frohro/Pico_Debug_Stack/Pico_Debug_Stack.txt

(export (version "E")
  (design
    (source "/home/frohro/Classes/Electronics/Pico_Development_Stack/Pico_Development_Stack.kicad_sch")
    (date "2025-12-18T11:42:48-0800")
    (tool "Eeschema 9.0.7-rc1-202512160022~49ee909d68~ubuntu25.04.1")
    (sheet (number "1") (name "/") (tstamps "/")
      (title_block
        (title "Raspberry Pi Pico Debug Stack")
        (company "Walla Walla University")
        (rev "0.1")
        (date "2025-12-10")
        (source "Pico_Development_Stack.kicad_sch")
        (comment (number "1") (value "Engineering"))
        (comment (number "2") (value "Rob Frohne"))
        (comment (number "3") (value ""))
        (comment (number "4") (value ""))
        (comment (number "5") (value ""))
        (comment (number "6") (value ""))
        (comment (number "7") (value ""))
        (comment (number "8") (value ""))
        (comment (number "9") (value "")))))
  (components
    (comp (ref "1V1_U1")
      (value "1V1")
      (footprint "TestPoint:TestPoint_Loop_D2.50mm_Drill1.0mm_LowProfile")
      (datasheet "~")
      (description "test point")
      (fields
        (field (name "Peak Wavelength"))
        (field (name "Footprint") "TestPoint:TestPoint_Loop_D2.50mm_Drill1.0mm_LowProfile")
        (field (name "Datasheet") "~")
        (field (name "Description") "test point"))
      (libsource (lib "Connector") (part "TestPoint") (description "test point"))
      (property (name "Peak Wavelength") (value ""))
      (property (name "Sheetname") (value "Root"))
      (property (name "Sheetfile") (value "Pico_Development_Stack.kicad_sch"))
      (property (name "ki_keywords") (value "test point tp"))
      (property (name "ki_fp_filters") (value "Pin* Test*"))
      (sheetpath (names "/") (tstamps "/"))
      (tstamps "04d520b3-1497-4948-9d44-730200b11b7a"))
    (comp (ref "A1")
      (value "RaspberryPi_Pico")
      (footprint "Module:RaspberryPi_Pico_SMD_HandSolder")
      (datasheet "https://datasheets.raspberrypi.com/pico/pico-datasheet.pdf")
      (description "Versatile and inexpensive microcontroller module (with debug pins) powered by RP2040 dual-core Arm Cortex-M0+ processor up to 133 MHz, 264kB SRAM, 2MB QSPI flash; also supports Raspberry Pi Pico 2")
      (fields
        (field (name "Peak Wavelength"))
        (field (name "Footprint") "Module:RaspberryPi_Pico_SMD_HandSolder")
        (field (name "Datasheet") "https://datasheets.raspberrypi.com/pico/pico-datasheet.pdf")
        (field (name "Description") "Versatile and inexpensive microcontroller module (with debug pins) powered by RP2040 dual-core Arm Cortex-M0+ processor up to 133 MHz, 264kB SRAM, 2MB QSPI flash; also supports Raspberry Pi Pico 2"))
      (libsource (lib "MCU_Module") (part "RaspberryPi_Pico_Debug") (description "Versatile and inexpensive microcontroller module (with debug pins) powered by RP2040 dual-core Arm Cortex-M0+ processor up to 133 MHz, 264kB SRAM, 2MB QSPI flash; also supports Raspberry Pi Pico 2"))
      (property (name "Peak Wavelength") (value ""))
      (property (name "Sheetname") (value "Root"))
      (property (name "Sheetfile") (value "Pico_Development_Stack.kicad_sch"))
      (property (name "ki_keywords") (value "RP2350A M33 RISC-V Hazard3 usb swd"))
      (property (name "ki_fp_filters") (value "RaspberryPi?Pico?SMD*"))
      (sheetpath (names "/") (tstamps "/"))
      (tstamps "4f39aecf-2b63-418a-a298-e7947e174bf0"))
    (comp (ref "C1")
      (value "10uF")
      (footprint "PCM_JLCPCB:C_0603")
      (datasheet "https://www.lcsc.com/datasheet/lcsc_datasheet_2304140030_Samsung-Electro-Mechanics-CL10A106MA8NRNC_C96446.pdf")
      (description "25V 10uF X5R ±20% 0603 Multilayer Ceramic Capacitors MLCC - SMD/SMT ROHS")
      (fields
        (field (name "LCSC") "C96446")
        (field (name "Stock") "3388297")
        (field (name "Price") "0.021USD")
        (field (name "Process") "SMT")
        (field (name "Minimum Qty") "20")
        (field (name "Attrition Qty") "8")
        (field (name "Class") "Basic Component")
        (field (name "Category") "Capacitors,Multilayer Ceramic Capacitors MLCC - SMD/SMT")
        (field (name "Manufacturer") "Samsung Electro-Mechanics")
        (field (name "Part") "CL10A106MA8NRNC")
        (field (name "Voltage Rated") "25V")
        (field (name "Tolerance") "±20%")
        (field (name "Capacitance") "10uF")
        (field (name "Temperature Coefficient") "X5R")
        (field (name "Footprint") "PCM_JLCPCB:C_0603")
        (field (name "Datasheet") "https://www.lcsc.com/datasheet/lcsc_datasheet_2304140030_Samsung-Electro-Mechanics-CL10A106MA8NRNC_C96446.pdf")
        (field (name "Description") "25V 10uF X5R ±20% 0603 Multilayer Ceramic Capacitors MLCC - SMD/SMT ROHS"))
      (libsource (lib "PCM_JLCPCB-Capacitors") (part "0603,10uF,(2)") (description "25V 10uF X5R ±20% 0603 Multilayer Ceramic Capacitors MLCC - SMD/SMT ROHS"))
      (property (name "LCSC") (value "C96446"))
      (property (name "Stock") (value "3388297"))
      (property (name "Price") (value "0.021USD"))
      (property (name "Process") (value "SMT"))
      (property (name "Minimum Qty") (value "20"))
      (property (name "Attrition Qty") (value "8"))
      (property (name "Class") (value "Basic Component"))
      (property (name "Category") (value "Capacitors,Multilayer Ceramic Capacitors MLCC - SMD/SMT"))
      (property (name "Manufacturer") (value "Samsung Electro-Mechanics"))
      (property (name "Part") (value "CL10A106MA8NRNC"))
      (property (name "Voltage Rated") (value "25V"))
      (property (name "Tolerance") (value "±20%"))
      (property (name "Capacitance") (value "10uF"))
      (property (name "Temperature Coefficient") (value "X5R"))
      (property (name "Sheetname") (value "Root"))
      (property (name "Sheetfile") (value "Pico_Development_Stack.kicad_sch"))
      (property (name "ki_fp_filters") (value "C_*"))
      (sheetpath (names "/") (tstamps "/"))
      (tstamps "58dccd1a-244c-415b-846c-d42b6af4e663"))
    (comp (ref "C2")
      (value "100nF")
      (footprint "PCM_JLCPCB:C_0603")
      (datasheet "https://www.lcsc.com/datasheet/lcsc_datasheet_2211101700_YAGEO-CC0603KRX7R9BB104_C14663.pdf")
      (description "50V 100nF X7R ±10% 0603 Multilayer Ceramic Capacitors MLCC - SMD/SMT ROHS")
      (fields
        (field (name "LCSC") "C14663")
        (field (name "Stock") "70324515")
        (field (name "Price") "0.006USD")
        (field (name "Process") "SMT")
        (field (name "Minimum Qty") "20")
        (field (name "Attrition Qty") "10")
        (field (name "Class") "Basic Component")
        (field (name "Category") "Capacitors,Multilayer Ceramic Capacitors MLCC - SMD/SMT")
        (field (name "Manufacturer") "YAGEO")
        (field (name "Part") "CC0603KRX7R9BB104")
        (field (name "Voltage Rated") "50V")
        (field (name "Tolerance") "±10%")
        (field (name "Capacitance") "100nF")
        (field (name "Temperature Coefficient") "X7R")
        (field (name "Peak Wavelength"))
        (field (name "Footprint") "PCM_JLCPCB:C_0603")
        (field (name "Datasheet") "https://www.lcsc.com/datasheet/lcsc_datasheet_2211101700_YAGEO-CC0603KRX7R9BB104_C14663.pdf")
        (field (name "Description") "50V 100nF X7R ±10% 0603 Multilayer Ceramic Capacitors MLCC - SMD/SMT ROHS"))
      (libsource (lib "PCM_JLCPCB-Capacitors") (part "0603,100nF") (description "50V 100nF X7R ±10% 0603 Multilayer Ceramic Capacitors MLCC - SMD/SMT ROHS"))
      (property (name "LCSC") (value "C14663"))
      (property (name "Stock") (value "70324515"))
      (property (name "Price") (value "0.006USD"))
      (property (name "Process") (value "SMT"))
      (property (name "Minimum Qty") (value "20"))
      (property (name "Attrition Qty") (value "10"))
      (property (name "Class") (value "Basic Component"))
      (property (name "Category") (value "Capacitors,Multilayer Ceramic Capacitors MLCC - SMD/SMT"))
      (property (name "Manufacturer") (value "YAGEO"))
      (property (name "Part") (value "CC0603KRX7R9BB104"))
      (property (name "Voltage Rated") (value "50V"))
      (property (name "Tolerance") (value "±10%"))
      (property (name "Capacitance") (value "100nF"))
      (property (name "Temperature Coefficient") (value "X7R"))
      (property (name "Peak Wavelength") (value ""))
      (property (name "Sheetname") (value "Root"))
      (property (name "Sheetfile") (value "Pico_Development_Stack.kicad_sch"))
      (property (name "ki_fp_filters") (value "C_*"))
      (sheetpath (names "/") (tstamps "/"))
      (tstamps "41aaf059-0a23-4617-9123-ac9339070171"))
    (comp (ref "C3")
      (value "100nF")
      (footprint "PCM_JLCPCB:C_0603")
      (datasheet "https://www.lcsc.com/datasheet/lcsc_datasheet_2211101700_YAGEO-CC0603KRX7R9BB104_C14663.pdf")
      (description "50V 100nF X7R ±10% 0603 Multilayer Ceramic Capacitors MLCC - SMD/SMT ROHS")
      (fields
        (field (name "LCSC") "C14663")
        (field (name "Stock") "70324515")
        (field (name "Price") "0.006USD")
        (field (name "Process") "SMT")
        (field (name "Minimum Qty") "20")
        (field (name "Attrition Qty") "10")
        (field (name "Class") "Basic Component")
        (field (name "Category") "Capacitors,Multilayer Ceramic Capacitors MLCC - SMD/SMT")
        (field (name "Manufacturer") "YAGEO")
        (field (name "Part") "CC0603KRX7R9BB104")
        (field (name "Voltage Rated") "50V")
        (field (name "Tolerance") "±10%")
        (field (name "Capacitance") "100nF")
        (field (name "Temperature Coefficient") "X7R")
        (field (name "Peak Wavelength"))
        (field (name "Footprint") "PCM_JLCPCB:C_0603")
        (field (name "Datasheet") "https://www.lcsc.com/datasheet/lcsc_datasheet_2211101700_YAGEO-CC0603KRX7R9BB104_C14663.pdf")
        (field (name "Description") "50V 100nF X7R ±10% 0603 Multilayer Ceramic Capacitors MLCC - SMD/SMT ROHS"))
      (libsource (lib "PCM_JLCPCB-Capacitors") (part "0603,100nF") (description "50V 100nF X7R ±10% 0603 Multilayer Ceramic Capacitors MLCC - SMD/SMT ROHS"))
      (property (name "LCSC") (value "C14663"))
      (property (name "Stock") (value "70324515"))
      (property (name "Price") (value "0.006USD"))
      (property (name "Process") (value "SMT"))
      (property (name "Minimum Qty") (value "20"))
      (property (name "Attrition Qty") (value "10"))
      (property (name "Class") (value "Basic Component"))
      (property (name "Category") (value "Capacitors,Multilayer Ceramic Capacitors MLCC - SMD/SMT"))
      (property (name "Manufacturer") (value "YAGEO"))
      (property (name "Part") (value "CC0603KRX7R9BB104"))
      (property (name "Voltage Rated") (value "50V"))
      (property (name "Tolerance") (value "±10%"))
      (property (name "Capacitance") (value "100nF"))
      (property (name "Temperature Coefficient") (value "X7R"))
      (property (name "Peak Wavelength") (value ""))
      (property (name "Sheetname") (value "Root"))
      (property (name "Sheetfile") (value "Pico_Development_Stack.kicad_sch"))
      (property (name "ki_fp_filters") (value "C_*"))
      (sheetpath (names "/") (tstamps "/"))
      (tstamps "a7b95df1-5875-4482-b6cb-c3aa639ff80f"))
    (comp (ref "C4")
      (value "100nF")
      (footprint "PCM_JLCPCB:C_0603")
      (datasheet "https://www.lcsc.com/datasheet/lcsc_datasheet_2211101700_YAGEO-CC0603KRX7R9BB104_C14663.pdf")
      (description "50V 100nF X7R ±10% 0603 Multilayer Ceramic Capacitors MLCC - SMD/SMT ROHS")
      (fields
        (field (name "LCSC") "C14663")
        (field (name "Stock") "70324515")
        (field (name "Price") "0.006USD")
        (field (name "Process") "SMT")
        (field (name "Minimum Qty") "20")
        (field (name "Attrition Qty") "10")
        (field (name "Class") "Basic Component")
        (field (name "Category") "Capacitors,Multilayer Ceramic Capacitors MLCC - SMD/SMT")
        (field (name "Manufacturer") "YAGEO")
        (field (name "Part") "CC0603KRX7R9BB104")
        (field (name "Voltage Rated") "50V")
        (field (name "Tolerance") "±10%")
        (field (name "Capacitance") "100nF")
        (field (name "Temperature Coefficient") "X7R")
        (field (name "Peak Wavelength"))
        (field (name "Footprint") "PCM_JLCPCB:C_0603")
        (field (name "Datasheet") "https://www.lcsc.com/datasheet/lcsc_datasheet_2211101700_YAGEO-CC0603KRX7R9BB104_C14663.pdf")
        (field (name "Description") "50V 100nF X7R ±10% 0603 Multilayer Ceramic Capacitors MLCC - SMD/SMT ROHS"))
      (libsource (lib "PCM_JLCPCB-Capacitors") (part "0603,100nF") (description "50V 100nF X7R ±10% 0603 Multilayer Ceramic Capacitors MLCC - SMD/SMT ROHS"))
      (property (name "LCSC") (value "C14663"))
      (property (name "Stock") (value "70324515"))
      (property (name "Price") (value "0.006USD"))
      (property (name "Process") (value "SMT"))
      (property (name "Minimum Qty") (value "20"))
      (property (name "Attrition Qty") (value "10"))
      (property (name "Class") (value "Basic Component"))
      (property (name "Category") (value "Capacitors,Multilayer Ceramic Capacitors MLCC - SMD/SMT"))
      (property (name "Manufacturer") (value "YAGEO"))
      (property (name "Part") (value "CC0603KRX7R9BB104"))
      (property (name "Voltage Rated") (value "50V"))
      (property (name "Tolerance") (value "±10%"))
      (property (name "Capacitance") (value "100nF"))
      (property (name "Temperature Coefficient") (value "X7R"))
      (property (name "Peak Wavelength") (value ""))
      (property (name "Sheetname") (value "Root"))
      (property (name "Sheetfile") (value "Pico_Development_Stack.kicad_sch"))
      (property (name "ki_fp_filters") (value "C_*"))
      (sheetpath (names "/") (tstamps "/"))
      (tstamps "84eebfa3-599e-4102-a1fc-1094d56afc2d"))
    (comp (ref "C5")
      (value "100nF")
      (footprint "PCM_JLCPCB:C_0603")
      (datasheet "https://www.lcsc.com/datasheet/lcsc_datasheet_2211101700_YAGEO-CC0603KRX7R9BB104_C14663.pdf")
      (description "50V 100nF X7R ±10% 0603 Multilayer Ceramic Capacitors MLCC - SMD/SMT ROHS")
      (fields
        (field (name "LCSC") "C14663")
        (field (name "Stock") "70324515")
        (field (name "Price") "0.006USD")
        (field (name "Process") "SMT")
        (field (name "Minimum Qty") "20")
        (field (name "Attrition Qty") "10")
        (field (name "Class") "Basic Component")
        (field (name "Category") "Capacitors,Multilayer Ceramic Capacitors MLCC - SMD/SMT")
        (field (name "Manufacturer") "YAGEO")
        (field (name "Part") "CC0603KRX7R9BB104")
        (field (name "Voltage Rated") "50V")
        (field (name "Tolerance") "±10%")
        (field (name "Capacitance") "100nF")
        (field (name "Temperature Coefficient") "X7R")
        (field (name "Peak Wavelength"))
        (field (name "Footprint") "PCM_JLCPCB:C_0603")
        (field (name "Datasheet") "https://www.lcsc.com/datasheet/lcsc_datasheet_2211101700_YAGEO-CC0603KRX7R9BB104_C14663.pdf")
        (field (name "Description") "50V 100nF X7R ±10% 0603 Multilayer Ceramic Capacitors MLCC - SMD/SMT ROHS"))
      (libsource (lib "PCM_JLCPCB-Capacitors") (part "0603,100nF") (description "50V 100nF X7R ±10% 0603 Multilayer Ceramic Capacitors MLCC - SMD/SMT ROHS"))
      (property (name "LCSC") (value "C14663"))
      (property (name "Stock") (value "70324515"))
      (property (name "Price") (value "0.006USD"))
      (property (name "Process") (value "SMT"))
      (property (name "Minimum Qty") (value "20"))
      (property (name "Attrition Qty") (value "10"))
      (property (name "Class") (value "Basic Component"))
      (property (name "Category") (value "Capacitors,Multilayer Ceramic Capacitors MLCC - SMD/SMT"))
      (property (name "Manufacturer") (value "YAGEO"))
      (property (name "Part") (value "CC0603KRX7R9BB104"))
      (property (name "Voltage Rated") (value "50V"))
      (property (name "Tolerance") (value "±10%"))
      (property (name "Capacitance") (value "100nF"))
      (property (name "Temperature Coefficient") (value "X7R"))
      (property (name "Peak Wavelength") (value ""))
      (property (name "Sheetname") (value "Root"))
      (property (name "Sheetfile") (value "Pico_Development_Stack.kicad_sch"))
      (property (name "ki_fp_filters") (value "C_*"))
      (sheetpath (names "/") (tstamps "/"))
      (tstamps "6679e69f-ec74-435c-90bb-8d16bdcccdf5"))
    (comp (ref "C6")
      (value "10uF")
      (footprint "PCM_JLCPCB:C_0603")
      (datasheet "https://www.lcsc.com/datasheet/lcsc_datasheet_2304140030_Samsung-Electro-Mechanics-CL10A106MA8NRNC_C96446.pdf")
      (description "25V 10uF X5R ±20% 0603 Multilayer Ceramic Capacitors MLCC - SMD/SMT ROHS")
      (fields
        (field (name "LCSC") "C96446")
        (field (name "Stock") "3388297")
        (field (name "Price") "0.021USD")
        (field (name "Process") "SMT")
        (field (name "Minimum Qty") "20")
        (field (name "Attrition Qty") "8")
        (field (name "Class") "Basic Component")
        (field (name "Category") "Capacitors,Multilayer Ceramic Capacitors MLCC - SMD/SMT")
        (field (name "Manufacturer") "Samsung Electro-Mechanics")
        (field (name "Part") "CL10A106MA8NRNC")
        (field (name "Voltage Rated") "25V")
        (field (name "Tolerance") "±20%")
        (field (name "Capacitance") "10uF")
        (field (name "Temperature Coefficient") "X5R")
        (field (name "Footprint") "PCM_JLCPCB:C_0603")
        (field (name "Datasheet") "https://www.lcsc.com/datasheet/lcsc_datasheet_2304140030_Samsung-Electro-Mechanics-CL10A106MA8NRNC_C96446.pdf")
        (field (name "Description") "25V 10uF X5R ±20% 0603 Multilayer Ceramic Capacitors MLCC - SMD/SMT ROHS"))
      (libsource (lib "PCM_JLCPCB-Capacitors") (part "0603,10uF,(2)") (description "25V 10uF X5R ±20% 0603 Multilayer Ceramic Capacitors MLCC - SMD/SMT ROHS"))
      (property (name "LCSC") (value "C96446"))
      (property (name "Stock") (value "3388297"))
      (property (name "Price") (value "0.021USD"))
      (property (name "Process") (value "SMT"))
      (property (name "Minimum Qty") (value "20"))
      (property (name "Attrition Qty") (value "8"))
      (property (name "Class") (value "Basic Component"))
      (property (name "Category") (value "Capacitors,Multilayer Ceramic Capacitors MLCC - SMD/SMT"))
      (property (name "Manufacturer") (value "Samsung Electro-Mechanics"))
      (property (name "Part") (value "CL10A106MA8NRNC"))
      (property (name "Voltage Rated") (value "25V"))
      (property (name "Tolerance") (value "±20%"))
      (property (name "Capacitance") (value "10uF"))
      (property (name "Temperature Coefficient") (value "X5R"))
      (property (name "Sheetname") (value "Root"))
      (property (name "Sheetfile") (value "Pico_Development_Stack.kicad_sch"))
      (property (name "ki_fp_filters") (value "C_*"))
      (sheetpath (names "/") (tstamps "/"))
      (tstamps "024aaf4a-5d37-4c77-9761-49cda8301e7f"))
    (comp (ref "C7")
      (value "22nF")
      (footprint "PCM_JLCPCB:C_0603")
      (datasheet "https://www.lcsc.com/datasheet/lcsc_datasheet_2304140030_Samsung-Electro-Mechanics-CL10B223KB8NNNC_C21122.pdf")
      (description "50V 22nF X7R ±10% 0603 Multilayer Ceramic Capacitors MLCC - SMD/SMT ROHS")
      (fields
        (field (name "LCSC") "C21122")
        (field (name "Stock") "746157")
        (field (name "Price") "0.007USD")
        (field (name "Process") "SMT")
        (field (name "Minimum Qty") "20")
        (field (name "Attrition Qty") "10")
        (field (name "Class") "Basic Component")
        (field (name "Category") "Capacitors,Multilayer Ceramic Capacitors MLCC - SMD/SMT")
        (field (name "Manufacturer") "Samsung Electro-Mechanics")
        (field (name "Part") "CL10B223KB8NNNC")
        (field (name "Voltage Rated") "50V")
        (field (name "Tolerance") "±10%")
        (field (name "Capacitance") "22nF")
        (field (name "Temperature Coefficient") "X7R")
        (field (name "Footprint") "PCM_JLCPCB:C_0603")
        (field (name "Datasheet") "https://www.lcsc.com/datasheet/lcsc_datasheet_2304140030_Samsung-Electro-Mechanics-CL10B223KB8NNNC_C21122.pdf")
        (field (name "Description") "50V 22nF X7R ±10% 0603 Multilayer Ceramic Capacitors MLCC - SMD/SMT ROHS"))
      (libsource (lib "PCM_JLCPCB-Capacitors") (part "0603,22nF") (description "50V 22nF X7R ±10% 0603 Multilayer Ceramic Capacitors MLCC - SMD/SMT ROHS"))
      (property (name "LCSC") (value "C21122"))
      (property (name "Stock") (value "746157"))
      (property (name "Price") (value "0.007USD"))
      (property (name "Process") (value "SMT"))
      (property (name "Minimum Qty") (value "20"))
      (property (name "Attrition Qty") (value "10"))
      (property (name "Class") (value "Basic Component"))
      (property (name "Category") (value "Capacitors,Multilayer Ceramic Capacitors MLCC - SMD/SMT"))
      (property (name "Manufacturer") (value "Samsung Electro-Mechanics"))
      (property (name "Part") (value "CL10B223KB8NNNC"))
      (property (name "Voltage Rated") (value "50V"))
      (property (name "Tolerance") (value "±10%"))
      (property (name "Capacitance") (value "22nF"))
      (property (name "Temperature Coefficient") (value "X7R"))
      (property (name "Sheetname") (value "Root"))
      (property (name "Sheetfile") (value "Pico_Development_Stack.kicad_sch"))
      (property (name "ki_fp_filters") (value "C_*"))
      (sheetpath (names "/") (tstamps "/"))
      (tstamps "5f9451e0-e461-40d3-bff0-ac59c7c7d7ab"))
    (comp (ref "C8")
      (value "22uF")
      (footprint "PCM_JLCPCB:C_0805")
      (datasheet "https://www.lcsc.com/datasheet/lcsc_datasheet_2304140030_Samsung-Electro-Mechanics-CL21A226MAQNNNE_C45783.pdf")
      (description "25V 22uF X5R ±20% 0805 Multilayer Ceramic Capacitors MLCC - SMD/SMT ROHS")
      (fields
        (field (name "LCSC") "C45783")
        (field (name "Stock") "6479946")
        (field (name "Price") "0.027USD")
        (field (name "Process") "SMT")
        (field (name "Minimum Qty") "20")
        (field (name "Attrition Qty") "8")
        (field (name "Class") "Basic Component")
        (field (name "Category") "Capacitors,Multilayer Ceramic Capacitors MLCC - SMD/SMT")
        (field (name "Manufacturer") "Samsung Electro-Mechanics")
        (field (name "Part") "CL21A226MAQNNNE")
        (field (name "Voltage Rated") "25V")
        (field (name "Tolerance") "±20%")
        (field (name "Capacitance") "22uF")
        (field (name "Temperature Coefficient") "X5R")
        (field (name "Footprint") "PCM_JLCPCB:C_0805")
        (field (name "Datasheet") "https://www.lcsc.com/datasheet/lcsc_datasheet_2304140030_Samsung-Electro-Mechanics-CL21A226MAQNNNE_C45783.pdf")
        (field (name "Description") "25V 22uF X5R ±20% 0805 Multilayer Ceramic Capacitors MLCC - SMD/SMT ROHS"))
      (libsource (lib "PCM_JLCPCB-Capacitors") (part "0805,22uF") (description "25V 22uF X5R ±20% 0805 Multilayer Ceramic Capacitors MLCC - SMD/SMT ROHS"))
      (property (name "LCSC") (value "C45783"))
      (property (name "Stock") (value "6479946"))
      (property (name "Price") (value "0.027USD"))
      (property (name "Process") (value "SMT"))
      (property (name "Minimum Qty") (value "20"))
      (property (name "Attrition Qty") (value "8"))
      (property (name "Class") (value "Basic Component"))
      (property (name "Category") (value "Capacitors,Multilayer Ceramic Capacitors MLCC - SMD/SMT"))
      (property (name "Manufacturer") (value "Samsung Electro-Mechanics"))
      (property (name "Part") (value "CL21A226MAQNNNE"))
      (property (name "Voltage Rated") (value "25V"))
      (property (name "Tolerance") (value "±20%"))
      (property (name "Capacitance") (value "22uF"))
      (property (name "Temperature Coefficient") (value "X5R"))
      (property (name "Sheetname") (value "Root"))
      (property (name "Sheetfile") (value "Pico_Development_Stack.kicad_sch"))
      (property (name "ki_fp_filters") (value "C_*"))
      (sheetpath (names "/") (tstamps "/"))
      (tstamps "dde8e6b0-4d19-45e5-ba62-ad8baa8489e9"))
    (comp (ref "C9")
      (value "22uF")
      (footprint "PCM_JLCPCB:C_0805")
      (datasheet "https://www.lcsc.com/datasheet/lcsc_datasheet_2304140030_Samsung-Electro-Mechanics-CL21A226MAQNNNE_C45783.pdf")
      (description "25V 22uF X5R ±20% 0805 Multilayer Ceramic Capacitors MLCC - SMD/SMT ROHS")
      (fields
        (field (name "LCSC") "C45783")
        (field (name "Stock") "6479946")
        (field (name "Price") "0.027USD")
        (field (name "Process") "SMT")
        (field (name "Minimum Qty") "20")
        (field (name "Attrition Qty") "8")
        (field (name "Class") "Basic Component")
        (field (name "Category") "Capacitors,Multilayer Ceramic Capacitors MLCC - SMD/SMT")
        (field (name "Manufacturer") "Samsung Electro-Mechanics")
        (field (name "Part") "CL21A226MAQNNNE")
        (field (name "Voltage Rated") "25V")
        (field (name "Tolerance") "±20%")
        (field (name "Capacitance") "22uF")
        (field (name "Temperature Coefficient") "X5R")
        (field (name "Footprint") "PCM_JLCPCB:C_0805")
        (field (name "Datasheet") "https://www.lcsc.com/datasheet/lcsc_datasheet_2304140030_Samsung-Electro-Mechanics-CL21A226MAQNNNE_C45783.pdf")
        (field (name "Description") "25V 22uF X5R ±20% 0805 Multilayer Ceramic Capacitors MLCC - SMD/SMT ROHS"))
      (libsource (lib "PCM_JLCPCB-Capacitors") (part "0805,22uF") (description "25V 22uF X5R ±20% 0805 Multilayer Ceramic Capacitors MLCC - SMD/SMT ROHS"))
      (property (name "LCSC") (value "C45783"))
      (property (name "Stock") (value "6479946"))
      (property (name "Price") (value "0.027USD"))
      (property (name "Process") (value "SMT"))
      (property (name "Minimum Qty") (value "20"))
      (property (name "Attrition Qty") (value "8"))
      (property (name "Class") (value "Basic Component"))
      (property (name "Category") (value "Capacitors,Multilayer Ceramic Capacitors MLCC - SMD/SMT"))
      (property (name "Manufacturer") (value "Samsung Electro-Mechanics"))
      (property (name "Part") (value "CL21A226MAQNNNE"))
      (property (name "Voltage Rated") (value "25V"))
      (property (name "Tolerance") (value "±20%"))
      (property (name "Capacitance") (value "22uF"))
      (property (name "Temperature Coefficient") (value "X5R"))
      (property (name "Sheetname") (value "Root"))
      (property (name "Sheetfile") (value "Pico_Development_Stack.kicad_sch"))
      (property (name "ki_fp_filters") (value "C_*"))
      (sheetpath (names "/") (tstamps "/"))
      (tstamps "4b71ddb2-d961-49d4-8c0b-ad9b4ba3da24"))
    (comp (ref "C10")
      (value "10uF")
      (footprint "PCM_JLCPCB:C_0603")
      (datasheet "https://www.lcsc.com/datasheet/lcsc_datasheet_2304140030_Samsung-Electro-Mechanics-CL10A106MA8NRNC_C96446.pdf")
      (description "25V 10uF X5R ±20% 0603 Multilayer Ceramic Capacitors MLCC - SMD/SMT ROHS")
      (fields
        (field (name "LCSC") "C96446")
        (field (name "Stock") "3388297")
        (field (name "Price") "0.021USD")
        (field (name "Process") "SMT")
        (field (name "Minimum Qty") "20")
        (field (name "Attrition Qty") "8")
        (field (name "Class") "Basic Component")
        (field (name "Category") "Capacitors,Multilayer Ceramic Capacitors MLCC - SMD/SMT")
        (field (name "Manufacturer") "Samsung Electro-Mechanics")
        (field (name "Part") "CL10A106MA8NRNC")
        (field (name "Voltage Rated") "25V")
        (field (name "Tolerance") "±20%")
        (field (name "Capacitance") "10uF")
        (field (name "Temperature Coefficient") "X5R")
        (field (name "Footprint") "PCM_JLCPCB:C_0603")
        (field (name "Datasheet") "https://www.lcsc.com/datasheet/lcsc_datasheet_2304140030_Samsung-Electro-Mechanics-CL10A106MA8NRNC_C96446.pdf")
        (field (name "Description") "25V 10uF X5R ±20% 0603 Multilayer Ceramic Capacitors MLCC - SMD/SMT ROHS"))
      (libsource (lib "PCM_JLCPCB-Capacitors") (part "0603,10uF,(2)") (description "25V 10uF X5R ±20% 0603 Multilayer Ceramic Capacitors MLCC - SMD/SMT ROHS"))
      (property (name "LCSC") (value "C96446"))
      (property (name "Stock") (value "3388297"))
      (property (name "Price") (value "0.021USD"))
      (property (name "Process") (value "SMT"))
      (property (name "Minimum Qty") (value "20"))
      (property (name "Attrition Qty") (value "8"))
      (property (name "Class") (value "Basic Component"))
      (property (name "Category") (value "Capacitors,Multilayer Ceramic Capacitors MLCC - SMD/SMT"))
      (property (name "Manufacturer") (value "Samsung Electro-Mechanics"))
      (property (name "Part") (value "CL10A106MA8NRNC"))
      (property (name "Voltage Rated") (value "25V"))
      (property (name "Tolerance") (value "±20%"))
      (property (name "Capacitance") (value "10uF"))
      (property (name "Temperature Coefficient") (value "X5R"))
      (property (name "Sheetname") (value "Root"))
      (property (name "Sheetfile") (value "Pico_Development_Stack.kicad_sch"))
      (property (name "ki_fp_filters") (value "C_*"))
      (sheetpath (names "/") (tstamps "/"))
      (tstamps "8ab68a28-5f2a-4086-b9f4-7d58be0168da"))
    (comp (ref "C11")
      (value "15pF")
      (footprint "PCM_JLCPCB:C_0603")
      (datasheet "https://www.lcsc.com/datasheet/lcsc_datasheet_2304140030_Samsung-Electro-Mechanics-CL10C150JB8NNNC_C1644.pdf")
      (description "50V 15pF C0G ±5% 0603 Multilayer Ceramic Capacitors MLCC - SMD/SMT ROHS")
      (fields
        (field (name "LCSC") "C1644")
        (field (name "Stock") "530628")
        (field (name "Price") "0.008USD")
        (field (name "Process") "SMT")
        (field (name "Minimum Qty") "20")
        (field (name "Attrition Qty") "10")
        (field (name "Class") "Basic Component")
        (field (name "Category") "Capacitors,Multilayer Ceramic Capacitors MLCC - SMD/SMT")
        (field (name "Manufacturer") "Samsung Electro-Mechanics")
        (field (name "Part") "CL10C150JB8NNNC")
        (field (name "Voltage Rated") "50V")
        (field (name "Tolerance") "±5%")
        (field (name "Capacitance") "15pF")
        (field (name "Temperature Coefficient") "C0G")
        (field (name "Footprint") "PCM_JLCPCB:C_0603")
        (field (name "Datasheet") "https://www.lcsc.com/datasheet/lcsc_datasheet_2304140030_Samsung-Electro-Mechanics-CL10C150JB8NNNC_C1644.pdf")
        (field (name "Description") "50V 15pF C0G ±5% 0603 Multilayer Ceramic Capacitors MLCC - SMD/SMT ROHS"))
      (libsource (lib "PCM_JLCPCB-Capacitors") (part "0603,15pF") (description "50V 15pF C0G ±5% 0603 Multilayer Ceramic Capacitors MLCC - SMD/SMT ROHS"))
      (property (name "LCSC") (value "C1644"))
      (property (name "Stock") (value "530628"))
      (property (name "Price") (value "0.008USD"))
      (property (name "Process") (value "SMT"))
      (property (name "Minimum Qty") (value "20"))
      (property (name "Attrition Qty") (value "10"))
      (property (name "Class") (value "Basic Component"))
      (property (name "Category") (value "Capacitors,Multilayer Ceramic Capacitors MLCC - SMD/SMT"))
      (property (name "Manufacturer") (value "Samsung Electro-Mechanics"))
      (property (name "Part") (value "CL10C150JB8NNNC"))
      (property (name "Voltage Rated") (value "50V"))
      (property (name "Tolerance") (value "±5%"))
      (property (name "Capacitance") (value "15pF"))
      (property (name "Temperature Coefficient") (value "C0G"))
      (property (name "Sheetname") (value "Root"))
      (property (name "Sheetfile") (value "Pico_Development_Stack.kicad_sch"))
      (property (name "ki_fp_filters") (value "C_*"))
      (sheetpath (names "/") (tstamps "/"))
      (tstamps "e517992e-69df-4bea-be89-e246776bf343"))
    (comp (ref "C12")
      (value "15pF")
      (footprint "PCM_JLCPCB:C_0603")
      (datasheet "https://www.lcsc.com/datasheet/lcsc_datasheet_2304140030_Samsung-Electro-Mechanics-CL10C150JB8NNNC_C1644.pdf")
      (description "50V 15pF C0G ±5% 0603 Multilayer Ceramic Capacitors MLCC - SMD/SMT ROHS")
      (fields
        (field (name "LCSC") "C1644")
        (field (name "Stock") "530628")
        (field (name "Price") "0.008USD")
        (field (name "Process") "SMT")
        (field (name "Minimum Qty") "20")
        (field (name "Attrition Qty") "10")
        (field (name "Class") "Basic Component")
        (field (name "Category") "Capacitors,Multilayer Ceramic Capacitors MLCC - SMD/SMT")
        (field (name "Manufacturer") "Samsung Electro-Mechanics")
        (field (name "Part") "CL10C150JB8NNNC")
        (field (name "Voltage Rated") "50V")
        (field (name "Tolerance") "±5%")
        (field (name "Capacitance") "15pF")
        (field (name "Temperature Coefficient") "C0G")
        (field (name "Footprint") "PCM_JLCPCB:C_0603")
        (field (name "Datasheet") "https://www.lcsc.com/datasheet/lcsc_datasheet_2304140030_Samsung-Electro-Mechanics-CL10C150JB8NNNC_C1644.pdf")
        (field (name "Description") "50V 15pF C0G ±5% 0603 Multilayer Ceramic Capacitors MLCC - SMD/SMT ROHS"))
      (libsource (lib "PCM_JLCPCB-Capacitors") (part "0603,15pF") (description "50V 15pF C0G ±5% 0603 Multilayer Ceramic Capacitors MLCC - SMD/SMT ROHS"))
      (property (name "LCSC") (value "C1644"))
      (property (name "Stock") (value "530628"))
      (property (name "Price") (value "0.008USD"))
      (property (name "Process") (value "SMT"))
      (property (name "Minimum Qty") (value "20"))
      (property (name "Attrition Qty") (value "10"))
      (property (name "Class") (value "Basic Component"))
      (property (name "Category") (value "Capacitors,Multilayer Ceramic Capacitors MLCC - SMD/SMT"))
      (property (name "Manufacturer") (value "Samsung Electro-Mechanics"))
      (property (name "Part") (value "CL10C150JB8NNNC"))
      (property (name "Voltage Rated") (value "50V"))
      (property (name "Tolerance") (value "±5%"))
      (property (name "Capacitance") (value "15pF"))
      (property (name "Temperature Coefficient") (value "C0G"))
      (property (name "Sheetname") (value "Root"))
      (property (name "Sheetfile") (value "Pico_Development_Stack.kicad_sch"))
      (property (name "ki_fp_filters") (value "C_*"))
      (sheetpath (names "/") (tstamps "/"))
      (tstamps "0e0d56db-b4ac-47ab-a85e-e6936359b822"))
    (comp (ref "C13")
      (value "100n")
      (footprint "PCM_JLCPCB:C_0603")
      (datasheet "https://www.lcsc.com/datasheet/lcsc_datasheet_2211101700_YAGEO-CC0603KRX7R9BB104_C14663.pdf")
      (description "50V 100nF X7R ±10% 0603 Multilayer Ceramic Capacitors MLCC - SMD/SMT ROHS")
      (fields
        (field (name "Peak Wavelength"))
        (field (name "LCSC") "C14663")
        (field (name "Stock") "70324515")
        (field (name "Price") "0.006USD")
        (field (name "Process") "SMT")
        (field (name "Minimum Qty") "20")
        (field (name "Attrition Qty") "10")
        (field (name "Class") "Basic Component")
        (field (name "Category") "Capacitors,Multilayer Ceramic Capacitors MLCC - SMD/SMT")
        (field (name "Manufacturer") "YAGEO")
        (field (name "Part") "CC0603KRX7R9BB104")
        (field (name "Voltage Rated") "50V")
        (field (name "Tolerance") "±10%")
        (field (name "Capacitance") "100nF")
        (field (name "Temperature Coefficient") "X7R")
        (field (name "Footprint") "PCM_JLCPCB:C_0603")
        (field (name "Datasheet") "https://www.lcsc.com/datasheet/lcsc_datasheet_2211101700_YAGEO-CC0603KRX7R9BB104_C14663.pdf")
        (field (name "Description") "50V 100nF X7R ±10% 0603 Multilayer Ceramic Capacitors MLCC - SMD/SMT ROHS"))
      (libsource (lib "PCM_JLCPCB-Capacitors") (part "0603,100nF") (description "50V 100nF X7R ±10% 0603 Multilayer Ceramic Capacitors MLCC - SMD/SMT ROHS"))
      (property (name "Peak Wavelength") (value ""))
      (property (name "LCSC") (value "C14663"))
      (property (name "Stock") (value "70324515"))
      (property (name "Price") (value "0.006USD"))
      (property (name "Process") (value "SMT"))
      (property (name "Minimum Qty") (value "20"))
      (property (name "Attrition Qty") (value "10"))
      (property (name "Class") (value "Basic Component"))
      (property (name "Category") (value "Capacitors,Multilayer Ceramic Capacitors MLCC - SMD/SMT"))
      (property (name "Manufacturer") (value "YAGEO"))
      (property (name "Part") (value "CC0603KRX7R9BB104"))
      (property (name "Voltage Rated") (value "50V"))
      (property (name "Tolerance") (value "±10%"))
      (property (name "Capacitance") (value "100nF"))
      (property (name "Temperature Coefficient") (value "X7R"))
      (property (name "Sheetname") (value "Root"))
      (property (name "Sheetfile") (value "Pico_Development_Stack.kicad_sch"))
      (property (name "ki_fp_filters") (value "C_*"))
      (sheetpath (names "/") (tstamps "/"))
      (tstamps "ad941bc2-e619-4ffe-8f91-d7e3073161dc"))
    (comp (ref "C14")
      (value "100n")
      (footprint "PCM_JLCPCB:C_0603")
      (datasheet "https://www.lcsc.com/datasheet/lcsc_datasheet_2211101700_YAGEO-CC0603KRX7R9BB104_C14663.pdf")
      (description "50V 100nF X7R ±10% 0603 Multilayer Ceramic Capacitors MLCC - SMD/SMT ROHS")
      (fields
        (field (name "Peak Wavelength"))
        (field (name "LCSC") "C14663")
        (field (name "Stock") "70324515")
        (field (name "Price") "0.006USD")
        (field (name "Process") "SMT")
        (field (name "Minimum Qty") "20")
        (field (name "Attrition Qty") "10")
        (field (name "Class") "Basic Component")
        (field (name "Category") "Capacitors,Multilayer Ceramic Capacitors MLCC - SMD/SMT")
        (field (name "Manufacturer") "YAGEO")
        (field (name "Part") "CC0603KRX7R9BB104")
        (field (name "Voltage Rated") "50V")
        (field (name "Tolerance") "±10%")
        (field (name "Capacitance") "100nF")
        (field (name "Temperature Coefficient") "X7R")
        (field (name "Footprint") "PCM_JLCPCB:C_0603")
        (field (name "Datasheet") "https://www.lcsc.com/datasheet/lcsc_datasheet_2211101700_YAGEO-CC0603KRX7R9BB104_C14663.pdf")
        (field (name "Description") "50V 100nF X7R ±10% 0603 Multilayer Ceramic Capacitors MLCC - SMD/SMT ROHS"))
      (libsource (lib "PCM_JLCPCB-Capacitors") (part "0603,100nF") (description "50V 100nF X7R ±10% 0603 Multilayer Ceramic Capacitors MLCC - SMD/SMT ROHS"))
      (property (name "Peak Wavelength") (value ""))
      (property (name "LCSC") (value "C14663"))
      (property (name "Stock") (value "70324515"))
      (property (name "Price") (value "0.006USD"))
      (property (name "Process") (value "SMT"))
      (property (name "Minimum Qty") (value "20"))
      (property (name "Attrition Qty") (value "10"))
      (property (name "Class") (value "Basic Component"))
      (property (name "Category") (value "Capacitors,Multilayer Ceramic Capacitors MLCC - SMD/SMT"))
      (property (name "Manufacturer") (value "YAGEO"))
      (property (name "Part") (value "CC0603KRX7R9BB104"))
      (property (name "Voltage Rated") (value "50V"))
      (property (name "Tolerance") (value "±10%"))
      (property (name "Capacitance") (value "100nF"))
      (property (name "Temperature Coefficient") (value "X7R"))
      (property (name "Sheetname") (value "Root"))
      (property (name "Sheetfile") (value "Pico_Development_Stack.kicad_sch"))
      (property (name "ki_fp_filters") (value "C_*"))
      (sheetpath (names "/") (tstamps "/"))
      (tstamps "87dbd1db-fe44-44e0-b614-1588969497be"))
    (comp (ref "C15")
      (value "15pF")
      (footprint "PCM_JLCPCB:C_0603")
      (datasheet "https://www.lcsc.com/datasheet/lcsc_datasheet_2304140030_Samsung-Electro-Mechanics-CL10C150JB8NNNC_C1644.pdf")
      (description "50V 15pF C0G ±5% 0603 Multilayer Ceramic Capacitors MLCC - SMD/SMT ROHS")
      (fields
        (field (name "LCSC") "C1644")
        (field (name "Stock") "530628")
        (field (name "Price") "0.008USD")
        (field (name "Process") "SMT")
        (field (name "Minimum Qty") "20")
        (field (name "Attrition Qty") "10")
        (field (name "Class") "Basic Component")
        (field (name "Category") "Capacitors,Multilayer Ceramic Capacitors MLCC - SMD/SMT")
        (field (name "Manufacturer") "Samsung Electro-Mechanics")
        (field (name "Part") "CL10C150JB8NNNC")
        (field (name "Voltage Rated") "50V")
        (field (name "Tolerance") "±5%")
        (field (name "Capacitance") "15pF")
        (field (name "Temperature Coefficient") "C0G")
        (field (name "Footprint") "PCM_JLCPCB:C_0603")
        (field (name "Datasheet") "https://www.lcsc.com/datasheet/lcsc_datasheet_2304140030_Samsung-Electro-Mechanics-CL10C150JB8NNNC_C1644.pdf")
        (field (name "Description") "50V 15pF C0G ±5% 0603 Multilayer Ceramic Capacitors MLCC - SMD/SMT ROHS"))
      (libsource (lib "PCM_JLCPCB-Capacitors") (part "0603,15pF") (description "50V 15pF C0G ±5% 0603 Multilayer Ceramic Capacitors MLCC - SMD/SMT ROHS"))
      (property (name "LCSC") (value "C1644"))
      (property (name "Stock") (value "530628"))
      (property (name "Price") (value "0.008USD"))
      (property (name "Process") (value "SMT"))
      (property (name "Minimum Qty") (value "20"))
      (property (name "Attrition Qty") (value "10"))
      (property (name "Class") (value "Basic Component"))
      (property (name "Category") (value "Capacitors,Multilayer Ceramic Capacitors MLCC - SMD/SMT"))
      (property (name "Manufacturer") (value "Samsung Electro-Mechanics"))
      (property (name "Part") (value "CL10C150JB8NNNC"))
      (property (name "Voltage Rated") (value "50V"))
      (property (name "Tolerance") (value "±5%"))
      (property (name "Capacitance") (value "15pF"))
      (property (name "Temperature Coefficient") (value "C0G"))
      (property (name "Sheetname") (value "Root"))
      (property (name "Sheetfile") (value "Pico_Development_Stack.kicad_sch"))
      (property (name "ki_fp_filters") (value "C_*"))
      (sheetpath (names "/") (tstamps "/"))
      (tstamps "90bb02f8-aedb-4994-ab52-2c149d783b24"))
    (comp (ref "C16")
      (value "15pF")
      (footprint "PCM_JLCPCB:C_0603")
      (datasheet "https://www.lcsc.com/datasheet/lcsc_datasheet_2304140030_Samsung-Electro-Mechanics-CL10C150JB8NNNC_C1644.pdf")
      (description "50V 15pF C0G ±5% 0603 Multilayer Ceramic Capacitors MLCC - SMD/SMT ROHS")
      (fields
        (field (name "LCSC") "C1644")
        (field (name "Stock") "530628")
        (field (name "Price") "0.008USD")
        (field (name "Process") "SMT")
        (field (name "Minimum Qty") "20")
        (field (name "Attrition Qty") "10")
        (field (name "Class") "Basic Component")
        (field (name "Category") "Capacitors,Multilayer Ceramic Capacitors MLCC - SMD/SMT")
        (field (name "Manufacturer") "Samsung Electro-Mechanics")
        (field (name "Part") "CL10C150JB8NNNC")
        (field (name "Voltage Rated") "50V")
        (field (name "Tolerance") "±5%")
        (field (name "Capacitance") "15pF")
        (field (name "Temperature Coefficient") "C0G")
        (field (name "Footprint") "PCM_JLCPCB:C_0603")
        (field (name "Datasheet") "https://www.lcsc.com/datasheet/lcsc_datasheet_2304140030_Samsung-Electro-Mechanics-CL10C150JB8NNNC_C1644.pdf")
        (field (name "Description") "50V 15pF C0G ±5% 0603 Multilayer Ceramic Capacitors MLCC - SMD/SMT ROHS"))
      (libsource (lib "PCM_JLCPCB-Capacitors") (part "0603,15pF") (description "50V 15pF C0G ±5% 0603 Multilayer Ceramic Capacitors MLCC - SMD/SMT ROHS"))
      (property (name "LCSC") (value "C1644"))
      (property (name "Stock") (value "530628"))
      (property (name "Price") (value "0.008USD"))
      (property (name "Process") (value "SMT"))
      (property (name "Minimum Qty") (value "20"))
      (property (name "Attrition Qty") (value "10"))
      (property (name "Class") (value "Basic Component"))
      (property (name "Category") (value "Capacitors,Multilayer Ceramic Capacitors MLCC - SMD/SMT"))
      (property (name "Manufacturer") (value "Samsung Electro-Mechanics"))
      (property (name "Part") (value "CL10C150JB8NNNC"))
      (property (name "Voltage Rated") (value "50V"))
      (property (name "Tolerance") (value "±5%"))
      (property (name "Capacitance") (value "15pF"))
      (property (name "Temperature Coefficient") (value "C0G"))
      (property (name "Sheetname") (value "Root"))
      (property (name "Sheetfile") (value "Pico_Development_Stack.kicad_sch"))
      (property (name "ki_fp_filters") (value "C_*"))
      (sheetpath (names "/") (tstamps "/"))
      (tstamps "218f0572-07b2-4993-b840-5253615be193"))
    (comp (ref "C17")
      (value "15pF")
      (footprint "PCM_JLCPCB:C_0603")
      (datasheet "https://www.lcsc.com/datasheet/lcsc_datasheet_2304140030_Samsung-Electro-Mechanics-CL10C150JB8NNNC_C1644.pdf")
      (description "50V 15pF C0G ±5% 0603 Multilayer Ceramic Capacitors MLCC - SMD/SMT ROHS")
      (fields
        (field (name "LCSC") "C1644")
        (field (name "Stock") "530628")
        (field (name "Price") "0.008USD")
        (field (name "Process") "SMT")
        (field (name "Minimum Qty") "20")
        (field (name "Attrition Qty") "10")
        (field (name "Class") "Basic Component")
        (field (name "Category") "Capacitors,Multilayer Ceramic Capacitors MLCC - SMD/SMT")
        (field (name "Manufacturer") "Samsung Electro-Mechanics")
        (field (name "Part") "CL10C150JB8NNNC")
        (field (name "Voltage Rated") "50V")
        (field (name "Tolerance") "±5%")
        (field (name "Capacitance") "15pF")
        (field (name "Temperature Coefficient") "C0G")
        (field (name "Footprint") "PCM_JLCPCB:C_0603")
        (field (name "Datasheet") "https://www.lcsc.com/datasheet/lcsc_datasheet_2304140030_Samsung-Electro-Mechanics-CL10C150JB8NNNC_C1644.pdf")
        (field (name "Description") "50V 15pF C0G ±5% 0603 Multilayer Ceramic Capacitors MLCC - SMD/SMT ROHS"))
      (libsource (lib "PCM_JLCPCB-Capacitors") (part "0603,15pF") (description "50V 15pF C0G ±5% 0603 Multilayer Ceramic Capacitors MLCC - SMD/SMT ROHS"))
      (property (name "LCSC") (value "C1644"))
      (property (name "Stock") (value "530628"))
      (property (name "Price") (value "0.008USD"))
      (property (name "Process") (value "SMT"))
      (property (name "Minimum Qty") (value "20"))
      (property (name "Attrition Qty") (value "10"))
      (property (name "Class") (value "Basic Component"))
      (property (name "Category") (value "Capacitors,Multilayer Ceramic Capacitors MLCC - SMD/SMT"))
      (property (name "Manufacturer") (value "Samsung Electro-Mechanics"))
      (property (name "Part") (value "CL10C150JB8NNNC"))
      (property (name "Voltage Rated") (value "50V"))
      (property (name "Tolerance") (value "±5%"))
      (property (name "Capacitance") (value "15pF"))
      (property (name "Temperature Coefficient") (value "C0G"))
      (property (name "Sheetname") (value "Root"))
      (property (name "Sheetfile") (value "Pico_Development_Stack.kicad_sch"))
      (property (name "ki_fp_filters") (value "C_*"))
      (sheetpath (names "/") (tstamps "/"))
      (tstamps "15d67958-7054-43be-b22d-373adae222cf"))
    (comp (ref "C18")
      (value "15pF")
      (footprint "PCM_JLCPCB:C_0603")
      (datasheet "https://www.lcsc.com/datasheet/lcsc_datasheet_2304140030_Samsung-Electro-Mechanics-CL10C150JB8NNNC_C1644.pdf")
      (description "50V 15pF C0G ±5% 0603 Multilayer Ceramic Capacitors MLCC - SMD/SMT ROHS")
      (fields
        (field (name "LCSC") "C1644")
        (field (name "Stock") "530628")
        (field (name "Price") "0.008USD")
        (field (name "Process") "SMT")
        (field (name "Minimum Qty") "20")
        (field (name "Attrition Qty") "10")
        (field (name "Class") "Basic Component")
        (field (name "Category") "Capacitors,Multilayer Ceramic Capacitors MLCC - SMD/SMT")
        (field (name "Manufacturer") "Samsung Electro-Mechanics")
        (field (name "Part") "CL10C150JB8NNNC")
        (field (name "Voltage Rated") "50V")
        (field (name "Tolerance") "±5%")
        (field (name "Capacitance") "15pF")
        (field (name "Temperature Coefficient") "C0G")
        (field (name "Footprint") "PCM_JLCPCB:C_0603")
        (field (name "Datasheet") "https://www.lcsc.com/datasheet/lcsc_datasheet_2304140030_Samsung-Electro-Mechanics-CL10C150JB8NNNC_C1644.pdf")
        (field (name "Description") "50V 15pF C0G ±5% 0603 Multilayer Ceramic Capacitors MLCC - SMD/SMT ROHS"))
      (libsource (lib "PCM_JLCPCB-Capacitors") (part "0603,15pF") (description "50V 15pF C0G ±5% 0603 Multilayer Ceramic Capacitors MLCC - SMD/SMT ROHS"))
      (property (name "LCSC") (value "C1644"))
      (property (name "Stock") (value "530628"))
      (property (name "Price") (value "0.008USD"))
      (property (name "Process") (value "SMT"))
      (property (name "Minimum Qty") (value "20"))
      (property (name "Attrition Qty") (value "10"))
      (property (name "Class") (value "Basic Component"))
      (property (name "Category") (value "Capacitors,Multilayer Ceramic Capacitors MLCC - SMD/SMT"))
      (property (name "Manufacturer") (value "Samsung Electro-Mechanics"))
      (property (name "Part") (value "CL10C150JB8NNNC"))
      (property (name "Voltage Rated") (value "50V"))
      (property (name "Tolerance") (value "±5%"))
      (property (name "Capacitance") (value "15pF"))
      (property (name "Temperature Coefficient") (value "C0G"))
      (property (name "Sheetname") (value "Root"))
      (property (name "Sheetfile") (value "Pico_Development_Stack.kicad_sch"))
      (property (name "ki_fp_filters") (value "C_*"))
      (sheetpath (names "/") (tstamps "/"))
      (tstamps "5f4d418f-146b-49ea-a87b-baa7f0aae07f"))
    (comp (ref "C19")
      (value "4.7uF")
      (footprint "PCM_JLCPCB:C_0603")
      (datasheet "https://www.lcsc.com/datasheet/lcsc_datasheet_2304140030_Samsung-Electro-Mechanics-CL10A475KO8NNNC_C19666.pdf")
      (description "16V 4.7uF X5R ±10% 0603 Multilayer Ceramic Capacitors MLCC - SMD/SMT ROHS")
      (fields
        (field (name "LCSC") "C19666")
        (field (name "Stock") "4246728")
        (field (name "Price") "0.013USD")
        (field (name "Process") "SMT")
        (field (name "Minimum Qty") "20")
        (field (name "Attrition Qty") "10")
        (field (name "Class") "Basic Component")
        (field (name "Category") "Capacitors,Multilayer Ceramic Capacitors MLCC - SMD/SMT")
        (field (name "Manufacturer") "Samsung Electro-Mechanics")
        (field (name "Part") "CL10A475KO8NNNC")
        (field (name "Voltage Rated") "16V")
        (field (name "Tolerance") "±10%")
        (field (name "Capacitance") "4.7uF")
        (field (name "Temperature Coefficient") "X5R")
        (field (name "Peak Wavelength"))
        (field (name "Footprint") "PCM_JLCPCB:C_0603")
        (field (name "Datasheet") "https://www.lcsc.com/datasheet/lcsc_datasheet_2304140030_Samsung-Electro-Mechanics-CL10A475KO8NNNC_C19666.pdf")
        (field (name "Description") "16V 4.7uF X5R ±10% 0603 Multilayer Ceramic Capacitors MLCC - SMD/SMT ROHS"))
      (libsource (lib "PCM_JLCPCB-Capacitors") (part "0603,4.7uF") (description "16V 4.7uF X5R ±10% 0603 Multilayer Ceramic Capacitors MLCC - SMD/SMT ROHS"))
      (property (name "LCSC") (value "C19666"))
      (property (name "Stock") (value "4246728"))
      (property (name "Price") (value "0.013USD"))
      (property (name "Process") (value "SMT"))
      (property (name "Minimum Qty") (value "20"))
      (property (name "Attrition Qty") (value "10"))
      (property (name "Class") (value "Basic Component"))
      (property (name "Category") (value "Capacitors,Multilayer Ceramic Capacitors MLCC - SMD/SMT"))
      (property (name "Manufacturer") (value "Samsung Electro-Mechanics"))
      (property (name "Part") (value "CL10A475KO8NNNC"))
      (property (name "Voltage Rated") (value "16V"))
      (property (name "Tolerance") (value "±10%"))
      (property (name "Capacitance") (value "4.7uF"))
      (property (name "Temperature Coefficient") (value "X5R"))
      (property (name "Peak Wavelength") (value ""))
      (property (name "Sheetname") (value "Root"))
      (property (name "Sheetfile") (value "Pico_Development_Stack.kicad_sch"))
      (property (name "ki_fp_filters") (value "C_*"))
      (sheetpath (names "/") (tstamps "/"))
      (tstamps "865ae598-d712-4617-9186-ccdd9e9680ec"))
    (comp (ref "C20")
      (value "100nF")
      (footprint "PCM_JLCPCB:C_0603")
      (datasheet "https://www.lcsc.com/datasheet/lcsc_datasheet_2211101700_YAGEO-CC0603KRX7R9BB104_C14663.pdf")
      (description "50V 100nF X7R ±10% 0603 Multilayer Ceramic Capacitors MLCC - SMD/SMT ROHS")
      (fields
        (field (name "LCSC") "C14663")
        (field (name "Stock") "70324515")
        (field (name "Price") "0.006USD")
        (field (name "Process") "SMT")
        (field (name "Minimum Qty") "20")
        (field (name "Attrition Qty") "10")
        (field (name "Class") "Basic Component")
        (field (name "Category") "Capacitors,Multilayer Ceramic Capacitors MLCC - SMD/SMT")
        (field (name "Manufacturer") "YAGEO")
        (field (name "Part") "CC0603KRX7R9BB104")
        (field (name "Voltage Rated") "50V")
        (field (name "Tolerance") "±10%")
        (field (name "Capacitance") "100nF")
        (field (name "Temperature Coefficient") "X7R")
        (field (name "Peak Wavelength"))
        (field (name "Footprint") "PCM_JLCPCB:C_0603")
        (field (name "Datasheet") "https://www.lcsc.com/datasheet/lcsc_datasheet_2211101700_YAGEO-CC0603KRX7R9BB104_C14663.pdf")
        (field (name "Description") "50V 100nF X7R ±10% 0603 Multilayer Ceramic Capacitors MLCC - SMD/SMT ROHS"))
      (libsource (lib "PCM_JLCPCB-Capacitors") (part "0603,100nF") (description "50V 100nF X7R ±10% 0603 Multilayer Ceramic Capacitors MLCC - SMD/SMT ROHS"))
      (property (name "LCSC") (value "C14663"))
      (property (name "Stock") (value "70324515"))
      (property (name "Price") (value "0.006USD"))
      (property (name "Process") (value "SMT"))
      (property (name "Minimum Qty") (value "20"))
      (property (name "Attrition Qty") (value "10"))
      (property (name "Class") (value "Basic Component"))
      (property (name "Category") (value "Capacitors,Multilayer Ceramic Capacitors MLCC - SMD/SMT"))
      (property (name "Manufacturer") (value "YAGEO"))
      (property (name "Part") (value "CC0603KRX7R9BB104"))
      (property (name "Voltage Rated") (value "50V"))
      (property (name "Tolerance") (value "±10%"))
      (property (name "Capacitance") (value "100nF"))
      (property (name "Temperature Coefficient") (value "X7R"))
      (property (name "Peak Wavelength") (value ""))
      (property (name "Sheetname") (value "Root"))
      (property (name "Sheetfile") (value "Pico_Development_Stack.kicad_sch"))
      (property (name "ki_fp_filters") (value "C_*"))
      (sheetpath (names "/") (tstamps "/"))
      (tstamps "ca55c5c2-c50b-49c5-8519-57ad99130cf6"))
    (comp (ref "C21")
      (value "100nF")
      (footprint "PCM_JLCPCB:C_0603")
      (datasheet "https://www.lcsc.com/datasheet/lcsc_datasheet_2211101700_YAGEO-CC0603KRX7R9BB104_C14663.pdf")
      (description "50V 100nF X7R ±10% 0603 Multilayer Ceramic Capacitors MLCC - SMD/SMT ROHS")
      (fields
        (field (name "LCSC") "C14663")
        (field (name "Stock") "70324515")
        (field (name "Price") "0.006USD")
        (field (name "Process") "SMT")
        (field (name "Minimum Qty") "20")
        (field (name "Attrition Qty") "10")
        (field (name "Class") "Basic Component")
        (field (name "Category") "Capacitors,Multilayer Ceramic Capacitors MLCC - SMD/SMT")
        (field (name "Manufacturer") "YAGEO")
        (field (name "Part") "CC0603KRX7R9BB104")
        (field (name "Voltage Rated") "50V")
        (field (name "Tolerance") "±10%")
        (field (name "Capacitance") "100nF")
        (field (name "Temperature Coefficient") "X7R")
        (field (name "Peak Wavelength"))
        (field (name "Footprint") "PCM_JLCPCB:C_0603")
        (field (name "Datasheet") "https://www.lcsc.com/datasheet/lcsc_datasheet_2211101700_YAGEO-CC0603KRX7R9BB104_C14663.pdf")
        (field (name "Description") "50V 100nF X7R ±10% 0603 Multilayer Ceramic Capacitors MLCC - SMD/SMT ROHS"))
      (libsource (lib "PCM_JLCPCB-Capacitors") (part "0603,100nF") (description "50V 100nF X7R ±10% 0603 Multilayer Ceramic Capacitors MLCC - SMD/SMT ROHS"))
      (property (name "LCSC") (value "C14663"))
      (property (name "Stock") (value "70324515"))
      (property (name "Price") (value "0.006USD"))
      (property (name "Process") (value "SMT"))
      (property (name "Minimum Qty") (value "20"))
      (property (name "Attrition Qty") (value "10"))
      (property (name "Class") (value "Basic Component"))
      (property (name "Category") (value "Capacitors,Multilayer Ceramic Capacitors MLCC - SMD/SMT"))
      (property (name "Manufacturer") (value "YAGEO"))
      (property (name "Part") (value "CC0603KRX7R9BB104"))
      (property (name "Voltage Rated") (value "50V"))
      (property (name "Tolerance") (value "±10%"))
      (property (name "Capacitance") (value "100nF"))
      (property (name "Temperature Coefficient") (value "X7R"))
      (property (name "Peak Wavelength") (value ""))
      (property (name "Sheetname") (value "Root"))
      (property (name "Sheetfile") (value "Pico_Development_Stack.kicad_sch"))
      (property (name "ki_fp_filters") (value "C_*"))
      (sheetpath (names "/") (tstamps "/"))
      (tstamps "75f6bb37-4ca2-4fcf-a8a9-06a22f594ee0"))
    (comp (ref "C22")
      (value "100nF")
      (footprint "PCM_JLCPCB:C_0603")
      (datasheet "https://www.lcsc.com/datasheet/lcsc_datasheet_2211101700_YAGEO-CC0603KRX7R9BB104_C14663.pdf")
      (description "50V 100nF X7R ±10% 0603 Multilayer Ceramic Capacitors MLCC - SMD/SMT ROHS")
      (fields
        (field (name "LCSC") "C14663")
        (field (name "Stock") "70324515")
        (field (name "Price") "0.006USD")
        (field (name "Process") "SMT")
        (field (name "Minimum Qty") "20")
        (field (name "Attrition Qty") "10")
        (field (name "Class") "Basic Component")
        (field (name "Category") "Capacitors,Multilayer Ceramic Capacitors MLCC - SMD/SMT")
        (field (name "Manufacturer") "YAGEO")
        (field (name "Part") "CC0603KRX7R9BB104")
        (field (name "Voltage Rated") "50V")
        (field (name "Tolerance") "±10%")
        (field (name "Capacitance") "100nF")
        (field (name "Temperature Coefficient") "X7R")
        (field (name "Peak Wavelength"))
        (field (name "Footprint") "PCM_JLCPCB:C_0603")
        (field (name "Datasheet") "https://www.lcsc.com/datasheet/lcsc_datasheet_2211101700_YAGEO-CC0603KRX7R9BB104_C14663.pdf")
        (field (name "Description") "50V 100nF X7R ±10% 0603 Multilayer Ceramic Capacitors MLCC - SMD/SMT ROHS"))
      (libsource (lib "PCM_JLCPCB-Capacitors") (part "0603,100nF") (description "50V 100nF X7R ±10% 0603 Multilayer Ceramic Capacitors MLCC - SMD/SMT ROHS"))
      (property (name "LCSC") (value "C14663"))
      (property (name "Stock") (value "70324515"))
      (property (name "Price") (value "0.006USD"))
      (property (name "Process") (value "SMT"))
      (property (name "Minimum Qty") (value "20"))
      (property (name "Attrition Qty") (value "10"))
      (property (name "Class") (value "Basic Component"))
      (property (name "Category") (value "Capacitors,Multilayer Ceramic Capacitors MLCC - SMD/SMT"))
      (property (name "Manufacturer") (value "YAGEO"))
      (property (name "Part") (value "CC0603KRX7R9BB104"))
      (property (name "Voltage Rated") (value "50V"))
      (property (name "Tolerance") (value "±10%"))
      (property (name "Capacitance") (value "100nF"))
      (property (name "Temperature Coefficient") (value "X7R"))
      (property (name "Peak Wavelength") (value ""))
      (property (name "Sheetname") (value "Root"))
      (property (name "Sheetfile") (value "Pico_Development_Stack.kicad_sch"))
      (property (name "ki_fp_filters") (value "C_*"))
      (sheetpath (names "/") (tstamps "/"))
      (tstamps "b9b01385-918e-4d0b-9988-2dadcb5075c7"))
    (comp (ref "C23")
      (value "100nF")
      (footprint "PCM_JLCPCB:C_0603")
      (datasheet "https://www.lcsc.com/datasheet/lcsc_datasheet_2211101700_YAGEO-CC0603KRX7R9BB104_C14663.pdf")
      (description "50V 100nF X7R ±10% 0603 Multilayer Ceramic Capacitors MLCC - SMD/SMT ROHS")
      (fields
        (field (name "LCSC") "C14663")
        (field (name "Stock") "70324515")
        (field (name "Price") "0.006USD")
        (field (name "Process") "SMT")
        (field (name "Minimum Qty") "20")
        (field (name "Attrition Qty") "10")
        (field (name "Class") "Basic Component")
        (field (name "Category") "Capacitors,Multilayer Ceramic Capacitors MLCC - SMD/SMT")
        (field (name "Manufacturer") "YAGEO")
        (field (name "Part") "CC0603KRX7R9BB104")
        (field (name "Voltage Rated") "50V")
        (field (name "Tolerance") "±10%")
        (field (name "Capacitance") "100nF")
        (field (name "Temperature Coefficient") "X7R")
        (field (name "Peak Wavelength"))
        (field (name "Footprint") "PCM_JLCPCB:C_0603")
        (field (name "Datasheet") "https://www.lcsc.com/datasheet/lcsc_datasheet_2211101700_YAGEO-CC0603KRX7R9BB104_C14663.pdf")
        (field (name "Description") "50V 100nF X7R ±10% 0603 Multilayer Ceramic Capacitors MLCC - SMD/SMT ROHS"))
      (libsource (lib "PCM_JLCPCB-Capacitors") (part "0603,100nF") (description "50V 100nF X7R ±10% 0603 Multilayer Ceramic Capacitors MLCC - SMD/SMT ROHS"))
      (property (name "LCSC") (value "C14663"))
      (property (name "Stock") (value "70324515"))
      (property (name "Price") (value "0.006USD"))
      (property (name "Process") (value "SMT"))
      (property (name "Minimum Qty") (value "20"))
      (property (name "Attrition Qty") (value "10"))
      (property (name "Class") (value "Basic Component"))
      (property (name "Category") (value "Capacitors,Multilayer Ceramic Capacitors MLCC - SMD/SMT"))
      (property (name "Manufacturer") (value "YAGEO"))
      (property (name "Part") (value "CC0603KRX7R9BB104"))
      (property (name "Voltage Rated") (value "50V"))
      (property (name "Tolerance") (value "±10%"))
      (property (name "Capacitance") (value "100nF"))
      (property (name "Temperature Coefficient") (value "X7R"))
      (property (name "Peak Wavelength") (value ""))
      (property (name "Sheetname") (value "Root"))
      (property (name "Sheetfile") (value "Pico_Development_Stack.kicad_sch"))
      (property (name "ki_fp_filters") (value "C_*"))
      (sheetpath (names "/") (tstamps "/"))
      (tstamps "6bfb8f57-e32c-4281-be6e-b84114ede55a"))
    (comp (ref "C24")
      (value "100nF")
      (footprint "PCM_JLCPCB:C_0603")
      (datasheet "https://www.lcsc.com/datasheet/lcsc_datasheet_2211101700_YAGEO-CC0603KRX7R9BB104_C14663.pdf")
      (description "50V 100nF X7R ±10% 0603 Multilayer Ceramic Capacitors MLCC - SMD/SMT ROHS")
      (fields
        (field (name "LCSC") "C14663")
        (field (name "Stock") "70324515")
        (field (name "Price") "0.006USD")
        (field (name "Process") "SMT")
        (field (name "Minimum Qty") "20")
        (field (name "Attrition Qty") "10")
        (field (name "Class") "Basic Component")
        (field (name "Category") "Capacitors,Multilayer Ceramic Capacitors MLCC - SMD/SMT")
        (field (name "Manufacturer") "YAGEO")
        (field (name "Part") "CC0603KRX7R9BB104")
        (field (name "Voltage Rated") "50V")
        (field (name "Tolerance") "±10%")
        (field (name "Capacitance") "100nF")
        (field (name "Temperature Coefficient") "X7R")
        (field (name "Peak Wavelength"))
        (field (name "Footprint") "PCM_JLCPCB:C_0603")
        (field (name "Datasheet") "https://www.lcsc.com/datasheet/lcsc_datasheet_2211101700_YAGEO-CC0603KRX7R9BB104_C14663.pdf")
        (field (name "Description") "50V 100nF X7R ±10% 0603 Multilayer Ceramic Capacitors MLCC - SMD/SMT ROHS"))
      (libsource (lib "PCM_JLCPCB-Capacitors") (part "0603,100nF") (description "50V 100nF X7R ±10% 0603 Multilayer Ceramic Capacitors MLCC - SMD/SMT ROHS"))
      (property (name "LCSC") (value "C14663"))
      (property (name "Stock") (value "70324515"))
      (property (name "Price") (value "0.006USD"))
      (property (name "Process") (value "SMT"))
      (property (name "Minimum Qty") (value "20"))
      (property (name "Attrition Qty") (value "10"))
      (property (name "Class") (value "Basic Component"))
      (property (name "Category") (value "Capacitors,Multilayer Ceramic Capacitors MLCC - SMD/SMT"))
      (property (name "Manufacturer") (value "YAGEO"))
      (property (name "Part") (value "CC0603KRX7R9BB104"))
      (property (name "Voltage Rated") (value "50V"))
      (property (name "Tolerance") (value "±10%"))
      (property (name "Capacitance") (value "100nF"))
      (property (name "Temperature Coefficient") (value "X7R"))
      (property (name "Peak Wavelength") (value ""))
      (property (name "Sheetname") (value "Root"))
      (property (name "Sheetfile") (value "Pico_Development_Stack.kicad_sch"))
      (property (name "ki_fp_filters") (value "C_*"))
      (sheetpath (names "/") (tstamps "/"))
      (tstamps "84b8df8d-e083-4673-9dab-93b357eb2180"))
    (comp (ref "C25")
      (value "100nF")
      (footprint "PCM_JLCPCB:C_0603")
      (datasheet "https://www.lcsc.com/datasheet/lcsc_datasheet_2211101700_YAGEO-CC0603KRX7R9BB104_C14663.pdf")
      (description "50V 100nF X7R ±10% 0603 Multilayer Ceramic Capacitors MLCC - SMD/SMT ROHS")
      (fields
        (field (name "LCSC") "C14663")
        (field (name "Stock") "70324515")
        (field (name "Price") "0.006USD")
        (field (name "Process") "SMT")
        (field (name "Minimum Qty") "20")
        (field (name "Attrition Qty") "10")
        (field (name "Class") "Basic Component")
        (field (name "Category") "Capacitors,Multilayer Ceramic Capacitors MLCC - SMD/SMT")
        (field (name "Manufacturer") "YAGEO")
        (field (name "Part") "CC0603KRX7R9BB104")
        (field (name "Voltage Rated") "50V")
        (field (name "Tolerance") "±10%")
        (field (name "Capacitance") "100nF")
        (field (name "Temperature Coefficient") "X7R")
        (field (name "Peak Wavelength"))
        (field (name "Footprint") "PCM_JLCPCB:C_0603")
        (field (name "Datasheet") "https://www.lcsc.com/datasheet/lcsc_datasheet_2211101700_YAGEO-CC0603KRX7R9BB104_C14663.pdf")
        (field (name "Description") "50V 100nF X7R ±10% 0603 Multilayer Ceramic Capacitors MLCC - SMD/SMT ROHS"))
      (libsource (lib "PCM_JLCPCB-Capacitors") (part "0603,100nF") (description "50V 100nF X7R ±10% 0603 Multilayer Ceramic Capacitors MLCC - SMD/SMT ROHS"))
      (property (name "LCSC") (value "C14663"))
      (property (name "Stock") (value "70324515"))
      (property (name "Price") (value "0.006USD"))
      (property (name "Process") (value "SMT"))
      (property (name "Minimum Qty") (value "20"))
      (property (name "Attrition Qty") (value "10"))
      (property (name "Class") (value "Basic Component"))
      (property (name "Category") (value "Capacitors,Multilayer Ceramic Capacitors MLCC - SMD/SMT"))
      (property (name "Manufacturer") (value "YAGEO"))
      (property (name "Part") (value "CC0603KRX7R9BB104"))
      (property (name "Voltage Rated") (value "50V"))
      (property (name "Tolerance") (value "±10%"))
      (property (name "Capacitance") (value "100nF"))
      (property (name "Temperature Coefficient") (value "X7R"))
      (property (name "Peak Wavelength") (value ""))
      (property (name "Sheetname") (value "Root"))
      (property (name "Sheetfile") (value "Pico_Development_Stack.kicad_sch"))
      (property (name "ki_fp_filters") (value "C_*"))
      (sheetpath (names "/") (tstamps "/"))
      (tstamps "aaebd554-cbd2-4509-abd4-4694b2d01228"))
    (comp (ref "C26")
      (value "4.7uF")
      (footprint "PCM_JLCPCB:C_0603")
      (datasheet "https://www.lcsc.com/datasheet/lcsc_datasheet_2304140030_Samsung-Electro-Mechanics-CL10A475KO8NNNC_C19666.pdf")
      (description "16V 4.7uF X5R ±10% 0603 Multilayer Ceramic Capacitors MLCC - SMD/SMT ROHS")
      (fields
        (field (name "LCSC") "C19666")
        (field (name "Stock") "4246728")
        (field (name "Price") "0.013USD")
        (field (name "Process") "SMT")
        (field (name "Minimum Qty") "20")
        (field (name "Attrition Qty") "10")
        (field (name "Class") "Basic Component")
        (field (name "Category") "Capacitors,Multilayer Ceramic Capacitors MLCC - SMD/SMT")
        (field (name "Manufacturer") "Samsung Electro-Mechanics")
        (field (name "Part") "CL10A475KO8NNNC")
        (field (name "Voltage Rated") "16V")
        (field (name "Tolerance") "±10%")
        (field (name "Capacitance") "4.7uF")
        (field (name "Temperature Coefficient") "X5R")
        (field (name "Peak Wavelength"))
        (field (name "Footprint") "PCM_JLCPCB:C_0603")
        (field (name "Datasheet") "https://www.lcsc.com/datasheet/lcsc_datasheet_2304140030_Samsung-Electro-Mechanics-CL10A475KO8NNNC_C19666.pdf")
        (field (name "Description") "16V 4.7uF X5R ±10% 0603 Multilayer Ceramic Capacitors MLCC - SMD/SMT ROHS"))
      (libsource (lib "PCM_JLCPCB-Capacitors") (part "0603,4.7uF") (description "16V 4.7uF X5R ±10% 0603 Multilayer Ceramic Capacitors MLCC - SMD/SMT ROHS"))
      (property (name "LCSC") (value "C19666"))
      (property (name "Stock") (value "4246728"))
      (property (name "Price") (value "0.013USD"))
      (property (name "Process") (value "SMT"))
      (property (name "Minimum Qty") (value "20"))
      (property (name "Attrition Qty") (value "10"))
      (property (name "Class") (value "Basic Component"))
      (property (name "Category") (value "Capacitors,Multilayer Ceramic Capacitors MLCC - SMD/SMT"))
      (property (name "Manufacturer") (value "Samsung Electro-Mechanics"))
      (property (name "Part") (value "CL10A475KO8NNNC"))
      (property (name "Voltage Rated") (value "16V"))
      (property (name "Tolerance") (value "±10%"))
      (property (name "Capacitance") (value "4.7uF"))
      (property (name "Temperature Coefficient") (value "X5R"))
      (property (name "Peak Wavelength") (value ""))
      (property (name "Sheetname") (value "Root"))
      (property (name "Sheetfile") (value "Pico_Development_Stack.kicad_sch"))
      (property (name "ki_fp_filters") (value "C_*"))
      (sheetpath (names "/") (tstamps "/"))
      (tstamps "f74d9d0c-deed-4326-8e12-ee981638bfbf"))
    (comp (ref "C27")
      (value "100nF")
      (footprint "PCM_JLCPCB:C_0603")
      (datasheet "https://www.lcsc.com/datasheet/lcsc_datasheet_2211101700_YAGEO-CC0603KRX7R9BB104_C14663.pdf")
      (description "50V 100nF X7R ±10% 0603 Multilayer Ceramic Capacitors MLCC - SMD/SMT ROHS")
      (fields
        (field (name "LCSC") "C14663")
        (field (name "Stock") "70324515")
        (field (name "Price") "0.006USD")
        (field (name "Process") "SMT")
        (field (name "Minimum Qty") "20")
        (field (name "Attrition Qty") "10")
        (field (name "Class") "Basic Component")
        (field (name "Category") "Capacitors,Multilayer Ceramic Capacitors MLCC - SMD/SMT")
        (field (name "Manufacturer") "YAGEO")
        (field (name "Part") "CC0603KRX7R9BB104")
        (field (name "Voltage Rated") "50V")
        (field (name "Tolerance") "±10%")
        (field (name "Capacitance") "100nF")
        (field (name "Temperature Coefficient") "X7R")
        (field (name "Peak Wavelength"))
        (field (name "Footprint") "PCM_JLCPCB:C_0603")
        (field (name "Datasheet") "https://www.lcsc.com/datasheet/lcsc_datasheet_2211101700_YAGEO-CC0603KRX7R9BB104_C14663.pdf")
        (field (name "Description") "50V 100nF X7R ±10% 0603 Multilayer Ceramic Capacitors MLCC - SMD/SMT ROHS"))
      (libsource (lib "PCM_JLCPCB-Capacitors") (part "0603,100nF") (description "50V 100nF X7R ±10% 0603 Multilayer Ceramic Capacitors MLCC - SMD/SMT ROHS"))
      (property (name "LCSC") (value "C14663"))
      (property (name "Stock") (value "70324515"))
      (property (name "Price") (value "0.006USD"))
      (property (name "Process") (value "SMT"))
      (property (name "Minimum Qty") (value "20"))
      (property (name "Attrition Qty") (value "10"))
      (property (name "Class") (value "Basic Component"))
      (property (name "Category") (value "Capacitors,Multilayer Ceramic Capacitors MLCC - SMD/SMT"))
      (property (name "Manufacturer") (value "YAGEO"))
      (property (name "Part") (value "CC0603KRX7R9BB104"))
      (property (name "Voltage Rated") (value "50V"))
      (property (name "Tolerance") (value "±10%"))
      (property (name "Capacitance") (value "100nF"))
      (property (name "Temperature Coefficient") (value "X7R"))
      (property (name "Peak Wavelength") (value ""))
      (property (name "Sheetname") (value "Root"))
      (property (name "Sheetfile") (value "Pico_Development_Stack.kicad_sch"))
      (property (name "ki_fp_filters") (value "C_*"))
      (sheetpath (names "/") (tstamps "/"))
      (tstamps "e8b9cc6f-45d6-46e1-a3eb-df0af3f1b29d"))
    (comp (ref "C28")
      (value "100nF")
      (footprint "PCM_JLCPCB:C_0603")
      (datasheet "https://www.lcsc.com/datasheet/lcsc_datasheet_2211101700_YAGEO-CC0603KRX7R9BB104_C14663.pdf")
      (description "50V 100nF X7R ±10% 0603 Multilayer Ceramic Capacitors MLCC - SMD/SMT ROHS")
      (fields
        (field (name "LCSC") "C14663")
        (field (name "Stock") "70324515")
        (field (name "Price") "0.006USD")
        (field (name "Process") "SMT")
        (field (name "Minimum Qty") "20")
        (field (name "Attrition Qty") "10")
        (field (name "Class") "Basic Component")
        (field (name "Category") "Capacitors,Multilayer Ceramic Capacitors MLCC - SMD/SMT")
        (field (name "Manufacturer") "YAGEO")
        (field (name "Part") "CC0603KRX7R9BB104")
        (field (name "Voltage Rated") "50V")
        (field (name "Tolerance") "±10%")
        (field (name "Capacitance") "100nF")
        (field (name "Temperature Coefficient") "X7R")
        (field (name "Peak Wavelength"))
        (field (name "Footprint") "PCM_JLCPCB:C_0603")
        (field (name "Datasheet") "https://www.lcsc.com/datasheet/lcsc_datasheet_2211101700_YAGEO-CC0603KRX7R9BB104_C14663.pdf")
        (field (name "Description") "50V 100nF X7R ±10% 0603 Multilayer Ceramic Capacitors MLCC - SMD/SMT ROHS"))
      (libsource (lib "PCM_JLCPCB-Capacitors") (part "0603,100nF") (description "50V 100nF X7R ±10% 0603 Multilayer Ceramic Capacitors MLCC - SMD/SMT ROHS"))
      (property (name "LCSC") (value "C14663"))
      (property (name "Stock") (value "70324515"))
      (property (name "Price") (value "0.006USD"))
      (property (name "Process") (value "SMT"))
      (property (name "Minimum Qty") (value "20"))
      (property (name "Attrition Qty") (value "10"))
      (property (name "Class") (value "Basic Component"))
      (property (name "Category") (value "Capacitors,Multilayer Ceramic Capacitors MLCC - SMD/SMT"))
      (property (name "Manufacturer") (value "YAGEO"))
      (property (name "Part") (value "CC0603KRX7R9BB104"))
      (property (name "Voltage Rated") (value "50V"))
      (property (name "Tolerance") (value "±10%"))
      (property (name "Capacitance") (value "100nF"))
      (property (name "Temperature Coefficient") (value "X7R"))
      (property (name "Peak Wavelength") (value ""))
      (property (name "Sheetname") (value "Root"))
      (property (name "Sheetfile") (value "Pico_Development_Stack.kicad_sch"))
      (property (name "ki_fp_filters") (value "C_*"))
      (sheetpath (names "/") (tstamps "/"))
      (tstamps "e0b12413-ece6-447b-95f8-5f0cf46dce46"))
    (comp (ref "C29")
      (value "100nF")
      (footprint "PCM_JLCPCB:C_0603")
      (datasheet "https://www.lcsc.com/datasheet/lcsc_datasheet_2211101700_YAGEO-CC0603KRX7R9BB104_C14663.pdf")
      (description "50V 100nF X7R ±10% 0603 Multilayer Ceramic Capacitors MLCC - SMD/SMT ROHS")
      (fields
        (field (name "LCSC") "C14663")
        (field (name "Stock") "70324515")
        (field (name "Price") "0.006USD")
        (field (name "Process") "SMT")
        (field (name "Minimum Qty") "20")
        (field (name "Attrition Qty") "10")
        (field (name "Class") "Basic Component")
        (field (name "Category") "Capacitors,Multilayer Ceramic Capacitors MLCC - SMD/SMT")
        (field (name "Manufacturer") "YAGEO")
        (field (name "Part") "CC0603KRX7R9BB104")
        (field (name "Voltage Rated") "50V")
        (field (name "Tolerance") "±10%")
        (field (name "Capacitance") "100nF")
        (field (name "Temperature Coefficient") "X7R")
        (field (name "Peak Wavelength"))
        (field (name "Footprint") "PCM_JLCPCB:C_0603")
        (field (name "Datasheet") "https://www.lcsc.com/datasheet/lcsc_datasheet_2211101700_YAGEO-CC0603KRX7R9BB104_C14663.pdf")
        (field (name "Description") "50V 100nF X7R ±10% 0603 Multilayer Ceramic Capacitors MLCC - SMD/SMT ROHS"))
      (libsource (lib "PCM_JLCPCB-Capacitors") (part "0603,100nF") (description "50V 100nF X7R ±10% 0603 Multilayer Ceramic Capacitors MLCC - SMD/SMT ROHS"))
      (property (name "LCSC") (value "C14663"))
      (property (name "Stock") (value "70324515"))
      (property (name "Price") (value "0.006USD"))
      (property (name "Process") (value "SMT"))
      (property (name "Minimum Qty") (value "20"))
      (property (name "Attrition Qty") (value "10"))
      (property (name "Class") (value "Basic Component"))
      (property (name "Category") (value "Capacitors,Multilayer Ceramic Capacitors MLCC - SMD/SMT"))
      (property (name "Manufacturer") (value "YAGEO"))
      (property (name "Part") (value "CC0603KRX7R9BB104"))
      (property (name "Voltage Rated") (value "50V"))
      (property (name "Tolerance") (value "±10%"))
      (property (name "Capacitance") (value "100nF"))
      (property (name "Temperature Coefficient") (value "X7R"))
      (property (name "Peak Wavelength") (value ""))
      (property (name "Sheetname") (value "Root"))
      (property (name "Sheetfile") (value "Pico_Development_Stack.kicad_sch"))
      (property (name "ki_fp_filters") (value "C_*"))
      (sheetpath (names "/") (tstamps "/"))
      (tstamps "873663b2-8935-4546-b954-d496e2f44f45"))
    (comp (ref "C30")
      (value "4.7uF")
      (footprint "PCM_JLCPCB:C_0603")
      (datasheet "https://www.lcsc.com/datasheet/lcsc_datasheet_2304140030_Samsung-Electro-Mechanics-CL10A475KO8NNNC_C19666.pdf")
      (description "16V 4.7uF X5R ±10% 0603 Multilayer Ceramic Capacitors MLCC - SMD/SMT ROHS")
      (fields
        (field (name "LCSC") "C19666")
        (field (name "Stock") "4246728")
        (field (name "Price") "0.013USD")
        (field (name "Process") "SMT")
        (field (name "Minimum Qty") "20")
        (field (name "Attrition Qty") "10")
        (field (name "Class") "Basic Component")
        (field (name "Category") "Capacitors,Multilayer Ceramic Capacitors MLCC - SMD/SMT")
        (field (name "Manufacturer") "Samsung Electro-Mechanics")
        (field (name "Part") "CL10A475KO8NNNC")
        (field (name "Voltage Rated") "16V")
        (field (name "Tolerance") "±10%")
        (field (name "Capacitance") "4.7uF")
        (field (name "Temperature Coefficient") "X5R")
        (field (name "Peak Wavelength"))
        (field (name "Footprint") "PCM_JLCPCB:C_0603")
        (field (name "Datasheet") "https://www.lcsc.com/datasheet/lcsc_datasheet_2304140030_Samsung-Electro-Mechanics-CL10A475KO8NNNC_C19666.pdf")
        (field (name "Description") "16V 4.7uF X5R ±10% 0603 Multilayer Ceramic Capacitors MLCC - SMD/SMT ROHS"))
      (libsource (lib "PCM_JLCPCB-Capacitors") (part "0603,4.7uF") (description "16V 4.7uF X5R ±10% 0603 Multilayer Ceramic Capacitors MLCC - SMD/SMT ROHS"))
      (property (name "LCSC") (value "C19666"))
      (property (name "Stock") (value "4246728"))
      (property (name "Price") (value "0.013USD"))
      (property (name "Process") (value "SMT"))
      (property (name "Minimum Qty") (value "20"))
      (property (name "Attrition Qty") (value "10"))
      (property (name "Class") (value "Basic Component"))
      (property (name "Category") (value "Capacitors,Multilayer Ceramic Capacitors MLCC - SMD/SMT"))
      (property (name "Manufacturer") (value "Samsung Electro-Mechanics"))
      (property (name "Part") (value "CL10A475KO8NNNC"))
      (property (name "Voltage Rated") (value "16V"))
      (property (name "Tolerance") (value "±10%"))
      (property (name "Capacitance") (value "4.7uF"))
      (property (name "Temperature Coefficient") (value "X5R"))
      (property (name "Peak Wavelength") (value ""))
      (property (name "Sheetname") (value "Root"))
      (property (name "Sheetfile") (value "Pico_Development_Stack.kicad_sch"))
      (property (name "ki_fp_filters") (value "C_*"))
      (sheetpath (names "/") (tstamps "/"))
      (tstamps "7c456a5d-525f-41ba-9538-c5f92bb68a56"))
    (comp (ref "C31")
      (value "100nF")
      (footprint "PCM_JLCPCB:C_0603")
      (datasheet "https://www.lcsc.com/datasheet/lcsc_datasheet_2211101700_YAGEO-CC0603KRX7R9BB104_C14663.pdf")
      (description "50V 100nF X7R ±10% 0603 Multilayer Ceramic Capacitors MLCC - SMD/SMT ROHS")
      (fields
        (field (name "LCSC") "C14663")
        (field (name "Stock") "70324515")
        (field (name "Price") "0.006USD")
        (field (name "Process") "SMT")
        (field (name "Minimum Qty") "20")
        (field (name "Attrition Qty") "10")
        (field (name "Class") "Basic Component")
        (field (name "Category") "Capacitors,Multilayer Ceramic Capacitors MLCC - SMD/SMT")
        (field (name "Manufacturer") "YAGEO")
        (field (name "Part") "CC0603KRX7R9BB104")
        (field (name "Voltage Rated") "50V")
        (field (name "Tolerance") "±10%")
        (field (name "Capacitance") "100nF")
        (field (name "Temperature Coefficient") "X7R")
        (field (name "Peak Wavelength"))
        (field (name "Footprint") "PCM_JLCPCB:C_0603")
        (field (name "Datasheet") "https://www.lcsc.com/datasheet/lcsc_datasheet_2211101700_YAGEO-CC0603KRX7R9BB104_C14663.pdf")
        (field (name "Description") "50V 100nF X7R ±10% 0603 Multilayer Ceramic Capacitors MLCC - SMD/SMT ROHS"))
      (libsource (lib "PCM_JLCPCB-Capacitors") (part "0603,100nF") (description "50V 100nF X7R ±10% 0603 Multilayer Ceramic Capacitors MLCC - SMD/SMT ROHS"))
      (property (name "LCSC") (value "C14663"))
      (property (name "Stock") (value "70324515"))
      (property (name "Price") (value "0.006USD"))
      (property (name "Process") (value "SMT"))
      (property (name "Minimum Qty") (value "20"))
      (property (name "Attrition Qty") (value "10"))
      (property (name "Class") (value "Basic Component"))
      (property (name "Category") (value "Capacitors,Multilayer Ceramic Capacitors MLCC - SMD/SMT"))
      (property (name "Manufacturer") (value "YAGEO"))
      (property (name "Part") (value "CC0603KRX7R9BB104"))
      (property (name "Voltage Rated") (value "50V"))
      (property (name "Tolerance") (value "±10%"))
      (property (name "Capacitance") (value "100nF"))
      (property (name "Temperature Coefficient") (value "X7R"))
      (property (name "Peak Wavelength") (value ""))
      (property (name "Sheetname") (value "Root"))
      (property (name "Sheetfile") (value "Pico_Development_Stack.kicad_sch"))
      (property (name "ki_fp_filters") (value "C_*"))
      (sheetpath (names "/") (tstamps "/"))
      (tstamps "79128338-b6f2-48ef-9651-77ad70c91b5a"))
    (comp (ref "C32")
      (value "100n")
      (footprint "PCM_JLCPCB:C_0603")
      (datasheet "https://www.lcsc.com/datasheet/lcsc_datasheet_2211101700_YAGEO-CC0603KRX7R9BB104_C14663.pdf")
      (description "50V 100nF X7R ±10% 0603 Multilayer Ceramic Capacitors MLCC - SMD/SMT ROHS")
      (fields
        (field (name "Peak Wavelength"))
        (field (name "LCSC") "C14663")
        (field (name "Stock") "70324515")
        (field (name "Price") "0.006USD")
        (field (name "Process") "SMT")
        (field (name "Minimum Qty") "20")
        (field (name "Attrition Qty") "10")
        (field (name "Class") "Basic Component")
        (field (name "Category") "Capacitors,Multilayer Ceramic Capacitors MLCC - SMD/SMT")
        (field (name "Manufacturer") "YAGEO")
        (field (name "Part") "CC0603KRX7R9BB104")
        (field (name "Voltage Rated") "50V")
        (field (name "Tolerance") "±10%")
        (field (name "Capacitance") "100nF")
        (field (name "Temperature Coefficient") "X7R")
        (field (name "Footprint") "PCM_JLCPCB:C_0603")
        (field (name "Datasheet") "https://www.lcsc.com/datasheet/lcsc_datasheet_2211101700_YAGEO-CC0603KRX7R9BB104_C14663.pdf")
        (field (name "Description") "50V 100nF X7R ±10% 0603 Multilayer Ceramic Capacitors MLCC - SMD/SMT ROHS"))
      (libsource (lib "PCM_JLCPCB-Capacitors") (part "0603,100nF") (description "50V 100nF X7R ±10% 0603 Multilayer Ceramic Capacitors MLCC - SMD/SMT ROHS"))
      (property (name "Peak Wavelength") (value ""))
      (property (name "LCSC") (value "C14663"))
      (property (name "Stock") (value "70324515"))
      (property (name "Price") (value "0.006USD"))
      (property (name "Process") (value "SMT"))
      (property (name "Minimum Qty") (value "20"))
      (property (name "Attrition Qty") (value "10"))
      (property (name "Class") (value "Basic Component"))
      (property (name "Category") (value "Capacitors,Multilayer Ceramic Capacitors MLCC - SMD/SMT"))
      (property (name "Manufacturer") (value "YAGEO"))
      (property (name "Part") (value "CC0603KRX7R9BB104"))
      (property (name "Voltage Rated") (value "50V"))
      (property (name "Tolerance") (value "±10%"))
      (property (name "Capacitance") (value "100nF"))
      (property (name "Temperature Coefficient") (value "X7R"))
      (property (name "Sheetname") (value "Root"))
      (property (name "Sheetfile") (value "Pico_Development_Stack.kicad_sch"))
      (property (name "ki_fp_filters") (value "C_*"))
      (sheetpath (names "/") (tstamps "/"))
      (tstamps "da8af28b-ccc7-456c-bf95-34231815c364"))
    (comp (ref "C33")
      (value "100nF")
      (footprint "PCM_JLCPCB:C_0603")
      (datasheet "https://www.lcsc.com/datasheet/lcsc_datasheet_2211101700_YAGEO-CC0603KRX7R9BB104_C14663.pdf")
      (description "50V 100nF X7R ±10% 0603 Multilayer Ceramic Capacitors MLCC - SMD/SMT ROHS")
      (fields
        (field (name "LCSC") "C14663")
        (field (name "Stock") "70324515")
        (field (name "Price") "0.006USD")
        (field (name "Process") "SMT")
        (field (name "Minimum Qty") "20")
        (field (name "Attrition Qty") "10")
        (field (name "Class") "Basic Component")
        (field (name "Category") "Capacitors,Multilayer Ceramic Capacitors MLCC - SMD/SMT")
        (field (name "Manufacturer") "YAGEO")
        (field (name "Part") "CC0603KRX7R9BB104")
        (field (name "Voltage Rated") "50V")
        (field (name "Tolerance") "±10%")
        (field (name "Capacitance") "100nF")
        (field (name "Temperature Coefficient") "X7R")
        (field (name "Peak Wavelength"))
        (field (name "Footprint") "PCM_JLCPCB:C_0603")
        (field (name "Datasheet") "https://www.lcsc.com/datasheet/lcsc_datasheet_2211101700_YAGEO-CC0603KRX7R9BB104_C14663.pdf")
        (field (name "Description") "50V 100nF X7R ±10% 0603 Multilayer Ceramic Capacitors MLCC - SMD/SMT ROHS"))
      (libsource (lib "PCM_JLCPCB-Capacitors") (part "0603,100nF") (description "50V 100nF X7R ±10% 0603 Multilayer Ceramic Capacitors MLCC - SMD/SMT ROHS"))
      (property (name "LCSC") (value "C14663"))
      (property (name "Stock") (value "70324515"))
      (property (name "Price") (value "0.006USD"))
      (property (name "Process") (value "SMT"))
      (property (name "Minimum Qty") (value "20"))
      (property (name "Attrition Qty") (value "10"))
      (property (name "Class") (value "Basic Component"))
      (property (name "Category") (value "Capacitors,Multilayer Ceramic Capacitors MLCC - SMD/SMT"))
      (property (name "Manufacturer") (value "YAGEO"))
      (property (name "Part") (value "CC0603KRX7R9BB104"))
      (property (name "Voltage Rated") (value "50V"))
      (property (name "Tolerance") (value "±10%"))
      (property (name "Capacitance") (value "100nF"))
      (property (name "Temperature Coefficient") (value "X7R"))
      (property (name "Peak Wavelength") (value ""))
      (property (name "Sheetname") (value "Root"))
      (property (name "Sheetfile") (value "Pico_Development_Stack.kicad_sch"))
      (property (name "ki_fp_filters") (value "C_*"))
      (sheetpath (names "/") (tstamps "/"))
      (tstamps "2f4d4903-1c43-4e39-ac3f-e6f6d8c4c7b7"))
    (comp (ref "C34")
      (value "100nF")
      (footprint "PCM_JLCPCB:C_0603")
      (datasheet "https://www.lcsc.com/datasheet/lcsc_datasheet_2211101700_YAGEO-CC0603KRX7R9BB104_C14663.pdf")
      (description "50V 100nF X7R ±10% 0603 Multilayer Ceramic Capacitors MLCC - SMD/SMT ROHS")
      (fields
        (field (name "LCSC") "C14663")
        (field (name "Stock") "70324515")
        (field (name "Price") "0.006USD")
        (field (name "Process") "SMT")
        (field (name "Minimum Qty") "20")
        (field (name "Attrition Qty") "10")
        (field (name "Class") "Basic Component")
        (field (name "Category") "Capacitors,Multilayer Ceramic Capacitors MLCC - SMD/SMT")
        (field (name "Manufacturer") "YAGEO")
        (field (name "Part") "CC0603KRX7R9BB104")
        (field (name "Voltage Rated") "50V")
        (field (name "Tolerance") "±10%")
        (field (name "Capacitance") "100nF")
        (field (name "Temperature Coefficient") "X7R")
        (field (name "Peak Wavelength"))
        (field (name "Footprint") "PCM_JLCPCB:C_0603")
        (field (name "Datasheet") "https://www.lcsc.com/datasheet/lcsc_datasheet_2211101700_YAGEO-CC0603KRX7R9BB104_C14663.pdf")
        (field (name "Description") "50V 100nF X7R ±10% 0603 Multilayer Ceramic Capacitors MLCC - SMD/SMT ROHS"))
      (libsource (lib "PCM_JLCPCB-Capacitors") (part "0603,100nF") (description "50V 100nF X7R ±10% 0603 Multilayer Ceramic Capacitors MLCC - SMD/SMT ROHS"))
      (property (name "LCSC") (value "C14663"))
      (property (name "Stock") (value "70324515"))
      (property (name "Price") (value "0.006USD"))
      (property (name "Process") (value "SMT"))
      (property (name "Minimum Qty") (value "20"))
      (property (name "Attrition Qty") (value "10"))
      (property (name "Class") (value "Basic Component"))
      (property (name "Category") (value "Capacitors,Multilayer Ceramic Capacitors MLCC - SMD/SMT"))
      (property (name "Manufacturer") (value "YAGEO"))
      (property (name "Part") (value "CC0603KRX7R9BB104"))
      (property (name "Voltage Rated") (value "50V"))
      (property (name "Tolerance") (value "±10%"))
      (property (name "Capacitance") (value "100nF"))
      (property (name "Temperature Coefficient") (value "X7R"))
      (property (name "Peak Wavelength") (value ""))
      (property (name "Sheetname") (value "Root"))
      (property (name "Sheetfile") (value "Pico_Development_Stack.kicad_sch"))
      (property (name "ki_fp_filters") (value "C_*"))
      (sheetpath (names "/") (tstamps "/"))
      (tstamps "e2f00ef4-2e52-44ad-8080-6618dc923abf"))
    (comp (ref "C35")
      (value "100nF")
      (footprint "PCM_JLCPCB:C_0603")
      (datasheet "https://www.lcsc.com/datasheet/lcsc_datasheet_2211101700_YAGEO-CC0603KRX7R9BB104_C14663.pdf")
      (description "50V 100nF X7R ±10% 0603 Multilayer Ceramic Capacitors MLCC - SMD/SMT ROHS")
      (fields
        (field (name "LCSC") "C14663")
        (field (name "Stock") "70324515")
        (field (name "Price") "0.006USD")
        (field (name "Process") "SMT")
        (field (name "Minimum Qty") "20")
        (field (name "Attrition Qty") "10")
        (field (name "Class") "Basic Component")
        (field (name "Category") "Capacitors,Multilayer Ceramic Capacitors MLCC - SMD/SMT")
        (field (name "Manufacturer") "YAGEO")
        (field (name "Part") "CC0603KRX7R9BB104")
        (field (name "Voltage Rated") "50V")
        (field (name "Tolerance") "±10%")
        (field (name "Capacitance") "100nF")
        (field (name "Temperature Coefficient") "X7R")
        (field (name "Peak Wavelength"))
        (field (name "Footprint") "PCM_JLCPCB:C_0603")
        (field (name "Datasheet") "https://www.lcsc.com/datasheet/lcsc_datasheet_2211101700_YAGEO-CC0603KRX7R9BB104_C14663.pdf")
        (field (name "Description") "50V 100nF X7R ±10% 0603 Multilayer Ceramic Capacitors MLCC - SMD/SMT ROHS"))
      (libsource (lib "PCM_JLCPCB-Capacitors") (part "0603,100nF") (description "50V 100nF X7R ±10% 0603 Multilayer Ceramic Capacitors MLCC - SMD/SMT ROHS"))
      (property (name "LCSC") (value "C14663"))
      (property (name "Stock") (value "70324515"))
      (property (name "Price") (value "0.006USD"))
      (property (name "Process") (value "SMT"))
      (property (name "Minimum Qty") (value "20"))
      (property (name "Attrition Qty") (value "10"))
      (property (name "Class") (value "Basic Component"))
      (property (name "Category") (value "Capacitors,Multilayer Ceramic Capacitors MLCC - SMD/SMT"))
      (property (name "Manufacturer") (value "YAGEO"))
      (property (name "Part") (value "CC0603KRX7R9BB104"))
      (property (name "Voltage Rated") (value "50V"))
      (property (name "Tolerance") (value "±10%"))
      (property (name "Capacitance") (value "100nF"))
      (property (name "Temperature Coefficient") (value "X7R"))
      (property (name "Peak Wavelength") (value ""))
      (property (name "Sheetname") (value "Root"))
      (property (name "Sheetfile") (value "Pico_Development_Stack.kicad_sch"))
      (property (name "ki_fp_filters") (value "C_*"))
      (sheetpath (names "/") (tstamps "/"))
      (tstamps "4370ad8e-e7aa-4ca7-9f03-ec5d0a1f4b6d"))
    (comp (ref "C36")
      (value "100nF")
      (footprint "PCM_JLCPCB:C_0603")
      (datasheet "https://www.lcsc.com/datasheet/lcsc_datasheet_2211101700_YAGEO-CC0603KRX7R9BB104_C14663.pdf")
      (description "50V 100nF X7R ±10% 0603 Multilayer Ceramic Capacitors MLCC - SMD/SMT ROHS")
      (fields
        (field (name "LCSC") "C14663")
        (field (name "Stock") "70324515")
        (field (name "Price") "0.006USD")
        (field (name "Process") "SMT")
        (field (name "Minimum Qty") "20")
        (field (name "Attrition Qty") "10")
        (field (name "Class") "Basic Component")
        (field (name "Category") "Capacitors,Multilayer Ceramic Capacitors MLCC - SMD/SMT")
        (field (name "Manufacturer") "YAGEO")
        (field (name "Part") "CC0603KRX7R9BB104")
        (field (name "Voltage Rated") "50V")
        (field (name "Tolerance") "±10%")
        (field (name "Capacitance") "100nF")
        (field (name "Temperature Coefficient") "X7R")
        (field (name "Peak Wavelength"))
        (field (name "Footprint") "PCM_JLCPCB:C_0603")
        (field (name "Datasheet") "https://www.lcsc.com/datasheet/lcsc_datasheet_2211101700_YAGEO-CC0603KRX7R9BB104_C14663.pdf")
        (field (name "Description") "50V 100nF X7R ±10% 0603 Multilayer Ceramic Capacitors MLCC - SMD/SMT ROHS"))
      (libsource (lib "PCM_JLCPCB-Capacitors") (part "0603,100nF") (description "50V 100nF X7R ±10% 0603 Multilayer Ceramic Capacitors MLCC - SMD/SMT ROHS"))
      (property (name "LCSC") (value "C14663"))
      (property (name "Stock") (value "70324515"))
      (property (name "Price") (value "0.006USD"))
      (property (name "Process") (value "SMT"))
      (property (name "Minimum Qty") (value "20"))
      (property (name "Attrition Qty") (value "10"))
      (property (name "Class") (value "Basic Component"))
      (property (name "Category") (value "Capacitors,Multilayer Ceramic Capacitors MLCC - SMD/SMT"))
      (property (name "Manufacturer") (value "YAGEO"))
      (property (name "Part") (value "CC0603KRX7R9BB104"))
      (property (name "Voltage Rated") (value "50V"))
      (property (name "Tolerance") (value "±10%"))
      (property (name "Capacitance") (value "100nF"))
      (property (name "Temperature Coefficient") (value "X7R"))
      (property (name "Peak Wavelength") (value ""))
      (property (name "Sheetname") (value "Root"))
      (property (name "Sheetfile") (value "Pico_Development_Stack.kicad_sch"))
      (property (name "ki_fp_filters") (value "C_*"))
      (sheetpath (names "/") (tstamps "/"))
      (tstamps "6656456e-064b-45f4-95b9-a9eaaae7918c"))
    (comp (ref "C37")
      (value "100nF")
      (footprint "PCM_JLCPCB:C_0603")
      (datasheet "https://www.lcsc.com/datasheet/lcsc_datasheet_2211101700_YAGEO-CC0603KRX7R9BB104_C14663.pdf")
      (description "50V 100nF X7R ±10% 0603 Multilayer Ceramic Capacitors MLCC - SMD/SMT ROHS")
      (fields
        (field (name "LCSC") "C14663")
        (field (name "Stock") "70324515")
        (field (name "Price") "0.006USD")
        (field (name "Process") "SMT")
        (field (name "Minimum Qty") "20")
        (field (name "Attrition Qty") "10")
        (field (name "Class") "Basic Component")
        (field (name "Category") "Capacitors,Multilayer Ceramic Capacitors MLCC - SMD/SMT")
        (field (name "Manufacturer") "YAGEO")
        (field (name "Part") "CC0603KRX7R9BB104")
        (field (name "Voltage Rated") "50V")
        (field (name "Tolerance") "±10%")
        (field (name "Capacitance") "100nF")
        (field (name "Temperature Coefficient") "X7R")
        (field (name "Peak Wavelength"))
        (field (name "Footprint") "PCM_JLCPCB:C_0603")
        (field (name "Datasheet") "https://www.lcsc.com/datasheet/lcsc_datasheet_2211101700_YAGEO-CC0603KRX7R9BB104_C14663.pdf")
        (field (name "Description") "50V 100nF X7R ±10% 0603 Multilayer Ceramic Capacitors MLCC - SMD/SMT ROHS"))
      (libsource (lib "PCM_JLCPCB-Capacitors") (part "0603,100nF") (description "50V 100nF X7R ±10% 0603 Multilayer Ceramic Capacitors MLCC - SMD/SMT ROHS"))
      (property (name "LCSC") (value "C14663"))
      (property (name "Stock") (value "70324515"))
      (property (name "Price") (value "0.006USD"))
      (property (name "Process") (value "SMT"))
      (property (name "Minimum Qty") (value "20"))
      (property (name "Attrition Qty") (value "10"))
      (property (name "Class") (value "Basic Component"))
      (property (name "Category") (value "Capacitors,Multilayer Ceramic Capacitors MLCC - SMD/SMT"))
      (property (name "Manufacturer") (value "YAGEO"))
      (property (name "Part") (value "CC0603KRX7R9BB104"))
      (property (name "Voltage Rated") (value "50V"))
      (property (name "Tolerance") (value "±10%"))
      (property (name "Capacitance") (value "100nF"))
      (property (name "Temperature Coefficient") (value "X7R"))
      (property (name "Peak Wavelength") (value ""))
      (property (name "Sheetname") (value "Root"))
      (property (name "Sheetfile") (value "Pico_Development_Stack.kicad_sch"))
      (property (name "ki_fp_filters") (value "C_*"))
      (sheetpath (names "/") (tstamps "/"))
      (tstamps "7d0f20d1-c7f8-4761-8048-be2d64ce4be7"))
    (comp (ref "C38")
      (value "100nF")
      (footprint "PCM_JLCPCB:C_0603")
      (datasheet "https://www.lcsc.com/datasheet/lcsc_datasheet_2211101700_YAGEO-CC0603KRX7R9BB104_C14663.pdf")
      (description "50V 100nF X7R ±10% 0603 Multilayer Ceramic Capacitors MLCC - SMD/SMT ROHS")
      (fields
        (field (name "LCSC") "C14663")
        (field (name "Stock") "70324515")
        (field (name "Price") "0.006USD")
        (field (name "Process") "SMT")
        (field (name "Minimum Qty") "20")
        (field (name "Attrition Qty") "10")
        (field (name "Class") "Basic Component")
        (field (name "Category") "Capacitors,Multilayer Ceramic Capacitors MLCC - SMD/SMT")
        (field (name "Manufacturer") "YAGEO")
        (field (name "Part") "CC0603KRX7R9BB104")
        (field (name "Voltage Rated") "50V")
        (field (name "Tolerance") "±10%")
        (field (name "Capacitance") "100nF")
        (field (name "Temperature Coefficient") "X7R")
        (field (name "Peak Wavelength"))
        (field (name "Footprint") "PCM_JLCPCB:C_0603")
        (field (name "Datasheet") "https://www.lcsc.com/datasheet/lcsc_datasheet_2211101700_YAGEO-CC0603KRX7R9BB104_C14663.pdf")
        (field (name "Description") "50V 100nF X7R ±10% 0603 Multilayer Ceramic Capacitors MLCC - SMD/SMT ROHS"))
      (libsource (lib "PCM_JLCPCB-Capacitors") (part "0603,100nF") (description "50V 100nF X7R ±10% 0603 Multilayer Ceramic Capacitors MLCC - SMD/SMT ROHS"))
      (property (name "LCSC") (value "C14663"))
      (property (name "Stock") (value "70324515"))
      (property (name "Price") (value "0.006USD"))
      (property (name "Process") (value "SMT"))
      (property (name "Minimum Qty") (value "20"))
      (property (name "Attrition Qty") (value "10"))
      (property (name "Class") (value "Basic Component"))
      (property (name "Category") (value "Capacitors,Multilayer Ceramic Capacitors MLCC - SMD/SMT"))
      (property (name "Manufacturer") (value "YAGEO"))
      (property (name "Part") (value "CC0603KRX7R9BB104"))
      (property (name "Voltage Rated") (value "50V"))
      (property (name "Tolerance") (value "±10%"))
      (property (name "Capacitance") (value "100nF"))
      (property (name "Temperature Coefficient") (value "X7R"))
      (property (name "Peak Wavelength") (value ""))
      (property (name "Sheetname") (value "Root"))
      (property (name "Sheetfile") (value "Pico_Development_Stack.kicad_sch"))
      (property (name "ki_fp_filters") (value "C_*"))
      (sheetpath (names "/") (tstamps "/"))
      (tstamps "36dfb3c3-4554-4fc9-b1e4-bfa76814b88c"))
    (comp (ref "C39")
      (value "100nF")
      (footprint "PCM_JLCPCB:C_0603")
      (datasheet "https://www.lcsc.com/datasheet/lcsc_datasheet_2211101700_YAGEO-CC0603KRX7R9BB104_C14663.pdf")
      (description "50V 100nF X7R ±10% 0603 Multilayer Ceramic Capacitors MLCC - SMD/SMT ROHS")
      (fields
        (field (name "LCSC") "C14663")
        (field (name "Stock") "70324515")
        (field (name "Price") "0.006USD")
        (field (name "Process") "SMT")
        (field (name "Minimum Qty") "20")
        (field (name "Attrition Qty") "10")
        (field (name "Class") "Basic Component")
        (field (name "Category") "Capacitors,Multilayer Ceramic Capacitors MLCC - SMD/SMT")
        (field (name "Manufacturer") "YAGEO")
        (field (name "Part") "CC0603KRX7R9BB104")
        (field (name "Voltage Rated") "50V")
        (field (name "Tolerance") "±10%")
        (field (name "Capacitance") "100nF")
        (field (name "Temperature Coefficient") "X7R")
        (field (name "Peak Wavelength"))
        (field (name "Footprint") "PCM_JLCPCB:C_0603")
        (field (name "Datasheet") "https://www.lcsc.com/datasheet/lcsc_datasheet_2211101700_YAGEO-CC0603KRX7R9BB104_C14663.pdf")
        (field (name "Description") "50V 100nF X7R ±10% 0603 Multilayer Ceramic Capacitors MLCC - SMD/SMT ROHS"))
      (libsource (lib "PCM_JLCPCB-Capacitors") (part "0603,100nF") (description "50V 100nF X7R ±10% 0603 Multilayer Ceramic Capacitors MLCC - SMD/SMT ROHS"))
      (property (name "LCSC") (value "C14663"))
      (property (name "Stock") (value "70324515"))
      (property (name "Price") (value "0.006USD"))
      (property (name "Process") (value "SMT"))
      (property (name "Minimum Qty") (value "20"))
      (property (name "Attrition Qty") (value "10"))
      (property (name "Class") (value "Basic Component"))
      (property (name "Category") (value "Capacitors,Multilayer Ceramic Capacitors MLCC - SMD/SMT"))
      (property (name "Manufacturer") (value "YAGEO"))
      (property (name "Part") (value "CC0603KRX7R9BB104"))
      (property (name "Voltage Rated") (value "50V"))
      (property (name "Tolerance") (value "±10%"))
      (property (name "Capacitance") (value "100nF"))
      (property (name "Temperature Coefficient") (value "X7R"))
      (property (name "Peak Wavelength") (value ""))
      (property (name "Sheetname") (value "Root"))
      (property (name "Sheetfile") (value "Pico_Development_Stack.kicad_sch"))
      (property (name "ki_fp_filters") (value "C_*"))
      (sheetpath (names "/") (tstamps "/"))
      (tstamps "16761f3f-bbdb-4f41-bd6c-0ec570a62cc6"))
    (comp (ref "C40")
      (value "100nF")
      (footprint "PCM_JLCPCB:C_0603")
      (datasheet "https://www.lcsc.com/datasheet/lcsc_datasheet_2211101700_YAGEO-CC0603KRX7R9BB104_C14663.pdf")
      (description "50V 100nF X7R ±10% 0603 Multilayer Ceramic Capacitors MLCC - SMD/SMT ROHS")
      (fields
        (field (name "LCSC") "C14663")
        (field (name "Stock") "70324515")
        (field (name "Price") "0.006USD")
        (field (name "Process") "SMT")
        (field (name "Minimum Qty") "20")
        (field (name "Attrition Qty") "10")
        (field (name "Class") "Basic Component")
        (field (name "Category") "Capacitors,Multilayer Ceramic Capacitors MLCC - SMD/SMT")
        (field (name "Manufacturer") "YAGEO")
        (field (name "Part") "CC0603KRX7R9BB104")
        (field (name "Voltage Rated") "50V")
        (field (name "Tolerance") "±10%")
        (field (name "Capacitance") "100nF")
        (field (name "Temperature Coefficient") "X7R")
        (field (name "Peak Wavelength"))
        (field (name "Footprint") "PCM_JLCPCB:C_0603")
        (field (name "Datasheet") "https://www.lcsc.com/datasheet/lcsc_datasheet_2211101700_YAGEO-CC0603KRX7R9BB104_C14663.pdf")
        (field (name "Description") "50V 100nF X7R ±10% 0603 Multilayer Ceramic Capacitors MLCC - SMD/SMT ROHS"))
      (libsource (lib "PCM_JLCPCB-Capacitors") (part "0603,100nF") (description "50V 100nF X7R ±10% 0603 Multilayer Ceramic Capacitors MLCC - SMD/SMT ROHS"))
      (property (name "LCSC") (value "C14663"))
      (property (name "Stock") (value "70324515"))
      (property (name "Price") (value "0.006USD"))
      (property (name "Process") (value "SMT"))
      (property (name "Minimum Qty") (value "20"))
      (property (name "Attrition Qty") (value "10"))
      (property (name "Class") (value "Basic Component"))
      (property (name "Category") (value "Capacitors,Multilayer Ceramic Capacitors MLCC - SMD/SMT"))
      (property (name "Manufacturer") (value "YAGEO"))
      (property (name "Part") (value "CC0603KRX7R9BB104"))
      (property (name "Voltage Rated") (value "50V"))
      (property (name "Tolerance") (value "±10%"))
      (property (name "Capacitance") (value "100nF"))
      (property (name "Temperature Coefficient") (value "X7R"))
      (property (name "Peak Wavelength") (value ""))
      (property (name "Sheetname") (value "Root"))
      (property (name "Sheetfile") (value "Pico_Development_Stack.kicad_sch"))
      (property (name "ki_fp_filters") (value "C_*"))
      (sheetpath (names "/") (tstamps "/"))
      (tstamps "1224a955-da0b-4c8c-a5c6-6e18616c0d9f"))
    (comp (ref "C41")
      (value "100nF")
      (footprint "PCM_JLCPCB:C_0603")
      (datasheet "https://www.lcsc.com/datasheet/lcsc_datasheet_2211101700_YAGEO-CC0603KRX7R9BB104_C14663.pdf")
      (description "50V 100nF X7R ±10% 0603 Multilayer Ceramic Capacitors MLCC - SMD/SMT ROHS")
      (fields
        (field (name "LCSC") "C14663")
        (field (name "Stock") "70324515")
        (field (name "Price") "0.006USD")
        (field (name "Process") "SMT")
        (field (name "Minimum Qty") "20")
        (field (name "Attrition Qty") "10")
        (field (name "Class") "Basic Component")
        (field (name "Category") "Capacitors,Multilayer Ceramic Capacitors MLCC - SMD/SMT")
        (field (name "Manufacturer") "YAGEO")
        (field (name "Part") "CC0603KRX7R9BB104")
        (field (name "Voltage Rated") "50V")
        (field (name "Tolerance") "±10%")
        (field (name "Capacitance") "100nF")
        (field (name "Temperature Coefficient") "X7R")
        (field (name "Peak Wavelength"))
        (field (name "Footprint") "PCM_JLCPCB:C_0603")
        (field (name "Datasheet") "https://www.lcsc.com/datasheet/lcsc_datasheet_2211101700_YAGEO-CC0603KRX7R9BB104_C14663.pdf")
        (field (name "Description") "50V 100nF X7R ±10% 0603 Multilayer Ceramic Capacitors MLCC - SMD/SMT ROHS"))
      (libsource (lib "PCM_JLCPCB-Capacitors") (part "0603,100nF") (description "50V 100nF X7R ±10% 0603 Multilayer Ceramic Capacitors MLCC - SMD/SMT ROHS"))
      (property (name "LCSC") (value "C14663"))
      (property (name "Stock") (value "70324515"))
      (property (name "Price") (value "0.006USD"))
      (property (name "Process") (value "SMT"))
      (property (name "Minimum Qty") (value "20"))
      (property (name "Attrition Qty") (value "10"))
      (property (name "Class") (value "Basic Component"))
      (property (name "Category") (value "Capacitors,Multilayer Ceramic Capacitors MLCC - SMD/SMT"))
      (property (name "Manufacturer") (value "YAGEO"))
      (property (name "Part") (value "CC0603KRX7R9BB104"))
      (property (name "Voltage Rated") (value "50V"))
      (property (name "Tolerance") (value "±10%"))
      (property (name "Capacitance") (value "100nF"))
      (property (name "Temperature Coefficient") (value "X7R"))
      (property (name "Peak Wavelength") (value ""))
      (property (name "Sheetname") (value "Root"))
      (property (name "Sheetfile") (value "Pico_Development_Stack.kicad_sch"))
      (property (name "ki_fp_filters") (value "C_*"))
      (sheetpath (names "/") (tstamps "/"))
      (tstamps "8881840b-f177-484f-a84d-7bad4b38f877"))
    (comp (ref "C42")
      (value "4.7uF")
      (footprint "PCM_JLCPCB:C_0603")
      (datasheet "https://www.lcsc.com/datasheet/lcsc_datasheet_2304140030_Samsung-Electro-Mechanics-CL10A475KO8NNNC_C19666.pdf")
      (description "16V 4.7uF X5R ±10% 0603 Multilayer Ceramic Capacitors MLCC - SMD/SMT ROHS")
      (fields
        (field (name "LCSC") "C19666")
        (field (name "Stock") "4246728")
        (field (name "Price") "0.013USD")
        (field (name "Process") "SMT")
        (field (name "Minimum Qty") "20")
        (field (name "Attrition Qty") "10")
        (field (name "Class") "Basic Component")
        (field (name "Category") "Capacitors,Multilayer Ceramic Capacitors MLCC - SMD/SMT")
        (field (name "Manufacturer") "Samsung Electro-Mechanics")
        (field (name "Part") "CL10A475KO8NNNC")
        (field (name "Voltage Rated") "16V")
        (field (name "Tolerance") "±10%")
        (field (name "Capacitance") "4.7uF")
        (field (name "Temperature Coefficient") "X5R")
        (field (name "Peak Wavelength"))
        (field (name "Footprint") "PCM_JLCPCB:C_0603")
        (field (name "Datasheet") "https://www.lcsc.com/datasheet/lcsc_datasheet_2304140030_Samsung-Electro-Mechanics-CL10A475KO8NNNC_C19666.pdf")
        (field (name "Description") "16V 4.7uF X5R ±10% 0603 Multilayer Ceramic Capacitors MLCC - SMD/SMT ROHS"))
      (libsource (lib "PCM_JLCPCB-Capacitors") (part "0603,4.7uF") (description "16V 4.7uF X5R ±10% 0603 Multilayer Ceramic Capacitors MLCC - SMD/SMT ROHS"))
      (property (name "LCSC") (value "C19666"))
      (property (name "Stock") (value "4246728"))
      (property (name "Price") (value "0.013USD"))
      (property (name "Process") (value "SMT"))
      (property (name "Minimum Qty") (value "20"))
      (property (name "Attrition Qty") (value "10"))
      (property (name "Class") (value "Basic Component"))
      (property (name "Category") (value "Capacitors,Multilayer Ceramic Capacitors MLCC - SMD/SMT"))
      (property (name "Manufacturer") (value "Samsung Electro-Mechanics"))
      (property (name "Part") (value "CL10A475KO8NNNC"))
      (property (name "Voltage Rated") (value "16V"))
      (property (name "Tolerance") (value "±10%"))
      (property (name "Capacitance") (value "4.7uF"))
      (property (name "Temperature Coefficient") (value "X5R"))
      (property (name "Peak Wavelength") (value ""))
      (property (name "Sheetname") (value "Root"))
      (property (name "Sheetfile") (value "Pico_Development_Stack.kicad_sch"))
      (property (name "ki_fp_filters") (value "C_*"))
      (sheetpath (names "/") (tstamps "/"))
      (tstamps "96b5afff-71ce-4195-a9d3-e01919553243"))
    (comp (ref "C43")
      (value "4.7uF")
      (footprint "PCM_JLCPCB:C_0603")
      (datasheet "https://www.lcsc.com/datasheet/lcsc_datasheet_2304140030_Samsung-Electro-Mechanics-CL10A475KO8NNNC_C19666.pdf")
      (description "16V 4.7uF X5R ±10% 0603 Multilayer Ceramic Capacitors MLCC - SMD/SMT ROHS")
      (fields
        (field (name "LCSC") "C19666")
        (field (name "Stock") "4246728")
        (field (name "Price") "0.013USD")
        (field (name "Process") "SMT")
        (field (name "Minimum Qty") "20")
        (field (name "Attrition Qty") "10")
        (field (name "Class") "Basic Component")
        (field (name "Category") "Capacitors,Multilayer Ceramic Capacitors MLCC - SMD/SMT")
        (field (name "Manufacturer") "Samsung Electro-Mechanics")
        (field (name "Part") "CL10A475KO8NNNC")
        (field (name "Voltage Rated") "16V")
        (field (name "Tolerance") "±10%")
        (field (name "Capacitance") "4.7uF")
        (field (name "Temperature Coefficient") "X5R")
        (field (name "Peak Wavelength"))
        (field (name "Footprint") "PCM_JLCPCB:C_0603")
        (field (name "Datasheet") "https://www.lcsc.com/datasheet/lcsc_datasheet_2304140030_Samsung-Electro-Mechanics-CL10A475KO8NNNC_C19666.pdf")
        (field (name "Description") "16V 4.7uF X5R ±10% 0603 Multilayer Ceramic Capacitors MLCC - SMD/SMT ROHS"))
      (libsource (lib "PCM_JLCPCB-Capacitors") (part "0603,4.7uF") (description "16V 4.7uF X5R ±10% 0603 Multilayer Ceramic Capacitors MLCC - SMD/SMT ROHS"))
      (property (name "LCSC") (value "C19666"))
      (property (name "Stock") (value "4246728"))
      (property (name "Price") (value "0.013USD"))
      (property (name "Process") (value "SMT"))
      (property (name "Minimum Qty") (value "20"))
      (property (name "Attrition Qty") (value "10"))
      (property (name "Class") (value "Basic Component"))
      (property (name "Category") (value "Capacitors,Multilayer Ceramic Capacitors MLCC - SMD/SMT"))
      (property (name "Manufacturer") (value "Samsung Electro-Mechanics"))
      (property (name "Part") (value "CL10A475KO8NNNC"))
      (property (name "Voltage Rated") (value "16V"))
      (property (name "Tolerance") (value "±10%"))
      (property (name "Capacitance") (value "4.7uF"))
      (property (name "Temperature Coefficient") (value "X5R"))
      (property (name "Peak Wavelength") (value ""))
      (property (name "Sheetname") (value "Root"))
      (property (name "Sheetfile") (value "Pico_Development_Stack.kicad_sch"))
      (property (name "ki_fp_filters") (value "C_*"))
      (sheetpath (names "/") (tstamps "/"))
      (tstamps "147271d9-db15-424f-a858-47c8d82a547e"))
    (comp (ref "C44")
      (value "4.7uF")
      (footprint "PCM_JLCPCB:C_0603")
      (datasheet "https://www.lcsc.com/datasheet/lcsc_datasheet_2304140030_Samsung-Electro-Mechanics-CL10A475KO8NNNC_C19666.pdf")
      (description "16V 4.7uF X5R ±10% 0603 Multilayer Ceramic Capacitors MLCC - SMD/SMT ROHS")
      (fields
        (field (name "LCSC") "C19666")
        (field (name "Stock") "4246728")
        (field (name "Price") "0.013USD")
        (field (name "Process") "SMT")
        (field (name "Minimum Qty") "20")
        (field (name "Attrition Qty") "10")
        (field (name "Class") "Basic Component")
        (field (name "Category") "Capacitors,Multilayer Ceramic Capacitors MLCC - SMD/SMT")
        (field (name "Manufacturer") "Samsung Electro-Mechanics")
        (field (name "Part") "CL10A475KO8NNNC")
        (field (name "Voltage Rated") "16V")
        (field (name "Tolerance") "±10%")
        (field (name "Capacitance") "4.7uF")
        (field (name "Temperature Coefficient") "X5R")
        (field (name "Peak Wavelength"))
        (field (name "Footprint") "PCM_JLCPCB:C_0603")
        (field (name "Datasheet") "https://www.lcsc.com/datasheet/lcsc_datasheet_2304140030_Samsung-Electro-Mechanics-CL10A475KO8NNNC_C19666.pdf")
        (field (name "Description") "16V 4.7uF X5R ±10% 0603 Multilayer Ceramic Capacitors MLCC - SMD/SMT ROHS"))
      (libsource (lib "PCM_JLCPCB-Capacitors") (part "0603,4.7uF") (description "16V 4.7uF X5R ±10% 0603 Multilayer Ceramic Capacitors MLCC - SMD/SMT ROHS"))
      (property (name "LCSC") (value "C19666"))
      (property (name "Stock") (value "4246728"))
      (property (name "Price") (value "0.013USD"))
      (property (name "Process") (value "SMT"))
      (property (name "Minimum Qty") (value "20"))
      (property (name "Attrition Qty") (value "10"))
      (property (name "Class") (value "Basic Component"))
      (property (name "Category") (value "Capacitors,Multilayer Ceramic Capacitors MLCC - SMD/SMT"))
      (property (name "Manufacturer") (value "Samsung Electro-Mechanics"))
      (property (name "Part") (value "CL10A475KO8NNNC"))
      (property (name "Voltage Rated") (value "16V"))
      (property (name "Tolerance") (value "±10%"))
      (property (name "Capacitance") (value "4.7uF"))
      (property (name "Temperature Coefficient") (value "X5R"))
      (property (name "Peak Wavelength") (value ""))
      (property (name "Sheetname") (value "Root"))
      (property (name "Sheetfile") (value "Pico_Development_Stack.kicad_sch"))
      (property (name "ki_fp_filters") (value "C_*"))
      (sheetpath (names "/") (tstamps "/"))
      (tstamps "16b729c1-7c3c-4056-a16e-496998ee01d5"))
    (comp (ref "C45")
      (value "4.7uF")
      (footprint "PCM_JLCPCB:C_0603")
      (datasheet "https://www.lcsc.com/datasheet/lcsc_datasheet_2304140030_Samsung-Electro-Mechanics-CL10A475KO8NNNC_C19666.pdf")
      (description "16V 4.7uF X5R ±10% 0603 Multilayer Ceramic Capacitors MLCC - SMD/SMT ROHS")
      (fields
        (field (name "LCSC") "C19666")
        (field (name "Stock") "4246728")
        (field (name "Price") "0.013USD")
        (field (name "Process") "SMT")
        (field (name "Minimum Qty") "20")
        (field (name "Attrition Qty") "10")
        (field (name "Class") "Basic Component")
        (field (name "Category") "Capacitors,Multilayer Ceramic Capacitors MLCC - SMD/SMT")
        (field (name "Manufacturer") "Samsung Electro-Mechanics")
        (field (name "Part") "CL10A475KO8NNNC")
        (field (name "Voltage Rated") "16V")
        (field (name "Tolerance") "±10%")
        (field (name "Capacitance") "4.7uF")
        (field (name "Temperature Coefficient") "X5R")
        (field (name "Peak Wavelength"))
        (field (name "Footprint") "PCM_JLCPCB:C_0603")
        (field (name "Datasheet") "https://www.lcsc.com/datasheet/lcsc_datasheet_2304140030_Samsung-Electro-Mechanics-CL10A475KO8NNNC_C19666.pdf")
        (field (name "Description") "16V 4.7uF X5R ±10% 0603 Multilayer Ceramic Capacitors MLCC - SMD/SMT ROHS"))
      (libsource (lib "PCM_JLCPCB-Capacitors") (part "0603,4.7uF") (description "16V 4.7uF X5R ±10% 0603 Multilayer Ceramic Capacitors MLCC - SMD/SMT ROHS"))
      (property (name "LCSC") (value "C19666"))
      (property (name "Stock") (value "4246728"))
      (property (name "Price") (value "0.013USD"))
      (property (name "Process") (value "SMT"))
      (property (name "Minimum Qty") (value "20"))
      (property (name "Attrition Qty") (value "10"))
      (property (name "Class") (value "Basic Component"))
      (property (name "Category") (value "Capacitors,Multilayer Ceramic Capacitors MLCC - SMD/SMT"))
      (property (name "Manufacturer") (value "Samsung Electro-Mechanics"))
      (property (name "Part") (value "CL10A475KO8NNNC"))
      (property (name "Voltage Rated") (value "16V"))
      (property (name "Tolerance") (value "±10%"))
      (property (name "Capacitance") (value "4.7uF"))
      (property (name "Temperature Coefficient") (value "X5R"))
      (property (name "Peak Wavelength") (value ""))
      (property (name "Sheetname") (value "Root"))
      (property (name "Sheetfile") (value "Pico_Development_Stack.kicad_sch"))
      (property (name "ki_fp_filters") (value "C_*"))
      (sheetpath (names "/") (tstamps "/"))
      (tstamps "3ad55d2a-3434-42a7-9e0e-dc7847096d6e"))
    (comp (ref "C46")
      (value "4.7uF")
      (footprint "PCM_JLCPCB:C_0603")
      (datasheet "https://www.lcsc.com/datasheet/lcsc_datasheet_2304140030_Samsung-Electro-Mechanics-CL10A475KO8NNNC_C19666.pdf")
      (description "16V 4.7uF X5R ±10% 0603 Multilayer Ceramic Capacitors MLCC - SMD/SMT ROHS")
      (fields
        (field (name "LCSC") "C19666")
        (field (name "Stock") "4246728")
        (field (name "Price") "0.013USD")
        (field (name "Process") "SMT")
        (field (name "Minimum Qty") "20")
        (field (name "Attrition Qty") "10")
        (field (name "Class") "Basic Component")
        (field (name "Category") "Capacitors,Multilayer Ceramic Capacitors MLCC - SMD/SMT")
        (field (name "Manufacturer") "Samsung Electro-Mechanics")
        (field (name "Part") "CL10A475KO8NNNC")
        (field (name "Voltage Rated") "16V")
        (field (name "Tolerance") "±10%")
        (field (name "Capacitance") "4.7uF")
        (field (name "Temperature Coefficient") "X5R")
        (field (name "Peak Wavelength"))
        (field (name "Footprint") "PCM_JLCPCB:C_0603")
        (field (name "Datasheet") "https://www.lcsc.com/datasheet/lcsc_datasheet_2304140030_Samsung-Electro-Mechanics-CL10A475KO8NNNC_C19666.pdf")
        (field (name "Description") "16V 4.7uF X5R ±10% 0603 Multilayer Ceramic Capacitors MLCC - SMD/SMT ROHS"))
      (libsource (lib "PCM_JLCPCB-Capacitors") (part "0603,4.7uF") (description "16V 4.7uF X5R ±10% 0603 Multilayer Ceramic Capacitors MLCC - SMD/SMT ROHS"))
      (property (name "LCSC") (value "C19666"))
      (property (name "Stock") (value "4246728"))
      (property (name "Price") (value "0.013USD"))
      (property (name "Process") (value "SMT"))
      (property (name "Minimum Qty") (value "20"))
      (property (name "Attrition Qty") (value "10"))
      (property (name "Class") (value "Basic Component"))
      (property (name "Category") (value "Capacitors,Multilayer Ceramic Capacitors MLCC - SMD/SMT"))
      (property (name "Manufacturer") (value "Samsung Electro-Mechanics"))
      (property (name "Part") (value "CL10A475KO8NNNC"))
      (property (name "Voltage Rated") (value "16V"))
      (property (name "Tolerance") (value "±10%"))
      (property (name "Capacitance") (value "4.7uF"))
      (property (name "Temperature Coefficient") (value "X5R"))
      (property (name "Peak Wavelength") (value ""))
      (property (name "Sheetname") (value "Root"))
      (property (name "Sheetfile") (value "Pico_Development_Stack.kicad_sch"))
      (property (name "ki_fp_filters") (value "C_*"))
      (sheetpath (names "/") (tstamps "/"))
      (tstamps "5d4a049a-fae1-4411-86f7-475b60c1a661"))
    (comp (ref "C47")
      (value "4.7uF")
      (footprint "PCM_JLCPCB:C_0603")
      (datasheet "https://www.lcsc.com/datasheet/lcsc_datasheet_2304140030_Samsung-Electro-Mechanics-CL10A475KO8NNNC_C19666.pdf")
      (description "16V 4.7uF X5R ±10% 0603 Multilayer Ceramic Capacitors MLCC - SMD/SMT ROHS")
      (fields
        (field (name "LCSC") "C19666")
        (field (name "Stock") "4246728")
        (field (name "Price") "0.013USD")
        (field (name "Process") "SMT")
        (field (name "Minimum Qty") "20")
        (field (name "Attrition Qty") "10")
        (field (name "Class") "Basic Component")
        (field (name "Category") "Capacitors,Multilayer Ceramic Capacitors MLCC - SMD/SMT")
        (field (name "Manufacturer") "Samsung Electro-Mechanics")
        (field (name "Part") "CL10A475KO8NNNC")
        (field (name "Voltage Rated") "16V")
        (field (name "Tolerance") "±10%")
        (field (name "Capacitance") "4.7uF")
        (field (name "Temperature Coefficient") "X5R")
        (field (name "Peak Wavelength"))
        (field (name "Footprint") "PCM_JLCPCB:C_0603")
        (field (name "Datasheet") "https://www.lcsc.com/datasheet/lcsc_datasheet_2304140030_Samsung-Electro-Mechanics-CL10A475KO8NNNC_C19666.pdf")
        (field (name "Description") "16V 4.7uF X5R ±10% 0603 Multilayer Ceramic Capacitors MLCC - SMD/SMT ROHS"))
      (libsource (lib "PCM_JLCPCB-Capacitors") (part "0603,4.7uF") (description "16V 4.7uF X5R ±10% 0603 Multilayer Ceramic Capacitors MLCC - SMD/SMT ROHS"))
      (property (name "LCSC") (value "C19666"))
      (property (name "Stock") (value "4246728"))
      (property (name "Price") (value "0.013USD"))
      (property (name "Process") (value "SMT"))
      (property (name "Minimum Qty") (value "20"))
      (property (name "Attrition Qty") (value "10"))
      (property (name "Class") (value "Basic Component"))
      (property (name "Category") (value "Capacitors,Multilayer Ceramic Capacitors MLCC - SMD/SMT"))
      (property (name "Manufacturer") (value "Samsung Electro-Mechanics"))
      (property (name "Part") (value "CL10A475KO8NNNC"))
      (property (name "Voltage Rated") (value "16V"))
      (property (name "Tolerance") (value "±10%"))
      (property (name "Capacitance") (value "4.7uF"))
      (property (name "Temperature Coefficient") (value "X5R"))
      (property (name "Peak Wavelength") (value ""))
      (property (name "Sheetname") (value "Root"))
      (property (name "Sheetfile") (value "Pico_Development_Stack.kicad_sch"))
      (property (name "ki_fp_filters") (value "C_*"))
      (sheetpath (names "/") (tstamps "/"))
      (tstamps "95ebddab-0b43-4e12-a00f-663cf9faca92"))
    (comp (ref "C48")
      (value "4.7uF")
      (footprint "PCM_JLCPCB:C_0603")
      (datasheet "https://www.lcsc.com/datasheet/lcsc_datasheet_2304140030_Samsung-Electro-Mechanics-CL10A475KO8NNNC_C19666.pdf")
      (description "16V 4.7uF X5R ±10% 0603 Multilayer Ceramic Capacitors MLCC - SMD/SMT ROHS")
      (fields
        (field (name "LCSC") "C19666")
        (field (name "Stock") "4246728")
        (field (name "Price") "0.013USD")
        (field (name "Process") "SMT")
        (field (name "Minimum Qty") "20")
        (field (name "Attrition Qty") "10")
        (field (name "Class") "Basic Component")
        (field (name "Category") "Capacitors,Multilayer Ceramic Capacitors MLCC - SMD/SMT")
        (field (name "Manufacturer") "Samsung Electro-Mechanics")
        (field (name "Part") "CL10A475KO8NNNC")
        (field (name "Voltage Rated") "16V")
        (field (name "Tolerance") "±10%")
        (field (name "Capacitance") "4.7uF")
        (field (name "Temperature Coefficient") "X5R")
        (field (name "Peak Wavelength"))
        (field (name "Footprint") "PCM_JLCPCB:C_0603")
        (field (name "Datasheet") "https://www.lcsc.com/datasheet/lcsc_datasheet_2304140030_Samsung-Electro-Mechanics-CL10A475KO8NNNC_C19666.pdf")
        (field (name "Description") "16V 4.7uF X5R ±10% 0603 Multilayer Ceramic Capacitors MLCC - SMD/SMT ROHS"))
      (libsource (lib "PCM_JLCPCB-Capacitors") (part "0603,4.7uF") (description "16V 4.7uF X5R ±10% 0603 Multilayer Ceramic Capacitors MLCC - SMD/SMT ROHS"))
      (property (name "LCSC") (value "C19666"))
      (property (name "Stock") (value "4246728"))
      (property (name "Price") (value "0.013USD"))
      (property (name "Process") (value "SMT"))
      (property (name "Minimum Qty") (value "20"))
      (property (name "Attrition Qty") (value "10"))
      (property (name "Class") (value "Basic Component"))
      (property (name "Category") (value "Capacitors,Multilayer Ceramic Capacitors MLCC - SMD/SMT"))
      (property (name "Manufacturer") (value "Samsung Electro-Mechanics"))
      (property (name "Part") (value "CL10A475KO8NNNC"))
      (property (name "Voltage Rated") (value "16V"))
      (property (name "Tolerance") (value "±10%"))
      (property (name "Capacitance") (value "4.7uF"))
      (property (name "Temperature Coefficient") (value "X5R"))
      (property (name "Peak Wavelength") (value ""))
      (property (name "Sheetname") (value "Root"))
      (property (name "Sheetfile") (value "Pico_Development_Stack.kicad_sch"))
      (property (name "ki_fp_filters") (value "C_*"))
      (sheetpath (names "/") (tstamps "/"))
      (tstamps "080712cc-73fa-40e3-a1b7-6d8b50e39555"))
    (comp (ref "C49")
      (value "4.7uF")
      (footprint "PCM_JLCPCB:C_0603")
      (datasheet "https://www.lcsc.com/datasheet/lcsc_datasheet_2304140030_Samsung-Electro-Mechanics-CL10A475KO8NNNC_C19666.pdf")
      (description "16V 4.7uF X5R ±10% 0603 Multilayer Ceramic Capacitors MLCC - SMD/SMT ROHS")
      (fields
        (field (name "LCSC") "C19666")
        (field (name "Stock") "4246728")
        (field (name "Price") "0.013USD")
        (field (name "Process") "SMT")
        (field (name "Minimum Qty") "20")
        (field (name "Attrition Qty") "10")
        (field (name "Class") "Basic Component")
        (field (name "Category") "Capacitors,Multilayer Ceramic Capacitors MLCC - SMD/SMT")
        (field (name "Manufacturer") "Samsung Electro-Mechanics")
        (field (name "Part") "CL10A475KO8NNNC")
        (field (name "Voltage Rated") "16V")
        (field (name "Tolerance") "±10%")
        (field (name "Capacitance") "4.7uF")
        (field (name "Temperature Coefficient") "X5R")
        (field (name "Peak Wavelength"))
        (field (name "Footprint") "PCM_JLCPCB:C_0603")
        (field (name "Datasheet") "https://www.lcsc.com/datasheet/lcsc_datasheet_2304140030_Samsung-Electro-Mechanics-CL10A475KO8NNNC_C19666.pdf")
        (field (name "Description") "16V 4.7uF X5R ±10% 0603 Multilayer Ceramic Capacitors MLCC - SMD/SMT ROHS"))
      (libsource (lib "PCM_JLCPCB-Capacitors") (part "0603,4.7uF") (description "16V 4.7uF X5R ±10% 0603 Multilayer Ceramic Capacitors MLCC - SMD/SMT ROHS"))
      (property (name "LCSC") (value "C19666"))
      (property (name "Stock") (value "4246728"))
      (property (name "Price") (value "0.013USD"))
      (property (name "Process") (value "SMT"))
      (property (name "Minimum Qty") (value "20"))
      (property (name "Attrition Qty") (value "10"))
      (property (name "Class") (value "Basic Component"))
      (property (name "Category") (value "Capacitors,Multilayer Ceramic Capacitors MLCC - SMD/SMT"))
      (property (name "Manufacturer") (value "Samsung Electro-Mechanics"))
      (property (name "Part") (value "CL10A475KO8NNNC"))
      (property (name "Voltage Rated") (value "16V"))
      (property (name "Tolerance") (value "±10%"))
      (property (name "Capacitance") (value "4.7uF"))
      (property (name "Temperature Coefficient") (value "X5R"))
      (property (name "Peak Wavelength") (value ""))
      (property (name "Sheetname") (value "Root"))
      (property (name "Sheetfile") (value "Pico_Development_Stack.kicad_sch"))
      (property (name "ki_fp_filters") (value "C_*"))
      (sheetpath (names "/") (tstamps "/"))
      (tstamps "a0f87000-1853-4cdf-aff3-57dda5206287"))
    (comp (ref "C50")
      (value "4.7uF")
      (footprint "PCM_JLCPCB:C_0603")
      (datasheet "https://www.lcsc.com/datasheet/lcsc_datasheet_2304140030_Samsung-Electro-Mechanics-CL10A475KO8NNNC_C19666.pdf")
      (description "16V 4.7uF X5R ±10% 0603 Multilayer Ceramic Capacitors MLCC - SMD/SMT ROHS")
      (fields
        (field (name "LCSC") "C19666")
        (field (name "Stock") "4246728")
        (field (name "Price") "0.013USD")
        (field (name "Process") "SMT")
        (field (name "Minimum Qty") "20")
        (field (name "Attrition Qty") "10")
        (field (name "Class") "Basic Component")
        (field (name "Category") "Capacitors,Multilayer Ceramic Capacitors MLCC - SMD/SMT")
        (field (name "Manufacturer") "Samsung Electro-Mechanics")
        (field (name "Part") "CL10A475KO8NNNC")
        (field (name "Voltage Rated") "16V")
        (field (name "Tolerance") "±10%")
        (field (name "Capacitance") "4.7uF")
        (field (name "Temperature Coefficient") "X5R")
        (field (name "Peak Wavelength"))
        (field (name "Footprint") "PCM_JLCPCB:C_0603")
        (field (name "Datasheet") "https://www.lcsc.com/datasheet/lcsc_datasheet_2304140030_Samsung-Electro-Mechanics-CL10A475KO8NNNC_C19666.pdf")
        (field (name "Description") "16V 4.7uF X5R ±10% 0603 Multilayer Ceramic Capacitors MLCC - SMD/SMT ROHS"))
      (libsource (lib "PCM_JLCPCB-Capacitors") (part "0603,4.7uF") (description "16V 4.7uF X5R ±10% 0603 Multilayer Ceramic Capacitors MLCC - SMD/SMT ROHS"))
      (property (name "LCSC") (value "C19666"))
      (property (name "Stock") (value "4246728"))
      (property (name "Price") (value "0.013USD"))
      (property (name "Process") (value "SMT"))
      (property (name "Minimum Qty") (value "20"))
      (property (name "Attrition Qty") (value "10"))
      (property (name "Class") (value "Basic Component"))
      (property (name "Category") (value "Capacitors,Multilayer Ceramic Capacitors MLCC - SMD/SMT"))
      (property (name "Manufacturer") (value "Samsung Electro-Mechanics"))
      (property (name "Part") (value "CL10A475KO8NNNC"))
      (property (name "Voltage Rated") (value "16V"))
      (property (name "Tolerance") (value "±10%"))
      (property (name "Capacitance") (value "4.7uF"))
      (property (name "Temperature Coefficient") (value "X5R"))
      (property (name "Peak Wavelength") (value ""))
      (property (name "Sheetname") (value "Root"))
      (property (name "Sheetfile") (value "Pico_Development_Stack.kicad_sch"))
      (property (name "ki_fp_filters") (value "C_*"))
      (sheetpath (names "/") (tstamps "/"))
      (tstamps "82aacd82-7b84-4ed9-b3f4-a3ce0ccb5372"))
    (comp (ref "C51")
      (value "100nF")
      (footprint "PCM_JLCPCB:C_0603")
      (datasheet "https://www.lcsc.com/datasheet/lcsc_datasheet_2211101700_YAGEO-CC0603KRX7R9BB104_C14663.pdf")
      (description "50V 100nF X7R ±10% 0603 Multilayer Ceramic Capacitors MLCC - SMD/SMT ROHS")
      (fields
        (field (name "LCSC") "C14663")
        (field (name "Stock") "70324515")
        (field (name "Price") "0.006USD")
        (field (name "Process") "SMT")
        (field (name "Minimum Qty") "20")
        (field (name "Attrition Qty") "10")
        (field (name "Class") "Basic Component")
        (field (name "Category") "Capacitors,Multilayer Ceramic Capacitors MLCC - SMD/SMT")
        (field (name "Manufacturer") "YAGEO")
        (field (name "Part") "CC0603KRX7R9BB104")
        (field (name "Voltage Rated") "50V")
        (field (name "Tolerance") "±10%")
        (field (name "Capacitance") "100nF")
        (field (name "Temperature Coefficient") "X7R")
        (field (name "Peak Wavelength"))
        (field (name "Footprint") "PCM_JLCPCB:C_0603")
        (field (name "Datasheet") "https://www.lcsc.com/datasheet/lcsc_datasheet_2211101700_YAGEO-CC0603KRX7R9BB104_C14663.pdf")
        (field (name "Description") "50V 100nF X7R ±10% 0603 Multilayer Ceramic Capacitors MLCC - SMD/SMT ROHS"))
      (libsource (lib "PCM_JLCPCB-Capacitors") (part "0603,100nF") (description "50V 100nF X7R ±10% 0603 Multilayer Ceramic Capacitors MLCC - SMD/SMT ROHS"))
      (property (name "LCSC") (value "C14663"))
      (property (name "Stock") (value "70324515"))
      (property (name "Price") (value "0.006USD"))
      (property (name "Process") (value "SMT"))
      (property (name "Minimum Qty") (value "20"))
      (property (name "Attrition Qty") (value "10"))
      (property (name "Class") (value "Basic Component"))
      (property (name "Category") (value "Capacitors,Multilayer Ceramic Capacitors MLCC - SMD/SMT"))
      (property (name "Manufacturer") (value "YAGEO"))
      (property (name "Part") (value "CC0603KRX7R9BB104"))
      (property (name "Voltage Rated") (value "50V"))
      (property (name "Tolerance") (value "±10%"))
      (property (name "Capacitance") (value "100nF"))
      (property (name "Temperature Coefficient") (value "X7R"))
      (property (name "Peak Wavelength") (value ""))
      (property (name "Sheetname") (value "Root"))
      (property (name "Sheetfile") (value "Pico_Development_Stack.kicad_sch"))
      (property (name "ki_fp_filters") (value "C_*"))
      (sheetpath (names "/") (tstamps "/"))
      (tstamps "45892542-954b-4660-8594-d2c9b5d252cb"))
    (comp (ref "C53")
      (value "100nF")
      (footprint "PCM_JLCPCB:C_0603")
      (datasheet "https://www.lcsc.com/datasheet/lcsc_datasheet_2211101700_YAGEO-CC0603KRX7R9BB104_C14663.pdf")
      (description "50V 100nF X7R ±10% 0603 Multilayer Ceramic Capacitors MLCC - SMD/SMT ROHS")
      (fields
        (field (name "LCSC") "C14663")
        (field (name "Stock") "70324515")
        (field (name "Price") "0.006USD")
        (field (name "Process") "SMT")
        (field (name "Minimum Qty") "20")
        (field (name "Attrition Qty") "10")
        (field (name "Class") "Basic Component")
        (field (name "Category") "Capacitors,Multilayer Ceramic Capacitors MLCC - SMD/SMT")
        (field (name "Manufacturer") "YAGEO")
        (field (name "Part") "CC0603KRX7R9BB104")
        (field (name "Voltage Rated") "50V")
        (field (name "Tolerance") "±10%")
        (field (name "Capacitance") "100nF")
        (field (name "Temperature Coefficient") "X7R")
        (field (name "Peak Wavelength"))
        (field (name "Footprint") "PCM_JLCPCB:C_0603")
        (field (name "Datasheet") "https://www.lcsc.com/datasheet/lcsc_datasheet_2211101700_YAGEO-CC0603KRX7R9BB104_C14663.pdf")
        (field (name "Description") "50V 100nF X7R ±10% 0603 Multilayer Ceramic Capacitors MLCC - SMD/SMT ROHS"))
      (libsource (lib "PCM_JLCPCB-Capacitors") (part "0603,100nF") (description "50V 100nF X7R ±10% 0603 Multilayer Ceramic Capacitors MLCC - SMD/SMT ROHS"))
      (property (name "LCSC") (value "C14663"))
      (property (name "Stock") (value "70324515"))
      (property (name "Price") (value "0.006USD"))
      (property (name "Process") (value "SMT"))
      (property (name "Minimum Qty") (value "20"))
      (property (name "Attrition Qty") (value "10"))
      (property (name "Class") (value "Basic Component"))
      (property (name "Category") (value "Capacitors,Multilayer Ceramic Capacitors MLCC - SMD/SMT"))
      (property (name "Manufacturer") (value "YAGEO"))
      (property (name "Part") (value "CC0603KRX7R9BB104"))
      (property (name "Voltage Rated") (value "50V"))
      (property (name "Tolerance") (value "±10%"))
      (property (name "Capacitance") (value "100nF"))
      (property (name "Temperature Coefficient") (value "X7R"))
      (property (name "Peak Wavelength") (value ""))
      (property (name "Sheetname") (value "Root"))
      (property (name "Sheetfile") (value "Pico_Development_Stack.kicad_sch"))
      (property (name "ki_fp_filters") (value "C_*"))
      (sheetpath (names "/") (tstamps "/"))
      (tstamps "f40a20b5-04e6-40b8-84e6-9f1aa595ebb6"))
    (comp (ref "C54")
      (value "22pF")
      (footprint "PCM_JLCPCB:C_0603")
      (datasheet "https://www.lcsc.com/datasheet/lcsc_datasheet_2304140030_Samsung-Electro-Mechanics-CL10C220JB8NNNC_C1653.pdf")
      (description "50V 22pF C0G ±5% 0603 Multilayer Ceramic Capacitors MLCC - SMD/SMT ROHS")
      (fields
        (field (name "LCSC") "C1653")
        (field (name "Stock") "1531147")
        (field (name "Price") "0.007USD")
        (field (name "Process") "SMT")
        (field (name "Minimum Qty") "20")
        (field (name "Attrition Qty") "10")
        (field (name "Class") "Basic Component")
        (field (name "Category") "Capacitors,Multilayer Ceramic Capacitors MLCC - SMD/SMT")
        (field (name "Manufacturer") "Samsung Electro-Mechanics")
        (field (name "Part") "CL10C220JB8NNNC")
        (field (name "Voltage Rated") "50V")
        (field (name "Tolerance") "±5%")
        (field (name "Capacitance") "22pF")
        (field (name "Temperature Coefficient") "C0G")
        (field (name "Footprint") "PCM_JLCPCB:C_0603")
        (field (name "Datasheet") "https://www.lcsc.com/datasheet/lcsc_datasheet_2304140030_Samsung-Electro-Mechanics-CL10C220JB8NNNC_C1653.pdf")
        (field (name "Description") "50V 22pF C0G ±5% 0603 Multilayer Ceramic Capacitors MLCC - SMD/SMT ROHS"))
      (libsource (lib "PCM_JLCPCB-Capacitors") (part "0603,22pF") (description "50V 22pF C0G ±5% 0603 Multilayer Ceramic Capacitors MLCC - SMD/SMT ROHS"))
      (property (name "LCSC") (value "C1653"))
      (property (name "Stock") (value "1531147"))
      (property (name "Price") (value "0.007USD"))
      (property (name "Process") (value "SMT"))
      (property (name "Minimum Qty") (value "20"))
      (property (name "Attrition Qty") (value "10"))
      (property (name "Class") (value "Basic Component"))
      (property (name "Category") (value "Capacitors,Multilayer Ceramic Capacitors MLCC - SMD/SMT"))
      (property (name "Manufacturer") (value "Samsung Electro-Mechanics"))
      (property (name "Part") (value "CL10C220JB8NNNC"))
      (property (name "Voltage Rated") (value "50V"))
      (property (name "Tolerance") (value "±5%"))
      (property (name "Capacitance") (value "22pF"))
      (property (name "Temperature Coefficient") (value "C0G"))
      (property (name "Sheetname") (value "Root"))
      (property (name "Sheetfile") (value "Pico_Development_Stack.kicad_sch"))
      (property (name "ki_fp_filters") (value "C_*"))
      (sheetpath (names "/") (tstamps "/"))
      (tstamps "2def1469-bda8-4223-b0f7-c8abf922d548"))
    (comp (ref "C55")
      (value "22uF")
      (footprint "PCM_JLCPCB:C_0805")
      (datasheet "https://www.lcsc.com/datasheet/lcsc_datasheet_2304140030_Samsung-Electro-Mechanics-CL21A226MAQNNNE_C45783.pdf")
      (description "25V 22uF X5R ±20% 0805 Multilayer Ceramic Capacitors MLCC - SMD/SMT ROHS")
      (fields
        (field (name "LCSC") "C45783")
        (field (name "Stock") "6479946")
        (field (name "Price") "0.027USD")
        (field (name "Process") "SMT")
        (field (name "Minimum Qty") "20")
        (field (name "Attrition Qty") "8")
        (field (name "Class") "Basic Component")
        (field (name "Category") "Capacitors,Multilayer Ceramic Capacitors MLCC - SMD/SMT")
        (field (name "Manufacturer") "Samsung Electro-Mechanics")
        (field (name "Part") "CL21A226MAQNNNE")
        (field (name "Voltage Rated") "25V")
        (field (name "Tolerance") "±20%")
        (field (name "Capacitance") "22uF")
        (field (name "Temperature Coefficient") "X5R")
        (field (name "Footprint") "PCM_JLCPCB:C_0805")
        (field (name "Datasheet") "https://www.lcsc.com/datasheet/lcsc_datasheet_2304140030_Samsung-Electro-Mechanics-CL21A226MAQNNNE_C45783.pdf")
        (field (name "Description") "25V 22uF X5R ±20% 0805 Multilayer Ceramic Capacitors MLCC - SMD/SMT ROHS"))
      (libsource (lib "PCM_JLCPCB-Capacitors") (part "0805,22uF") (description "25V 22uF X5R ±20% 0805 Multilayer Ceramic Capacitors MLCC - SMD/SMT ROHS"))
      (property (name "LCSC") (value "C45783"))
      (property (name "Stock") (value "6479946"))
      (property (name "Price") (value "0.027USD"))
      (property (name "Process") (value "SMT"))
      (property (name "Minimum Qty") (value "20"))
      (property (name "Attrition Qty") (value "8"))
      (property (name "Class") (value "Basic Component"))
      (property (name "Category") (value "Capacitors,Multilayer Ceramic Capacitors MLCC - SMD/SMT"))
      (property (name "Manufacturer") (value "Samsung Electro-Mechanics"))
      (property (name "Part") (value "CL21A226MAQNNNE"))
      (property (name "Voltage Rated") (value "25V"))
      (property (name "Tolerance") (value "±20%"))
      (property (name "Capacitance") (value "22uF"))
      (property (name "Temperature Coefficient") (value "X5R"))
      (property (name "Sheetname") (value "Root"))
      (property (name "Sheetfile") (value "Pico_Development_Stack.kicad_sch"))
      (property (name "ki_fp_filters") (value "C_*"))
      (sheetpath (names "/") (tstamps "/"))
      (tstamps "98d2fd50-b016-44f2-94d3-fa6d7b15861d"))
    (comp (ref "D1")
      (value "Yellow")
      (footprint "PCM_JLCPCB:D_0603")
      (datasheet "https://www.lcsc.com/datasheet/lcsc_datasheet_2008201033_Foshan-NationStar-Optoelectronics-NCD0603Y2_C89811.pdf")
      (description "25mA 100mcd~220mcd Colorless transparent lens 586nm~595nm -30°C~+85°C Yellow 130° 65mW 1.6V~2.6V 0603 LED Indication - Discrete ROHS")
      (fields
        (field (name "LCSC") "C89811")
        (field (name "Stock") "109176")
        (field (name "Price") "0.021USD")
        (field (name "Process") "SMT")
        (field (name "Minimum Qty") "20")
        (field (name "Attrition Qty") "6")
        (field (name "Class") "Preferred Component")
        (field (name "Category") "Optoelectronics,Light Emitting Diodes (LED)")
        (field (name "Manufacturer") "Foshan NationStar Optoelectronics")
        (field (name "Part") "NCD0603Y2")
        (field (name "Dominant Wavelength") "586nm~595nm")
        (field (name "Operating Temperature") "-30°C~+85°C")
        (field (name "Power Dissipation") "65mW")
        (field (name "Emitted Color") "Yellow")
        (field (name "Viewing Angle") "130°")
        (field (name "Forward Current") "25mA")
        (field (name "Forward Voltage (VF)") "1.6V~2.6V")
        (field (name "Lens Color") "Colorless Transparent Lens")
        (field (name "Luminous Intensity") "100mcd~220mcd")
        (field (name "Peak Wavelength"))
        (field (name "Footprint") "PCM_JLCPCB:D_0603")
        (field (name "Datasheet") "https://www.lcsc.com/datasheet/lcsc_datasheet_2008201033_Foshan-NationStar-Optoelectronics-NCD0603Y2_C89811.pdf")
        (field (name "Description") "25mA 100mcd~220mcd Colorless transparent lens 586nm~595nm -30°C~+85°C Yellow 130° 65mW 1.6V~2.6V 0603 LED Indication - Discrete ROHS"))
      (libsource (lib "PCM_JLCPCB-Diodes") (part "LED,0603,Yellow") (description "25mA 100mcd~220mcd Colorless transparent lens 586nm~595nm -30°C~+85°C Yellow 130° 65mW 1.6V~2.6V 0603 LED Indication - Discrete ROHS"))
      (property (name "LCSC") (value "C89811"))
      (property (name "Stock") (value "109176"))
      (property (name "Price") (value "0.021USD"))
      (property (name "Process") (value "SMT"))
      (property (name "Minimum Qty") (value "20"))
      (property (name "Attrition Qty") (value "6"))
      (property (name "Class") (value "Preferred Component"))
      (property (name "Category") (value "Optoelectronics,Light Emitting Diodes (LED)"))
      (property (name "Manufacturer") (value "Foshan NationStar Optoelectronics"))
      (property (name "Part") (value "NCD0603Y2"))
      (property (name "Dominant Wavelength") (value "586nm~595nm"))
      (property (name "Operating Temperature") (value "-30°C~+85°C"))
      (property (name "Power Dissipation") (value "65mW"))
      (property (name "Emitted Color") (value "Yellow"))
      (property (name "Viewing Angle") (value "130°"))
      (property (name "Forward Current") (value "25mA"))
      (property (name "Forward Voltage (VF)") (value "1.6V~2.6V"))
      (property (name "Lens Color") (value "Colorless Transparent Lens"))
      (property (name "Luminous Intensity") (value "100mcd~220mcd"))
      (property (name "Peak Wavelength") (value ""))
      (property (name "Sheetname") (value "Root"))
      (property (name "Sheetfile") (value "Pico_Development_Stack.kicad_sch"))
      (property (name "ki_fp_filters") (value "D_*"))
      (sheetpath (names "/") (tstamps "/"))
      (tstamps "62735aab-d9ce-48e6-ab62-4147f854bcb2"))
    (comp (ref "D2")
      (value "White")
      (footprint "PCM_JLCPCB:D_0603")
      (datasheet "https://www.lcsc.com/datasheet/lcsc_datasheet_2305091500_Hubei-KENTO-Elec-KT-0603W_C2290.pdf")
      (description "White 0603 LED Indication - Discrete ROHS")
      (fields
        (field (name "LCSC") "C2290")
        (field (name "Stock") "1189238")
        (field (name "Price") "0.013USD")
        (field (name "Process") "SMT")
        (field (name "Minimum Qty") "20")
        (field (name "Attrition Qty") "10")
        (field (name "Class") "Basic Component")
        (field (name "Category") "Optocouplers & LEDs & Infrared,Light Emitting Diodes (LED)")
        (field (name "Manufacturer") "Hubei KENTO Elec")
        (field (name "Part") "KT-0603W")
        (field (name "Peak Wavelength"))
        (field (name "Footprint") "PCM_JLCPCB:D_0603")
        (field (name "Datasheet") "https://www.lcsc.com/datasheet/lcsc_datasheet_2305091500_Hubei-KENTO-Elec-KT-0603W_C2290.pdf")
        (field (name "Description") "White 0603 LED Indication - Discrete ROHS"))
      (libsource (lib "PCM_JLCPCB-Diodes") (part "LED,0603,White") (description "White 0603 LED Indication - Discrete ROHS"))
      (property (name "LCSC") (value "C2290"))
      (property (name "Stock") (value "1189238"))
      (property (name "Price") (value "0.013USD"))
      (property (name "Process") (value "SMT"))
      (property (name "Minimum Qty") (value "20"))
      (property (name "Attrition Qty") (value "10"))
      (property (name "Class") (value "Basic Component"))
      (property (name "Category") (value "Optocouplers & LEDs & Infrared,Light Emitting Diodes (LED)"))
      (property (name "Manufacturer") (value "Hubei KENTO Elec"))
      (property (name "Part") (value "KT-0603W"))
      (property (name "Peak Wavelength") (value ""))
      (property (name "Sheetname") (value "Root"))
      (property (name "Sheetfile") (value "Pico_Development_Stack.kicad_sch"))
      (property (name "ki_fp_filters") (value "D_*"))
      (sheetpath (names "/") (tstamps "/"))
      (tstamps "ff92ca50-6125-4905-8825-2a82932b9def"))
    (comp (ref "D3")
      (value "Red")
      (footprint "PCM_JLCPCB:D_0603")
      (datasheet "https://www.lcsc.com/datasheet/lcsc_datasheet_1810231112_Hubei-KENTO-Elec-KT-0603R_C2286.pdf")
      (description "-40°C~+85°C Red 0603 LED Indication - Discrete ROHS")
      (fields
        (field (name "LCSC") "C2286")
        (field (name "Stock") "5373336")
        (field (name "Price") "0.009USD")
        (field (name "Process") "SMT")
        (field (name "Minimum Qty") "20")
        (field (name "Attrition Qty") "10")
        (field (name "Class") "Basic Component")
        (field (name "Category") "Optocouplers & LEDs & Infrared,Light Emitting Diodes (LED)")
        (field (name "Manufacturer") "Hubei KENTO Elec")
        (field (name "Part") "KT-0603R")
        (field (name "Peak Wavelength"))
        (field (name "Footprint") "PCM_JLCPCB:D_0603")
        (field (name "Datasheet") "https://www.lcsc.com/datasheet/lcsc_datasheet_1810231112_Hubei-KENTO-Elec-KT-0603R_C2286.pdf")
        (field (name "Description") "-40°C~+85°C Red 0603 LED Indication - Discrete ROHS"))
      (libsource (lib "") (part "LED,0603,Red_1") (description "-40°C~+85°C Red 0603 LED Indication - Discrete ROHS"))
      (property (name "LCSC") (value "C2286"))
      (property (name "Stock") (value "5373336"))
      (property (name "Price") (value "0.009USD"))
      (property (name "Process") (value "SMT"))
      (property (name "Minimum Qty") (value "20"))
      (property (name "Attrition Qty") (value "10"))
      (property (name "Class") (value "Basic Component"))
      (property (name "Category") (value "Optocouplers & LEDs & Infrared,Light Emitting Diodes (LED)"))
      (property (name "Manufacturer") (value "Hubei KENTO Elec"))
      (property (name "Part") (value "KT-0603R"))
      (property (name "Peak Wavelength") (value ""))
      (property (name "Sheetname") (value "Root"))
      (property (name "Sheetfile") (value "Pico_Development_Stack.kicad_sch"))
      (property (name "ki_fp_filters") (value "D_*"))
      (sheetpath (names "/") (tstamps "/"))
      (tstamps "6e773e9d-b389-4b18-94f9-b2ccc0c4eeda"))
    (comp (ref "D4")
      (value "Red")
      (footprint "PCM_JLCPCB:D_0603")
      (datasheet "https://www.lcsc.com/datasheet/lcsc_datasheet_1810231112_Hubei-KENTO-Elec-KT-0603R_C2286.pdf")
      (description "-40°C~+85°C Red 0603 LED Indication - Discrete ROHS")
      (fields
        (field (name "LCSC") "C2286")
        (field (name "Stock") "5373336")
        (field (name "Price") "0.009USD")
        (field (name "Process") "SMT")
        (field (name "Minimum Qty") "20")
        (field (name "Attrition Qty") "10")
        (field (name "Class") "Basic Component")
        (field (name "Category") "Optocouplers & LEDs & Infrared,Light Emitting Diodes (LED)")
        (field (name "Manufacturer") "Hubei KENTO Elec")
        (field (name "Part") "KT-0603R")
        (field (name "Peak Wavelength"))
        (field (name "Footprint") "PCM_JLCPCB:D_0603")
        (field (name "Datasheet") "https://www.lcsc.com/datasheet/lcsc_datasheet_1810231112_Hubei-KENTO-Elec-KT-0603R_C2286.pdf")
        (field (name "Description") "-40°C~+85°C Red 0603 LED Indication - Discrete ROHS"))
      (libsource (lib "PCM_JLCPCB-Diodes") (part "LED,0603,Red") (description "-40°C~+85°C Red 0603 LED Indication - Discrete ROHS"))
      (property (name "LCSC") (value "C2286"))
      (property (name "Stock") (value "5373336"))
      (property (name "Price") (value "0.009USD"))
      (property (name "Process") (value "SMT"))
      (property (name "Minimum Qty") (value "20"))
      (property (name "Attrition Qty") (value "10"))
      (property (name "Class") (value "Basic Component"))
      (property (name "Category") (value "Optocouplers & LEDs & Infrared,Light Emitting Diodes (LED)"))
      (property (name "Manufacturer") (value "Hubei KENTO Elec"))
      (property (name "Part") (value "KT-0603R"))
      (property (name "Peak Wavelength") (value ""))
      (property (name "Sheetname") (value "Root"))
      (property (name "Sheetfile") (value "Pico_Development_Stack.kicad_sch"))
      (property (name "ki_fp_filters") (value "D_*"))
      (sheetpath (names "/") (tstamps "/"))
      (tstamps "ae4c3171-1197-4654-aec0-e06fa974b799"))
    (comp (ref "D5")
      (value "Green")
      (footprint "PCM_JLCPCB:D_0805")
      (datasheet "https://www.lcsc.com/datasheet/lcsc_datasheet_1806151820_Hubei-KENTO-Elec-KT-0805G_C2297.pdf")
      (description "Emerald 0805 LED Indication - Discrete ROHS")
      (fields
        (field (name "LCSC") "C2297")
        (field (name "Stock") "2062782")
        (field (name "Price") "0.014USD")
        (field (name "Process") "SMT")
        (field (name "Minimum Qty") "20")
        (field (name "Attrition Qty") "10")
        (field (name "Class") "Basic Component")
        (field (name "Category") "Optoelectronics,Light Emitting Diodes (LED)")
        (field (name "Manufacturer") "Hubei KENTO Elec")
        (field (name "Part") "KT-0805G")
        (field (name "Emitted Color") "Emerald")
        (field (name "Peak Wavelength"))
        (field (name "Footprint") "PCM_JLCPCB:D_0805")
        (field (name "Datasheet") "https://www.lcsc.com/datasheet/lcsc_datasheet_1806151820_Hubei-KENTO-Elec-KT-0805G_C2297.pdf")
        (field (name "Description") "Emerald 0805 LED Indication - Discrete ROHS"))
      (libsource (lib "PCM_JLCPCB-Diodes") (part "LED,0805,Green") (description "Emerald 0805 LED Indication - Discrete ROHS"))
      (property (name "LCSC") (value "C2297"))
      (property (name "Stock") (value "2062782"))
      (property (name "Price") (value "0.014USD"))
      (property (name "Process") (value "SMT"))
      (property (name "Minimum Qty") (value "20"))
      (property (name "Attrition Qty") (value "10"))
      (property (name "Class") (value "Basic Component"))
      (property (name "Category") (value "Optoelectronics,Light Emitting Diodes (LED)"))
      (property (name "Manufacturer") (value "Hubei KENTO Elec"))
      (property (name "Part") (value "KT-0805G"))
      (property (name "Emitted Color") (value "Emerald"))
      (property (name "Peak Wavelength") (value ""))
      (property (name "Sheetname") (value "Root"))
      (property (name "Sheetfile") (value "Pico_Development_Stack.kicad_sch"))
      (property (name "ki_fp_filters") (value "D_*"))
      (sheetpath (names "/") (tstamps "/"))
      (tstamps "464cc7e6-92a1-4b4a-a962-cd1b3005c9b5"))
    (comp (ref "D6")
      (value "DSL34")
      (footprint "PCM_JLCPCB:D_SOD-123FL")
      (datasheet "https://wmsc.lcsc.com/wmsc/upload/file/pdf/v2/lcsc/2406171613_hongjiacheng-DSL34_C22466347.pdf")
      (description "40V Independent Type 450mV@3A 4A SOD-123FL Schottky Diodes ROHS")
      (fields
        (field (name "LCSC") "C22466347")
        (field (name "Stock") "2179")
        (field (name "Price") "0.075USD")
        (field (name "Process") "SMT")
        (field (name "Minimum Qty") "5")
        (field (name "Attrition Qty") "4")
        (field (name "Class") "Preferred Component")
        (field (name "Category") "Diodes,Schottky Diodes")
        (field (name "Manufacturer") "hongjiacheng")
        (field (name "Part") "DSL34")
        (field (name "Footprint") "PCM_JLCPCB:D_SOD-123FL")
        (field (name "Datasheet") "https://wmsc.lcsc.com/wmsc/upload/file/pdf/v2/lcsc/2406171613_hongjiacheng-DSL34_C22466347.pdf")
        (field (name "Description") "40V Independent Type 450mV@3A 4A SOD-123FL Schottky Diodes ROHS"))
      (libsource (lib "PCM_JLCPCB-Diodes") (part "Schottky,DSL34") (description "40V Independent Type 450mV@3A 4A SOD-123FL Schottky Diodes ROHS"))
      (property (name "LCSC") (value "C22466347"))
      (property (name "Stock") (value "2179"))
      (property (name "Price") (value "0.075USD"))
      (property (name "Process") (value "SMT"))
      (property (name "Minimum Qty") (value "5"))
      (property (name "Attrition Qty") (value "4"))
      (property (name "Class") (value "Preferred Component"))
      (property (name "Category") (value "Diodes,Schottky Diodes"))
      (property (name "Manufacturer") (value "hongjiacheng"))
      (property (name "Part") (value "DSL34"))
      (property (name "Sheetname") (value "Root"))
      (property (name "Sheetfile") (value "Pico_Development_Stack.kicad_sch"))
      (property (name "ki_fp_filters") (value "D_*"))
      (sheetpath (names "/") (tstamps "/"))
      (tstamps "4f23d096-c17b-4171-95a1-483f6a2bd861"))
    (comp (ref "D7")
      (value "BAT54")
      (footprint "PCM_JLCPCB:D_SOT-23")
      (datasheet "https://wmsc.lcsc.com/wmsc/upload/file/pdf/v2/lcsc/2406171624_hongjiacheng-BAT54_C22466368.pdf")
      (description "30V Independent Type 200mA 1V@100mA SOT-23 Schottky Diodes ROHS")
      (fields
        (field (name "LCSC") "C22466368")
        (field (name "Stock") "11561")
        (field (name "Price") "0.016USD")
        (field (name "Process") "SMT")
        (field (name "Minimum Qty") "10")
        (field (name "Attrition Qty") "4")
        (field (name "Class") "Preferred Component")
        (field (name "Category") "Diodes,Schottky Diodes")
        (field (name "Manufacturer") "hongjiacheng")
        (field (name "Part") "BAT54")
        (field (name "Peak Wavelength"))
        (field (name "Footprint") "PCM_JLCPCB:D_SOT-23")
        (field (name "Datasheet") "https://wmsc.lcsc.com/wmsc/upload/file/pdf/v2/lcsc/2406171624_hongjiacheng-BAT54_C22466368.pdf")
        (field (name "Description") "30V Independent Type 200mA 1V@100mA SOT-23 Schottky Diodes ROHS"))
      (libsource (lib "") (part "Schottky,BAT54_1") (description "30V Independent Type 200mA 1V@100mA SOT-23 Schottky Diodes ROHS"))
      (property (name "LCSC") (value "C22466368"))
      (property (name "Stock") (value "11561"))
      (property (name "Price") (value "0.016USD"))
      (property (name "Process") (value "SMT"))
      (property (name "Minimum Qty") (value "10"))
      (property (name "Attrition Qty") (value "4"))
      (property (name "Class") (value "Preferred Component"))
      (property (name "Category") (value "Diodes,Schottky Diodes"))
      (property (name "Manufacturer") (value "hongjiacheng"))
      (property (name "Part") (value "BAT54"))
      (property (name "Peak Wavelength") (value ""))
      (property (name "Sheetname") (value "Root"))
      (property (name "Sheetfile") (value "Pico_Development_Stack.kicad_sch"))
      (property (name "ki_fp_filters") (value "D_*"))
      (sheetpath (names "/") (tstamps "/"))
      (tstamps "d3fb643c-5e9f-4551-b4f2-c9d6ea8e1781"))
    (comp (ref "F1")
      (value "1.5A Hold")
      (footprint "Fuse:Fuse_1206_3216Metric")
      (datasheet "https://jlcpcb.com/api/file/downloadByFileSystemAccessId/8588912268200824832")
      (description "Resettable fuse, polymeric positive temperature coefficient")
      (fields
        (field (name "LCSC") "C495353")
        (field (name "Footprint") "Fuse:Fuse_1206_3216Metric")
        (field (name "Datasheet") "https://jlcpcb.com/api/file/downloadByFileSystemAccessId/8588912268200824832")
        (field (name "Description") "Resettable fuse, polymeric positive temperature coefficient"))
      (libsource (lib "Device") (part "Polyfuse") (description "Resettable fuse, polymeric positive temperature coefficient"))
      (property (name "LCSC") (value "C495353"))
      (property (name "Sheetname") (value "Root"))
      (property (name "Sheetfile") (value "Pico_Development_Stack.kicad_sch"))
      (property (name "ki_keywords") (value "resettable fuse PTC PPTC polyfuse polyswitch"))
      (property (name "ki_fp_filters") (value "*polyfuse* *PTC*"))
      (sheetpath (names "/") (tstamps "/"))
      (tstamps "28ae9bc4-b235-46db-a72f-761ccf691ff6"))
    (comp (ref "J1")
      (value "~")
      (footprint "Connector_PinHeader_2.54mm:PinHeader_1x20_P2.54mm_Vertical")
      (fields
        (field (name "LCSC") "C5156618")
        (field (name "Peak Wavelength"))
        (field (name "Footprint") "Connector_PinHeader_2.54mm:PinHeader_1x20_P2.54mm_Vertical")
        (field (name "Datasheet"))
        (field (name "Description")))
      (libsource (lib "pico_connector") (part "Conn_02x20_Split") (description ""))
      (property (name "LCSC") (value "C5156618"))
      (property (name "Peak Wavelength") (value ""))
      (property (name "Sheetname") (value "Root"))
      (property (name "Sheetfile") (value "Pico_Development_Stack.kicad_sch"))
      (sheetpath (names "/") (tstamps "/"))
      (tstamps "dca91faf-70bd-4cf9-b9a8-d3aa629bac33" "2bd1ea44-22ed-4d28-a79a-78d9ba1ff8de"))
    (comp (ref "J2")
      (value "~")
      (footprint "Connector_PinHeader_2.54mm:PinHeader_1x20_P2.54mm_Vertical")
      (fields
        (field (name "LCSC") "C5156618")
        (field (name "Peak Wavelength"))
        (field (name "Footprint") "Connector_PinHeader_2.54mm:PinHeader_1x20_P2.54mm_Vertical")
        (field (name "Datasheet"))
        (field (name "Description")))
      (libsource (lib "") (part "Conn_02x20_Split_1") (description ""))
      (property (name "LCSC") (value "C5156618"))
      (property (name "Peak Wavelength") (value ""))
      (property (name "Sheetname") (value "Root"))
      (property (name "Sheetfile") (value "Pico_Development_Stack.kicad_sch"))
      (sheetpath (names "/") (tstamps "/"))
      (tstamps "acac66ce-e59e-41d9-9e9a-52cee66e3979" "73eaa5f6-ff18-4a8e-9aa7-afc34390f896"))
    (comp (ref "J3")
      (value "Conn_01x03_Socket")
      (footprint "Connector_PinHeader_2.54mm:PinHeader_1x03_P2.54mm_Vertical")
      (datasheet "~")
      (description "Generic connector, single row, 01x03, script generated")
      (fields
        (field (name "LCSC") "C146243")
        (field (name "Peak Wavelength"))
        (field (name "Footprint") "Connector_PinHeader_2.54mm:PinHeader_1x03_P2.54mm_Vertical")
        (field (name "Datasheet") "~")
        (field (name "Description") "Generic connector, single row, 01x03, script generated"))
      (libsource (lib "Connector") (part "Conn_01x03_Socket") (description "Generic connector, single row, 01x03, script generated"))
      (property (name "LCSC") (value "C146243"))
      (property (name "Peak Wavelength") (value ""))
      (property (name "Sheetname") (value "Root"))
      (property (name "Sheetfile") (value "Pico_Development_Stack.kicad_sch"))
      (property (name "dnp"))
      (property (name "ki_keywords") (value "connector"))
      (property (name "ki_fp_filters") (value "Connector*:*_1x??_*"))
      (sheetpath (names "/") (tstamps "/"))
      (tstamps "0c39ba6d-f657-436c-8a25-a9315b20b34a"))
    (comp (ref "J4")
      (value "Conn_01x04_Pin")
      (footprint "Connector_PinHeader_2.54mm:PinHeader_1x04_P2.54mm_Vertical")
      (datasheet "~")
      (description "Generic connector, single row, 01x04, script generated")
      (fields
        (field (name "Peak Wavelength"))
        (field (name "Footprint") "Connector_PinHeader_2.54mm:PinHeader_1x04_P2.54mm_Vertical")
        (field (name "Datasheet") "~")
        (field (name "Description") "Generic connector, single row, 01x04, script generated"))
      (libsource (lib "Connector") (part "Conn_01x04_Pin") (description "Generic connector, single row, 01x04, script generated"))
      (property (name "Peak Wavelength") (value ""))
      (property (name "Sheetname") (value "Root"))
      (property (name "Sheetfile") (value "Pico_Development_Stack.kicad_sch"))
      (property (name "dnp"))
      (property (name "ki_keywords") (value "connector"))
      (property (name "ki_fp_filters") (value "Connector*:*_1x??_*"))
      (sheetpath (names "/") (tstamps "/"))
      (tstamps "27a7612e-1bfc-49e0-9d28-f88ef1f9bc46"))
    (comp (ref "J5")
      (value "Conn_01x03_Socket")
      (footprint "Connector_PinHeader_2.54mm:PinHeader_1x03_P2.54mm_Vertical")
      (datasheet "~")
      (description "Generic connector, single row, 01x03, script generated")
      (fields
        (field (name "LCSC") "C146243")
        (field (name "Peak Wavelength"))
        (field (name "Footprint") "Connector_PinHeader_2.54mm:PinHeader_1x03_P2.54mm_Vertical")
        (field (name "Datasheet") "~")
        (field (name "Description") "Generic connector, single row, 01x03, script generated"))
      (libsource (lib "Connector") (part "Conn_01x03_Socket") (description "Generic connector, single row, 01x03, script generated"))
      (property (name "LCSC") (value "C146243"))
      (property (name "Peak Wavelength") (value ""))
      (property (name "Sheetname") (value "Root"))
      (property (name "Sheetfile") (value "Pico_Development_Stack.kicad_sch"))
      (property (name "dnp"))
      (property (name "ki_keywords") (value "connector"))
      (property (name "ki_fp_filters") (value "Connector*:*_1x??_*"))
      (sheetpath (names "/") (tstamps "/"))
      (tstamps "16b57b28-94a9-4d8a-b17a-526beb976af7"))
    (comp (ref "J6")
      (value "Conn_01x03_Socket")
      (footprint "Connector_PinHeader_2.54mm:PinHeader_1x03_P2.54mm_Vertical")
      (datasheet "~")
      (description "Generic connector, single row, 01x03, script generated")
      (fields
        (field (name "LCSC") "C146243")
        (field (name "Peak Wavelength"))
        (field (name "Footprint") "Connector_PinHeader_2.54mm:PinHeader_1x03_P2.54mm_Vertical")
        (field (name "Datasheet") "~")
        (field (name "Description") "Generic connector, single row, 01x03, script generated"))
      (libsource (lib "Connector") (part "Conn_01x03_Socket") (description "Generic connector, single row, 01x03, script generated"))
      (property (name "LCSC") (value "C146243"))
      (property (name "Peak Wavelength") (value ""))
      (property (name "Sheetname") (value "Root"))
      (property (name "Sheetfile") (value "Pico_Development_Stack.kicad_sch"))
      (property (name "dnp"))
      (property (name "ki_keywords") (value "connector"))
      (property (name "ki_fp_filters") (value "Connector*:*_1x??_*"))
      (sheetpath (names "/") (tstamps "/"))
      (tstamps "270e0014-441d-4b42-8c60-c7f7f2f2c71c"))
    (comp (ref "J7")
      (value "Connector, USB-TYPE-C-16P")
      (footprint "PCM_JLCPCB:TYPE-C-SMD_HX-TYPE-C-16PIN")
      (datasheet "https://atta.szlcsc.com/upload/public/pdf/source/20220920/0EF8F885FCCEA71F60E9E85152155021.pdf")
      (description "3A 1 Horizontal attachment 16P Female -25℃~+85℃ Type-C SMD USB Connectors ROHS")
      (fields
        (field (name "LCSC") "C2927039")
        (field (name "Peak Wavelength"))
        (field (name "Footprint") "PCM_JLCPCB:TYPE-C-SMD_HX-TYPE-C-16PIN")
        (field (name "Datasheet") "https://atta.szlcsc.com/upload/public/pdf/source/20220920/0EF8F885FCCEA71F60E9E85152155021.pdf")
        (field (name "Description") "3A 1 Horizontal attachment 16P Female -25℃~+85℃ Type-C SMD USB Connectors ROHS"))
      (libsource (lib "PCM_JLCPCB-Extended") (part "Connector, USB-TYPE-C-16P") (description "3A 1 Horizontal attachment 16P Female -25℃~+85℃ Type-C SMD USB Connectors ROHS"))
      (property (name "LCSC") (value "C2927039"))
      (property (name "Peak Wavelength") (value ""))
      (property (name "Sheetname") (value "Root"))
      (property (name "Sheetfile") (value "Pico_Development_Stack.kicad_sch"))
      (property (name "ki_keywords") (value "C2927039"))
      (sheetpath (names "/") (tstamps "/"))
      (tstamps "281c5886-41fa-4984-95f0-c419b18c8f3a"))
    (comp (ref "J8")
      (value "~")
      (footprint "Connector_PinHeader_2.54mm:PinHeader_1x20_P2.54mm_Vertical")
      (fields
        (field (name "LCSC") "C5156618")
        (field (name "Peak Wavelength"))
        (field (name "Footprint") "Connector_PinHeader_2.54mm:PinHeader_1x20_P2.54mm_Vertical")
        (field (name "Datasheet"))
        (field (name "Description")))
      (libsource (lib "pico_connector") (part "Conn_02x20_Split") (description ""))
      (property (name "LCSC") (value "C5156618"))
      (property (name "Peak Wavelength") (value ""))
      (property (name "Sheetname") (value "Root"))
      (property (name "Sheetfile") (value "Pico_Development_Stack.kicad_sch"))
      (sheetpath (names "/") (tstamps "/"))
      (tstamps "cd9b2c14-3386-4b3e-b18d-ec6b7f2b1b2d" "2ccc84cd-9a5c-4726-80b7-77600156cfa5"))
    (comp (ref "J9")
      (value "Conn_01x03_Socket")
      (footprint "Connector_PinHeader_2.54mm:PinHeader_1x03_P2.54mm_Vertical")
      (datasheet "~")
      (description "Generic connector, single row, 01x03, script generated")
      (fields
        (field (name "LCSC") "C146243")
        (field (name "Peak Wavelength"))
        (field (name "Footprint") "Connector_PinHeader_2.54mm:PinHeader_1x03_P2.54mm_Vertical")
        (field (name "Datasheet") "~")
        (field (name "Description") "Generic connector, single row, 01x03, script generated"))
      (libsource (lib "Connector") (part "Conn_01x03_Socket") (description "Generic connector, single row, 01x03, script generated"))
      (property (name "LCSC") (value "C146243"))
      (property (name "Peak Wavelength") (value ""))
      (property (name "Sheetname") (value "Root"))
      (property (name "Sheetfile") (value "Pico_Development_Stack.kicad_sch"))
      (property (name "dnp"))
      (property (name "ki_keywords") (value "connector"))
      (property (name "ki_fp_filters") (value "Connector*:*_1x??_*"))
      (sheetpath (names "/") (tstamps "/"))
      (tstamps "838e640d-11af-49bd-b11b-da73854da911"))
    (comp (ref "J10")
      (value "USB_A_Stacked")
      (footprint "Connector_USB:USB_A_CUI_UJ2-ADH-TH_Horizontal_Stacked")
      (datasheet "https://jlcpcb.com/api/file/downloadByFileSystemAccessId/8588933952048807936")
      (description "USB Type A connector, stacked")
      (fields
        (field (name "LCSC") "C698206")
        (field (name "Peak Wavelength"))
        (field (name "Footprint") "Connector_USB:USB_A_CUI_UJ2-ADH-TH_Horizontal_Stacked")
        (field (name "Datasheet") "https://jlcpcb.com/api/file/downloadByFileSystemAccessId/8588933952048807936")
        (field (name "Description") "USB Type A connector, stacked"))
      (libsource (lib "Connector") (part "USB_A_Stacked") (description "USB Type A connector, stacked"))
      (property (name "LCSC") (value "C698206"))
      (property (name "Peak Wavelength") (value ""))
      (property (name "Sheetname") (value "Root"))
      (property (name "Sheetfile") (value "Pico_Development_Stack.kicad_sch"))
      (property (name "ki_keywords") (value "connector USB"))
      (property (name "ki_fp_filters") (value "USB*"))
      (sheetpath (names "/") (tstamps "/"))
      (tstamps "073b8051-b3c6-4429-a915-11d010d51a31"))
    (comp (ref "L1")
      (value "3.3u")
      (footprint "RP2350_60QFN_minimal:L_pol_2016")
      (datasheet "https://lcsc.com/datasheet/lcsc_datasheet_2412101620_ABRACON-AOTA-B201610S3R3-101-T_C42411119.pdf")
      (description "FIXED IND 3.3UH 1.2A 150MOHM SMD")
      (fields
        (field (name "MPN") "MLP2016H3R3MT0S1  (substituted AOTA-B201610S3R3-101-T)")
        (field (name "Manufacturer") "TDK Corporation")
        (field (name "LCSC") "C42411119")
        (field (name "Attrition Qty"))
        (field (name "Capacitance"))
        (field (name "Category"))
        (field (name "Class"))
        (field (name "Minimum Qty"))
        (field (name "Part"))
        (field (name "Price"))
        (field (name "Process"))
        (field (name "Stock"))
        (field (name "Temperature Coefficient"))
        (field (name "Tolerance"))
        (field (name "Voltage Rated"))
        (field (name "Peak Wavelength"))
        (field (name "Footprint") "RP2350_60QFN_minimal:L_pol_2016")
        (field (name "Datasheet") "https://lcsc.com/datasheet/lcsc_datasheet_2412101620_ABRACON-AOTA-B201610S3R3-101-T_C42411119.pdf")
        (field (name "Description") "FIXED IND 3.3UH 1.2A 150MOHM SMD"))
      (libsource (lib "") (part "L_1") (description "FIXED IND 3.3UH 1.2A 150MOHM SMD"))
      (property (name "MPN") (value "MLP2016H3R3MT0S1  (substituted AOTA-B201610S3R3-101-T)"))
      (property (name "Manufacturer") (value "TDK Corporation"))
      (property (name "LCSC") (value "C42411119"))
      (property (name "Attrition Qty") (value ""))
      (property (name "Capacitance") (value ""))
      (property (name "Category") (value ""))
      (property (name "Class") (value ""))
      (property (name "Minimum Qty") (value ""))
      (property (name "Part") (value ""))
      (property (name "Price") (value ""))
      (property (name "Process") (value ""))
      (property (name "Stock") (value ""))
      (property (name "Temperature Coefficient") (value ""))
      (property (name "Tolerance") (value ""))
      (property (name "Voltage Rated") (value ""))
      (property (name "Peak Wavelength") (value ""))
      (property (name "Sheetname") (value "Root"))
      (property (name "Sheetfile") (value "Pico_Development_Stack.kicad_sch"))
      (property (name "ki_keywords") (value "inductor choke coil reactor magnetic"))
      (property (name "ki_fp_filters") (value "Choke_* *Coil* Inductor_* L_*"))
      (sheetpath (names "/") (tstamps "/"))
      (tstamps "5e161da0-e50c-4f34-a66e-d46ecc302bc6"))
    (comp (ref "L2")
      (value "3.3u")
      (footprint "RP2350_60QFN_minimal:L_pol_2016")
      (datasheet "https://lcsc.com/datasheet/lcsc_datasheet_2412101620_ABRACON-AOTA-B201610S3R3-101-T_C42411119.pdf")
      (description "FIXED IND 3.3UH 1.2A 150MOHM SMD")
      (fields
        (field (name "MPN") "MLP2016H3R3MT0S1  (substituted AOTA-B201610S3R3-101-T)")
        (field (name "Manufacturer") "TDK Corporation")
        (field (name "LCSC") "C42411119")
        (field (name "Attrition Qty"))
        (field (name "Capacitance"))
        (field (name "Category"))
        (field (name "Class"))
        (field (name "Minimum Qty"))
        (field (name "Part"))
        (field (name "Price"))
        (field (name "Process"))
        (field (name "Stock"))
        (field (name "Temperature Coefficient"))
        (field (name "Tolerance"))
        (field (name "Voltage Rated"))
        (field (name "Peak Wavelength"))
        (field (name "Footprint") "RP2350_60QFN_minimal:L_pol_2016")
        (field (name "Datasheet") "https://lcsc.com/datasheet/lcsc_datasheet_2412101620_ABRACON-AOTA-B201610S3R3-101-T_C42411119.pdf")
        (field (name "Description") "FIXED IND 3.3UH 1.2A 150MOHM SMD"))
      (libsource (lib "") (part "L_1") (description "FIXED IND 3.3UH 1.2A 150MOHM SMD"))
      (property (name "MPN") (value "MLP2016H3R3MT0S1  (substituted AOTA-B201610S3R3-101-T)"))
      (property (name "Manufacturer") (value "TDK Corporation"))
      (property (name "LCSC") (value "C42411119"))
      (property (name "Attrition Qty") (value ""))
      (property (name "Capacitance") (value ""))
      (property (name "Category") (value ""))
      (property (name "Class") (value ""))
      (property (name "Minimum Qty") (value ""))
      (property (name "Part") (value ""))
      (property (name "Price") (value ""))
      (property (name "Process") (value ""))
      (property (name "Stock") (value ""))
      (property (name "Temperature Coefficient") (value ""))
      (property (name "Tolerance") (value ""))
      (property (name "Voltage Rated") (value ""))
      (property (name "Peak Wavelength") (value ""))
      (property (name "Sheetname") (value "Root"))
      (property (name "Sheetfile") (value "Pico_Development_Stack.kicad_sch"))
      (property (name "ki_keywords") (value "inductor choke coil reactor magnetic"))
      (property (name "ki_fp_filters") (value "Choke_* *Coil* Inductor_* L_*"))
      (sheetpath (names "/") (tstamps "/"))
      (tstamps "be5c274a-0f05-4272-9dc6-86db70678593"))
    (comp (ref "L3")
      (value "3.3u")
      (footprint "RP2350_60QFN_minimal:L_pol_2016")
      (datasheet "https://lcsc.com/datasheet/lcsc_datasheet_2412101620_ABRACON-AOTA-B201610S3R3-101-T_C42411119.pdf")
      (description "FIXED IND 3.3UH 1.2A 150MOHM SMD")
      (fields
        (field (name "MPN") "MLP2016H3R3MT0S1  (substituted AOTA-B201610S3R3-101-T)")
        (field (name "Manufacturer") "TDK Corporation")
        (field (name "LCSC") "C42411119")
        (field (name "Attrition Qty"))
        (field (name "Capacitance"))
        (field (name "Category"))
        (field (name "Class"))
        (field (name "Minimum Qty"))
        (field (name "Part"))
        (field (name "Price"))
        (field (name "Process"))
        (field (name "Stock"))
        (field (name "Temperature Coefficient"))
        (field (name "Tolerance"))
        (field (name "Voltage Rated"))
        (field (name "Peak Wavelength"))
        (field (name "Footprint") "RP2350_60QFN_minimal:L_pol_2016")
        (field (name "Datasheet") "https://lcsc.com/datasheet/lcsc_datasheet_2412101620_ABRACON-AOTA-B201610S3R3-101-T_C42411119.pdf")
        (field (name "Description") "FIXED IND 3.3UH 1.2A 150MOHM SMD"))
      (libsource (lib "") (part "L_1") (description "FIXED IND 3.3UH 1.2A 150MOHM SMD"))
      (property (name "MPN") (value "MLP2016H3R3MT0S1  (substituted AOTA-B201610S3R3-101-T)"))
      (property (name "Manufacturer") (value "TDK Corporation"))
      (property (name "LCSC") (value "C42411119"))
      (property (name "Attrition Qty") (value ""))
      (property (name "Capacitance") (value ""))
      (property (name "Category") (value ""))
      (property (name "Class") (value ""))
      (property (name "Minimum Qty") (value ""))
      (property (name "Part") (value ""))
      (property (name "Price") (value ""))
      (property (name "Process") (value ""))
      (property (name "Stock") (value ""))
      (property (name "Temperature Coefficient") (value ""))
      (property (name "Tolerance") (value ""))
      (property (name "Voltage Rated") (value ""))
      (property (name "Peak Wavelength") (value ""))
      (property (name "Sheetname") (value "Root"))
      (property (name "Sheetfile") (value "Pico_Development_Stack.kicad_sch"))
      (property (name "ki_keywords") (value "inductor choke coil reactor magnetic"))
      (property (name "ki_fp_filters") (value "Choke_* *Coil* Inductor_* L_*"))
      (sheetpath (names "/") (tstamps "/"))
      (tstamps "b89c7669-9454-4ffd-bd4a-16ec1bcdc85b"))
    (comp (ref "L4")
      (value "3.3u")
      (footprint "RP2350_60QFN_minimal:L_pol_2016")
      (datasheet "https://lcsc.com/datasheet/lcsc_datasheet_2412101620_ABRACON-AOTA-B201610S3R3-101-T_C42411119.pdf")
      (description "FIXED IND 3.3UH 1.2A 150MOHM SMD")
      (fields
        (field (name "MPN") "MLP2016H3R3MT0S1  (substituted AOTA-B201610S3R3-101-T)")
        (field (name "Manufacturer") "TDK Corporation")
        (field (name "LCSC") "C42411119")
        (field (name "Attrition Qty"))
        (field (name "Capacitance"))
        (field (name "Category"))
        (field (name "Class"))
        (field (name "Minimum Qty"))
        (field (name "Part"))
        (field (name "Price"))
        (field (name "Process"))
        (field (name "Stock"))
        (field (name "Temperature Coefficient"))
        (field (name "Tolerance"))
        (field (name "Voltage Rated"))
        (field (name "Peak Wavelength"))
        (field (name "Footprint") "RP2350_60QFN_minimal:L_pol_2016")
        (field (name "Datasheet") "https://lcsc.com/datasheet/lcsc_datasheet_2412101620_ABRACON-AOTA-B201610S3R3-101-T_C42411119.pdf")
        (field (name "Description") "FIXED IND 3.3UH 1.2A 150MOHM SMD"))
      (libsource (lib "") (part "L_1") (description "FIXED IND 3.3UH 1.2A 150MOHM SMD"))
      (property (name "MPN") (value "MLP2016H3R3MT0S1  (substituted AOTA-B201610S3R3-101-T)"))
      (property (name "Manufacturer") (value "TDK Corporation"))
      (property (name "LCSC") (value "C42411119"))
      (property (name "Attrition Qty") (value ""))
      (property (name "Capacitance") (value ""))
      (property (name "Category") (value ""))
      (property (name "Class") (value ""))
      (property (name "Minimum Qty") (value ""))
      (property (name "Part") (value ""))
      (property (name "Price") (value ""))
      (property (name "Process") (value ""))
      (property (name "Stock") (value ""))
      (property (name "Temperature Coefficient") (value ""))
      (property (name "Tolerance") (value ""))
      (property (name "Voltage Rated") (value ""))
      (property (name "Peak Wavelength") (value ""))
      (property (name "Sheetname") (value "Root"))
      (property (name "Sheetfile") (value "Pico_Development_Stack.kicad_sch"))
      (property (name "ki_keywords") (value "inductor choke coil reactor magnetic"))
      (property (name "ki_fp_filters") (value "Choke_* *Coil* Inductor_* L_*"))
      (sheetpath (names "/") (tstamps "/"))
      (tstamps "c067a2de-0410-451f-be36-9b976feb9291"))
    (comp (ref "R1")
      (value "330")
      (footprint "PCM_JLCPCB:R_0603")
      (datasheet "https://www.lcsc.com/datasheet/lcsc_datasheet_2206010116_UNI-ROYAL-Uniroyal-Elec-0603WAF3300T5E_C23138.pdf")
      (description "100mW Thick Film Resistors 75V ±100ppm/°C ±1% 330Ω 0603 Chip Resistor - Surface Mount ROHS")
      (fields
        (field (name "LCSC") "C23138")
        (field (name "Peak Wavelength"))
        (field (name "Stock") "2977706")
        (field (name "Price") "0.004USD")
        (field (name "Process") "SMT")
        (field (name "Minimum Qty") "20")
        (field (name "Attrition Qty") "10")
        (field (name "Class") "Basic Component")
        (field (name "Category") "Resistors,Chip Resistor - Surface Mount")
        (field (name "Manufacturer") "UNI-ROYAL(Uniroyal Elec)")
        (field (name "Part") "0603WAF3300T5E")
        (field (name "Resistance") "330Ω")
        (field (name "Power(Watts)") "100mW")
        (field (name "Type") "Thick Film Resistors")
        (field (name "Overload Voltage (Max)") "75V")
        (field (name "Operating Temperature Range") "-55°C~+155°C")
        (field (name "Tolerance") "±1%")
        (field (name "Temperature Coefficient") "±100ppm/°C")
        (field (name "Footprint") "PCM_JLCPCB:R_0603")
        (field (name "Datasheet") "https://www.lcsc.com/datasheet/lcsc_datasheet_2206010116_UNI-ROYAL-Uniroyal-Elec-0603WAF3300T5E_C23138.pdf")
        (field (name "Description") "100mW Thick Film Resistors 75V ±100ppm/°C ±1% 330Ω 0603 Chip Resistor - Surface Mount ROHS"))
      (libsource (lib "PCM_JLCPCB-Resistors") (part "0603,330Ω") (description "100mW Thick Film Resistors 75V ±100ppm/°C ±1% 330Ω 0603 Chip Resistor - Surface Mount ROHS"))
      (property (name "LCSC") (value "C23138"))
      (property (name "Peak Wavelength") (value ""))
      (property (name "Stock") (value "2977706"))
      (property (name "Price") (value "0.004USD"))
      (property (name "Process") (value "SMT"))
      (property (name "Minimum Qty") (value "20"))
      (property (name "Attrition Qty") (value "10"))
      (property (name "Class") (value "Basic Component"))
      (property (name "Category") (value "Resistors,Chip Resistor - Surface Mount"))
      (property (name "Manufacturer") (value "UNI-ROYAL(Uniroyal Elec)"))
      (property (name "Part") (value "0603WAF3300T5E"))
      (property (name "Resistance") (value "330Ω"))
      (property (name "Power(Watts)") (value "100mW"))
      (property (name "Type") (value "Thick Film Resistors"))
      (property (name "Overload Voltage (Max)") (value "75V"))
      (property (name "Operating Temperature Range") (value "-55°C~+155°C"))
      (property (name "Tolerance") (value "±1%"))
      (property (name "Temperature Coefficient") (value "±100ppm/°C"))
      (property (name "Sheetname") (value "Root"))
      (property (name "Sheetfile") (value "Pico_Development_Stack.kicad_sch"))
      (property (name "ki_fp_filters") (value "R_*"))
      (sheetpath (names "/") (tstamps "/"))
      (tstamps "da9b8adb-8030-4fa9-adce-ca6d056d3193"))
    (comp (ref "R2")
      (value "330")
      (footprint "PCM_JLCPCB:R_0603")
      (datasheet "https://www.lcsc.com/datasheet/lcsc_datasheet_2206010116_UNI-ROYAL-Uniroyal-Elec-0603WAF3300T5E_C23138.pdf")
      (description "100mW Thick Film Resistors 75V ±100ppm/°C ±1% 330Ω 0603 Chip Resistor - Surface Mount ROHS")
      (fields
        (field (name "LCSC") "C23138")
        (field (name "Peak Wavelength"))
        (field (name "Stock") "2977706")
        (field (name "Price") "0.004USD")
        (field (name "Process") "SMT")
        (field (name "Minimum Qty") "20")
        (field (name "Attrition Qty") "10")
        (field (name "Class") "Basic Component")
        (field (name "Category") "Resistors,Chip Resistor - Surface Mount")
        (field (name "Manufacturer") "UNI-ROYAL(Uniroyal Elec)")
        (field (name "Part") "0603WAF3300T5E")
        (field (name "Resistance") "330Ω")
        (field (name "Power(Watts)") "100mW")
        (field (name "Type") "Thick Film Resistors")
        (field (name "Overload Voltage (Max)") "75V")
        (field (name "Operating Temperature Range") "-55°C~+155°C")
        (field (name "Tolerance") "±1%")
        (field (name "Temperature Coefficient") "±100ppm/°C")
        (field (name "Footprint") "PCM_JLCPCB:R_0603")
        (field (name "Datasheet") "https://www.lcsc.com/datasheet/lcsc_datasheet_2206010116_UNI-ROYAL-Uniroyal-Elec-0603WAF3300T5E_C23138.pdf")
        (field (name "Description") "100mW Thick Film Resistors 75V ±100ppm/°C ±1% 330Ω 0603 Chip Resistor - Surface Mount ROHS"))
      (libsource (lib "PCM_JLCPCB-Resistors") (part "0603,330Ω") (description "100mW Thick Film Resistors 75V ±100ppm/°C ±1% 330Ω 0603 Chip Resistor - Surface Mount ROHS"))
      (property (name "LCSC") (value "C23138"))
      (property (name "Peak Wavelength") (value ""))
      (property (name "Stock") (value "2977706"))
      (property (name "Price") (value "0.004USD"))
      (property (name "Process") (value "SMT"))
      (property (name "Minimum Qty") (value "20"))
      (property (name "Attrition Qty") (value "10"))
      (property (name "Class") (value "Basic Component"))
      (property (name "Category") (value "Resistors,Chip Resistor - Surface Mount"))
      (property (name "Manufacturer") (value "UNI-ROYAL(Uniroyal Elec)"))
      (property (name "Part") (value "0603WAF3300T5E"))
      (property (name "Resistance") (value "330Ω"))
      (property (name "Power(Watts)") (value "100mW"))
      (property (name "Type") (value "Thick Film Resistors"))
      (property (name "Overload Voltage (Max)") (value "75V"))
      (property (name "Operating Temperature Range") (value "-55°C~+155°C"))
      (property (name "Tolerance") (value "±1%"))
      (property (name "Temperature Coefficient") (value "±100ppm/°C"))
      (property (name "Sheetname") (value "Root"))
      (property (name "Sheetfile") (value "Pico_Development_Stack.kicad_sch"))
      (property (name "ki_fp_filters") (value "R_*"))
      (sheetpath (names "/") (tstamps "/"))
      (tstamps "48f871f1-1a21-4012-8d5c-1cacccdf2214"))
    (comp (ref "R3")
      (value "330")
      (footprint "PCM_JLCPCB:R_0603")
      (datasheet "https://www.lcsc.com/datasheet/lcsc_datasheet_2206010116_UNI-ROYAL-Uniroyal-Elec-0603WAF3300T5E_C23138.pdf")
      (description "100mW Thick Film Resistors 75V ±100ppm/°C ±1% 330Ω 0603 Chip Resistor - Surface Mount ROHS")
      (fields
        (field (name "LCSC") "C23138")
        (field (name "Peak Wavelength"))
        (field (name "Stock") "2977706")
        (field (name "Price") "0.004USD")
        (field (name "Process") "SMT")
        (field (name "Minimum Qty") "20")
        (field (name "Attrition Qty") "10")
        (field (name "Class") "Basic Component")
        (field (name "Category") "Resistors,Chip Resistor - Surface Mount")
        (field (name "Manufacturer") "UNI-ROYAL(Uniroyal Elec)")
        (field (name "Part") "0603WAF3300T5E")
        (field (name "Resistance") "330Ω")
        (field (name "Power(Watts)") "100mW")
        (field (name "Type") "Thick Film Resistors")
        (field (name "Overload Voltage (Max)") "75V")
        (field (name "Operating Temperature Range") "-55°C~+155°C")
        (field (name "Tolerance") "±1%")
        (field (name "Temperature Coefficient") "±100ppm/°C")
        (field (name "Footprint") "PCM_JLCPCB:R_0603")
        (field (name "Datasheet") "https://www.lcsc.com/datasheet/lcsc_datasheet_2206010116_UNI-ROYAL-Uniroyal-Elec-0603WAF3300T5E_C23138.pdf")
        (field (name "Description") "100mW Thick Film Resistors 75V ±100ppm/°C ±1% 330Ω 0603 Chip Resistor - Surface Mount ROHS"))
      (libsource (lib "PCM_JLCPCB-Resistors") (part "0603,330Ω") (description "100mW Thick Film Resistors 75V ±100ppm/°C ±1% 330Ω 0603 Chip Resistor - Surface Mount ROHS"))
      (property (name "LCSC") (value "C23138"))
      (property (name "Peak Wavelength") (value ""))
      (property (name "Stock") (value "2977706"))
      (property (name "Price") (value "0.004USD"))
      (property (name "Process") (value "SMT"))
      (property (name "Minimum Qty") (value "20"))
      (property (name "Attrition Qty") (value "10"))
      (property (name "Class") (value "Basic Component"))
      (property (name "Category") (value "Resistors,Chip Resistor - Surface Mount"))
      (property (name "Manufacturer") (value "UNI-ROYAL(Uniroyal Elec)"))
      (property (name "Part") (value "0603WAF3300T5E"))
      (property (name "Resistance") (value "330Ω"))
      (property (name "Power(Watts)") (value "100mW"))
      (property (name "Type") (value "Thick Film Resistors"))
      (property (name "Overload Voltage (Max)") (value "75V"))
      (property (name "Operating Temperature Range") (value "-55°C~+155°C"))
      (property (name "Tolerance") (value "±1%"))
      (property (name "Temperature Coefficient") (value "±100ppm/°C"))
      (property (name "Sheetname") (value "Root"))
      (property (name "Sheetfile") (value "Pico_Development_Stack.kicad_sch"))
      (property (name "ki_fp_filters") (value "R_*"))
      (sheetpath (names "/") (tstamps "/"))
      (tstamps "8f75873a-5fff-40bb-af49-31d98dc52693"))
    (comp (ref "R4")
      (value "22")
      (footprint "PCM_JLCPCB:R_0603")
      (datasheet "https://www.lcsc.com/datasheet/lcsc_datasheet_2206010100_UNI-ROYAL-Uniroyal-Elec-0603WAF220JT5E_C23345.pdf")
      (description "100mW Thick Film Resistors 75V ±100ppm/°C ±1% 22Ω 0603 Chip Resistor - Surface Mount ROHS")
      (fields
        (field (name "LCSC") "C23345")
        (field (name "Peak Wavelength"))
        (field (name "Stock") "4414856")
        (field (name "Price") "0.004USD")
        (field (name "Process") "SMT")
        (field (name "Minimum Qty") "20")
        (field (name "Attrition Qty") "10")
        (field (name "Class") "Basic Component")
        (field (name "Category") "Resistors,Chip Resistor - Surface Mount")
        (field (name "Manufacturer") "UNI-ROYAL(Uniroyal Elec)")
        (field (name "Part") "0603WAF220JT5E")
        (field (name "Resistance") "22Ω")
        (field (name "Power(Watts)") "100mW")
        (field (name "Type") "Thick Film Resistors")
        (field (name "Overload Voltage (Max)") "75V")
        (field (name "Operating Temperature Range") "-55°C~+155°C")
        (field (name "Tolerance") "±1%")
        (field (name "Temperature Coefficient") "±100ppm/°C")
        (field (name "Footprint") "PCM_JLCPCB:R_0603")
        (field (name "Datasheet") "https://www.lcsc.com/datasheet/lcsc_datasheet_2206010100_UNI-ROYAL-Uniroyal-Elec-0603WAF220JT5E_C23345.pdf")
        (field (name "Description") "100mW Thick Film Resistors 75V ±100ppm/°C ±1% 22Ω 0603 Chip Resistor - Surface Mount ROHS"))
      (libsource (lib "PCM_JLCPCB-Resistors") (part "0603,22Ω") (description "100mW Thick Film Resistors 75V ±100ppm/°C ±1% 22Ω 0603 Chip Resistor - Surface Mount ROHS"))
      (property (name "LCSC") (value "C23345"))
      (property (name "Peak Wavelength") (value ""))
      (property (name "Stock") (value "4414856"))
      (property (name "Price") (value "0.004USD"))
      (property (name "Process") (value "SMT"))
      (property (name "Minimum Qty") (value "20"))
      (property (name "Attrition Qty") (value "10"))
      (property (name "Class") (value "Basic Component"))
      (property (name "Category") (value "Resistors,Chip Resistor - Surface Mount"))
      (property (name "Manufacturer") (value "UNI-ROYAL(Uniroyal Elec)"))
      (property (name "Part") (value "0603WAF220JT5E"))
      (property (name "Resistance") (value "22Ω"))
      (property (name "Power(Watts)") (value "100mW"))
      (property (name "Type") (value "Thick Film Resistors"))
      (property (name "Overload Voltage (Max)") (value "75V"))
      (property (name "Operating Temperature Range") (value "-55°C~+155°C"))
      (property (name "Tolerance") (value "±1%"))
      (property (name "Temperature Coefficient") (value "±100ppm/°C"))
      (property (name "Sheetname") (value "Root"))
      (property (name "Sheetfile") (value "Pico_Development_Stack.kicad_sch"))
      (property (name "ki_fp_filters") (value "R_*"))
      (sheetpath (names "/") (tstamps "/"))
      (tstamps "8df98e3b-c3b9-4cdc-b57d-39e88ebd295b"))
    (comp (ref "R5")
      (value "22")
      (footprint "PCM_JLCPCB:R_0603")
      (datasheet "https://www.lcsc.com/datasheet/lcsc_datasheet_2206010100_UNI-ROYAL-Uniroyal-Elec-0603WAF220JT5E_C23345.pdf")
      (description "100mW Thick Film Resistors 75V ±100ppm/°C ±1% 22Ω 0603 Chip Resistor - Surface Mount ROHS")
      (fields
        (field (name "LCSC") "C23345")
        (field (name "Peak Wavelength"))
        (field (name "Stock") "4414856")
        (field (name "Price") "0.004USD")
        (field (name "Process") "SMT")
        (field (name "Minimum Qty") "20")
        (field (name "Attrition Qty") "10")
        (field (name "Class") "Basic Component")
        (field (name "Category") "Resistors,Chip Resistor - Surface Mount")
        (field (name "Manufacturer") "UNI-ROYAL(Uniroyal Elec)")
        (field (name "Part") "0603WAF220JT5E")
        (field (name "Resistance") "22Ω")
        (field (name "Power(Watts)") "100mW")
        (field (name "Type") "Thick Film Resistors")
        (field (name "Overload Voltage (Max)") "75V")
        (field (name "Operating Temperature Range") "-55°C~+155°C")
        (field (name "Tolerance") "±1%")
        (field (name "Temperature Coefficient") "±100ppm/°C")
        (field (name "Footprint") "PCM_JLCPCB:R_0603")
        (field (name "Datasheet") "https://www.lcsc.com/datasheet/lcsc_datasheet_2206010100_UNI-ROYAL-Uniroyal-Elec-0603WAF220JT5E_C23345.pdf")
        (field (name "Description") "100mW Thick Film Resistors 75V ±100ppm/°C ±1% 22Ω 0603 Chip Resistor - Surface Mount ROHS"))
      (libsource (lib "PCM_JLCPCB-Resistors") (part "0603,22Ω") (description "100mW Thick Film Resistors 75V ±100ppm/°C ±1% 22Ω 0603 Chip Resistor - Surface Mount ROHS"))
      (property (name "LCSC") (value "C23345"))
      (property (name "Peak Wavelength") (value ""))
      (property (name "Stock") (value "4414856"))
      (property (name "Price") (value "0.004USD"))
      (property (name "Process") (value "SMT"))
      (property (name "Minimum Qty") (value "20"))
      (property (name "Attrition Qty") (value "10"))
      (property (name "Class") (value "Basic Component"))
      (property (name "Category") (value "Resistors,Chip Resistor - Surface Mount"))
      (property (name "Manufacturer") (value "UNI-ROYAL(Uniroyal Elec)"))
      (property (name "Part") (value "0603WAF220JT5E"))
      (property (name "Resistance") (value "22Ω"))
      (property (name "Power(Watts)") (value "100mW"))
      (property (name "Type") (value "Thick Film Resistors"))
      (property (name "Overload Voltage (Max)") (value "75V"))
      (property (name "Operating Temperature Range") (value "-55°C~+155°C"))
      (property (name "Tolerance") (value "±1%"))
      (property (name "Temperature Coefficient") (value "±100ppm/°C"))
      (property (name "Sheetname") (value "Root"))
      (property (name "Sheetfile") (value "Pico_Development_Stack.kicad_sch"))
      (property (name "ki_fp_filters") (value "R_*"))
      (sheetpath (names "/") (tstamps "/"))
      (tstamps "de2f6447-bb29-4f37-a004-030f87088fa1"))
    (comp (ref "R6")
      (value "22")
      (footprint "PCM_JLCPCB:R_0603")
      (datasheet "https://www.lcsc.com/datasheet/lcsc_datasheet_2206010100_UNI-ROYAL-Uniroyal-Elec-0603WAF220JT5E_C23345.pdf")
      (description "100mW Thick Film Resistors 75V ±100ppm/°C ±1% 22Ω 0603 Chip Resistor - Surface Mount ROHS")
      (fields
        (field (name "LCSC") "C23345")
        (field (name "Peak Wavelength"))
        (field (name "Stock") "4414856")
        (field (name "Price") "0.004USD")
        (field (name "Process") "SMT")
        (field (name "Minimum Qty") "20")
        (field (name "Attrition Qty") "10")
        (field (name "Class") "Basic Component")
        (field (name "Category") "Resistors,Chip Resistor - Surface Mount")
        (field (name "Manufacturer") "UNI-ROYAL(Uniroyal Elec)")
        (field (name "Part") "0603WAF220JT5E")
        (field (name "Resistance") "22Ω")
        (field (name "Power(Watts)") "100mW")
        (field (name "Type") "Thick Film Resistors")
        (field (name "Overload Voltage (Max)") "75V")
        (field (name "Operating Temperature Range") "-55°C~+155°C")
        (field (name "Tolerance") "±1%")
        (field (name "Temperature Coefficient") "±100ppm/°C")
        (field (name "Footprint") "PCM_JLCPCB:R_0603")
        (field (name "Datasheet") "https://www.lcsc.com/datasheet/lcsc_datasheet_2206010100_UNI-ROYAL-Uniroyal-Elec-0603WAF220JT5E_C23345.pdf")
        (field (name "Description") "100mW Thick Film Resistors 75V ±100ppm/°C ±1% 22Ω 0603 Chip Resistor - Surface Mount ROHS"))
      (libsource (lib "PCM_JLCPCB-Resistors") (part "0603,22Ω") (description "100mW Thick Film Resistors 75V ±100ppm/°C ±1% 22Ω 0603 Chip Resistor - Surface Mount ROHS"))
      (property (name "LCSC") (value "C23345"))
      (property (name "Peak Wavelength") (value ""))
      (property (name "Stock") (value "4414856"))
      (property (name "Price") (value "0.004USD"))
      (property (name "Process") (value "SMT"))
      (property (name "Minimum Qty") (value "20"))
      (property (name "Attrition Qty") (value "10"))
      (property (name "Class") (value "Basic Component"))
      (property (name "Category") (value "Resistors,Chip Resistor - Surface Mount"))
      (property (name "Manufacturer") (value "UNI-ROYAL(Uniroyal Elec)"))
      (property (name "Part") (value "0603WAF220JT5E"))
      (property (name "Resistance") (value "22Ω"))
      (property (name "Power(Watts)") (value "100mW"))
      (property (name "Type") (value "Thick Film Resistors"))
      (property (name "Overload Voltage (Max)") (value "75V"))
      (property (name "Operating Temperature Range") (value "-55°C~+155°C"))
      (property (name "Tolerance") (value "±1%"))
      (property (name "Temperature Coefficient") (value "±100ppm/°C"))
      (property (name "Sheetname") (value "Root"))
      (property (name "Sheetfile") (value "Pico_Development_Stack.kicad_sch"))
      (property (name "ki_fp_filters") (value "R_*"))
      (sheetpath (names "/") (tstamps "/"))
      (tstamps "0616c628-f32c-4c66-94e4-90b4649772b5"))
    (comp (ref "R7")
      (value "22")
      (footprint "PCM_JLCPCB:R_0603")
      (datasheet "https://www.lcsc.com/datasheet/lcsc_datasheet_2206010100_UNI-ROYAL-Uniroyal-Elec-0603WAF220JT5E_C23345.pdf")
      (description "100mW Thick Film Resistors 75V ±100ppm/°C ±1% 22Ω 0603 Chip Resistor - Surface Mount ROHS")
      (fields
        (field (name "LCSC") "C23345")
        (field (name "Peak Wavelength"))
        (field (name "Stock") "4414856")
        (field (name "Price") "0.004USD")
        (field (name "Process") "SMT")
        (field (name "Minimum Qty") "20")
        (field (name "Attrition Qty") "10")
        (field (name "Class") "Basic Component")
        (field (name "Category") "Resistors,Chip Resistor - Surface Mount")
        (field (name "Manufacturer") "UNI-ROYAL(Uniroyal Elec)")
        (field (name "Part") "0603WAF220JT5E")
        (field (name "Resistance") "22Ω")
        (field (name "Power(Watts)") "100mW")
        (field (name "Type") "Thick Film Resistors")
        (field (name "Overload Voltage (Max)") "75V")
        (field (name "Operating Temperature Range") "-55°C~+155°C")
        (field (name "Tolerance") "±1%")
        (field (name "Temperature Coefficient") "±100ppm/°C")
        (field (name "Footprint") "PCM_JLCPCB:R_0603")
        (field (name "Datasheet") "https://www.lcsc.com/datasheet/lcsc_datasheet_2206010100_UNI-ROYAL-Uniroyal-Elec-0603WAF220JT5E_C23345.pdf")
        (field (name "Description") "100mW Thick Film Resistors 75V ±100ppm/°C ±1% 22Ω 0603 Chip Resistor - Surface Mount ROHS"))
      (libsource (lib "PCM_JLCPCB-Resistors") (part "0603,22Ω") (description "100mW Thick Film Resistors 75V ±100ppm/°C ±1% 22Ω 0603 Chip Resistor - Surface Mount ROHS"))
      (property (name "LCSC") (value "C23345"))
      (property (name "Peak Wavelength") (value ""))
      (property (name "Stock") (value "4414856"))
      (property (name "Price") (value "0.004USD"))
      (property (name "Process") (value "SMT"))
      (property (name "Minimum Qty") (value "20"))
      (property (name "Attrition Qty") (value "10"))
      (property (name "Class") (value "Basic Component"))
      (property (name "Category") (value "Resistors,Chip Resistor - Surface Mount"))
      (property (name "Manufacturer") (value "UNI-ROYAL(Uniroyal Elec)"))
      (property (name "Part") (value "0603WAF220JT5E"))
      (property (name "Resistance") (value "22Ω"))
      (property (name "Power(Watts)") (value "100mW"))
      (property (name "Type") (value "Thick Film Resistors"))
      (property (name "Overload Voltage (Max)") (value "75V"))
      (property (name "Operating Temperature Range") (value "-55°C~+155°C"))
      (property (name "Tolerance") (value "±1%"))
      (property (name "Temperature Coefficient") (value "±100ppm/°C"))
      (property (name "Sheetname") (value "Root"))
      (property (name "Sheetfile") (value "Pico_Development_Stack.kicad_sch"))
      (property (name "ki_fp_filters") (value "R_*"))
      (sheetpath (names "/") (tstamps "/"))
      (tstamps "37657b15-7338-41fd-85d5-e6561e3c454a"))
    (comp (ref "R8")
      (value "330")
      (footprint "PCM_JLCPCB:R_0603")
      (datasheet "https://www.lcsc.com/datasheet/lcsc_datasheet_2206010116_UNI-ROYAL-Uniroyal-Elec-0603WAF3300T5E_C23138.pdf")
      (description "100mW Thick Film Resistors 75V ±100ppm/°C ±1% 330Ω 0603 Chip Resistor - Surface Mount ROHS")
      (fields
        (field (name "LCSC") "C23138")
        (field (name "Peak Wavelength"))
        (field (name "Stock") "2977706")
        (field (name "Price") "0.004USD")
        (field (name "Process") "SMT")
        (field (name "Minimum Qty") "20")
        (field (name "Attrition Qty") "10")
        (field (name "Class") "Basic Component")
        (field (name "Category") "Resistors,Chip Resistor - Surface Mount")
        (field (name "Manufacturer") "UNI-ROYAL(Uniroyal Elec)")
        (field (name "Part") "0603WAF3300T5E")
        (field (name "Resistance") "330Ω")
        (field (name "Power(Watts)") "100mW")
        (field (name "Type") "Thick Film Resistors")
        (field (name "Overload Voltage (Max)") "75V")
        (field (name "Operating Temperature Range") "-55°C~+155°C")
        (field (name "Tolerance") "±1%")
        (field (name "Temperature Coefficient") "±100ppm/°C")
        (field (name "Footprint") "PCM_JLCPCB:R_0603")
        (field (name "Datasheet") "https://www.lcsc.com/datasheet/lcsc_datasheet_2206010116_UNI-ROYAL-Uniroyal-Elec-0603WAF3300T5E_C23138.pdf")
        (field (name "Description") "100mW Thick Film Resistors 75V ±100ppm/°C ±1% 330Ω 0603 Chip Resistor - Surface Mount ROHS"))
      (libsource (lib "PCM_JLCPCB-Resistors") (part "0603,330Ω") (description "100mW Thick Film Resistors 75V ±100ppm/°C ±1% 330Ω 0603 Chip Resistor - Surface Mount ROHS"))
      (property (name "LCSC") (value "C23138"))
      (property (name "Peak Wavelength") (value ""))
      (property (name "Stock") (value "2977706"))
      (property (name "Price") (value "0.004USD"))
      (property (name "Process") (value "SMT"))
      (property (name "Minimum Qty") (value "20"))
      (property (name "Attrition Qty") (value "10"))
      (property (name "Class") (value "Basic Component"))
      (property (name "Category") (value "Resistors,Chip Resistor - Surface Mount"))
      (property (name "Manufacturer") (value "UNI-ROYAL(Uniroyal Elec)"))
      (property (name "Part") (value "0603WAF3300T5E"))
      (property (name "Resistance") (value "330Ω"))
      (property (name "Power(Watts)") (value "100mW"))
      (property (name "Type") (value "Thick Film Resistors"))
      (property (name "Overload Voltage (Max)") (value "75V"))
      (property (name "Operating Temperature Range") (value "-55°C~+155°C"))
      (property (name "Tolerance") (value "±1%"))
      (property (name "Temperature Coefficient") (value "±100ppm/°C"))
      (property (name "Sheetname") (value "Root"))
      (property (name "Sheetfile") (value "Pico_Development_Stack.kicad_sch"))
      (property (name "ki_fp_filters") (value "R_*"))
      (sheetpath (names "/") (tstamps "/"))
      (tstamps "0e40460a-5850-4a54-b6e1-e9a8b15636f6"))
    (comp (ref "R9")
      (value "330")
      (footprint "PCM_JLCPCB:R_0603")
      (datasheet "https://www.lcsc.com/datasheet/lcsc_datasheet_2206010116_UNI-ROYAL-Uniroyal-Elec-0603WAF3300T5E_C23138.pdf")
      (description "100mW Thick Film Resistors 75V ±100ppm/°C ±1% 330Ω 0603 Chip Resistor - Surface Mount ROHS")
      (fields
        (field (name "LCSC") "C23138")
        (field (name "Peak Wavelength"))
        (field (name "Stock") "2977706")
        (field (name "Price") "0.004USD")
        (field (name "Process") "SMT")
        (field (name "Minimum Qty") "20")
        (field (name "Attrition Qty") "10")
        (field (name "Class") "Basic Component")
        (field (name "Category") "Resistors,Chip Resistor - Surface Mount")
        (field (name "Manufacturer") "UNI-ROYAL(Uniroyal Elec)")
        (field (name "Part") "0603WAF3300T5E")
        (field (name "Resistance") "330Ω")
        (field (name "Power(Watts)") "100mW")
        (field (name "Type") "Thick Film Resistors")
        (field (name "Overload Voltage (Max)") "75V")
        (field (name "Operating Temperature Range") "-55°C~+155°C")
        (field (name "Tolerance") "±1%")
        (field (name "Temperature Coefficient") "±100ppm/°C")
        (field (name "Footprint") "PCM_JLCPCB:R_0603")
        (field (name "Datasheet") "https://www.lcsc.com/datasheet/lcsc_datasheet_2206010116_UNI-ROYAL-Uniroyal-Elec-0603WAF3300T5E_C23138.pdf")
        (field (name "Description") "100mW Thick Film Resistors 75V ±100ppm/°C ±1% 330Ω 0603 Chip Resistor - Surface Mount ROHS"))
      (libsource (lib "PCM_JLCPCB-Resistors") (part "0603,330Ω") (description "100mW Thick Film Resistors 75V ±100ppm/°C ±1% 330Ω 0603 Chip Resistor - Surface Mount ROHS"))
      (property (name "LCSC") (value "C23138"))
      (property (name "Peak Wavelength") (value ""))
      (property (name "Stock") (value "2977706"))
      (property (name "Price") (value "0.004USD"))
      (property (name "Process") (value "SMT"))
      (property (name "Minimum Qty") (value "20"))
      (property (name "Attrition Qty") (value "10"))
      (property (name "Class") (value "Basic Component"))
      (property (name "Category") (value "Resistors,Chip Resistor - Surface Mount"))
      (property (name "Manufacturer") (value "UNI-ROYAL(Uniroyal Elec)"))
      (property (name "Part") (value "0603WAF3300T5E"))
      (property (name "Resistance") (value "330Ω"))
      (property (name "Power(Watts)") (value "100mW"))
      (property (name "Type") (value "Thick Film Resistors"))
      (property (name "Overload Voltage (Max)") (value "75V"))
      (property (name "Operating Temperature Range") (value "-55°C~+155°C"))
      (property (name "Tolerance") (value "±1%"))
      (property (name "Temperature Coefficient") (value "±100ppm/°C"))
      (property (name "Sheetname") (value "Root"))
      (property (name "Sheetfile") (value "Pico_Development_Stack.kicad_sch"))
      (property (name "ki_fp_filters") (value "R_*"))
      (sheetpath (names "/") (tstamps "/"))
      (tstamps "e13491ad-88ef-4ff0-8500-d8d68541fe12"))
    (comp (ref "R10")
      (value "5.1kΩ")
      (footprint "PCM_JLCPCB:R_0603")
      (datasheet "https://www.lcsc.com/datasheet/lcsc_datasheet_2206010116_UNI-ROYAL-Uniroyal-Elec-0603WAF5101T5E_C23186.pdf")
      (description "100mW Thick Film Resistors 75V ±100ppm/°C ±1% 5.1kΩ 0603 Chip Resistor - Surface Mount ROHS")
      (fields
        (field (name "LCSC") "C23186")
        (field (name "Stock") "9223405")
        (field (name "Price") "0.004USD")
        (field (name "Process") "SMT")
        (field (name "Minimum Qty") "20")
        (field (name "Attrition Qty") "10")
        (field (name "Class") "Basic Component")
        (field (name "Category") "Resistors,Chip Resistor - Surface Mount")
        (field (name "Manufacturer") "UNI-ROYAL(Uniroyal Elec)")
        (field (name "Part") "0603WAF5101T5E")
        (field (name "Resistance") "5.1kΩ")
        (field (name "Power(Watts)") "100mW")
        (field (name "Type") "Thick Film Resistors")
        (field (name "Overload Voltage (Max)") "75V")
        (field (name "Operating Temperature Range") "-55°C~+155°C")
        (field (name "Tolerance") "±1%")
        (field (name "Temperature Coefficient") "±100ppm/°C")
        (field (name "Footprint") "PCM_JLCPCB:R_0603")
        (field (name "Datasheet") "https://www.lcsc.com/datasheet/lcsc_datasheet_2206010116_UNI-ROYAL-Uniroyal-Elec-0603WAF5101T5E_C23186.pdf")
        (field (name "Description") "100mW Thick Film Resistors 75V ±100ppm/°C ±1% 5.1kΩ 0603 Chip Resistor - Surface Mount ROHS"))
      (libsource (lib "PCM_JLCPCB-Resistors") (part "0603,5.1kΩ") (description "100mW Thick Film Resistors 75V ±100ppm/°C ±1% 5.1kΩ 0603 Chip Resistor - Surface Mount ROHS"))
      (property (name "LCSC") (value "C23186"))
      (property (name "Stock") (value "9223405"))
      (property (name "Price") (value "0.004USD"))
      (property (name "Process") (value "SMT"))
      (property (name "Minimum Qty") (value "20"))
      (property (name "Attrition Qty") (value "10"))
      (property (name "Class") (value "Basic Component"))
      (property (name "Category") (value "Resistors,Chip Resistor - Surface Mount"))
      (property (name "Manufacturer") (value "UNI-ROYAL(Uniroyal Elec)"))
      (property (name "Part") (value "0603WAF5101T5E"))
      (property (name "Resistance") (value "5.1kΩ"))
      (property (name "Power(Watts)") (value "100mW"))
      (property (name "Type") (value "Thick Film Resistors"))
      (property (name "Overload Voltage (Max)") (value "75V"))
      (property (name "Operating Temperature Range") (value "-55°C~+155°C"))
      (property (name "Tolerance") (value "±1%"))
      (property (name "Temperature Coefficient") (value "±100ppm/°C"))
      (property (name "Sheetname") (value "Root"))
      (property (name "Sheetfile") (value "Pico_Development_Stack.kicad_sch"))
      (property (name "ki_fp_filters") (value "R_*"))
      (sheetpath (names "/") (tstamps "/"))
      (tstamps "f8129f32-5cd1-474b-b174-f6b28252f692"))
    (comp (ref "R11")
      (value "5.1kΩ")
      (footprint "PCM_JLCPCB:R_0603")
      (datasheet "https://www.lcsc.com/datasheet/lcsc_datasheet_2206010116_UNI-ROYAL-Uniroyal-Elec-0603WAF5101T5E_C23186.pdf")
      (description "100mW Thick Film Resistors 75V ±100ppm/°C ±1% 5.1kΩ 0603 Chip Resistor - Surface Mount ROHS")
      (fields
        (field (name "LCSC") "C23186")
        (field (name "Stock") "9223405")
        (field (name "Price") "0.004USD")
        (field (name "Process") "SMT")
        (field (name "Minimum Qty") "20")
        (field (name "Attrition Qty") "10")
        (field (name "Class") "Basic Component")
        (field (name "Category") "Resistors,Chip Resistor - Surface Mount")
        (field (name "Manufacturer") "UNI-ROYAL(Uniroyal Elec)")
        (field (name "Part") "0603WAF5101T5E")
        (field (name "Resistance") "5.1kΩ")
        (field (name "Power(Watts)") "100mW")
        (field (name "Type") "Thick Film Resistors")
        (field (name "Overload Voltage (Max)") "75V")
        (field (name "Operating Temperature Range") "-55°C~+155°C")
        (field (name "Tolerance") "±1%")
        (field (name "Temperature Coefficient") "±100ppm/°C")
        (field (name "Footprint") "PCM_JLCPCB:R_0603")
        (field (name "Datasheet") "https://www.lcsc.com/datasheet/lcsc_datasheet_2206010116_UNI-ROYAL-Uniroyal-Elec-0603WAF5101T5E_C23186.pdf")
        (field (name "Description") "100mW Thick Film Resistors 75V ±100ppm/°C ±1% 5.1kΩ 0603 Chip Resistor - Surface Mount ROHS"))
      (libsource (lib "PCM_JLCPCB-Resistors") (part "0603,5.1kΩ") (description "100mW Thick Film Resistors 75V ±100ppm/°C ±1% 5.1kΩ 0603 Chip Resistor - Surface Mount ROHS"))
      (property (name "LCSC") (value "C23186"))
      (property (name "Stock") (value "9223405"))
      (property (name "Price") (value "0.004USD"))
      (property (name "Process") (value "SMT"))
      (property (name "Minimum Qty") (value "20"))
      (property (name "Attrition Qty") (value "10"))
      (property (name "Class") (value "Basic Component"))
      (property (name "Category") (value "Resistors,Chip Resistor - Surface Mount"))
      (property (name "Manufacturer") (value "UNI-ROYAL(Uniroyal Elec)"))
      (property (name "Part") (value "0603WAF5101T5E"))
      (property (name "Resistance") (value "5.1kΩ"))
      (property (name "Power(Watts)") (value "100mW"))
      (property (name "Type") (value "Thick Film Resistors"))
      (property (name "Overload Voltage (Max)") (value "75V"))
      (property (name "Operating Temperature Range") (value "-55°C~+155°C"))
      (property (name "Tolerance") (value "±1%"))
      (property (name "Temperature Coefficient") (value "±100ppm/°C"))
      (property (name "Sheetname") (value "Root"))
      (property (name "Sheetfile") (value "Pico_Development_Stack.kicad_sch"))
      (property (name "ki_fp_filters") (value "R_*"))
      (sheetpath (names "/") (tstamps "/"))
      (tstamps "28cb001e-4dd3-4b7a-9b26-0097f1e266b2"))
    (comp (ref "R12")
      (value "330")
      (footprint "PCM_JLCPCB:R_0603")
      (datasheet "https://www.lcsc.com/datasheet/lcsc_datasheet_2206010116_UNI-ROYAL-Uniroyal-Elec-0603WAF3300T5E_C23138.pdf")
      (description "100mW Thick Film Resistors 75V ±100ppm/°C ±1% 330Ω 0603 Chip Resistor - Surface Mount ROHS")
      (fields
        (field (name "LCSC") "C23138")
        (field (name "Peak Wavelength"))
        (field (name "Stock") "2977706")
        (field (name "Price") "0.004USD")
        (field (name "Process") "SMT")
        (field (name "Minimum Qty") "20")
        (field (name "Attrition Qty") "10")
        (field (name "Class") "Basic Component")
        (field (name "Category") "Resistors,Chip Resistor - Surface Mount")
        (field (name "Manufacturer") "UNI-ROYAL(Uniroyal Elec)")
        (field (name "Part") "0603WAF3300T5E")
        (field (name "Resistance") "330Ω")
        (field (name "Power(Watts)") "100mW")
        (field (name "Type") "Thick Film Resistors")
        (field (name "Overload Voltage (Max)") "75V")
        (field (name "Operating Temperature Range") "-55°C~+155°C")
        (field (name "Tolerance") "±1%")
        (field (name "Temperature Coefficient") "±100ppm/°C")
        (field (name "Footprint") "PCM_JLCPCB:R_0603")
        (field (name "Datasheet") "https://www.lcsc.com/datasheet/lcsc_datasheet_2206010116_UNI-ROYAL-Uniroyal-Elec-0603WAF3300T5E_C23138.pdf")
        (field (name "Description") "100mW Thick Film Resistors 75V ±100ppm/°C ±1% 330Ω 0603 Chip Resistor - Surface Mount ROHS"))
      (libsource (lib "PCM_JLCPCB-Resistors") (part "0603,330Ω") (description "100mW Thick Film Resistors 75V ±100ppm/°C ±1% 330Ω 0603 Chip Resistor - Surface Mount ROHS"))
      (property (name "LCSC") (value "C23138"))
      (property (name "Peak Wavelength") (value ""))
      (property (name "Stock") (value "2977706"))
      (property (name "Price") (value "0.004USD"))
      (property (name "Process") (value "SMT"))
      (property (name "Minimum Qty") (value "20"))
      (property (name "Attrition Qty") (value "10"))
      (property (name "Class") (value "Basic Component"))
      (property (name "Category") (value "Resistors,Chip Resistor - Surface Mount"))
      (property (name "Manufacturer") (value "UNI-ROYAL(Uniroyal Elec)"))
      (property (name "Part") (value "0603WAF3300T5E"))
      (property (name "Resistance") (value "330Ω"))
      (property (name "Power(Watts)") (value "100mW"))
      (property (name "Type") (value "Thick Film Resistors"))
      (property (name "Overload Voltage (Max)") (value "75V"))
      (property (name "Operating Temperature Range") (value "-55°C~+155°C"))
      (property (name "Tolerance") (value "±1%"))
      (property (name "Temperature Coefficient") (value "±100ppm/°C"))
      (property (name "Sheetname") (value "Root"))
      (property (name "Sheetfile") (value "Pico_Development_Stack.kicad_sch"))
      (property (name "ki_fp_filters") (value "R_*"))
      (sheetpath (names "/") (tstamps "/"))
      (tstamps "6ede1565-ea9c-4fc7-ba22-06e41607a8df"))
    (comp (ref "R13")
      (value "330")
      (footprint "PCM_JLCPCB:R_0603")
      (datasheet "https://www.lcsc.com/datasheet/lcsc_datasheet_2206010116_UNI-ROYAL-Uniroyal-Elec-0603WAF3300T5E_C23138.pdf")
      (description "100mW Thick Film Resistors 75V ±100ppm/°C ±1% 330Ω 0603 Chip Resistor - Surface Mount ROHS")
      (fields
        (field (name "LCSC") "C23138")
        (field (name "Peak Wavelength"))
        (field (name "Stock") "2977706")
        (field (name "Price") "0.004USD")
        (field (name "Process") "SMT")
        (field (name "Minimum Qty") "20")
        (field (name "Attrition Qty") "10")
        (field (name "Class") "Basic Component")
        (field (name "Category") "Resistors,Chip Resistor - Surface Mount")
        (field (name "Manufacturer") "UNI-ROYAL(Uniroyal Elec)")
        (field (name "Part") "0603WAF3300T5E")
        (field (name "Resistance") "330Ω")
        (field (name "Power(Watts)") "100mW")
        (field (name "Type") "Thick Film Resistors")
        (field (name "Overload Voltage (Max)") "75V")
        (field (name "Operating Temperature Range") "-55°C~+155°C")
        (field (name "Tolerance") "±1%")
        (field (name "Temperature Coefficient") "±100ppm/°C")
        (field (name "Footprint") "PCM_JLCPCB:R_0603")
        (field (name "Datasheet") "https://www.lcsc.com/datasheet/lcsc_datasheet_2206010116_UNI-ROYAL-Uniroyal-Elec-0603WAF3300T5E_C23138.pdf")
        (field (name "Description") "100mW Thick Film Resistors 75V ±100ppm/°C ±1% 330Ω 0603 Chip Resistor - Surface Mount ROHS"))
      (libsource (lib "PCM_JLCPCB-Resistors") (part "0603,330Ω") (description "100mW Thick Film Resistors 75V ±100ppm/°C ±1% 330Ω 0603 Chip Resistor - Surface Mount ROHS"))
      (property (name "LCSC") (value "C23138"))
      (property (name "Peak Wavelength") (value ""))
      (property (name "Stock") (value "2977706"))
      (property (name "Price") (value "0.004USD"))
      (property (name "Process") (value "SMT"))
      (property (name "Minimum Qty") (value "20"))
      (property (name "Attrition Qty") (value "10"))
      (property (name "Class") (value "Basic Component"))
      (property (name "Category") (value "Resistors,Chip Resistor - Surface Mount"))
      (property (name "Manufacturer") (value "UNI-ROYAL(Uniroyal Elec)"))
      (property (name "Part") (value "0603WAF3300T5E"))
      (property (name "Resistance") (value "330Ω"))
      (property (name "Power(Watts)") (value "100mW"))
      (property (name "Type") (value "Thick Film Resistors"))
      (property (name "Overload Voltage (Max)") (value "75V"))
      (property (name "Operating Temperature Range") (value "-55°C~+155°C"))
      (property (name "Tolerance") (value "±1%"))
      (property (name "Temperature Coefficient") (value "±100ppm/°C"))
      (property (name "Sheetname") (value "Root"))
      (property (name "Sheetfile") (value "Pico_Development_Stack.kicad_sch"))
      (property (name "ki_fp_filters") (value "R_*"))
      (sheetpath (names "/") (tstamps "/"))
      (tstamps "7395505f-bbc3-455a-acfb-c465ac045dd1"))
    (comp (ref "R14")
      (value "330")
      (footprint "PCM_JLCPCB:R_0603")
      (datasheet "https://www.lcsc.com/datasheet/lcsc_datasheet_2206010116_UNI-ROYAL-Uniroyal-Elec-0603WAF3300T5E_C23138.pdf")
      (description "100mW Thick Film Resistors 75V ±100ppm/°C ±1% 330Ω 0603 Chip Resistor - Surface Mount ROHS")
      (fields
        (field (name "LCSC") "C23138")
        (field (name "Peak Wavelength"))
        (field (name "Stock") "2977706")
        (field (name "Price") "0.004USD")
        (field (name "Process") "SMT")
        (field (name "Minimum Qty") "20")
        (field (name "Attrition Qty") "10")
        (field (name "Class") "Basic Component")
        (field (name "Category") "Resistors,Chip Resistor - Surface Mount")
        (field (name "Manufacturer") "UNI-ROYAL(Uniroyal Elec)")
        (field (name "Part") "0603WAF3300T5E")
        (field (name "Resistance") "330Ω")
        (field (name "Power(Watts)") "100mW")
        (field (name "Type") "Thick Film Resistors")
        (field (name "Overload Voltage (Max)") "75V")
        (field (name "Operating Temperature Range") "-55°C~+155°C")
        (field (name "Tolerance") "±1%")
        (field (name "Temperature Coefficient") "±100ppm/°C")
        (field (name "Footprint") "PCM_JLCPCB:R_0603")
        (field (name "Datasheet") "https://www.lcsc.com/datasheet/lcsc_datasheet_2206010116_UNI-ROYAL-Uniroyal-Elec-0603WAF3300T5E_C23138.pdf")
        (field (name "Description") "100mW Thick Film Resistors 75V ±100ppm/°C ±1% 330Ω 0603 Chip Resistor - Surface Mount ROHS"))
      (libsource (lib "PCM_JLCPCB-Resistors") (part "0603,330Ω") (description "100mW Thick Film Resistors 75V ±100ppm/°C ±1% 330Ω 0603 Chip Resistor - Surface Mount ROHS"))
      (property (name "LCSC") (value "C23138"))
      (property (name "Peak Wavelength") (value ""))
      (property (name "Stock") (value "2977706"))
      (property (name "Price") (value "0.004USD"))
      (property (name "Process") (value "SMT"))
      (property (name "Minimum Qty") (value "20"))
      (property (name "Attrition Qty") (value "10"))
      (property (name "Class") (value "Basic Component"))
      (property (name "Category") (value "Resistors,Chip Resistor - Surface Mount"))
      (property (name "Manufacturer") (value "UNI-ROYAL(Uniroyal Elec)"))
      (property (name "Part") (value "0603WAF3300T5E"))
      (property (name "Resistance") (value "330Ω"))
      (property (name "Power(Watts)") (value "100mW"))
      (property (name "Type") (value "Thick Film Resistors"))
      (property (name "Overload Voltage (Max)") (value "75V"))
      (property (name "Operating Temperature Range") (value "-55°C~+155°C"))
      (property (name "Tolerance") (value "±1%"))
      (property (name "Temperature Coefficient") (value "±100ppm/°C"))
      (property (name "Sheetname") (value "Root"))
      (property (name "Sheetfile") (value "Pico_Development_Stack.kicad_sch"))
      (property (name "ki_fp_filters") (value "R_*"))
      (sheetpath (names "/") (tstamps "/"))
      (tstamps "c45eae23-ad82-4652-aa3b-516f1d8dec7b"))
    (comp (ref "R15")
      (value "330")
      (footprint "PCM_JLCPCB:R_0603")
      (datasheet "https://www.lcsc.com/datasheet/lcsc_datasheet_2206010116_UNI-ROYAL-Uniroyal-Elec-0603WAF3300T5E_C23138.pdf")
      (description "100mW Thick Film Resistors 75V ±100ppm/°C ±1% 330Ω 0603 Chip Resistor - Surface Mount ROHS")
      (fields
        (field (name "LCSC") "C23138")
        (field (name "Peak Wavelength"))
        (field (name "Stock") "2977706")
        (field (name "Price") "0.004USD")
        (field (name "Process") "SMT")
        (field (name "Minimum Qty") "20")
        (field (name "Attrition Qty") "10")
        (field (name "Class") "Basic Component")
        (field (name "Category") "Resistors,Chip Resistor - Surface Mount")
        (field (name "Manufacturer") "UNI-ROYAL(Uniroyal Elec)")
        (field (name "Part") "0603WAF3300T5E")
        (field (name "Resistance") "330Ω")
        (field (name "Power(Watts)") "100mW")
        (field (name "Type") "Thick Film Resistors")
        (field (name "Overload Voltage (Max)") "75V")
        (field (name "Operating Temperature Range") "-55°C~+155°C")
        (field (name "Tolerance") "±1%")
        (field (name "Temperature Coefficient") "±100ppm/°C")
        (field (name "Footprint") "PCM_JLCPCB:R_0603")
        (field (name "Datasheet") "https://www.lcsc.com/datasheet/lcsc_datasheet_2206010116_UNI-ROYAL-Uniroyal-Elec-0603WAF3300T5E_C23138.pdf")
        (field (name "Description") "100mW Thick Film Resistors 75V ±100ppm/°C ±1% 330Ω 0603 Chip Resistor - Surface Mount ROHS"))
      (libsource (lib "PCM_JLCPCB-Resistors") (part "0603,330Ω") (description "100mW Thick Film Resistors 75V ±100ppm/°C ±1% 330Ω 0603 Chip Resistor - Surface Mount ROHS"))
      (property (name "LCSC") (value "C23138"))
      (property (name "Peak Wavelength") (value ""))
      (property (name "Stock") (value "2977706"))
      (property (name "Price") (value "0.004USD"))
      (property (name "Process") (value "SMT"))
      (property (name "Minimum Qty") (value "20"))
      (property (name "Attrition Qty") (value "10"))
      (property (name "Class") (value "Basic Component"))
      (property (name "Category") (value "Resistors,Chip Resistor - Surface Mount"))
      (property (name "Manufacturer") (value "UNI-ROYAL(Uniroyal Elec)"))
      (property (name "Part") (value "0603WAF3300T5E"))
      (property (name "Resistance") (value "330Ω"))
      (property (name "Power(Watts)") (value "100mW"))
      (property (name "Type") (value "Thick Film Resistors"))
      (property (name "Overload Voltage (Max)") (value "75V"))
      (property (name "Operating Temperature Range") (value "-55°C~+155°C"))
      (property (name "Tolerance") (value "±1%"))
      (property (name "Temperature Coefficient") (value "±100ppm/°C"))
      (property (name "Sheetname") (value "Root"))
      (property (name "Sheetfile") (value "Pico_Development_Stack.kicad_sch"))
      (property (name "ki_fp_filters") (value "R_*"))
      (sheetpath (names "/") (tstamps "/"))
      (tstamps "3c360c97-6606-4a94-851c-cc2dba280b90"))
    (comp (ref "R16")
      (value "330")
      (footprint "PCM_JLCPCB:R_0603")
      (datasheet "https://www.lcsc.com/datasheet/lcsc_datasheet_2206010116_UNI-ROYAL-Uniroyal-Elec-0603WAF3300T5E_C23138.pdf")
      (description "100mW Thick Film Resistors 75V ±100ppm/°C ±1% 330Ω 0603 Chip Resistor - Surface Mount ROHS")
      (fields
        (field (name "LCSC") "C23138")
        (field (name "Peak Wavelength"))
        (field (name "Stock") "2977706")
        (field (name "Price") "0.004USD")
        (field (name "Process") "SMT")
        (field (name "Minimum Qty") "20")
        (field (name "Attrition Qty") "10")
        (field (name "Class") "Basic Component")
        (field (name "Category") "Resistors,Chip Resistor - Surface Mount")
        (field (name "Manufacturer") "UNI-ROYAL(Uniroyal Elec)")
        (field (name "Part") "0603WAF3300T5E")
        (field (name "Resistance") "330Ω")
        (field (name "Power(Watts)") "100mW")
        (field (name "Type") "Thick Film Resistors")
        (field (name "Overload Voltage (Max)") "75V")
        (field (name "Operating Temperature Range") "-55°C~+155°C")
        (field (name "Tolerance") "±1%")
        (field (name "Temperature Coefficient") "±100ppm/°C")
        (field (name "Footprint") "PCM_JLCPCB:R_0603")
        (field (name "Datasheet") "https://www.lcsc.com/datasheet/lcsc_datasheet_2206010116_UNI-ROYAL-Uniroyal-Elec-0603WAF3300T5E_C23138.pdf")
        (field (name "Description") "100mW Thick Film Resistors 75V ±100ppm/°C ±1% 330Ω 0603 Chip Resistor - Surface Mount ROHS"))
      (libsource (lib "PCM_JLCPCB-Resistors") (part "0603,330Ω") (description "100mW Thick Film Resistors 75V ±100ppm/°C ±1% 330Ω 0603 Chip Resistor - Surface Mount ROHS"))
      (property (name "LCSC") (value "C23138"))
      (property (name "Peak Wavelength") (value ""))
      (property (name "Stock") (value "2977706"))
      (property (name "Price") (value "0.004USD"))
      (property (name "Process") (value "SMT"))
      (property (name "Minimum Qty") (value "20"))
      (property (name "Attrition Qty") (value "10"))
      (property (name "Class") (value "Basic Component"))
      (property (name "Category") (value "Resistors,Chip Resistor - Surface Mount"))
      (property (name "Manufacturer") (value "UNI-ROYAL(Uniroyal Elec)"))
      (property (name "Part") (value "0603WAF3300T5E"))
      (property (name "Resistance") (value "330Ω"))
      (property (name "Power(Watts)") (value "100mW"))
      (property (name "Type") (value "Thick Film Resistors"))
      (property (name "Overload Voltage (Max)") (value "75V"))
      (property (name "Operating Temperature Range") (value "-55°C~+155°C"))
      (property (name "Tolerance") (value "±1%"))
      (property (name "Temperature Coefficient") (value "±100ppm/°C"))
      (property (name "Sheetname") (value "Root"))
      (property (name "Sheetfile") (value "Pico_Development_Stack.kicad_sch"))
      (property (name "ki_fp_filters") (value "R_*"))
      (sheetpath (names "/") (tstamps "/"))
      (tstamps "fb841d4b-0db2-45b1-a318-172088f26ed5"))
    (comp (ref "R17")
      (value "330")
      (footprint "PCM_JLCPCB:R_0603")
      (datasheet "https://www.lcsc.com/datasheet/lcsc_datasheet_2206010116_UNI-ROYAL-Uniroyal-Elec-0603WAF3300T5E_C23138.pdf")
      (description "100mW Thick Film Resistors 75V ±100ppm/°C ±1% 330Ω 0603 Chip Resistor - Surface Mount ROHS")
      (fields
        (field (name "LCSC") "C23138")
        (field (name "Peak Wavelength"))
        (field (name "Stock") "2977706")
        (field (name "Price") "0.004USD")
        (field (name "Process") "SMT")
        (field (name "Minimum Qty") "20")
        (field (name "Attrition Qty") "10")
        (field (name "Class") "Basic Component")
        (field (name "Category") "Resistors,Chip Resistor - Surface Mount")
        (field (name "Manufacturer") "UNI-ROYAL(Uniroyal Elec)")
        (field (name "Part") "0603WAF3300T5E")
        (field (name "Resistance") "330Ω")
        (field (name "Power(Watts)") "100mW")
        (field (name "Type") "Thick Film Resistors")
        (field (name "Overload Voltage (Max)") "75V")
        (field (name "Operating Temperature Range") "-55°C~+155°C")
        (field (name "Tolerance") "±1%")
        (field (name "Temperature Coefficient") "±100ppm/°C")
        (field (name "Footprint") "PCM_JLCPCB:R_0603")
        (field (name "Datasheet") "https://www.lcsc.com/datasheet/lcsc_datasheet_2206010116_UNI-ROYAL-Uniroyal-Elec-0603WAF3300T5E_C23138.pdf")
        (field (name "Description") "100mW Thick Film Resistors 75V ±100ppm/°C ±1% 330Ω 0603 Chip Resistor - Surface Mount ROHS"))
      (libsource (lib "PCM_JLCPCB-Resistors") (part "0603,330Ω") (description "100mW Thick Film Resistors 75V ±100ppm/°C ±1% 330Ω 0603 Chip Resistor - Surface Mount ROHS"))
      (property (name "LCSC") (value "C23138"))
      (property (name "Peak Wavelength") (value ""))
      (property (name "Stock") (value "2977706"))
      (property (name "Price") (value "0.004USD"))
      (property (name "Process") (value "SMT"))
      (property (name "Minimum Qty") (value "20"))
      (property (name "Attrition Qty") (value "10"))
      (property (name "Class") (value "Basic Component"))
      (property (name "Category") (value "Resistors,Chip Resistor - Surface Mount"))
      (property (name "Manufacturer") (value "UNI-ROYAL(Uniroyal Elec)"))
      (property (name "Part") (value "0603WAF3300T5E"))
      (property (name "Resistance") (value "330Ω"))
      (property (name "Power(Watts)") (value "100mW"))
      (property (name "Type") (value "Thick Film Resistors"))
      (property (name "Overload Voltage (Max)") (value "75V"))
      (property (name "Operating Temperature Range") (value "-55°C~+155°C"))
      (property (name "Tolerance") (value "±1%"))
      (property (name "Temperature Coefficient") (value "±100ppm/°C"))
      (property (name "Sheetname") (value "Root"))
      (property (name "Sheetfile") (value "Pico_Development_Stack.kicad_sch"))
      (property (name "ki_fp_filters") (value "R_*"))
      (sheetpath (names "/") (tstamps "/"))
      (tstamps "8bc14635-9f75-4a83-b277-9a122cb503e0"))
    (comp (ref "R18")
      (value "330")
      (footprint "PCM_JLCPCB:R_0603")
      (datasheet "https://www.lcsc.com/datasheet/lcsc_datasheet_2206010116_UNI-ROYAL-Uniroyal-Elec-0603WAF3300T5E_C23138.pdf")
      (description "100mW Thick Film Resistors 75V ±100ppm/°C ±1% 330Ω 0603 Chip Resistor - Surface Mount ROHS")
      (fields
        (field (name "LCSC") "C23138")
        (field (name "Peak Wavelength"))
        (field (name "Stock") "2977706")
        (field (name "Price") "0.004USD")
        (field (name "Process") "SMT")
        (field (name "Minimum Qty") "20")
        (field (name "Attrition Qty") "10")
        (field (name "Class") "Basic Component")
        (field (name "Category") "Resistors,Chip Resistor - Surface Mount")
        (field (name "Manufacturer") "UNI-ROYAL(Uniroyal Elec)")
        (field (name "Part") "0603WAF3300T5E")
        (field (name "Resistance") "330Ω")
        (field (name "Power(Watts)") "100mW")
        (field (name "Type") "Thick Film Resistors")
        (field (name "Overload Voltage (Max)") "75V")
        (field (name "Operating Temperature Range") "-55°C~+155°C")
        (field (name "Tolerance") "±1%")
        (field (name "Temperature Coefficient") "±100ppm/°C")
        (field (name "Footprint") "PCM_JLCPCB:R_0603")
        (field (name "Datasheet") "https://www.lcsc.com/datasheet/lcsc_datasheet_2206010116_UNI-ROYAL-Uniroyal-Elec-0603WAF3300T5E_C23138.pdf")
        (field (name "Description") "100mW Thick Film Resistors 75V ±100ppm/°C ±1% 330Ω 0603 Chip Resistor - Surface Mount ROHS"))
      (libsource (lib "PCM_JLCPCB-Resistors") (part "0603,330Ω") (description "100mW Thick Film Resistors 75V ±100ppm/°C ±1% 330Ω 0603 Chip Resistor - Surface Mount ROHS"))
      (property (name "LCSC") (value "C23138"))
      (property (name "Peak Wavelength") (value ""))
      (property (name "Stock") (value "2977706"))
      (property (name "Price") (value "0.004USD"))
      (property (name "Process") (value "SMT"))
      (property (name "Minimum Qty") (value "20"))
      (property (name "Attrition Qty") (value "10"))
      (property (name "Class") (value "Basic Component"))
      (property (name "Category") (value "Resistors,Chip Resistor - Surface Mount"))
      (property (name "Manufacturer") (value "UNI-ROYAL(Uniroyal Elec)"))
      (property (name "Part") (value "0603WAF3300T5E"))
      (property (name "Resistance") (value "330Ω"))
      (property (name "Power(Watts)") (value "100mW"))
      (property (name "Type") (value "Thick Film Resistors"))
      (property (name "Overload Voltage (Max)") (value "75V"))
      (property (name "Operating Temperature Range") (value "-55°C~+155°C"))
      (property (name "Tolerance") (value "±1%"))
      (property (name "Temperature Coefficient") (value "±100ppm/°C"))
      (property (name "Sheetname") (value "Root"))
      (property (name "Sheetfile") (value "Pico_Development_Stack.kicad_sch"))
      (property (name "ki_fp_filters") (value "R_*"))
      (sheetpath (names "/") (tstamps "/"))
      (tstamps "bb15fddf-5ac0-4fe7-97a9-fd5037d46e18"))
    (comp (ref "R19")
      (value "330")
      (footprint "PCM_JLCPCB:R_0603")
      (datasheet "https://www.lcsc.com/datasheet/lcsc_datasheet_2206010116_UNI-ROYAL-Uniroyal-Elec-0603WAF3300T5E_C23138.pdf")
      (description "100mW Thick Film Resistors 75V ±100ppm/°C ±1% 330Ω 0603 Chip Resistor - Surface Mount ROHS")
      (fields
        (field (name "LCSC") "C23138")
        (field (name "Peak Wavelength"))
        (field (name "Stock") "2977706")
        (field (name "Price") "0.004USD")
        (field (name "Process") "SMT")
        (field (name "Minimum Qty") "20")
        (field (name "Attrition Qty") "10")
        (field (name "Class") "Basic Component")
        (field (name "Category") "Resistors,Chip Resistor - Surface Mount")
        (field (name "Manufacturer") "UNI-ROYAL(Uniroyal Elec)")
        (field (name "Part") "0603WAF3300T5E")
        (field (name "Resistance") "330Ω")
        (field (name "Power(Watts)") "100mW")
        (field (name "Type") "Thick Film Resistors")
        (field (name "Overload Voltage (Max)") "75V")
        (field (name "Operating Temperature Range") "-55°C~+155°C")
        (field (name "Tolerance") "±1%")
        (field (name "Temperature Coefficient") "±100ppm/°C")
        (field (name "Footprint") "PCM_JLCPCB:R_0603")
        (field (name "Datasheet") "https://www.lcsc.com/datasheet/lcsc_datasheet_2206010116_UNI-ROYAL-Uniroyal-Elec-0603WAF3300T5E_C23138.pdf")
        (field (name "Description") "100mW Thick Film Resistors 75V ±100ppm/°C ±1% 330Ω 0603 Chip Resistor - Surface Mount ROHS"))
      (libsource (lib "PCM_JLCPCB-Resistors") (part "0603,330Ω") (description "100mW Thick Film Resistors 75V ±100ppm/°C ±1% 330Ω 0603 Chip Resistor - Surface Mount ROHS"))
      (property (name "LCSC") (value "C23138"))
      (property (name "Peak Wavelength") (value ""))
      (property (name "Stock") (value "2977706"))
      (property (name "Price") (value "0.004USD"))
      (property (name "Process") (value "SMT"))
      (property (name "Minimum Qty") (value "20"))
      (property (name "Attrition Qty") (value "10"))
      (property (name "Class") (value "Basic Component"))
      (property (name "Category") (value "Resistors,Chip Resistor - Surface Mount"))
      (property (name "Manufacturer") (value "UNI-ROYAL(Uniroyal Elec)"))
      (property (name "Part") (value "0603WAF3300T5E"))
      (property (name "Resistance") (value "330Ω"))
      (property (name "Power(Watts)") (value "100mW"))
      (property (name "Type") (value "Thick Film Resistors"))
      (property (name "Overload Voltage (Max)") (value "75V"))
      (property (name "Operating Temperature Range") (value "-55°C~+155°C"))
      (property (name "Tolerance") (value "±1%"))
      (property (name "Temperature Coefficient") (value "±100ppm/°C"))
      (property (name "Sheetname") (value "Root"))
      (property (name "Sheetfile") (value "Pico_Development_Stack.kicad_sch"))
      (property (name "ki_fp_filters") (value "R_*"))
      (sheetpath (names "/") (tstamps "/"))
      (tstamps "31dac3f9-48f0-47d2-8a24-4f5fc3c096cb"))
    (comp (ref "R20")
      (value "330")
      (footprint "PCM_JLCPCB:R_0603")
      (datasheet "https://www.lcsc.com/datasheet/lcsc_datasheet_2206010116_UNI-ROYAL-Uniroyal-Elec-0603WAF3300T5E_C23138.pdf")
      (description "100mW Thick Film Resistors 75V ±100ppm/°C ±1% 330Ω 0603 Chip Resistor - Surface Mount ROHS")
      (fields
        (field (name "LCSC") "C23138")
        (field (name "Peak Wavelength"))
        (field (name "Stock") "2977706")
        (field (name "Price") "0.004USD")
        (field (name "Process") "SMT")
        (field (name "Minimum Qty") "20")
        (field (name "Attrition Qty") "10")
        (field (name "Class") "Basic Component")
        (field (name "Category") "Resistors,Chip Resistor - Surface Mount")
        (field (name "Manufacturer") "UNI-ROYAL(Uniroyal Elec)")
        (field (name "Part") "0603WAF3300T5E")
        (field (name "Resistance") "330Ω")
        (field (name "Power(Watts)") "100mW")
        (field (name "Type") "Thick Film Resistors")
        (field (name "Overload Voltage (Max)") "75V")
        (field (name "Operating Temperature Range") "-55°C~+155°C")
        (field (name "Tolerance") "±1%")
        (field (name "Temperature Coefficient") "±100ppm/°C")
        (field (name "Footprint") "PCM_JLCPCB:R_0603")
        (field (name "Datasheet") "https://www.lcsc.com/datasheet/lcsc_datasheet_2206010116_UNI-ROYAL-Uniroyal-Elec-0603WAF3300T5E_C23138.pdf")
        (field (name "Description") "100mW Thick Film Resistors 75V ±100ppm/°C ±1% 330Ω 0603 Chip Resistor - Surface Mount ROHS"))
      (libsource (lib "PCM_JLCPCB-Resistors") (part "0603,330Ω") (description "100mW Thick Film Resistors 75V ±100ppm/°C ±1% 330Ω 0603 Chip Resistor - Surface Mount ROHS"))
      (property (name "LCSC") (value "C23138"))
      (property (name "Peak Wavelength") (value ""))
      (property (name "Stock") (value "2977706"))
      (property (name "Price") (value "0.004USD"))
      (property (name "Process") (value "SMT"))
      (property (name "Minimum Qty") (value "20"))
      (property (name "Attrition Qty") (value "10"))
      (property (name "Class") (value "Basic Component"))
      (property (name "Category") (value "Resistors,Chip Resistor - Surface Mount"))
      (property (name "Manufacturer") (value "UNI-ROYAL(Uniroyal Elec)"))
      (property (name "Part") (value "0603WAF3300T5E"))
      (property (name "Resistance") (value "330Ω"))
      (property (name "Power(Watts)") (value "100mW"))
      (property (name "Type") (value "Thick Film Resistors"))
      (property (name "Overload Voltage (Max)") (value "75V"))
      (property (name "Operating Temperature Range") (value "-55°C~+155°C"))
      (property (name "Tolerance") (value "±1%"))
      (property (name "Temperature Coefficient") (value "±100ppm/°C"))
      (property (name "Sheetname") (value "Root"))
      (property (name "Sheetfile") (value "Pico_Development_Stack.kicad_sch"))
      (property (name "ki_fp_filters") (value "R_*"))
      (sheetpath (names "/") (tstamps "/"))
      (tstamps "81c550c9-66e1-4b09-8dcd-7fe2c432f83f"))
    (comp (ref "R21")
      (value "1kΩ")
      (footprint "PCM_JLCPCB:R_0603")
      (datasheet "https://www.lcsc.com/datasheet/lcsc_datasheet_2206010130_UNI-ROYAL-Uniroyal-Elec-0603WAF1001T5E_C21190.pdf")
      (description "100mW Thick Film Resistors 75V ±100ppm/°C ±1% 1kΩ 0603 Chip Resistor - Surface Mount ROHS")
      (fields
        (field (name "LCSC") "C21190")
        (field (name "Stock") "27538425")
        (field (name "Price") "0.004USD")
        (field (name "Process") "SMT")
        (field (name "Minimum Qty") "20")
        (field (name "Attrition Qty") "10")
        (field (name "Class") "Basic Component")
        (field (name "Category") "Resistors,Chip Resistor - Surface Mount")
        (field (name "Manufacturer") "UNI-ROYAL(Uniroyal Elec)")
        (field (name "Part") "0603WAF1001T5E")
        (field (name "Resistance") "1kΩ")
        (field (name "Power(Watts)") "100mW")
        (field (name "Type") "Thick Film Resistors")
        (field (name "Overload Voltage (Max)") "75V")
        (field (name "Operating Temperature Range") "-55°C~+155°C")
        (field (name "Tolerance") "±1%")
        (field (name "Temperature Coefficient") "±100ppm/°C")
        (field (name "Footprint") "PCM_JLCPCB:R_0603")
        (field (name "Datasheet") "https://www.lcsc.com/datasheet/lcsc_datasheet_2206010130_UNI-ROYAL-Uniroyal-Elec-0603WAF1001T5E_C21190.pdf")
        (field (name "Description") "100mW Thick Film Resistors 75V ±100ppm/°C ±1% 1kΩ 0603 Chip Resistor - Surface Mount ROHS"))
      (libsource (lib "PCM_JLCPCB-Resistors") (part "0603,1kΩ") (description "100mW Thick Film Resistors 75V ±100ppm/°C ±1% 1kΩ 0603 Chip Resistor - Surface Mount ROHS"))
      (property (name "LCSC") (value "C21190"))
      (property (name "Stock") (value "27538425"))
      (property (name "Price") (value "0.004USD"))
      (property (name "Process") (value "SMT"))
      (property (name "Minimum Qty") (value "20"))
      (property (name "Attrition Qty") (value "10"))
      (property (name "Class") (value "Basic Component"))
      (property (name "Category") (value "Resistors,Chip Resistor - Surface Mount"))
      (property (name "Manufacturer") (value "UNI-ROYAL(Uniroyal Elec)"))
      (property (name "Part") (value "0603WAF1001T5E"))
      (property (name "Resistance") (value "1kΩ"))
      (property (name "Power(Watts)") (value "100mW"))
      (property (name "Type") (value "Thick Film Resistors"))
      (property (name "Overload Voltage (Max)") (value "75V"))
      (property (name "Operating Temperature Range") (value "-55°C~+155°C"))
      (property (name "Tolerance") (value "±1%"))
      (property (name "Temperature Coefficient") (value "±100ppm/°C"))
      (property (name "Sheetname") (value "Root"))
      (property (name "Sheetfile") (value "Pico_Development_Stack.kicad_sch"))
      (property (name "ki_fp_filters") (value "R_*"))
      (sheetpath (names "/") (tstamps "/"))
      (tstamps "5145a272-beae-4b6b-a77d-ef8591ea34d5"))
    (comp (ref "R22")
      (value "330")
      (footprint "PCM_JLCPCB:R_0603")
      (datasheet "https://www.lcsc.com/datasheet/lcsc_datasheet_2206010116_UNI-ROYAL-Uniroyal-Elec-0603WAF3300T5E_C23138.pdf")
      (description "100mW Thick Film Resistors 75V ±100ppm/°C ±1% 330Ω 0603 Chip Resistor - Surface Mount ROHS")
      (fields
        (field (name "LCSC") "C23138")
        (field (name "Peak Wavelength"))
        (field (name "Stock") "2977706")
        (field (name "Price") "0.004USD")
        (field (name "Process") "SMT")
        (field (name "Minimum Qty") "20")
        (field (name "Attrition Qty") "10")
        (field (name "Class") "Basic Component")
        (field (name "Category") "Resistors,Chip Resistor - Surface Mount")
        (field (name "Manufacturer") "UNI-ROYAL(Uniroyal Elec)")
        (field (name "Part") "0603WAF3300T5E")
        (field (name "Resistance") "330Ω")
        (field (name "Power(Watts)") "100mW")
        (field (name "Type") "Thick Film Resistors")
        (field (name "Overload Voltage (Max)") "75V")
        (field (name "Operating Temperature Range") "-55°C~+155°C")
        (field (name "Tolerance") "±1%")
        (field (name "Temperature Coefficient") "±100ppm/°C")
        (field (name "Footprint") "PCM_JLCPCB:R_0603")
        (field (name "Datasheet") "https://www.lcsc.com/datasheet/lcsc_datasheet_2206010116_UNI-ROYAL-Uniroyal-Elec-0603WAF3300T5E_C23138.pdf")
        (field (name "Description") "100mW Thick Film Resistors 75V ±100ppm/°C ±1% 330Ω 0603 Chip Resistor - Surface Mount ROHS"))
      (libsource (lib "PCM_JLCPCB-Resistors") (part "0603,330Ω") (description "100mW Thick Film Resistors 75V ±100ppm/°C ±1% 330Ω 0603 Chip Resistor - Surface Mount ROHS"))
      (property (name "LCSC") (value "C23138"))
      (property (name "Peak Wavelength") (value ""))
      (property (name "Stock") (value "2977706"))
      (property (name "Price") (value "0.004USD"))
      (property (name "Process") (value "SMT"))
      (property (name "Minimum Qty") (value "20"))
      (property (name "Attrition Qty") (value "10"))
      (property (name "Class") (value "Basic Component"))
      (property (name "Category") (value "Resistors,Chip Resistor - Surface Mount"))
      (property (name "Manufacturer") (value "UNI-ROYAL(Uniroyal Elec)"))
      (property (name "Part") (value "0603WAF3300T5E"))
      (property (name "Resistance") (value "330Ω"))
      (property (name "Power(Watts)") (value "100mW"))
      (property (name "Type") (value "Thick Film Resistors"))
      (property (name "Overload Voltage (Max)") (value "75V"))
      (property (name "Operating Temperature Range") (value "-55°C~+155°C"))
      (property (name "Tolerance") (value "±1%"))
      (property (name "Temperature Coefficient") (value "±100ppm/°C"))
      (property (name "Sheetname") (value "Root"))
      (property (name "Sheetfile") (value "Pico_Development_Stack.kicad_sch"))
      (property (name "ki_fp_filters") (value "R_*"))
      (sheetpath (names "/") (tstamps "/"))
      (tstamps "54c27995-da3e-43f7-8488-dbc9f1456f6a"))
    (comp (ref "R23")
      (value "330")
      (footprint "PCM_JLCPCB:R_0603")
      (datasheet "https://www.lcsc.com/datasheet/lcsc_datasheet_2206010116_UNI-ROYAL-Uniroyal-Elec-0603WAF3300T5E_C23138.pdf")
      (description "100mW Thick Film Resistors 75V ±100ppm/°C ±1% 330Ω 0603 Chip Resistor - Surface Mount ROHS")
      (fields
        (field (name "LCSC") "C23138")
        (field (name "Peak Wavelength"))
        (field (name "Stock") "2977706")
        (field (name "Price") "0.004USD")
        (field (name "Process") "SMT")
        (field (name "Minimum Qty") "20")
        (field (name "Attrition Qty") "10")
        (field (name "Class") "Basic Component")
        (field (name "Category") "Resistors,Chip Resistor - Surface Mount")
        (field (name "Manufacturer") "UNI-ROYAL(Uniroyal Elec)")
        (field (name "Part") "0603WAF3300T5E")
        (field (name "Resistance") "330Ω")
        (field (name "Power(Watts)") "100mW")
        (field (name "Type") "Thick Film Resistors")
        (field (name "Overload Voltage (Max)") "75V")
        (field (name "Operating Temperature Range") "-55°C~+155°C")
        (field (name "Tolerance") "±1%")
        (field (name "Temperature Coefficient") "±100ppm/°C")
        (field (name "Footprint") "PCM_JLCPCB:R_0603")
        (field (name "Datasheet") "https://www.lcsc.com/datasheet/lcsc_datasheet_2206010116_UNI-ROYAL-Uniroyal-Elec-0603WAF3300T5E_C23138.pdf")
        (field (name "Description") "100mW Thick Film Resistors 75V ±100ppm/°C ±1% 330Ω 0603 Chip Resistor - Surface Mount ROHS"))
      (libsource (lib "PCM_JLCPCB-Resistors") (part "0603,330Ω") (description "100mW Thick Film Resistors 75V ±100ppm/°C ±1% 330Ω 0603 Chip Resistor - Surface Mount ROHS"))
      (property (name "LCSC") (value "C23138"))
      (property (name "Peak Wavelength") (value ""))
      (property (name "Stock") (value "2977706"))
      (property (name "Price") (value "0.004USD"))
      (property (name "Process") (value "SMT"))
      (property (name "Minimum Qty") (value "20"))
      (property (name "Attrition Qty") (value "10"))
      (property (name "Class") (value "Basic Component"))
      (property (name "Category") (value "Resistors,Chip Resistor - Surface Mount"))
      (property (name "Manufacturer") (value "UNI-ROYAL(Uniroyal Elec)"))
      (property (name "Part") (value "0603WAF3300T5E"))
      (property (name "Resistance") (value "330Ω"))
      (property (name "Power(Watts)") (value "100mW"))
      (property (name "Type") (value "Thick Film Resistors"))
      (property (name "Overload Voltage (Max)") (value "75V"))
      (property (name "Operating Temperature Range") (value "-55°C~+155°C"))
      (property (name "Tolerance") (value "±1%"))
      (property (name "Temperature Coefficient") (value "±100ppm/°C"))
      (property (name "Sheetname") (value "Root"))
      (property (name "Sheetfile") (value "Pico_Development_Stack.kicad_sch"))
      (property (name "ki_fp_filters") (value "R_*"))
      (sheetpath (names "/") (tstamps "/"))
      (tstamps "a0a4503e-35e5-4691-9b2c-7a033cae756d"))
    (comp (ref "R24")
      (value "330")
      (footprint "PCM_JLCPCB:R_0603")
      (datasheet "https://www.lcsc.com/datasheet/lcsc_datasheet_2206010116_UNI-ROYAL-Uniroyal-Elec-0603WAF3300T5E_C23138.pdf")
      (description "100mW Thick Film Resistors 75V ±100ppm/°C ±1% 330Ω 0603 Chip Resistor - Surface Mount ROHS")
      (fields
        (field (name "LCSC") "C23138")
        (field (name "Peak Wavelength"))
        (field (name "Stock") "2977706")
        (field (name "Price") "0.004USD")
        (field (name "Process") "SMT")
        (field (name "Minimum Qty") "20")
        (field (name "Attrition Qty") "10")
        (field (name "Class") "Basic Component")
        (field (name "Category") "Resistors,Chip Resistor - Surface Mount")
        (field (name "Manufacturer") "UNI-ROYAL(Uniroyal Elec)")
        (field (name "Part") "0603WAF3300T5E")
        (field (name "Resistance") "330Ω")
        (field (name "Power(Watts)") "100mW")
        (field (name "Type") "Thick Film Resistors")
        (field (name "Overload Voltage (Max)") "75V")
        (field (name "Operating Temperature Range") "-55°C~+155°C")
        (field (name "Tolerance") "±1%")
        (field (name "Temperature Coefficient") "±100ppm/°C")
        (field (name "Footprint") "PCM_JLCPCB:R_0603")
        (field (name "Datasheet") "https://www.lcsc.com/datasheet/lcsc_datasheet_2206010116_UNI-ROYAL-Uniroyal-Elec-0603WAF3300T5E_C23138.pdf")
        (field (name "Description") "100mW Thick Film Resistors 75V ±100ppm/°C ±1% 330Ω 0603 Chip Resistor - Surface Mount ROHS"))
      (libsource (lib "PCM_JLCPCB-Resistors") (part "0603,330Ω") (description "100mW Thick Film Resistors 75V ±100ppm/°C ±1% 330Ω 0603 Chip Resistor - Surface Mount ROHS"))
      (property (name "LCSC") (value "C23138"))
      (property (name "Peak Wavelength") (value ""))
      (property (name "Stock") (value "2977706"))
      (property (name "Price") (value "0.004USD"))
      (property (name "Process") (value "SMT"))
      (property (name "Minimum Qty") (value "20"))
      (property (name "Attrition Qty") (value "10"))
      (property (name "Class") (value "Basic Component"))
      (property (name "Category") (value "Resistors,Chip Resistor - Surface Mount"))
      (property (name "Manufacturer") (value "UNI-ROYAL(Uniroyal Elec)"))
      (property (name "Part") (value "0603WAF3300T5E"))
      (property (name "Resistance") (value "330Ω"))
      (property (name "Power(Watts)") (value "100mW"))
      (property (name "Type") (value "Thick Film Resistors"))
      (property (name "Overload Voltage (Max)") (value "75V"))
      (property (name "Operating Temperature Range") (value "-55°C~+155°C"))
      (property (name "Tolerance") (value "±1%"))
      (property (name "Temperature Coefficient") (value "±100ppm/°C"))
      (property (name "Sheetname") (value "Root"))
      (property (name "Sheetfile") (value "Pico_Development_Stack.kicad_sch"))
      (property (name "ki_fp_filters") (value "R_*"))
      (sheetpath (names "/") (tstamps "/"))
      (tstamps "d8089d51-43bd-41fa-9466-72b43c0e250e"))
    (comp (ref "R25")
      (value "330")
      (footprint "PCM_JLCPCB:R_0603")
      (datasheet "https://www.lcsc.com/datasheet/lcsc_datasheet_2206010116_UNI-ROYAL-Uniroyal-Elec-0603WAF3300T5E_C23138.pdf")
      (description "100mW Thick Film Resistors 75V ±100ppm/°C ±1% 330Ω 0603 Chip Resistor - Surface Mount ROHS")
      (fields
        (field (name "LCSC") "C23138")
        (field (name "Peak Wavelength"))
        (field (name "Stock") "2977706")
        (field (name "Price") "0.004USD")
        (field (name "Process") "SMT")
        (field (name "Minimum Qty") "20")
        (field (name "Attrition Qty") "10")
        (field (name "Class") "Basic Component")
        (field (name "Category") "Resistors,Chip Resistor - Surface Mount")
        (field (name "Manufacturer") "UNI-ROYAL(Uniroyal Elec)")
        (field (name "Part") "0603WAF3300T5E")
        (field (name "Resistance") "330Ω")
        (field (name "Power(Watts)") "100mW")
        (field (name "Type") "Thick Film Resistors")
        (field (name "Overload Voltage (Max)") "75V")
        (field (name "Operating Temperature Range") "-55°C~+155°C")
        (field (name "Tolerance") "±1%")
        (field (name "Temperature Coefficient") "±100ppm/°C")
        (field (name "Footprint") "PCM_JLCPCB:R_0603")
        (field (name "Datasheet") "https://www.lcsc.com/datasheet/lcsc_datasheet_2206010116_UNI-ROYAL-Uniroyal-Elec-0603WAF3300T5E_C23138.pdf")
        (field (name "Description") "100mW Thick Film Resistors 75V ±100ppm/°C ±1% 330Ω 0603 Chip Resistor - Surface Mount ROHS"))
      (libsource (lib "PCM_JLCPCB-Resistors") (part "0603,330Ω") (description "100mW Thick Film Resistors 75V ±100ppm/°C ±1% 330Ω 0603 Chip Resistor - Surface Mount ROHS"))
      (property (name "LCSC") (value "C23138"))
      (property (name "Peak Wavelength") (value ""))
      (property (name "Stock") (value "2977706"))
      (property (name "Price") (value "0.004USD"))
      (property (name "Process") (value "SMT"))
      (property (name "Minimum Qty") (value "20"))
      (property (name "Attrition Qty") (value "10"))
      (property (name "Class") (value "Basic Component"))
      (property (name "Category") (value "Resistors,Chip Resistor - Surface Mount"))
      (property (name "Manufacturer") (value "UNI-ROYAL(Uniroyal Elec)"))
      (property (name "Part") (value "0603WAF3300T5E"))
      (property (name "Resistance") (value "330Ω"))
      (property (name "Power(Watts)") (value "100mW"))
      (property (name "Type") (value "Thick Film Resistors"))
      (property (name "Overload Voltage (Max)") (value "75V"))
      (property (name "Operating Temperature Range") (value "-55°C~+155°C"))
      (property (name "Tolerance") (value "±1%"))
      (property (name "Temperature Coefficient") (value "±100ppm/°C"))
      (property (name "Sheetname") (value "Root"))
      (property (name "Sheetfile") (value "Pico_Development_Stack.kicad_sch"))
      (property (name "ki_fp_filters") (value "R_*"))
      (sheetpath (names "/") (tstamps "/"))
      (tstamps "8fbc5894-7f56-4bb3-aeec-eee26f0edae4"))
    (comp (ref "R26")
      (value "330")
      (footprint "PCM_JLCPCB:R_0603")
      (datasheet "https://www.lcsc.com/datasheet/lcsc_datasheet_2206010116_UNI-ROYAL-Uniroyal-Elec-0603WAF3300T5E_C23138.pdf")
      (description "100mW Thick Film Resistors 75V ±100ppm/°C ±1% 330Ω 0603 Chip Resistor - Surface Mount ROHS")
      (fields
        (field (name "LCSC") "C23138")
        (field (name "Peak Wavelength"))
        (field (name "Stock") "2977706")
        (field (name "Price") "0.004USD")
        (field (name "Process") "SMT")
        (field (name "Minimum Qty") "20")
        (field (name "Attrition Qty") "10")
        (field (name "Class") "Basic Component")
        (field (name "Category") "Resistors,Chip Resistor - Surface Mount")
        (field (name "Manufacturer") "UNI-ROYAL(Uniroyal Elec)")
        (field (name "Part") "0603WAF3300T5E")
        (field (name "Resistance") "330Ω")
        (field (name "Power(Watts)") "100mW")
        (field (name "Type") "Thick Film Resistors")
        (field (name "Overload Voltage (Max)") "75V")
        (field (name "Operating Temperature Range") "-55°C~+155°C")
        (field (name "Tolerance") "±1%")
        (field (name "Temperature Coefficient") "±100ppm/°C")
        (field (name "Footprint") "PCM_JLCPCB:R_0603")
        (field (name "Datasheet") "https://www.lcsc.com/datasheet/lcsc_datasheet_2206010116_UNI-ROYAL-Uniroyal-Elec-0603WAF3300T5E_C23138.pdf")
        (field (name "Description") "100mW Thick Film Resistors 75V ±100ppm/°C ±1% 330Ω 0603 Chip Resistor - Surface Mount ROHS"))
      (libsource (lib "PCM_JLCPCB-Resistors") (part "0603,330Ω") (description "100mW Thick Film Resistors 75V ±100ppm/°C ±1% 330Ω 0603 Chip Resistor - Surface Mount ROHS"))
      (property (name "LCSC") (value "C23138"))
      (property (name "Peak Wavelength") (value ""))
      (property (name "Stock") (value "2977706"))
      (property (name "Price") (value "0.004USD"))
      (property (name "Process") (value "SMT"))
      (property (name "Minimum Qty") (value "20"))
      (property (name "Attrition Qty") (value "10"))
      (property (name "Class") (value "Basic Component"))
      (property (name "Category") (value "Resistors,Chip Resistor - Surface Mount"))
      (property (name "Manufacturer") (value "UNI-ROYAL(Uniroyal Elec)"))
      (property (name "Part") (value "0603WAF3300T5E"))
      (property (name "Resistance") (value "330Ω"))
      (property (name "Power(Watts)") (value "100mW"))
      (property (name "Type") (value "Thick Film Resistors"))
      (property (name "Overload Voltage (Max)") (value "75V"))
      (property (name "Operating Temperature Range") (value "-55°C~+155°C"))
      (property (name "Tolerance") (value "±1%"))
      (property (name "Temperature Coefficient") (value "±100ppm/°C"))
      (property (name "Sheetname") (value "Root"))
      (property (name "Sheetfile") (value "Pico_Development_Stack.kicad_sch"))
      (property (name "ki_fp_filters") (value "R_*"))
      (sheetpath (names "/") (tstamps "/"))
      (tstamps "65176850-673e-4be8-8c20-ac5a8cbee807"))
    (comp (ref "R27")
      (value "330")
      (footprint "PCM_JLCPCB:R_0603")
      (datasheet "https://www.lcsc.com/datasheet/lcsc_datasheet_2206010116_UNI-ROYAL-Uniroyal-Elec-0603WAF3300T5E_C23138.pdf")
      (description "100mW Thick Film Resistors 75V ±100ppm/°C ±1% 330Ω 0603 Chip Resistor - Surface Mount ROHS")
      (fields
        (field (name "LCSC") "C23138")
        (field (name "Peak Wavelength"))
        (field (name "Stock") "2977706")
        (field (name "Price") "0.004USD")
        (field (name "Process") "SMT")
        (field (name "Minimum Qty") "20")
        (field (name "Attrition Qty") "10")
        (field (name "Class") "Basic Component")
        (field (name "Category") "Resistors,Chip Resistor - Surface Mount")
        (field (name "Manufacturer") "UNI-ROYAL(Uniroyal Elec)")
        (field (name "Part") "0603WAF3300T5E")
        (field (name "Resistance") "330Ω")
        (field (name "Power(Watts)") "100mW")
        (field (name "Type") "Thick Film Resistors")
        (field (name "Overload Voltage (Max)") "75V")
        (field (name "Operating Temperature Range") "-55°C~+155°C")
        (field (name "Tolerance") "±1%")
        (field (name "Temperature Coefficient") "±100ppm/°C")
        (field (name "Footprint") "PCM_JLCPCB:R_0603")
        (field (name "Datasheet") "https://www.lcsc.com/datasheet/lcsc_datasheet_2206010116_UNI-ROYAL-Uniroyal-Elec-0603WAF3300T5E_C23138.pdf")
        (field (name "Description") "100mW Thick Film Resistors 75V ±100ppm/°C ±1% 330Ω 0603 Chip Resistor - Surface Mount ROHS"))
      (libsource (lib "PCM_JLCPCB-Resistors") (part "0603,330Ω") (description "100mW Thick Film Resistors 75V ±100ppm/°C ±1% 330Ω 0603 Chip Resistor - Surface Mount ROHS"))
      (property (name "LCSC") (value "C23138"))
      (property (name "Peak Wavelength") (value ""))
      (property (name "Stock") (value "2977706"))
      (property (name "Price") (value "0.004USD"))
      (property (name "Process") (value "SMT"))
      (property (name "Minimum Qty") (value "20"))
      (property (name "Attrition Qty") (value "10"))
      (property (name "Class") (value "Basic Component"))
      (property (name "Category") (value "Resistors,Chip Resistor - Surface Mount"))
      (property (name "Manufacturer") (value "UNI-ROYAL(Uniroyal Elec)"))
      (property (name "Part") (value "0603WAF3300T5E"))
      (property (name "Resistance") (value "330Ω"))
      (property (name "Power(Watts)") (value "100mW"))
      (property (name "Type") (value "Thick Film Resistors"))
      (property (name "Overload Voltage (Max)") (value "75V"))
      (property (name "Operating Temperature Range") (value "-55°C~+155°C"))
      (property (name "Tolerance") (value "±1%"))
      (property (name "Temperature Coefficient") (value "±100ppm/°C"))
      (property (name "Sheetname") (value "Root"))
      (property (name "Sheetfile") (value "Pico_Development_Stack.kicad_sch"))
      (property (name "ki_fp_filters") (value "R_*"))
      (sheetpath (names "/") (tstamps "/"))
      (tstamps "52f7a2ac-e919-487b-a9bf-c95e128a51e7"))
    (comp (ref "R28")
      (value "10kΩ")
      (footprint "PCM_JLCPCB:R_0603")
      (datasheet "https://www.lcsc.com/datasheet/lcsc_datasheet_2206010045_UNI-ROYAL-Uniroyal-Elec-0603WAF1002T5E_C25804.pdf")
      (description "100mW Thick Film Resistors 75V ±100ppm/°C ±1% 10kΩ 0603 Chip Resistor - Surface Mount ROHS")
      (fields
        (field (name "LCSC") "C25804")
        (field (name "Stock") "51181774")
        (field (name "Price") "0.004USD")
        (field (name "Process") "SMT")
        (field (name "Minimum Qty") "20")
        (field (name "Attrition Qty") "10")
        (field (name "Class") "Basic Component")
        (field (name "Category") "Resistors,Chip Resistor - Surface Mount")
        (field (name "Manufacturer") "UNI-ROYAL(Uniroyal Elec)")
        (field (name "Part") "0603WAF1002T5E")
        (field (name "Resistance") "10kΩ")
        (field (name "Power(Watts)") "100mW")
        (field (name "Type") "Thick Film Resistors")
        (field (name "Overload Voltage (Max)") "75V")
        (field (name "Operating Temperature Range") "-55°C~+155°C")
        (field (name "Tolerance") "±1%")
        (field (name "Temperature Coefficient") "±100ppm/°C")
        (field (name "Footprint") "PCM_JLCPCB:R_0603")
        (field (name "Datasheet") "https://www.lcsc.com/datasheet/lcsc_datasheet_2206010045_UNI-ROYAL-Uniroyal-Elec-0603WAF1002T5E_C25804.pdf")
        (field (name "Description") "100mW Thick Film Resistors 75V ±100ppm/°C ±1% 10kΩ 0603 Chip Resistor - Surface Mount ROHS"))
      (libsource (lib "PCM_JLCPCB-Resistors") (part "0603,10kΩ") (description "100mW Thick Film Resistors 75V ±100ppm/°C ±1% 10kΩ 0603 Chip Resistor - Surface Mount ROHS"))
      (property (name "LCSC") (value "C25804"))
      (property (name "Stock") (value "51181774"))
      (property (name "Price") (value "0.004USD"))
      (property (name "Process") (value "SMT"))
      (property (name "Minimum Qty") (value "20"))
      (property (name "Attrition Qty") (value "10"))
      (property (name "Class") (value "Basic Component"))
      (property (name "Category") (value "Resistors,Chip Resistor - Surface Mount"))
      (property (name "Manufacturer") (value "UNI-ROYAL(Uniroyal Elec)"))
      (property (name "Part") (value "0603WAF1002T5E"))
      (property (name "Resistance") (value "10kΩ"))
      (property (name "Power(Watts)") (value "100mW"))
      (property (name "Type") (value "Thick Film Resistors"))
      (property (name "Overload Voltage (Max)") (value "75V"))
      (property (name "Operating Temperature Range") (value "-55°C~+155°C"))
      (property (name "Tolerance") (value "±1%"))
      (property (name "Temperature Coefficient") (value "±100ppm/°C"))
      (property (name "Sheetname") (value "Root"))
      (property (name "Sheetfile") (value "Pico_Development_Stack.kicad_sch"))
      (property (name "ki_fp_filters") (value "R_*"))
      (sheetpath (names "/") (tstamps "/"))
      (tstamps "462611b3-84d6-475c-98ee-21e12683f631"))
    (comp (ref "R29")
      (value "10kΩ")
      (footprint "PCM_JLCPCB:R_0603")
      (datasheet "https://www.lcsc.com/datasheet/lcsc_datasheet_2206010045_UNI-ROYAL-Uniroyal-Elec-0603WAF1002T5E_C25804.pdf")
      (description "100mW Thick Film Resistors 75V ±100ppm/°C ±1% 10kΩ 0603 Chip Resistor - Surface Mount ROHS")
      (fields
        (field (name "LCSC") "C25804")
        (field (name "Stock") "51181774")
        (field (name "Price") "0.004USD")
        (field (name "Process") "SMT")
        (field (name "Minimum Qty") "20")
        (field (name "Attrition Qty") "10")
        (field (name "Class") "Basic Component")
        (field (name "Category") "Resistors,Chip Resistor - Surface Mount")
        (field (name "Manufacturer") "UNI-ROYAL(Uniroyal Elec)")
        (field (name "Part") "0603WAF1002T5E")
        (field (name "Resistance") "10kΩ")
        (field (name "Power(Watts)") "100mW")
        (field (name "Type") "Thick Film Resistors")
        (field (name "Overload Voltage (Max)") "75V")
        (field (name "Operating Temperature Range") "-55°C~+155°C")
        (field (name "Tolerance") "±1%")
        (field (name "Temperature Coefficient") "±100ppm/°C")
        (field (name "Footprint") "PCM_JLCPCB:R_0603")
        (field (name "Datasheet") "https://www.lcsc.com/datasheet/lcsc_datasheet_2206010045_UNI-ROYAL-Uniroyal-Elec-0603WAF1002T5E_C25804.pdf")
        (field (name "Description") "100mW Thick Film Resistors 75V ±100ppm/°C ±1% 10kΩ 0603 Chip Resistor - Surface Mount ROHS"))
      (libsource (lib "PCM_JLCPCB-Resistors") (part "0603,10kΩ") (description "100mW Thick Film Resistors 75V ±100ppm/°C ±1% 10kΩ 0603 Chip Resistor - Surface Mount ROHS"))
      (property (name "LCSC") (value "C25804"))
      (property (name "Stock") (value "51181774"))
      (property (name "Price") (value "0.004USD"))
      (property (name "Process") (value "SMT"))
      (property (name "Minimum Qty") (value "20"))
      (property (name "Attrition Qty") (value "10"))
      (property (name "Class") (value "Basic Component"))
      (property (name "Category") (value "Resistors,Chip Resistor - Surface Mount"))
      (property (name "Manufacturer") (value "UNI-ROYAL(Uniroyal Elec)"))
      (property (name "Part") (value "0603WAF1002T5E"))
      (property (name "Resistance") (value "10kΩ"))
      (property (name "Power(Watts)") (value "100mW"))
      (property (name "Type") (value "Thick Film Resistors"))
      (property (name "Overload Voltage (Max)") (value "75V"))
      (property (name "Operating Temperature Range") (value "-55°C~+155°C"))
      (property (name "Tolerance") (value "±1%"))
      (property (name "Temperature Coefficient") (value "±100ppm/°C"))
      (property (name "Sheetname") (value "Root"))
      (property (name "Sheetfile") (value "Pico_Development_Stack.kicad_sch"))
      (property (name "ki_fp_filters") (value "R_*"))
      (sheetpath (names "/") (tstamps "/"))
      (tstamps "4a725092-d589-4e04-8a31-14d1dda0a7db"))
    (comp (ref "R30")
      (value "10kΩ")
      (footprint "PCM_JLCPCB:R_0603")
      (datasheet "https://www.lcsc.com/datasheet/lcsc_datasheet_2206010045_UNI-ROYAL-Uniroyal-Elec-0603WAF1002T5E_C25804.pdf")
      (description "100mW Thick Film Resistors 75V ±100ppm/°C ±1% 10kΩ 0603 Chip Resistor - Surface Mount ROHS")
      (fields
        (field (name "LCSC") "C25804")
        (field (name "Stock") "51181774")
        (field (name "Price") "0.004USD")
        (field (name "Process") "SMT")
        (field (name "Minimum Qty") "20")
        (field (name "Attrition Qty") "10")
        (field (name "Class") "Basic Component")
        (field (name "Category") "Resistors,Chip Resistor - Surface Mount")
        (field (name "Manufacturer") "UNI-ROYAL(Uniroyal Elec)")
        (field (name "Part") "0603WAF1002T5E")
        (field (name "Resistance") "10kΩ")
        (field (name "Power(Watts)") "100mW")
        (field (name "Type") "Thick Film Resistors")
        (field (name "Overload Voltage (Max)") "75V")
        (field (name "Operating Temperature Range") "-55°C~+155°C")
        (field (name "Tolerance") "±1%")
        (field (name "Temperature Coefficient") "±100ppm/°C")
        (field (name "Footprint") "PCM_JLCPCB:R_0603")
        (field (name "Datasheet") "https://www.lcsc.com/datasheet/lcsc_datasheet_2206010045_UNI-ROYAL-Uniroyal-Elec-0603WAF1002T5E_C25804.pdf")
        (field (name "Description") "100mW Thick Film Resistors 75V ±100ppm/°C ±1% 10kΩ 0603 Chip Resistor - Surface Mount ROHS"))
      (libsource (lib "PCM_JLCPCB-Resistors") (part "0603,10kΩ") (description "100mW Thick Film Resistors 75V ±100ppm/°C ±1% 10kΩ 0603 Chip Resistor - Surface Mount ROHS"))
      (property (name "LCSC") (value "C25804"))
      (property (name "Stock") (value "51181774"))
      (property (name "Price") (value "0.004USD"))
      (property (name "Process") (value "SMT"))
      (property (name "Minimum Qty") (value "20"))
      (property (name "Attrition Qty") (value "10"))
      (property (name "Class") (value "Basic Component"))
      (property (name "Category") (value "Resistors,Chip Resistor - Surface Mount"))
      (property (name "Manufacturer") (value "UNI-ROYAL(Uniroyal Elec)"))
      (property (name "Part") (value "0603WAF1002T5E"))
      (property (name "Resistance") (value "10kΩ"))
      (property (name "Power(Watts)") (value "100mW"))
      (property (name "Type") (value "Thick Film Resistors"))
      (property (name "Overload Voltage (Max)") (value "75V"))
      (property (name "Operating Temperature Range") (value "-55°C~+155°C"))
      (property (name "Tolerance") (value "±1%"))
      (property (name "Temperature Coefficient") (value "±100ppm/°C"))
      (property (name "Sheetname") (value "Root"))
      (property (name "Sheetfile") (value "Pico_Development_Stack.kicad_sch"))
      (property (name "ki_fp_filters") (value "R_*"))
      (sheetpath (names "/") (tstamps "/"))
      (tstamps "8c8ef416-3349-482a-80b9-99861fa1fed8"))
    (comp (ref "R31")
      (value "1kΩ")
      (footprint "PCM_JLCPCB:R_0603")
      (datasheet "https://www.lcsc.com/datasheet/lcsc_datasheet_2206010130_UNI-ROYAL-Uniroyal-Elec-0603WAF1001T5E_C21190.pdf")
      (description "100mW Thick Film Resistors 75V ±100ppm/°C ±1% 1kΩ 0603 Chip Resistor - Surface Mount ROHS")
      (fields
        (field (name "LCSC") "C21190")
        (field (name "Stock") "27538425")
        (field (name "Price") "0.004USD")
        (field (name "Process") "SMT")
        (field (name "Minimum Qty") "20")
        (field (name "Attrition Qty") "10")
        (field (name "Class") "Basic Component")
        (field (name "Category") "Resistors,Chip Resistor - Surface Mount")
        (field (name "Manufacturer") "UNI-ROYAL(Uniroyal Elec)")
        (field (name "Part") "0603WAF1001T5E")
        (field (name "Resistance") "1kΩ")
        (field (name "Power(Watts)") "100mW")
        (field (name "Type") "Thick Film Resistors")
        (field (name "Overload Voltage (Max)") "75V")
        (field (name "Operating Temperature Range") "-55°C~+155°C")
        (field (name "Tolerance") "±1%")
        (field (name "Temperature Coefficient") "±100ppm/°C")
        (field (name "Footprint") "PCM_JLCPCB:R_0603")
        (field (name "Datasheet") "https://www.lcsc.com/datasheet/lcsc_datasheet_2206010130_UNI-ROYAL-Uniroyal-Elec-0603WAF1001T5E_C21190.pdf")
        (field (name "Description") "100mW Thick Film Resistors 75V ±100ppm/°C ±1% 1kΩ 0603 Chip Resistor - Surface Mount ROHS"))
      (libsource (lib "PCM_JLCPCB-Resistors") (part "0603,1kΩ") (description "100mW Thick Film Resistors 75V ±100ppm/°C ±1% 1kΩ 0603 Chip Resistor - Surface Mount ROHS"))
      (property (name "LCSC") (value "C21190"))
      (property (name "Stock") (value "27538425"))
      (property (name "Price") (value "0.004USD"))
      (property (name "Process") (value "SMT"))
      (property (name "Minimum Qty") (value "20"))
      (property (name "Attrition Qty") (value "10"))
      (property (name "Class") (value "Basic Component"))
      (property (name "Category") (value "Resistors,Chip Resistor - Surface Mount"))
      (property (name "Manufacturer") (value "UNI-ROYAL(Uniroyal Elec)"))
      (property (name "Part") (value "0603WAF1001T5E"))
      (property (name "Resistance") (value "1kΩ"))
      (property (name "Power(Watts)") (value "100mW"))
      (property (name "Type") (value "Thick Film Resistors"))
      (property (name "Overload Voltage (Max)") (value "75V"))
      (property (name "Operating Temperature Range") (value "-55°C~+155°C"))
      (property (name "Tolerance") (value "±1%"))
      (property (name "Temperature Coefficient") (value "±100ppm/°C"))
      (property (name "Sheetname") (value "Root"))
      (property (name "Sheetfile") (value "Pico_Development_Stack.kicad_sch"))
      (property (name "ki_fp_filters") (value "R_*"))
      (sheetpath (names "/") (tstamps "/"))
      (tstamps "6b9fbf7d-0193-4145-99dd-2ffbea424020"))
    (comp (ref "R32")
      (value "10kΩ")
      (footprint "PCM_JLCPCB:R_0603")
      (datasheet "https://www.lcsc.com/datasheet/lcsc_datasheet_2206010045_UNI-ROYAL-Uniroyal-Elec-0603WAF1002T5E_C25804.pdf")
      (description "100mW Thick Film Resistors 75V ±100ppm/°C ±1% 10kΩ 0603 Chip Resistor - Surface Mount ROHS")
      (fields
        (field (name "LCSC") "C25804")
        (field (name "Stock") "51181774")
        (field (name "Price") "0.004USD")
        (field (name "Process") "SMT")
        (field (name "Minimum Qty") "20")
        (field (name "Attrition Qty") "10")
        (field (name "Class") "Basic Component")
        (field (name "Category") "Resistors,Chip Resistor - Surface Mount")
        (field (name "Manufacturer") "UNI-ROYAL(Uniroyal Elec)")
        (field (name "Part") "0603WAF1002T5E")
        (field (name "Resistance") "10kΩ")
        (field (name "Power(Watts)") "100mW")
        (field (name "Type") "Thick Film Resistors")
        (field (name "Overload Voltage (Max)") "75V")
        (field (name "Operating Temperature Range") "-55°C~+155°C")
        (field (name "Tolerance") "±1%")
        (field (name "Temperature Coefficient") "±100ppm/°C")
        (field (name "Footprint") "PCM_JLCPCB:R_0603")
        (field (name "Datasheet") "https://www.lcsc.com/datasheet/lcsc_datasheet_2206010045_UNI-ROYAL-Uniroyal-Elec-0603WAF1002T5E_C25804.pdf")
        (field (name "Description") "100mW Thick Film Resistors 75V ±100ppm/°C ±1% 10kΩ 0603 Chip Resistor - Surface Mount ROHS"))
      (libsource (lib "PCM_JLCPCB-Resistors") (part "0603,10kΩ") (description "100mW Thick Film Resistors 75V ±100ppm/°C ±1% 10kΩ 0603 Chip Resistor - Surface Mount ROHS"))
      (property (name "LCSC") (value "C25804"))
      (property (name "Stock") (value "51181774"))
      (property (name "Price") (value "0.004USD"))
      (property (name "Process") (value "SMT"))
      (property (name "Minimum Qty") (value "20"))
      (property (name "Attrition Qty") (value "10"))
      (property (name "Class") (value "Basic Component"))
      (property (name "Category") (value "Resistors,Chip Resistor - Surface Mount"))
      (property (name "Manufacturer") (value "UNI-ROYAL(Uniroyal Elec)"))
      (property (name "Part") (value "0603WAF1002T5E"))
      (property (name "Resistance") (value "10kΩ"))
      (property (name "Power(Watts)") (value "100mW"))
      (property (name "Type") (value "Thick Film Resistors"))
      (property (name "Overload Voltage (Max)") (value "75V"))
      (property (name "Operating Temperature Range") (value "-55°C~+155°C"))
      (property (name "Tolerance") (value "±1%"))
      (property (name "Temperature Coefficient") (value "±100ppm/°C"))
      (property (name "Sheetname") (value "Root"))
      (property (name "Sheetfile") (value "Pico_Development_Stack.kicad_sch"))
      (property (name "ki_fp_filters") (value "R_*"))
      (sheetpath (names "/") (tstamps "/"))
      (tstamps "a6730987-01f6-4f67-957d-aa35e1712e4f"))
    (comp (ref "R33")
      (value "5.1kΩ")
      (footprint "PCM_JLCPCB:R_0603")
      (datasheet "https://www.lcsc.com/datasheet/lcsc_datasheet_2206010116_UNI-ROYAL-Uniroyal-Elec-0603WAF5101T5E_C23186.pdf")
      (description "100mW Thick Film Resistors 75V ±100ppm/°C ±1% 5.1kΩ 0603 Chip Resistor - Surface Mount ROHS")
      (fields
        (field (name "LCSC") "C23186")
        (field (name "Stock") "9223405")
        (field (name "Price") "0.004USD")
        (field (name "Process") "SMT")
        (field (name "Minimum Qty") "20")
        (field (name "Attrition Qty") "10")
        (field (name "Class") "Basic Component")
        (field (name "Category") "Resistors,Chip Resistor - Surface Mount")
        (field (name "Manufacturer") "UNI-ROYAL(Uniroyal Elec)")
        (field (name "Part") "0603WAF5101T5E")
        (field (name "Resistance") "5.1kΩ")
        (field (name "Power(Watts)") "100mW")
        (field (name "Type") "Thick Film Resistors")
        (field (name "Overload Voltage (Max)") "75V")
        (field (name "Operating Temperature Range") "-55°C~+155°C")
        (field (name "Tolerance") "±1%")
        (field (name "Temperature Coefficient") "±100ppm/°C")
        (field (name "Footprint") "PCM_JLCPCB:R_0603")
        (field (name "Datasheet") "https://www.lcsc.com/datasheet/lcsc_datasheet_2206010116_UNI-ROYAL-Uniroyal-Elec-0603WAF5101T5E_C23186.pdf")
        (field (name "Description") "100mW Thick Film Resistors 75V ±100ppm/°C ±1% 5.1kΩ 0603 Chip Resistor - Surface Mount ROHS"))
      (libsource (lib "PCM_JLCPCB-Resistors") (part "0603,5.1kΩ") (description "100mW Thick Film Resistors 75V ±100ppm/°C ±1% 5.1kΩ 0603 Chip Resistor - Surface Mount ROHS"))
      (property (name "LCSC") (value "C23186"))
      (property (name "Stock") (value "9223405"))
      (property (name "Price") (value "0.004USD"))
      (property (name "Process") (value "SMT"))
      (property (name "Minimum Qty") (value "20"))
      (property (name "Attrition Qty") (value "10"))
      (property (name "Class") (value "Basic Component"))
      (property (name "Category") (value "Resistors,Chip Resistor - Surface Mount"))
      (property (name "Manufacturer") (value "UNI-ROYAL(Uniroyal Elec)"))
      (property (name "Part") (value "0603WAF5101T5E"))
      (property (name "Resistance") (value "5.1kΩ"))
      (property (name "Power(Watts)") (value "100mW"))
      (property (name "Type") (value "Thick Film Resistors"))
      (property (name "Overload Voltage (Max)") (value "75V"))
      (property (name "Operating Temperature Range") (value "-55°C~+155°C"))
      (property (name "Tolerance") (value "±1%"))
      (property (name "Temperature Coefficient") (value "±100ppm/°C"))
      (property (name "Sheetname") (value "Root"))
      (property (name "Sheetfile") (value "Pico_Development_Stack.kicad_sch"))
      (property (name "ki_fp_filters") (value "R_*"))
      (sheetpath (names "/") (tstamps "/"))
      (tstamps "ccd6596e-c2f8-4d81-9c64-94d9000b912c"))
    (comp (ref "R34")
      (value "330")
      (footprint "PCM_JLCPCB:R_0603")
      (datasheet "https://www.lcsc.com/datasheet/lcsc_datasheet_2206010116_UNI-ROYAL-Uniroyal-Elec-0603WAF3300T5E_C23138.pdf")
      (description "100mW Thick Film Resistors 75V ±100ppm/°C ±1% 330Ω 0603 Chip Resistor - Surface Mount ROHS")
      (fields
        (field (name "LCSC") "C23138")
        (field (name "Peak Wavelength"))
        (field (name "Stock") "2977706")
        (field (name "Price") "0.004USD")
        (field (name "Process") "SMT")
        (field (name "Minimum Qty") "20")
        (field (name "Attrition Qty") "10")
        (field (name "Class") "Basic Component")
        (field (name "Category") "Resistors,Chip Resistor - Surface Mount")
        (field (name "Manufacturer") "UNI-ROYAL(Uniroyal Elec)")
        (field (name "Part") "0603WAF3300T5E")
        (field (name "Resistance") "330Ω")
        (field (name "Power(Watts)") "100mW")
        (field (name "Type") "Thick Film Resistors")
        (field (name "Overload Voltage (Max)") "75V")
        (field (name "Operating Temperature Range") "-55°C~+155°C")
        (field (name "Tolerance") "±1%")
        (field (name "Temperature Coefficient") "±100ppm/°C")
        (field (name "Footprint") "PCM_JLCPCB:R_0603")
        (field (name "Datasheet") "https://www.lcsc.com/datasheet/lcsc_datasheet_2206010116_UNI-ROYAL-Uniroyal-Elec-0603WAF3300T5E_C23138.pdf")
        (field (name "Description") "100mW Thick Film Resistors 75V ±100ppm/°C ±1% 330Ω 0603 Chip Resistor - Surface Mount ROHS"))
      (libsource (lib "PCM_JLCPCB-Resistors") (part "0603,330Ω") (description "100mW Thick Film Resistors 75V ±100ppm/°C ±1% 330Ω 0603 Chip Resistor - Surface Mount ROHS"))
      (property (name "LCSC") (value "C23138"))
      (property (name "Peak Wavelength") (value ""))
      (property (name "Stock") (value "2977706"))
      (property (name "Price") (value "0.004USD"))
      (property (name "Process") (value "SMT"))
      (property (name "Minimum Qty") (value "20"))
      (property (name "Attrition Qty") (value "10"))
      (property (name "Class") (value "Basic Component"))
      (property (name "Category") (value "Resistors,Chip Resistor - Surface Mount"))
      (property (name "Manufacturer") (value "UNI-ROYAL(Uniroyal Elec)"))
      (property (name "Part") (value "0603WAF3300T5E"))
      (property (name "Resistance") (value "330Ω"))
      (property (name "Power(Watts)") (value "100mW"))
      (property (name "Type") (value "Thick Film Resistors"))
      (property (name "Overload Voltage (Max)") (value "75V"))
      (property (name "Operating Temperature Range") (value "-55°C~+155°C"))
      (property (name "Tolerance") (value "±1%"))
      (property (name "Temperature Coefficient") (value "±100ppm/°C"))
      (property (name "Sheetname") (value "Root"))
      (property (name "Sheetfile") (value "Pico_Development_Stack.kicad_sch"))
      (property (name "ki_fp_filters") (value "R_*"))
      (sheetpath (names "/") (tstamps "/"))
      (tstamps "053dfa64-907d-4be7-84a5-13097cc956ce"))
    (comp (ref "R35")
      (value "330")
      (footprint "PCM_JLCPCB:R_0603")
      (datasheet "https://www.lcsc.com/datasheet/lcsc_datasheet_2206010116_UNI-ROYAL-Uniroyal-Elec-0603WAF3300T5E_C23138.pdf")
      (description "100mW Thick Film Resistors 75V ±100ppm/°C ±1% 330Ω 0603 Chip Resistor - Surface Mount ROHS")
      (fields
        (field (name "LCSC") "C23138")
        (field (name "Peak Wavelength"))
        (field (name "Stock") "2977706")
        (field (name "Price") "0.004USD")
        (field (name "Process") "SMT")
        (field (name "Minimum Qty") "20")
        (field (name "Attrition Qty") "10")
        (field (name "Class") "Basic Component")
        (field (name "Category") "Resistors,Chip Resistor - Surface Mount")
        (field (name "Manufacturer") "UNI-ROYAL(Uniroyal Elec)")
        (field (name "Part") "0603WAF3300T5E")
        (field (name "Resistance") "330Ω")
        (field (name "Power(Watts)") "100mW")
        (field (name "Type") "Thick Film Resistors")
        (field (name "Overload Voltage (Max)") "75V")
        (field (name "Operating Temperature Range") "-55°C~+155°C")
        (field (name "Tolerance") "±1%")
        (field (name "Temperature Coefficient") "±100ppm/°C")
        (field (name "Footprint") "PCM_JLCPCB:R_0603")
        (field (name "Datasheet") "https://www.lcsc.com/datasheet/lcsc_datasheet_2206010116_UNI-ROYAL-Uniroyal-Elec-0603WAF3300T5E_C23138.pdf")
        (field (name "Description") "100mW Thick Film Resistors 75V ±100ppm/°C ±1% 330Ω 0603 Chip Resistor - Surface Mount ROHS"))
      (libsource (lib "PCM_JLCPCB-Resistors") (part "0603,330Ω") (description "100mW Thick Film Resistors 75V ±100ppm/°C ±1% 330Ω 0603 Chip Resistor - Surface Mount ROHS"))
      (property (name "LCSC") (value "C23138"))
      (property (name "Peak Wavelength") (value ""))
      (property (name "Stock") (value "2977706"))
      (property (name "Price") (value "0.004USD"))
      (property (name "Process") (value "SMT"))
      (property (name "Minimum Qty") (value "20"))
      (property (name "Attrition Qty") (value "10"))
      (property (name "Class") (value "Basic Component"))
      (property (name "Category") (value "Resistors,Chip Resistor - Surface Mount"))
      (property (name "Manufacturer") (value "UNI-ROYAL(Uniroyal Elec)"))
      (property (name "Part") (value "0603WAF3300T5E"))
      (property (name "Resistance") (value "330Ω"))
      (property (name "Power(Watts)") (value "100mW"))
      (property (name "Type") (value "Thick Film Resistors"))
      (property (name "Overload Voltage (Max)") (value "75V"))
      (property (name "Operating Temperature Range") (value "-55°C~+155°C"))
      (property (name "Tolerance") (value "±1%"))
      (property (name "Temperature Coefficient") (value "±100ppm/°C"))
      (property (name "Sheetname") (value "Root"))
      (property (name "Sheetfile") (value "Pico_Development_Stack.kicad_sch"))
      (property (name "ki_fp_filters") (value "R_*"))
      (sheetpath (names "/") (tstamps "/"))
      (tstamps "2575b72d-b009-46a0-a927-670b3dfc9b27"))
    (comp (ref "R36")
      (value "330")
      (footprint "PCM_JLCPCB:R_0603")
      (datasheet "https://www.lcsc.com/datasheet/lcsc_datasheet_2206010116_UNI-ROYAL-Uniroyal-Elec-0603WAF3300T5E_C23138.pdf")
      (description "100mW Thick Film Resistors 75V ±100ppm/°C ±1% 330Ω 0603 Chip Resistor - Surface Mount ROHS")
      (fields
        (field (name "LCSC") "C23138")
        (field (name "Peak Wavelength"))
        (field (name "Stock") "2977706")
        (field (name "Price") "0.004USD")
        (field (name "Process") "SMT")
        (field (name "Minimum Qty") "20")
        (field (name "Attrition Qty") "10")
        (field (name "Class") "Basic Component")
        (field (name "Category") "Resistors,Chip Resistor - Surface Mount")
        (field (name "Manufacturer") "UNI-ROYAL(Uniroyal Elec)")
        (field (name "Part") "0603WAF3300T5E")
        (field (name "Resistance") "330Ω")
        (field (name "Power(Watts)") "100mW")
        (field (name "Type") "Thick Film Resistors")
        (field (name "Overload Voltage (Max)") "75V")
        (field (name "Operating Temperature Range") "-55°C~+155°C")
        (field (name "Tolerance") "±1%")
        (field (name "Temperature Coefficient") "±100ppm/°C")
        (field (name "Footprint") "PCM_JLCPCB:R_0603")
        (field (name "Datasheet") "https://www.lcsc.com/datasheet/lcsc_datasheet_2206010116_UNI-ROYAL-Uniroyal-Elec-0603WAF3300T5E_C23138.pdf")
        (field (name "Description") "100mW Thick Film Resistors 75V ±100ppm/°C ±1% 330Ω 0603 Chip Resistor - Surface Mount ROHS"))
      (libsource (lib "PCM_JLCPCB-Resistors") (part "0603,330Ω") (description "100mW Thick Film Resistors 75V ±100ppm/°C ±1% 330Ω 0603 Chip Resistor - Surface Mount ROHS"))
      (property (name "LCSC") (value "C23138"))
      (property (name "Peak Wavelength") (value ""))
      (property (name "Stock") (value "2977706"))
      (property (name "Price") (value "0.004USD"))
      (property (name "Process") (value "SMT"))
      (property (name "Minimum Qty") (value "20"))
      (property (name "Attrition Qty") (value "10"))
      (property (name "Class") (value "Basic Component"))
      (property (name "Category") (value "Resistors,Chip Resistor - Surface Mount"))
      (property (name "Manufacturer") (value "UNI-ROYAL(Uniroyal Elec)"))
      (property (name "Part") (value "0603WAF3300T5E"))
      (property (name "Resistance") (value "330Ω"))
      (property (name "Power(Watts)") (value "100mW"))
      (property (name "Type") (value "Thick Film Resistors"))
      (property (name "Overload Voltage (Max)") (value "75V"))
      (property (name "Operating Temperature Range") (value "-55°C~+155°C"))
      (property (name "Tolerance") (value "±1%"))
      (property (name "Temperature Coefficient") (value "±100ppm/°C"))
      (property (name "Sheetname") (value "Root"))
      (property (name "Sheetfile") (value "Pico_Development_Stack.kicad_sch"))
      (property (name "ki_fp_filters") (value "R_*"))
      (sheetpath (names "/") (tstamps "/"))
      (tstamps "a955a0d0-fe73-4e05-9698-b773a6c3b43d"))
    (comp (ref "R37")
      (value "330")
      (footprint "PCM_JLCPCB:R_0603")
      (datasheet "https://www.lcsc.com/datasheet/lcsc_datasheet_2206010116_UNI-ROYAL-Uniroyal-Elec-0603WAF3300T5E_C23138.pdf")
      (description "100mW Thick Film Resistors 75V ±100ppm/°C ±1% 330Ω 0603 Chip Resistor - Surface Mount ROHS")
      (fields
        (field (name "LCSC") "C23138")
        (field (name "Peak Wavelength"))
        (field (name "Stock") "2977706")
        (field (name "Price") "0.004USD")
        (field (name "Process") "SMT")
        (field (name "Minimum Qty") "20")
        (field (name "Attrition Qty") "10")
        (field (name "Class") "Basic Component")
        (field (name "Category") "Resistors,Chip Resistor - Surface Mount")
        (field (name "Manufacturer") "UNI-ROYAL(Uniroyal Elec)")
        (field (name "Part") "0603WAF3300T5E")
        (field (name "Resistance") "330Ω")
        (field (name "Power(Watts)") "100mW")
        (field (name "Type") "Thick Film Resistors")
        (field (name "Overload Voltage (Max)") "75V")
        (field (name "Operating Temperature Range") "-55°C~+155°C")
        (field (name "Tolerance") "±1%")
        (field (name "Temperature Coefficient") "±100ppm/°C")
        (field (name "Footprint") "PCM_JLCPCB:R_0603")
        (field (name "Datasheet") "https://www.lcsc.com/datasheet/lcsc_datasheet_2206010116_UNI-ROYAL-Uniroyal-Elec-0603WAF3300T5E_C23138.pdf")
        (field (name "Description") "100mW Thick Film Resistors 75V ±100ppm/°C ±1% 330Ω 0603 Chip Resistor - Surface Mount ROHS"))
      (libsource (lib "PCM_JLCPCB-Resistors") (part "0603,330Ω") (description "100mW Thick Film Resistors 75V ±100ppm/°C ±1% 330Ω 0603 Chip Resistor - Surface Mount ROHS"))
      (property (name "LCSC") (value "C23138"))
      (property (name "Peak Wavelength") (value ""))
      (property (name "Stock") (value "2977706"))
      (property (name "Price") (value "0.004USD"))
      (property (name "Process") (value "SMT"))
      (property (name "Minimum Qty") (value "20"))
      (property (name "Attrition Qty") (value "10"))
      (property (name "Class") (value "Basic Component"))
      (property (name "Category") (value "Resistors,Chip Resistor - Surface Mount"))
      (property (name "Manufacturer") (value "UNI-ROYAL(Uniroyal Elec)"))
      (property (name "Part") (value "0603WAF3300T5E"))
      (property (name "Resistance") (value "330Ω"))
      (property (name "Power(Watts)") (value "100mW"))
      (property (name "Type") (value "Thick Film Resistors"))
      (property (name "Overload Voltage (Max)") (value "75V"))
      (property (name "Operating Temperature Range") (value "-55°C~+155°C"))
      (property (name "Tolerance") (value "±1%"))
      (property (name "Temperature Coefficient") (value "±100ppm/°C"))
      (property (name "Sheetname") (value "Root"))
      (property (name "Sheetfile") (value "Pico_Development_Stack.kicad_sch"))
      (property (name "ki_fp_filters") (value "R_*"))
      (sheetpath (names "/") (tstamps "/"))
      (tstamps "3036f69e-f851-46dc-a9ee-e2e35b79b050"))
    (comp (ref "R38")
      (value "330")
      (footprint "PCM_JLCPCB:R_0603")
      (datasheet "https://www.lcsc.com/datasheet/lcsc_datasheet_2206010116_UNI-ROYAL-Uniroyal-Elec-0603WAF3300T5E_C23138.pdf")
      (description "100mW Thick Film Resistors 75V ±100ppm/°C ±1% 330Ω 0603 Chip Resistor - Surface Mount ROHS")
      (fields
        (field (name "LCSC") "C23138")
        (field (name "Peak Wavelength"))
        (field (name "Stock") "2977706")
        (field (name "Price") "0.004USD")
        (field (name "Process") "SMT")
        (field (name "Minimum Qty") "20")
        (field (name "Attrition Qty") "10")
        (field (name "Class") "Basic Component")
        (field (name "Category") "Resistors,Chip Resistor - Surface Mount")
        (field (name "Manufacturer") "UNI-ROYAL(Uniroyal Elec)")
        (field (name "Part") "0603WAF3300T5E")
        (field (name "Resistance") "330Ω")
        (field (name "Power(Watts)") "100mW")
        (field (name "Type") "Thick Film Resistors")
        (field (name "Overload Voltage (Max)") "75V")
        (field (name "Operating Temperature Range") "-55°C~+155°C")
        (field (name "Tolerance") "±1%")
        (field (name "Temperature Coefficient") "±100ppm/°C")
        (field (name "Footprint") "PCM_JLCPCB:R_0603")
        (field (name "Datasheet") "https://www.lcsc.com/datasheet/lcsc_datasheet_2206010116_UNI-ROYAL-Uniroyal-Elec-0603WAF3300T5E_C23138.pdf")
        (field (name "Description") "100mW Thick Film Resistors 75V ±100ppm/°C ±1% 330Ω 0603 Chip Resistor - Surface Mount ROHS"))
      (libsource (lib "PCM_JLCPCB-Resistors") (part "0603,330Ω") (description "100mW Thick Film Resistors 75V ±100ppm/°C ±1% 330Ω 0603 Chip Resistor - Surface Mount ROHS"))
      (property (name "LCSC") (value "C23138"))
      (property (name "Peak Wavelength") (value ""))
      (property (name "Stock") (value "2977706"))
      (property (name "Price") (value "0.004USD"))
      (property (name "Process") (value "SMT"))
      (property (name "Minimum Qty") (value "20"))
      (property (name "Attrition Qty") (value "10"))
      (property (name "Class") (value "Basic Component"))
      (property (name "Category") (value "Resistors,Chip Resistor - Surface Mount"))
      (property (name "Manufacturer") (value "UNI-ROYAL(Uniroyal Elec)"))
      (property (name "Part") (value "0603WAF3300T5E"))
      (property (name "Resistance") (value "330Ω"))
      (property (name "Power(Watts)") (value "100mW"))
      (property (name "Type") (value "Thick Film Resistors"))
      (property (name "Overload Voltage (Max)") (value "75V"))
      (property (name "Operating Temperature Range") (value "-55°C~+155°C"))
      (property (name "Tolerance") (value "±1%"))
      (property (name "Temperature Coefficient") (value "±100ppm/°C"))
      (property (name "Sheetname") (value "Root"))
      (property (name "Sheetfile") (value "Pico_Development_Stack.kicad_sch"))
      (property (name "ki_fp_filters") (value "R_*"))
      (sheetpath (names "/") (tstamps "/"))
      (tstamps "c562d970-737a-43b4-9123-340f46c24050"))
    (comp (ref "R39")
      (value "330")
      (footprint "PCM_JLCPCB:R_0603")
      (datasheet "https://www.lcsc.com/datasheet/lcsc_datasheet_2206010116_UNI-ROYAL-Uniroyal-Elec-0603WAF3300T5E_C23138.pdf")
      (description "100mW Thick Film Resistors 75V ±100ppm/°C ±1% 330Ω 0603 Chip Resistor - Surface Mount ROHS")
      (fields
        (field (name "LCSC") "C23138")
        (field (name "Peak Wavelength"))
        (field (name "Stock") "2977706")
        (field (name "Price") "0.004USD")
        (field (name "Process") "SMT")
        (field (name "Minimum Qty") "20")
        (field (name "Attrition Qty") "10")
        (field (name "Class") "Basic Component")
        (field (name "Category") "Resistors,Chip Resistor - Surface Mount")
        (field (name "Manufacturer") "UNI-ROYAL(Uniroyal Elec)")
        (field (name "Part") "0603WAF3300T5E")
        (field (name "Resistance") "330Ω")
        (field (name "Power(Watts)") "100mW")
        (field (name "Type") "Thick Film Resistors")
        (field (name "Overload Voltage (Max)") "75V")
        (field (name "Operating Temperature Range") "-55°C~+155°C")
        (field (name "Tolerance") "±1%")
        (field (name "Temperature Coefficient") "±100ppm/°C")
        (field (name "Footprint") "PCM_JLCPCB:R_0603")
        (field (name "Datasheet") "https://www.lcsc.com/datasheet/lcsc_datasheet_2206010116_UNI-ROYAL-Uniroyal-Elec-0603WAF3300T5E_C23138.pdf")
        (field (name "Description") "100mW Thick Film Resistors 75V ±100ppm/°C ±1% 330Ω 0603 Chip Resistor - Surface Mount ROHS"))
      (libsource (lib "PCM_JLCPCB-Resistors") (part "0603,330Ω") (description "100mW Thick Film Resistors 75V ±100ppm/°C ±1% 330Ω 0603 Chip Resistor - Surface Mount ROHS"))
      (property (name "LCSC") (value "C23138"))
      (property (name "Peak Wavelength") (value ""))
      (property (name "Stock") (value "2977706"))
      (property (name "Price") (value "0.004USD"))
      (property (name "Process") (value "SMT"))
      (property (name "Minimum Qty") (value "20"))
      (property (name "Attrition Qty") (value "10"))
      (property (name "Class") (value "Basic Component"))
      (property (name "Category") (value "Resistors,Chip Resistor - Surface Mount"))
      (property (name "Manufacturer") (value "UNI-ROYAL(Uniroyal Elec)"))
      (property (name "Part") (value "0603WAF3300T5E"))
      (property (name "Resistance") (value "330Ω"))
      (property (name "Power(Watts)") (value "100mW"))
      (property (name "Type") (value "Thick Film Resistors"))
      (property (name "Overload Voltage (Max)") (value "75V"))
      (property (name "Operating Temperature Range") (value "-55°C~+155°C"))
      (property (name "Tolerance") (value "±1%"))
      (property (name "Temperature Coefficient") (value "±100ppm/°C"))
      (property (name "Sheetname") (value "Root"))
      (property (name "Sheetfile") (value "Pico_Development_Stack.kicad_sch"))
      (property (name "ki_fp_filters") (value "R_*"))
      (sheetpath (names "/") (tstamps "/"))
      (tstamps "96552dd3-270e-4728-aa30-b563f4dcccc1"))
    (comp (ref "R40")
      (value "330")
      (footprint "PCM_JLCPCB:R_0603")
      (datasheet "https://www.lcsc.com/datasheet/lcsc_datasheet_2206010116_UNI-ROYAL-Uniroyal-Elec-0603WAF3300T5E_C23138.pdf")
      (description "100mW Thick Film Resistors 75V ±100ppm/°C ±1% 330Ω 0603 Chip Resistor - Surface Mount ROHS")
      (fields
        (field (name "LCSC") "C23138")
        (field (name "Peak Wavelength"))
        (field (name "Stock") "2977706")
        (field (name "Price") "0.004USD")
        (field (name "Process") "SMT")
        (field (name "Minimum Qty") "20")
        (field (name "Attrition Qty") "10")
        (field (name "Class") "Basic Component")
        (field (name "Category") "Resistors,Chip Resistor - Surface Mount")
        (field (name "Manufacturer") "UNI-ROYAL(Uniroyal Elec)")
        (field (name "Part") "0603WAF3300T5E")
        (field (name "Resistance") "330Ω")
        (field (name "Power(Watts)") "100mW")
        (field (name "Type") "Thick Film Resistors")
        (field (name "Overload Voltage (Max)") "75V")
        (field (name "Operating Temperature Range") "-55°C~+155°C")
        (field (name "Tolerance") "±1%")
        (field (name "Temperature Coefficient") "±100ppm/°C")
        (field (name "Footprint") "PCM_JLCPCB:R_0603")
        (field (name "Datasheet") "https://www.lcsc.com/datasheet/lcsc_datasheet_2206010116_UNI-ROYAL-Uniroyal-Elec-0603WAF3300T5E_C23138.pdf")
        (field (name "Description") "100mW Thick Film Resistors 75V ±100ppm/°C ±1% 330Ω 0603 Chip Resistor - Surface Mount ROHS"))
      (libsource (lib "PCM_JLCPCB-Resistors") (part "0603,330Ω") (description "100mW Thick Film Resistors 75V ±100ppm/°C ±1% 330Ω 0603 Chip Resistor - Surface Mount ROHS"))
      (property (name "LCSC") (value "C23138"))
      (property (name "Peak Wavelength") (value ""))
      (property (name "Stock") (value "2977706"))
      (property (name "Price") (value "0.004USD"))
      (property (name "Process") (value "SMT"))
      (property (name "Minimum Qty") (value "20"))
      (property (name "Attrition Qty") (value "10"))
      (property (name "Class") (value "Basic Component"))
      (property (name "Category") (value "Resistors,Chip Resistor - Surface Mount"))
      (property (name "Manufacturer") (value "UNI-ROYAL(Uniroyal Elec)"))
      (property (name "Part") (value "0603WAF3300T5E"))
      (property (name "Resistance") (value "330Ω"))
      (property (name "Power(Watts)") (value "100mW"))
      (property (name "Type") (value "Thick Film Resistors"))
      (property (name "Overload Voltage (Max)") (value "75V"))
      (property (name "Operating Temperature Range") (value "-55°C~+155°C"))
      (property (name "Tolerance") (value "±1%"))
      (property (name "Temperature Coefficient") (value "±100ppm/°C"))
      (property (name "Sheetname") (value "Root"))
      (property (name "Sheetfile") (value "Pico_Development_Stack.kicad_sch"))
      (property (name "ki_fp_filters") (value "R_*"))
      (sheetpath (names "/") (tstamps "/"))
      (tstamps "5a86e9bd-248a-40a2-b508-a1ba28b990fd"))
    (comp (ref "R41")
      (value "330")
      (footprint "PCM_JLCPCB:R_0603")
      (datasheet "https://www.lcsc.com/datasheet/lcsc_datasheet_2206010116_UNI-ROYAL-Uniroyal-Elec-0603WAF3300T5E_C23138.pdf")
      (description "100mW Thick Film Resistors 75V ±100ppm/°C ±1% 330Ω 0603 Chip Resistor - Surface Mount ROHS")
      (fields
        (field (name "LCSC") "C23138")
        (field (name "Peak Wavelength"))
        (field (name "Stock") "2977706")
        (field (name "Price") "0.004USD")
        (field (name "Process") "SMT")
        (field (name "Minimum Qty") "20")
        (field (name "Attrition Qty") "10")
        (field (name "Class") "Basic Component")
        (field (name "Category") "Resistors,Chip Resistor - Surface Mount")
        (field (name "Manufacturer") "UNI-ROYAL(Uniroyal Elec)")
        (field (name "Part") "0603WAF3300T5E")
        (field (name "Resistance") "330Ω")
        (field (name "Power(Watts)") "100mW")
        (field (name "Type") "Thick Film Resistors")
        (field (name "Overload Voltage (Max)") "75V")
        (field (name "Operating Temperature Range") "-55°C~+155°C")
        (field (name "Tolerance") "±1%")
        (field (name "Temperature Coefficient") "±100ppm/°C")
        (field (name "Footprint") "PCM_JLCPCB:R_0603")
        (field (name "Datasheet") "https://www.lcsc.com/datasheet/lcsc_datasheet_2206010116_UNI-ROYAL-Uniroyal-Elec-0603WAF3300T5E_C23138.pdf")
        (field (name "Description") "100mW Thick Film Resistors 75V ±100ppm/°C ±1% 330Ω 0603 Chip Resistor - Surface Mount ROHS"))
      (libsource (lib "PCM_JLCPCB-Resistors") (part "0603,330Ω") (description "100mW Thick Film Resistors 75V ±100ppm/°C ±1% 330Ω 0603 Chip Resistor - Surface Mount ROHS"))
      (property (name "LCSC") (value "C23138"))
      (property (name "Peak Wavelength") (value ""))
      (property (name "Stock") (value "2977706"))
      (property (name "Price") (value "0.004USD"))
      (property (name "Process") (value "SMT"))
      (property (name "Minimum Qty") (value "20"))
      (property (name "Attrition Qty") (value "10"))
      (property (name "Class") (value "Basic Component"))
      (property (name "Category") (value "Resistors,Chip Resistor - Surface Mount"))
      (property (name "Manufacturer") (value "UNI-ROYAL(Uniroyal Elec)"))
      (property (name "Part") (value "0603WAF3300T5E"))
      (property (name "Resistance") (value "330Ω"))
      (property (name "Power(Watts)") (value "100mW"))
      (property (name "Type") (value "Thick Film Resistors"))
      (property (name "Overload Voltage (Max)") (value "75V"))
      (property (name "Operating Temperature Range") (value "-55°C~+155°C"))
      (property (name "Tolerance") (value "±1%"))
      (property (name "Temperature Coefficient") (value "±100ppm/°C"))
      (property (name "Sheetname") (value "Root"))
      (property (name "Sheetfile") (value "Pico_Development_Stack.kicad_sch"))
      (property (name "ki_fp_filters") (value "R_*"))
      (sheetpath (names "/") (tstamps "/"))
      (tstamps "aaba75bd-77a4-4085-9207-0e27265cc6ce"))
    (comp (ref "R42")
      (value "10kΩ")
      (footprint "PCM_JLCPCB:R_0603")
      (datasheet "https://www.lcsc.com/datasheet/lcsc_datasheet_2206010045_UNI-ROYAL-Uniroyal-Elec-0603WAF1002T5E_C25804.pdf")
      (description "100mW Thick Film Resistors 75V ±100ppm/°C ±1% 10kΩ 0603 Chip Resistor - Surface Mount ROHS")
      (fields
        (field (name "LCSC") "C25804")
        (field (name "Stock") "51181774")
        (field (name "Price") "0.004USD")
        (field (name "Process") "SMT")
        (field (name "Minimum Qty") "20")
        (field (name "Attrition Qty") "10")
        (field (name "Class") "Basic Component")
        (field (name "Category") "Resistors,Chip Resistor - Surface Mount")
        (field (name "Manufacturer") "UNI-ROYAL(Uniroyal Elec)")
        (field (name "Part") "0603WAF1002T5E")
        (field (name "Resistance") "10kΩ")
        (field (name "Power(Watts)") "100mW")
        (field (name "Type") "Thick Film Resistors")
        (field (name "Overload Voltage (Max)") "75V")
        (field (name "Operating Temperature Range") "-55°C~+155°C")
        (field (name "Tolerance") "±1%")
        (field (name "Temperature Coefficient") "±100ppm/°C")
        (field (name "Footprint") "PCM_JLCPCB:R_0603")
        (field (name "Datasheet") "https://www.lcsc.com/datasheet/lcsc_datasheet_2206010045_UNI-ROYAL-Uniroyal-Elec-0603WAF1002T5E_C25804.pdf")
        (field (name "Description") "100mW Thick Film Resistors 75V ±100ppm/°C ±1% 10kΩ 0603 Chip Resistor - Surface Mount ROHS"))
      (libsource (lib "PCM_JLCPCB-Resistors") (part "0603,10kΩ") (description "100mW Thick Film Resistors 75V ±100ppm/°C ±1% 10kΩ 0603 Chip Resistor - Surface Mount ROHS"))
      (property (name "LCSC") (value "C25804"))
      (property (name "Stock") (value "51181774"))
      (property (name "Price") (value "0.004USD"))
      (property (name "Process") (value "SMT"))
      (property (name "Minimum Qty") (value "20"))
      (property (name "Attrition Qty") (value "10"))
      (property (name "Class") (value "Basic Component"))
      (property (name "Category") (value "Resistors,Chip Resistor - Surface Mount"))
      (property (name "Manufacturer") (value "UNI-ROYAL(Uniroyal Elec)"))
      (property (name "Part") (value "0603WAF1002T5E"))
      (property (name "Resistance") (value "10kΩ"))
      (property (name "Power(Watts)") (value "100mW"))
      (property (name "Type") (value "Thick Film Resistors"))
      (property (name "Overload Voltage (Max)") (value "75V"))
      (property (name "Operating Temperature Range") (value "-55°C~+155°C"))
      (property (name "Tolerance") (value "±1%"))
      (property (name "Temperature Coefficient") (value "±100ppm/°C"))
      (property (name "Sheetname") (value "Root"))
      (property (name "Sheetfile") (value "Pico_Development_Stack.kicad_sch"))
      (property (name "ki_fp_filters") (value "R_*"))
      (sheetpath (names "/") (tstamps "/"))
      (tstamps "e5dea919-a4a1-45a5-9aa8-49dda1decb16"))
    (comp (ref "R43")
      (value "100")
      (footprint "PCM_JLCPCB:R_0603")
      (datasheet "https://www.lcsc.com/datasheet/lcsc_datasheet_2411221126_UNI-ROYAL-Uniroyal-Elec-0603WAF1000T5E_C22775.pdf")
      (description "100mW Thick Film Resistors 75V ±1% ±200ppm/°C 100Ω 0603 Chip Resistor - Surface Mount ROHS")
      (fields
        (field (name "Digi-Key Part Number"))
        (field (name "MPN") "RC0402FR-07100RL")
        (field (name "Manufacturer") "UNI-ROYAL(Uniroyal Elec)")
        (field (name "Supplier") "LCSC")
        (field (name "LCSC") "C22775")
        (field (name "Attrition Qty") "10")
        (field (name "Capacitance"))
        (field (name "Category") "Resistors,Chip Resistor - Surface Mount")
        (field (name "Class") "Basic Component")
        (field (name "Minimum Qty") "20")
        (field (name "Part") "0603WAF1000T5E")
        (field (name "Price") "0.004USD")
        (field (name "Process") "SMT")
        (field (name "Stock") "8202320")
        (field (name "Temperature Coefficient") "±200ppm/°C")
        (field (name "Tolerance") "±1%")
        (field (name "Voltage Rated"))
        (field (name "Peak Wavelength"))
        (field (name "Resistance") "100Ω")
        (field (name "Power(Watts)") "100mW")
        (field (name "Type") "Thick Film Resistors")
        (field (name "Overload Voltage (Max)") "75V")
        (field (name "Operating Temperature Range") "-55°C~+155°C")
        (field (name "Footprint") "PCM_JLCPCB:R_0603")
        (field (name "Datasheet") "https://www.lcsc.com/datasheet/lcsc_datasheet_2411221126_UNI-ROYAL-Uniroyal-Elec-0603WAF1000T5E_C22775.pdf")
        (field (name "Description") "100mW Thick Film Resistors 75V ±1% ±200ppm/°C 100Ω 0603 Chip Resistor - Surface Mount ROHS"))
      (libsource (lib "PCM_JLCPCB-Resistors") (part "0603,100Ω") (description "100mW Thick Film Resistors 75V ±1% ±200ppm/°C 100Ω 0603 Chip Resistor - Surface Mount ROHS"))
      (property (name "Digi-Key Part Number") (value ""))
      (property (name "MPN") (value "RC0402FR-07100RL"))
      (property (name "Manufacturer") (value "UNI-ROYAL(Uniroyal Elec)"))
      (property (name "Supplier") (value "LCSC"))
      (property (name "LCSC") (value "C22775"))
      (property (name "Attrition Qty") (value "10"))
      (property (name "Capacitance") (value ""))
      (property (name "Category") (value "Resistors,Chip Resistor - Surface Mount"))
      (property (name "Class") (value "Basic Component"))
      (property (name "Minimum Qty") (value "20"))
      (property (name "Part") (value "0603WAF1000T5E"))
      (property (name "Price") (value "0.004USD"))
      (property (name "Process") (value "SMT"))
      (property (name "Stock") (value "8202320"))
      (property (name "Temperature Coefficient") (value "±200ppm/°C"))
      (property (name "Tolerance") (value "±1%"))
      (property (name "Voltage Rated") (value ""))
      (property (name "Peak Wavelength") (value ""))
      (property (name "Resistance") (value "100Ω"))
      (property (name "Power(Watts)") (value "100mW"))
      (property (name "Type") (value "Thick Film Resistors"))
      (property (name "Overload Voltage (Max)") (value "75V"))
      (property (name "Operating Temperature Range") (value "-55°C~+155°C"))
      (property (name "Sheetname") (value "Root"))
      (property (name "Sheetfile") (value "Pico_Development_Stack.kicad_sch"))
      (property (name "ki_fp_filters") (value "R_*"))
      (sheetpath (names "/") (tstamps "/"))
      (tstamps "1e941516-0753-4fa8-b12e-37d95368e28d"))
    (comp (ref "R44")
      (value "1k")
      (footprint "PCM_JLCPCB:R_0603")
      (datasheet "https://www.lcsc.com/datasheet/lcsc_datasheet_2206010130_UNI-ROYAL-Uniroyal-Elec-0603WAF1001T5E_C21190.pdf")
      (description "100mW Thick Film Resistors 75V ±100ppm/°C ±1% 1kΩ 0603 Chip Resistor - Surface Mount ROHS")
      (fields
        (field (name "Digi-Key Part Number"))
        (field (name "MPN") "RC0402FR-071KL")
        (field (name "Manufacturer") "UNI-ROYAL(Uniroyal Elec)")
        (field (name "Supplier") "LCSC")
        (field (name "LCSC") "C21190")
        (field (name "Attrition Qty") "10")
        (field (name "Capacitance"))
        (field (name "Category") "Resistors,Chip Resistor - Surface Mount")
        (field (name "Class") "Basic Component")
        (field (name "Minimum Qty") "20")
        (field (name "Part") "0603WAF1001T5E")
        (field (name "Price") "0.004USD")
        (field (name "Process") "SMT")
        (field (name "Stock") "27538425")
        (field (name "Temperature Coefficient") "±100ppm/°C")
        (field (name "Tolerance") "±1%")
        (field (name "Voltage Rated"))
        (field (name "Peak Wavelength"))
        (field (name "Resistance") "1kΩ")
        (field (name "Power(Watts)") "100mW")
        (field (name "Type") "Thick Film Resistors")
        (field (name "Overload Voltage (Max)") "75V")
        (field (name "Operating Temperature Range") "-55°C~+155°C")
        (field (name "Footprint") "PCM_JLCPCB:R_0603")
        (field (name "Datasheet") "https://www.lcsc.com/datasheet/lcsc_datasheet_2206010130_UNI-ROYAL-Uniroyal-Elec-0603WAF1001T5E_C21190.pdf")
        (field (name "Description") "100mW Thick Film Resistors 75V ±100ppm/°C ±1% 1kΩ 0603 Chip Resistor - Surface Mount ROHS"))
      (libsource (lib "PCM_JLCPCB-Resistors") (part "0603,1kΩ") (description "100mW Thick Film Resistors 75V ±100ppm/°C ±1% 1kΩ 0603 Chip Resistor - Surface Mount ROHS"))
      (property (name "Digi-Key Part Number") (value ""))
      (property (name "MPN") (value "RC0402FR-071KL"))
      (property (name "Manufacturer") (value "UNI-ROYAL(Uniroyal Elec)"))
      (property (name "Supplier") (value "LCSC"))
      (property (name "LCSC") (value "C21190"))
      (property (name "Attrition Qty") (value "10"))
      (property (name "Capacitance") (value ""))
      (property (name "Category") (value "Resistors,Chip Resistor - Surface Mount"))
      (property (name "Class") (value "Basic Component"))
      (property (name "Minimum Qty") (value "20"))
      (property (name "Part") (value "0603WAF1001T5E"))
      (property (name "Price") (value "0.004USD"))
      (property (name "Process") (value "SMT"))
      (property (name "Stock") (value "27538425"))
      (property (name "Temperature Coefficient") (value "±100ppm/°C"))
      (property (name "Tolerance") (value "±1%"))
      (property (name "Voltage Rated") (value ""))
      (property (name "Peak Wavelength") (value ""))
      (property (name "Resistance") (value "1kΩ"))
      (property (name "Power(Watts)") (value "100mW"))
      (property (name "Type") (value "Thick Film Resistors"))
      (property (name "Overload Voltage (Max)") (value "75V"))
      (property (name "Operating Temperature Range") (value "-55°C~+155°C"))
      (property (name "Sheetname") (value "Root"))
      (property (name "Sheetfile") (value "Pico_Development_Stack.kicad_sch"))
      (property (name "ki_fp_filters") (value "R_*"))
      (sheetpath (names "/") (tstamps "/"))
      (tstamps "7fc3d283-3b6c-442d-9072-e32525b8e2ff"))
    (comp (ref "R45")
      (value "1k")
      (footprint "PCM_JLCPCB:R_0603")
      (datasheet "https://www.lcsc.com/datasheet/lcsc_datasheet_2206010130_UNI-ROYAL-Uniroyal-Elec-0603WAF1001T5E_C21190.pdf")
      (description "100mW Thick Film Resistors 75V ±100ppm/°C ±1% 1kΩ 0603 Chip Resistor - Surface Mount ROHS")
      (fields
        (field (name "Digi-Key Part Number"))
        (field (name "MPN") "RC0402FR-071KL")
        (field (name "Manufacturer") "UNI-ROYAL(Uniroyal Elec)")
        (field (name "Supplier") "LCSC")
        (field (name "LCSC") "C21190")
        (field (name "Attrition Qty") "10")
        (field (name "Capacitance"))
        (field (name "Category") "Resistors,Chip Resistor - Surface Mount")
        (field (name "Class") "Basic Component")
        (field (name "Minimum Qty") "20")
        (field (name "Part") "0603WAF1001T5E")
        (field (name "Price") "0.004USD")
        (field (name "Process") "SMT")
        (field (name "Stock") "27538425")
        (field (name "Temperature Coefficient") "±100ppm/°C")
        (field (name "Tolerance") "±1%")
        (field (name "Voltage Rated"))
        (field (name "Peak Wavelength"))
        (field (name "Resistance") "1kΩ")
        (field (name "Power(Watts)") "100mW")
        (field (name "Type") "Thick Film Resistors")
        (field (name "Overload Voltage (Max)") "75V")
        (field (name "Operating Temperature Range") "-55°C~+155°C")
        (field (name "Footprint") "PCM_JLCPCB:R_0603")
        (field (name "Datasheet") "https://www.lcsc.com/datasheet/lcsc_datasheet_2206010130_UNI-ROYAL-Uniroyal-Elec-0603WAF1001T5E_C21190.pdf")
        (field (name "Description") "100mW Thick Film Resistors 75V ±100ppm/°C ±1% 1kΩ 0603 Chip Resistor - Surface Mount ROHS"))
      (libsource (lib "PCM_JLCPCB-Resistors") (part "0603,1kΩ") (description "100mW Thick Film Resistors 75V ±100ppm/°C ±1% 1kΩ 0603 Chip Resistor - Surface Mount ROHS"))
      (property (name "Digi-Key Part Number") (value ""))
      (property (name "MPN") (value "RC0402FR-071KL"))
      (property (name "Manufacturer") (value "UNI-ROYAL(Uniroyal Elec)"))
      (property (name "Supplier") (value "LCSC"))
      (property (name "LCSC") (value "C21190"))
      (property (name "Attrition Qty") (value "10"))
      (property (name "Capacitance") (value ""))
      (property (name "Category") (value "Resistors,Chip Resistor - Surface Mount"))
      (property (name "Class") (value "Basic Component"))
      (property (name "Minimum Qty") (value "20"))
      (property (name "Part") (value "0603WAF1001T5E"))
      (property (name "Price") (value "0.004USD"))
      (property (name "Process") (value "SMT"))
      (property (name "Stock") (value "27538425"))
      (property (name "Temperature Coefficient") (value "±100ppm/°C"))
      (property (name "Tolerance") (value "±1%"))
      (property (name "Voltage Rated") (value ""))
      (property (name "Peak Wavelength") (value ""))
      (property (name "Resistance") (value "1kΩ"))
      (property (name "Power(Watts)") (value "100mW"))
      (property (name "Type") (value "Thick Film Resistors"))
      (property (name "Overload Voltage (Max)") (value "75V"))
      (property (name "Operating Temperature Range") (value "-55°C~+155°C"))
      (property (name "Sheetname") (value "Root"))
      (property (name "Sheetfile") (value "Pico_Development_Stack.kicad_sch"))
      (property (name "ki_fp_filters") (value "R_*"))
      (sheetpath (names "/") (tstamps "/"))
      (tstamps "ce8088b6-cb2f-49e6-a79c-f16160c6efc1"))
    (comp (ref "R46")
      (value "330")
      (footprint "PCM_JLCPCB:R_0603")
      (datasheet "https://www.lcsc.com/datasheet/lcsc_datasheet_2206010116_UNI-ROYAL-Uniroyal-Elec-0603WAF3300T5E_C23138.pdf")
      (description "100mW Thick Film Resistors 75V ±100ppm/°C ±1% 330Ω 0603 Chip Resistor - Surface Mount ROHS")
      (fields
        (field (name "LCSC") "C23138")
        (field (name "Peak Wavelength"))
        (field (name "Stock") "2977706")
        (field (name "Price") "0.004USD")
        (field (name "Process") "SMT")
        (field (name "Minimum Qty") "20")
        (field (name "Attrition Qty") "10")
        (field (name "Class") "Basic Component")
        (field (name "Category") "Resistors,Chip Resistor - Surface Mount")
        (field (name "Manufacturer") "UNI-ROYAL(Uniroyal Elec)")
        (field (name "Part") "0603WAF3300T5E")
        (field (name "Resistance") "330Ω")
        (field (name "Power(Watts)") "100mW")
        (field (name "Type") "Thick Film Resistors")
        (field (name "Overload Voltage (Max)") "75V")
        (field (name "Operating Temperature Range") "-55°C~+155°C")
        (field (name "Tolerance") "±1%")
        (field (name "Temperature Coefficient") "±100ppm/°C")
        (field (name "Footprint") "PCM_JLCPCB:R_0603")
        (field (name "Datasheet") "https://www.lcsc.com/datasheet/lcsc_datasheet_2206010116_UNI-ROYAL-Uniroyal-Elec-0603WAF3300T5E_C23138.pdf")
        (field (name "Description") "100mW Thick Film Resistors 75V ±100ppm/°C ±1% 330Ω 0603 Chip Resistor - Surface Mount ROHS"))
      (libsource (lib "PCM_JLCPCB-Resistors") (part "0603,330Ω") (description "100mW Thick Film Resistors 75V ±100ppm/°C ±1% 330Ω 0603 Chip Resistor - Surface Mount ROHS"))
      (property (name "LCSC") (value "C23138"))
      (property (name "Peak Wavelength") (value ""))
      (property (name "Stock") (value "2977706"))
      (property (name "Price") (value "0.004USD"))
      (property (name "Process") (value "SMT"))
      (property (name "Minimum Qty") (value "20"))
      (property (name "Attrition Qty") (value "10"))
      (property (name "Class") (value "Basic Component"))
      (property (name "Category") (value "Resistors,Chip Resistor - Surface Mount"))
      (property (name "Manufacturer") (value "UNI-ROYAL(Uniroyal Elec)"))
      (property (name "Part") (value "0603WAF3300T5E"))
      (property (name "Resistance") (value "330Ω"))
      (property (name "Power(Watts)") (value "100mW"))
      (property (name "Type") (value "Thick Film Resistors"))
      (property (name "Overload Voltage (Max)") (value "75V"))
      (property (name "Operating Temperature Range") (value "-55°C~+155°C"))
      (property (name "Tolerance") (value "±1%"))
      (property (name "Temperature Coefficient") (value "±100ppm/°C"))
      (property (name "Sheetname") (value "Root"))
      (property (name "Sheetfile") (value "Pico_Development_Stack.kicad_sch"))
      (property (name "ki_fp_filters") (value "R_*"))
      (sheetpath (names "/") (tstamps "/"))
      (tstamps "9128b2c5-5def-43a5-a5c5-41d1fca0bd1f"))
    (comp (ref "R47")
      (value "330")
      (footprint "PCM_JLCPCB:R_0603")
      (datasheet "https://www.lcsc.com/datasheet/lcsc_datasheet_2206010116_UNI-ROYAL-Uniroyal-Elec-0603WAF3300T5E_C23138.pdf")
      (description "100mW Thick Film Resistors 75V ±100ppm/°C ±1% 330Ω 0603 Chip Resistor - Surface Mount ROHS")
      (fields
        (field (name "LCSC") "C23138")
        (field (name "Peak Wavelength"))
        (field (name "Stock") "2977706")
        (field (name "Price") "0.004USD")
        (field (name "Process") "SMT")
        (field (name "Minimum Qty") "20")
        (field (name "Attrition Qty") "10")
        (field (name "Class") "Basic Component")
        (field (name "Category") "Resistors,Chip Resistor - Surface Mount")
        (field (name "Manufacturer") "UNI-ROYAL(Uniroyal Elec)")
        (field (name "Part") "0603WAF3300T5E")
        (field (name "Resistance") "330Ω")
        (field (name "Power(Watts)") "100mW")
        (field (name "Type") "Thick Film Resistors")
        (field (name "Overload Voltage (Max)") "75V")
        (field (name "Operating Temperature Range") "-55°C~+155°C")
        (field (name "Tolerance") "±1%")
        (field (name "Temperature Coefficient") "±100ppm/°C")
        (field (name "Footprint") "PCM_JLCPCB:R_0603")
        (field (name "Datasheet") "https://www.lcsc.com/datasheet/lcsc_datasheet_2206010116_UNI-ROYAL-Uniroyal-Elec-0603WAF3300T5E_C23138.pdf")
        (field (name "Description") "100mW Thick Film Resistors 75V ±100ppm/°C ±1% 330Ω 0603 Chip Resistor - Surface Mount ROHS"))
      (libsource (lib "PCM_JLCPCB-Resistors") (part "0603,330Ω") (description "100mW Thick Film Resistors 75V ±100ppm/°C ±1% 330Ω 0603 Chip Resistor - Surface Mount ROHS"))
      (property (name "LCSC") (value "C23138"))
      (property (name "Peak Wavelength") (value ""))
      (property (name "Stock") (value "2977706"))
      (property (name "Price") (value "0.004USD"))
      (property (name "Process") (value "SMT"))
      (property (name "Minimum Qty") (value "20"))
      (property (name "Attrition Qty") (value "10"))
      (property (name "Class") (value "Basic Component"))
      (property (name "Category") (value "Resistors,Chip Resistor - Surface Mount"))
      (property (name "Manufacturer") (value "UNI-ROYAL(Uniroyal Elec)"))
      (property (name "Part") (value "0603WAF3300T5E"))
      (property (name "Resistance") (value "330Ω"))
      (property (name "Power(Watts)") (value "100mW"))
      (property (name "Type") (value "Thick Film Resistors"))
      (property (name "Overload Voltage (Max)") (value "75V"))
      (property (name "Operating Temperature Range") (value "-55°C~+155°C"))
      (property (name "Tolerance") (value "±1%"))
      (property (name "Temperature Coefficient") (value "±100ppm/°C"))
      (property (name "Sheetname") (value "Root"))
      (property (name "Sheetfile") (value "Pico_Development_Stack.kicad_sch"))
      (property (name "ki_fp_filters") (value "R_*"))
      (sheetpath (names "/") (tstamps "/"))
      (tstamps "39ed282a-1905-4ecf-b8d2-39cdcf5825dc"))
    (comp (ref "R48")
      (value "1k")
      (footprint "PCM_JLCPCB:R_0603")
      (datasheet "https://www.lcsc.com/datasheet/lcsc_datasheet_2206010130_UNI-ROYAL-Uniroyal-Elec-0603WAF1001T5E_C21190.pdf")
      (description "100mW Thick Film Resistors 75V ±100ppm/°C ±1% 1kΩ 0603 Chip Resistor - Surface Mount ROHS")
      (fields
        (field (name "Digi-Key Part Number"))
        (field (name "MPN") "RC0402FR-071KL")
        (field (name "Manufacturer") "UNI-ROYAL(Uniroyal Elec)")
        (field (name "Supplier") "LCSC")
        (field (name "LCSC") "C21190")
        (field (name "Attrition Qty") "10")
        (field (name "Capacitance"))
        (field (name "Category") "Resistors,Chip Resistor - Surface Mount")
        (field (name "Class") "Basic Component")
        (field (name "Minimum Qty") "20")
        (field (name "Part") "0603WAF1001T5E")
        (field (name "Price") "0.004USD")
        (field (name "Process") "SMT")
        (field (name "Stock") "27538425")
        (field (name "Temperature Coefficient") "±100ppm/°C")
        (field (name "Tolerance") "±1%")
        (field (name "Voltage Rated"))
        (field (name "Peak Wavelength"))
        (field (name "Resistance") "1kΩ")
        (field (name "Power(Watts)") "100mW")
        (field (name "Type") "Thick Film Resistors")
        (field (name "Overload Voltage (Max)") "75V")
        (field (name "Operating Temperature Range") "-55°C~+155°C")
        (field (name "Footprint") "PCM_JLCPCB:R_0603")
        (field (name "Datasheet") "https://www.lcsc.com/datasheet/lcsc_datasheet_2206010130_UNI-ROYAL-Uniroyal-Elec-0603WAF1001T5E_C21190.pdf")
        (field (name "Description") "100mW Thick Film Resistors 75V ±100ppm/°C ±1% 1kΩ 0603 Chip Resistor - Surface Mount ROHS"))
      (libsource (lib "PCM_JLCPCB-Resistors") (part "0603,1kΩ") (description "100mW Thick Film Resistors 75V ±100ppm/°C ±1% 1kΩ 0603 Chip Resistor - Surface Mount ROHS"))
      (property (name "Digi-Key Part Number") (value ""))
      (property (name "MPN") (value "RC0402FR-071KL"))
      (property (name "Manufacturer") (value "UNI-ROYAL(Uniroyal Elec)"))
      (property (name "Supplier") (value "LCSC"))
      (property (name "LCSC") (value "C21190"))
      (property (name "Attrition Qty") (value "10"))
      (property (name "Capacitance") (value ""))
      (property (name "Category") (value "Resistors,Chip Resistor - Surface Mount"))
      (property (name "Class") (value "Basic Component"))
      (property (name "Minimum Qty") (value "20"))
      (property (name "Part") (value "0603WAF1001T5E"))
      (property (name "Price") (value "0.004USD"))
      (property (name "Process") (value "SMT"))
      (property (name "Stock") (value "27538425"))
      (property (name "Temperature Coefficient") (value "±100ppm/°C"))
      (property (name "Tolerance") (value "±1%"))
      (property (name "Voltage Rated") (value ""))
      (property (name "Peak Wavelength") (value ""))
      (property (name "Resistance") (value "1kΩ"))
      (property (name "Power(Watts)") (value "100mW"))
      (property (name "Type") (value "Thick Film Resistors"))
      (property (name "Overload Voltage (Max)") (value "75V"))
      (property (name "Operating Temperature Range") (value "-55°C~+155°C"))
      (property (name "Sheetname") (value "Root"))
      (property (name "Sheetfile") (value "Pico_Development_Stack.kicad_sch"))
      (property (name "ki_fp_filters") (value "R_*"))
      (sheetpath (names "/") (tstamps "/"))
      (tstamps "3a34afe7-0e49-4f26-9235-6007baead282"))
    (comp (ref "R49")
      (value "330")
      (footprint "PCM_JLCPCB:R_0603")
      (datasheet "https://www.lcsc.com/datasheet/lcsc_datasheet_2206010116_UNI-ROYAL-Uniroyal-Elec-0603WAF3300T5E_C23138.pdf")
      (description "100mW Thick Film Resistors 75V ±100ppm/°C ±1% 330Ω 0603 Chip Resistor - Surface Mount ROHS")
      (fields
        (field (name "LCSC") "C23138")
        (field (name "Peak Wavelength"))
        (field (name "Stock") "2977706")
        (field (name "Price") "0.004USD")
        (field (name "Process") "SMT")
        (field (name "Minimum Qty") "20")
        (field (name "Attrition Qty") "10")
        (field (name "Class") "Basic Component")
        (field (name "Category") "Resistors,Chip Resistor - Surface Mount")
        (field (name "Manufacturer") "UNI-ROYAL(Uniroyal Elec)")
        (field (name "Part") "0603WAF3300T5E")
        (field (name "Resistance") "330Ω")
        (field (name "Power(Watts)") "100mW")
        (field (name "Type") "Thick Film Resistors")
        (field (name "Overload Voltage (Max)") "75V")
        (field (name "Operating Temperature Range") "-55°C~+155°C")
        (field (name "Tolerance") "±1%")
        (field (name "Temperature Coefficient") "±100ppm/°C")
        (field (name "Footprint") "PCM_JLCPCB:R_0603")
        (field (name "Datasheet") "https://www.lcsc.com/datasheet/lcsc_datasheet_2206010116_UNI-ROYAL-Uniroyal-Elec-0603WAF3300T5E_C23138.pdf")
        (field (name "Description") "100mW Thick Film Resistors 75V ±100ppm/°C ±1% 330Ω 0603 Chip Resistor - Surface Mount ROHS"))
      (libsource (lib "PCM_JLCPCB-Resistors") (part "0603,330Ω") (description "100mW Thick Film Resistors 75V ±100ppm/°C ±1% 330Ω 0603 Chip Resistor - Surface Mount ROHS"))
      (property (name "LCSC") (value "C23138"))
      (property (name "Peak Wavelength") (value ""))
      (property (name "Stock") (value "2977706"))
      (property (name "Price") (value "0.004USD"))
      (property (name "Process") (value "SMT"))
      (property (name "Minimum Qty") (value "20"))
      (property (name "Attrition Qty") (value "10"))
      (property (name "Class") (value "Basic Component"))
      (property (name "Category") (value "Resistors,Chip Resistor - Surface Mount"))
      (property (name "Manufacturer") (value "UNI-ROYAL(Uniroyal Elec)"))
      (property (name "Part") (value "0603WAF3300T5E"))
      (property (name "Resistance") (value "330Ω"))
      (property (name "Power(Watts)") (value "100mW"))
      (property (name "Type") (value "Thick Film Resistors"))
      (property (name "Overload Voltage (Max)") (value "75V"))
      (property (name "Operating Temperature Range") (value "-55°C~+155°C"))
      (property (name "Tolerance") (value "±1%"))
      (property (name "Temperature Coefficient") (value "±100ppm/°C"))
      (property (name "Sheetname") (value "Root"))
      (property (name "Sheetfile") (value "Pico_Development_Stack.kicad_sch"))
      (property (name "ki_fp_filters") (value "R_*"))
      (sheetpath (names "/") (tstamps "/"))
      (tstamps "56620c97-b00d-4013-9122-6be8fcd2b3c7"))
    (comp (ref "R50")
      (value "330")
      (footprint "PCM_JLCPCB:R_0603")
      (datasheet "https://www.lcsc.com/datasheet/lcsc_datasheet_2206010116_UNI-ROYAL-Uniroyal-Elec-0603WAF3300T5E_C23138.pdf")
      (description "100mW Thick Film Resistors 75V ±100ppm/°C ±1% 330Ω 0603 Chip Resistor - Surface Mount ROHS")
      (fields
        (field (name "LCSC") "C23138")
        (field (name "Peak Wavelength"))
        (field (name "Stock") "2977706")
        (field (name "Price") "0.004USD")
        (field (name "Process") "SMT")
        (field (name "Minimum Qty") "20")
        (field (name "Attrition Qty") "10")
        (field (name "Class") "Basic Component")
        (field (name "Category") "Resistors,Chip Resistor - Surface Mount")
        (field (name "Manufacturer") "UNI-ROYAL(Uniroyal Elec)")
        (field (name "Part") "0603WAF3300T5E")
        (field (name "Resistance") "330Ω")
        (field (name "Power(Watts)") "100mW")
        (field (name "Type") "Thick Film Resistors")
        (field (name "Overload Voltage (Max)") "75V")
        (field (name "Operating Temperature Range") "-55°C~+155°C")
        (field (name "Tolerance") "±1%")
        (field (name "Temperature Coefficient") "±100ppm/°C")
        (field (name "Footprint") "PCM_JLCPCB:R_0603")
        (field (name "Datasheet") "https://www.lcsc.com/datasheet/lcsc_datasheet_2206010116_UNI-ROYAL-Uniroyal-Elec-0603WAF3300T5E_C23138.pdf")
        (field (name "Description") "100mW Thick Film Resistors 75V ±100ppm/°C ±1% 330Ω 0603 Chip Resistor - Surface Mount ROHS"))
      (libsource (lib "PCM_JLCPCB-Resistors") (part "0603,330Ω") (description "100mW Thick Film Resistors 75V ±100ppm/°C ±1% 330Ω 0603 Chip Resistor - Surface Mount ROHS"))
      (property (name "LCSC") (value "C23138"))
      (property (name "Peak Wavelength") (value ""))
      (property (name "Stock") (value "2977706"))
      (property (name "Price") (value "0.004USD"))
      (property (name "Process") (value "SMT"))
      (property (name "Minimum Qty") (value "20"))
      (property (name "Attrition Qty") (value "10"))
      (property (name "Class") (value "Basic Component"))
      (property (name "Category") (value "Resistors,Chip Resistor - Surface Mount"))
      (property (name "Manufacturer") (value "UNI-ROYAL(Uniroyal Elec)"))
      (property (name "Part") (value "0603WAF3300T5E"))
      (property (name "Resistance") (value "330Ω"))
      (property (name "Power(Watts)") (value "100mW"))
      (property (name "Type") (value "Thick Film Resistors"))
      (property (name "Overload Voltage (Max)") (value "75V"))
      (property (name "Operating Temperature Range") (value "-55°C~+155°C"))
      (property (name "Tolerance") (value "±1%"))
      (property (name "Temperature Coefficient") (value "±100ppm/°C"))
      (property (name "Sheetname") (value "Root"))
      (property (name "Sheetfile") (value "Pico_Development_Stack.kicad_sch"))
      (property (name "ki_fp_filters") (value "R_*"))
      (sheetpath (names "/") (tstamps "/"))
      (tstamps "5c2d3928-94f4-4651-b206-db306eaedee9"))
    (comp (ref "R51")
      (value "330")
      (footprint "PCM_JLCPCB:R_0603")
      (datasheet "https://www.lcsc.com/datasheet/lcsc_datasheet_2206010116_UNI-ROYAL-Uniroyal-Elec-0603WAF3300T5E_C23138.pdf")
      (description "100mW Thick Film Resistors 75V ±100ppm/°C ±1% 330Ω 0603 Chip Resistor - Surface Mount ROHS")
      (fields
        (field (name "LCSC") "C23138")
        (field (name "Peak Wavelength"))
        (field (name "Stock") "2977706")
        (field (name "Price") "0.004USD")
        (field (name "Process") "SMT")
        (field (name "Minimum Qty") "20")
        (field (name "Attrition Qty") "10")
        (field (name "Class") "Basic Component")
        (field (name "Category") "Resistors,Chip Resistor - Surface Mount")
        (field (name "Manufacturer") "UNI-ROYAL(Uniroyal Elec)")
        (field (name "Part") "0603WAF3300T5E")
        (field (name "Resistance") "330Ω")
        (field (name "Power(Watts)") "100mW")
        (field (name "Type") "Thick Film Resistors")
        (field (name "Overload Voltage (Max)") "75V")
        (field (name "Operating Temperature Range") "-55°C~+155°C")
        (field (name "Tolerance") "±1%")
        (field (name "Temperature Coefficient") "±100ppm/°C")
        (field (name "Footprint") "PCM_JLCPCB:R_0603")
        (field (name "Datasheet") "https://www.lcsc.com/datasheet/lcsc_datasheet_2206010116_UNI-ROYAL-Uniroyal-Elec-0603WAF3300T5E_C23138.pdf")
        (field (name "Description") "100mW Thick Film Resistors 75V ±100ppm/°C ±1% 330Ω 0603 Chip Resistor - Surface Mount ROHS"))
      (libsource (lib "PCM_JLCPCB-Resistors") (part "0603,330Ω") (description "100mW Thick Film Resistors 75V ±100ppm/°C ±1% 330Ω 0603 Chip Resistor - Surface Mount ROHS"))
      (property (name "LCSC") (value "C23138"))
      (property (name "Peak Wavelength") (value ""))
      (property (name "Stock") (value "2977706"))
      (property (name "Price") (value "0.004USD"))
      (property (name "Process") (value "SMT"))
      (property (name "Minimum Qty") (value "20"))
      (property (name "Attrition Qty") (value "10"))
      (property (name "Class") (value "Basic Component"))
      (property (name "Category") (value "Resistors,Chip Resistor - Surface Mount"))
      (property (name "Manufacturer") (value "UNI-ROYAL(Uniroyal Elec)"))
      (property (name "Part") (value "0603WAF3300T5E"))
      (property (name "Resistance") (value "330Ω"))
      (property (name "Power(Watts)") (value "100mW"))
      (property (name "Type") (value "Thick Film Resistors"))
      (property (name "Overload Voltage (Max)") (value "75V"))
      (property (name "Operating Temperature Range") (value "-55°C~+155°C"))
      (property (name "Tolerance") (value "±1%"))
      (property (name "Temperature Coefficient") (value "±100ppm/°C"))
      (property (name "Sheetname") (value "Root"))
      (property (name "Sheetfile") (value "Pico_Development_Stack.kicad_sch"))
      (property (name "ki_fp_filters") (value "R_*"))
      (sheetpath (names "/") (tstamps "/"))
      (tstamps "8e66a538-1706-447e-bcff-479e58d08f94"))
    (comp (ref "R52")
      (value "100")
      (footprint "PCM_JLCPCB:R_0603")
      (datasheet "https://www.lcsc.com/datasheet/lcsc_datasheet_2411221126_UNI-ROYAL-Uniroyal-Elec-0603WAF1000T5E_C22775.pdf")
      (description "100mW Thick Film Resistors 75V ±1% ±200ppm/°C 100Ω 0603 Chip Resistor - Surface Mount ROHS")
      (fields
        (field (name "Digi-Key Part Number"))
        (field (name "MPN") "RC0402FR-07100RL")
        (field (name "Manufacturer") "UNI-ROYAL(Uniroyal Elec)")
        (field (name "Supplier") "LCSC")
        (field (name "LCSC") "C22775")
        (field (name "Attrition Qty") "10")
        (field (name "Capacitance"))
        (field (name "Category") "Resistors,Chip Resistor - Surface Mount")
        (field (name "Class") "Basic Component")
        (field (name "Minimum Qty") "20")
        (field (name "Part") "0603WAF1000T5E")
        (field (name "Price") "0.004USD")
        (field (name "Process") "SMT")
        (field (name "Stock") "8202320")
        (field (name "Temperature Coefficient") "±200ppm/°C")
        (field (name "Tolerance") "±1%")
        (field (name "Voltage Rated"))
        (field (name "Peak Wavelength"))
        (field (name "Resistance") "100Ω")
        (field (name "Power(Watts)") "100mW")
        (field (name "Type") "Thick Film Resistors")
        (field (name "Overload Voltage (Max)") "75V")
        (field (name "Operating Temperature Range") "-55°C~+155°C")
        (field (name "Footprint") "PCM_JLCPCB:R_0603")
        (field (name "Datasheet") "https://www.lcsc.com/datasheet/lcsc_datasheet_2411221126_UNI-ROYAL-Uniroyal-Elec-0603WAF1000T5E_C22775.pdf")
        (field (name "Description") "100mW Thick Film Resistors 75V ±1% ±200ppm/°C 100Ω 0603 Chip Resistor - Surface Mount ROHS"))
      (libsource (lib "PCM_JLCPCB-Resistors") (part "0603,100Ω") (description "100mW Thick Film Resistors 75V ±1% ±200ppm/°C 100Ω 0603 Chip Resistor - Surface Mount ROHS"))
      (property (name "Digi-Key Part Number") (value ""))
      (property (name "MPN") (value "RC0402FR-07100RL"))
      (property (name "Manufacturer") (value "UNI-ROYAL(Uniroyal Elec)"))
      (property (name "Supplier") (value "LCSC"))
      (property (name "LCSC") (value "C22775"))
      (property (name "Attrition Qty") (value "10"))
      (property (name "Capacitance") (value ""))
      (property (name "Category") (value "Resistors,Chip Resistor - Surface Mount"))
      (property (name "Class") (value "Basic Component"))
      (property (name "Minimum Qty") (value "20"))
      (property (name "Part") (value "0603WAF1000T5E"))
      (property (name "Price") (value "0.004USD"))
      (property (name "Process") (value "SMT"))
      (property (name "Stock") (value "8202320"))
      (property (name "Temperature Coefficient") (value "±200ppm/°C"))
      (property (name "Tolerance") (value "±1%"))
      (property (name "Voltage Rated") (value ""))
      (property (name "Peak Wavelength") (value ""))
      (property (name "Resistance") (value "100Ω"))
      (property (name "Power(Watts)") (value "100mW"))
      (property (name "Type") (value "Thick Film Resistors"))
      (property (name "Overload Voltage (Max)") (value "75V"))
      (property (name "Operating Temperature Range") (value "-55°C~+155°C"))
      (property (name "Sheetname") (value "Root"))
      (property (name "Sheetfile") (value "Pico_Development_Stack.kicad_sch"))
      (property (name "ki_fp_filters") (value "R_*"))
      (sheetpath (names "/") (tstamps "/"))
      (tstamps "2e5dd723-1de2-4b85-a052-7bccd4e049a0"))
    (comp (ref "R53")
      (value "10kΩ")
      (footprint "PCM_JLCPCB:R_0603")
      (datasheet "https://www.lcsc.com/datasheet/lcsc_datasheet_2206010045_UNI-ROYAL-Uniroyal-Elec-0603WAF1002T5E_C25804.pdf")
      (description "100mW Thick Film Resistors 75V ±100ppm/°C ±1% 10kΩ 0603 Chip Resistor - Surface Mount ROHS")
      (fields
        (field (name "LCSC") "C25804")
        (field (name "Stock") "51181774")
        (field (name "Price") "0.004USD")
        (field (name "Process") "SMT")
        (field (name "Minimum Qty") "20")
        (field (name "Attrition Qty") "10")
        (field (name "Class") "Basic Component")
        (field (name "Category") "Resistors,Chip Resistor - Surface Mount")
        (field (name "Manufacturer") "UNI-ROYAL(Uniroyal Elec)")
        (field (name "Part") "0603WAF1002T5E")
        (field (name "Resistance") "10kΩ")
        (field (name "Power(Watts)") "100mW")
        (field (name "Type") "Thick Film Resistors")
        (field (name "Overload Voltage (Max)") "75V")
        (field (name "Operating Temperature Range") "-55°C~+155°C")
        (field (name "Tolerance") "±1%")
        (field (name "Temperature Coefficient") "±100ppm/°C")
        (field (name "Footprint") "PCM_JLCPCB:R_0603")
        (field (name "Datasheet") "https://www.lcsc.com/datasheet/lcsc_datasheet_2206010045_UNI-ROYAL-Uniroyal-Elec-0603WAF1002T5E_C25804.pdf")
        (field (name "Description") "100mW Thick Film Resistors 75V ±100ppm/°C ±1% 10kΩ 0603 Chip Resistor - Surface Mount ROHS"))
      (libsource (lib "PCM_JLCPCB-Resistors") (part "0603,10kΩ") (description "100mW Thick Film Resistors 75V ±100ppm/°C ±1% 10kΩ 0603 Chip Resistor - Surface Mount ROHS"))
      (property (name "LCSC") (value "C25804"))
      (property (name "Stock") (value "51181774"))
      (property (name "Price") (value "0.004USD"))
      (property (name "Process") (value "SMT"))
      (property (name "Minimum Qty") (value "20"))
      (property (name "Attrition Qty") (value "10"))
      (property (name "Class") (value "Basic Component"))
      (property (name "Category") (value "Resistors,Chip Resistor - Surface Mount"))
      (property (name "Manufacturer") (value "UNI-ROYAL(Uniroyal Elec)"))
      (property (name "Part") (value "0603WAF1002T5E"))
      (property (name "Resistance") (value "10kΩ"))
      (property (name "Power(Watts)") (value "100mW"))
      (property (name "Type") (value "Thick Film Resistors"))
      (property (name "Overload Voltage (Max)") (value "75V"))
      (property (name "Operating Temperature Range") (value "-55°C~+155°C"))
      (property (name "Tolerance") (value "±1%"))
      (property (name "Temperature Coefficient") (value "±100ppm/°C"))
      (property (name "Sheetname") (value "Root"))
      (property (name "Sheetfile") (value "Pico_Development_Stack.kicad_sch"))
      (property (name "ki_fp_filters") (value "R_*"))
      (sheetpath (names "/") (tstamps "/"))
      (tstamps "74fae7a1-4fd3-46dd-a594-f1103a0fc8c2"))
    (comp (ref "R54")
      (value "10kΩ")
      (footprint "PCM_JLCPCB:R_0603")
      (datasheet "https://www.lcsc.com/datasheet/lcsc_datasheet_2206010045_UNI-ROYAL-Uniroyal-Elec-0603WAF1002T5E_C25804.pdf")
      (description "100mW Thick Film Resistors 75V ±100ppm/°C ±1% 10kΩ 0603 Chip Resistor - Surface Mount ROHS")
      (fields
        (field (name "LCSC") "C25804")
        (field (name "Stock") "51181774")
        (field (name "Price") "0.004USD")
        (field (name "Process") "SMT")
        (field (name "Minimum Qty") "20")
        (field (name "Attrition Qty") "10")
        (field (name "Class") "Basic Component")
        (field (name "Category") "Resistors,Chip Resistor - Surface Mount")
        (field (name "Manufacturer") "UNI-ROYAL(Uniroyal Elec)")
        (field (name "Part") "0603WAF1002T5E")
        (field (name "Resistance") "10kΩ")
        (field (name "Power(Watts)") "100mW")
        (field (name "Type") "Thick Film Resistors")
        (field (name "Overload Voltage (Max)") "75V")
        (field (name "Operating Temperature Range") "-55°C~+155°C")
        (field (name "Tolerance") "±1%")
        (field (name "Temperature Coefficient") "±100ppm/°C")
        (field (name "Footprint") "PCM_JLCPCB:R_0603")
        (field (name "Datasheet") "https://www.lcsc.com/datasheet/lcsc_datasheet_2206010045_UNI-ROYAL-Uniroyal-Elec-0603WAF1002T5E_C25804.pdf")
        (field (name "Description") "100mW Thick Film Resistors 75V ±100ppm/°C ±1% 10kΩ 0603 Chip Resistor - Surface Mount ROHS"))
      (libsource (lib "PCM_JLCPCB-Resistors") (part "0603,10kΩ") (description "100mW Thick Film Resistors 75V ±100ppm/°C ±1% 10kΩ 0603 Chip Resistor - Surface Mount ROHS"))
      (property (name "LCSC") (value "C25804"))
      (property (name "Stock") (value "51181774"))
      (property (name "Price") (value "0.004USD"))
      (property (name "Process") (value "SMT"))
      (property (name "Minimum Qty") (value "20"))
      (property (name "Attrition Qty") (value "10"))
      (property (name "Class") (value "Basic Component"))
      (property (name "Category") (value "Resistors,Chip Resistor - Surface Mount"))
      (property (name "Manufacturer") (value "UNI-ROYAL(Uniroyal Elec)"))
      (property (name "Part") (value "0603WAF1002T5E"))
      (property (name "Resistance") (value "10kΩ"))
      (property (name "Power(Watts)") (value "100mW"))
      (property (name "Type") (value "Thick Film Resistors"))
      (property (name "Overload Voltage (Max)") (value "75V"))
      (property (name "Operating Temperature Range") (value "-55°C~+155°C"))
      (property (name "Tolerance") (value "±1%"))
      (property (name "Temperature Coefficient") (value "±100ppm/°C"))
      (property (name "Sheetname") (value "Root"))
      (property (name "Sheetfile") (value "Pico_Development_Stack.kicad_sch"))
      (property (name "ki_fp_filters") (value "R_*"))
      (sheetpath (names "/") (tstamps "/"))
      (tstamps "84eadd09-9af2-487b-9a18-5d13d97623d8"))
    (comp (ref "R56")
      (value "100kΩ")
      (footprint "PCM_JLCPCB:R_0603")
      (datasheet "https://www.lcsc.com/datasheet/lcsc_datasheet_2206010045_UNI-ROYAL-Uniroyal-Elec-0603WAF1003T5E_C25803.pdf")
      (description "100mW Thick Film Resistors 75V ±100ppm/°C ±1% 100kΩ 0603 Chip Resistor - Surface Mount ROHS")
      (fields
        (field (name "LCSC") "C25803")
        (field (name "Stock") "7820113")
        (field (name "Price") "0.004USD")
        (field (name "Process") "SMT")
        (field (name "Minimum Qty") "20")
        (field (name "Attrition Qty") "10")
        (field (name "Class") "Basic Component")
        (field (name "Category") "Resistors,Chip Resistor - Surface Mount")
        (field (name "Manufacturer") "UNI-ROYAL(Uniroyal Elec)")
        (field (name "Part") "0603WAF1003T5E")
        (field (name "Resistance") "100kΩ")
        (field (name "Power(Watts)") "100mW")
        (field (name "Type") "Thick Film Resistors")
        (field (name "Overload Voltage (Max)") "75V")
        (field (name "Operating Temperature Range") "-55°C~+155°C")
        (field (name "Tolerance") "±1%")
        (field (name "Temperature Coefficient") "±100ppm/°C")
        (field (name "Footprint") "PCM_JLCPCB:R_0603")
        (field (name "Datasheet") "https://www.lcsc.com/datasheet/lcsc_datasheet_2206010045_UNI-ROYAL-Uniroyal-Elec-0603WAF1003T5E_C25803.pdf")
        (field (name "Description") "100mW Thick Film Resistors 75V ±100ppm/°C ±1% 100kΩ 0603 Chip Resistor - Surface Mount ROHS"))
      (libsource (lib "PCM_JLCPCB-Resistors") (part "0603,100kΩ") (description "100mW Thick Film Resistors 75V ±100ppm/°C ±1% 100kΩ 0603 Chip Resistor - Surface Mount ROHS"))
      (property (name "LCSC") (value "C25803"))
      (property (name "Stock") (value "7820113"))
      (property (name "Price") (value "0.004USD"))
      (property (name "Process") (value "SMT"))
      (property (name "Minimum Qty") (value "20"))
      (property (name "Attrition Qty") (value "10"))
      (property (name "Class") (value "Basic Component"))
      (property (name "Category") (value "Resistors,Chip Resistor - Surface Mount"))
      (property (name "Manufacturer") (value "UNI-ROYAL(Uniroyal Elec)"))
      (property (name "Part") (value "0603WAF1003T5E"))
      (property (name "Resistance") (value "100kΩ"))
      (property (name "Power(Watts)") (value "100mW"))
      (property (name "Type") (value "Thick Film Resistors"))
      (property (name "Overload Voltage (Max)") (value "75V"))
      (property (name "Operating Temperature Range") (value "-55°C~+155°C"))
      (property (name "Tolerance") (value "±1%"))
      (property (name "Temperature Coefficient") (value "±100ppm/°C"))
      (property (name "Sheetname") (value "Root"))
      (property (name "Sheetfile") (value "Pico_Development_Stack.kicad_sch"))
      (property (name "ki_fp_filters") (value "R_*"))
      (sheetpath (names "/") (tstamps "/"))
      (tstamps "c8b09ba1-5a5e-463b-86b2-13da67ca0680"))
    (comp (ref "R57")
      (value "22")
      (footprint "PCM_JLCPCB:R_0603")
      (datasheet "https://www.lcsc.com/datasheet/lcsc_datasheet_2206010100_UNI-ROYAL-Uniroyal-Elec-0603WAF220JT5E_C23345.pdf")
      (description "100mW Thick Film Resistors 75V ±100ppm/°C ±1% 22Ω 0603 Chip Resistor - Surface Mount ROHS")
      (fields
        (field (name "Digi-Key Part Number"))
        (field (name "MPN") "RC0402FR-0727RL")
        (field (name "Manufacturer") "UNI-ROYAL(Uniroyal Elec)")
        (field (name "Supplier") "LCSC")
        (field (name "LCSC") "C23345")
        (field (name "Attrition Qty") "10")
        (field (name "Capacitance"))
        (field (name "Category") "Resistors,Chip Resistor - Surface Mount")
        (field (name "Class") "Basic Component")
        (field (name "Minimum Qty") "20")
        (field (name "Part") "0603WAF220JT5E")
        (field (name "Price") "0.004USD")
        (field (name "Process") "SMT")
        (field (name "Stock") "4414856")
        (field (name "Temperature Coefficient") "±100ppm/°C")
        (field (name "Tolerance") "±1%")
        (field (name "Voltage Rated"))
        (field (name "Peak Wavelength"))
        (field (name "Resistance") "22Ω")
        (field (name "Power(Watts)") "100mW")
        (field (name "Type") "Thick Film Resistors")
        (field (name "Overload Voltage (Max)") "75V")
        (field (name "Operating Temperature Range") "-55°C~+155°C")
        (field (name "Footprint") "PCM_JLCPCB:R_0603")
        (field (name "Datasheet") "https://www.lcsc.com/datasheet/lcsc_datasheet_2206010100_UNI-ROYAL-Uniroyal-Elec-0603WAF220JT5E_C23345.pdf")
        (field (name "Description") "100mW Thick Film Resistors 75V ±100ppm/°C ±1% 22Ω 0603 Chip Resistor - Surface Mount ROHS"))
      (libsource (lib "PCM_JLCPCB-Resistors") (part "0603,22Ω") (description "100mW Thick Film Resistors 75V ±100ppm/°C ±1% 22Ω 0603 Chip Resistor - Surface Mount ROHS"))
      (property (name "Digi-Key Part Number") (value ""))
      (property (name "MPN") (value "RC0402FR-0727RL"))
      (property (name "Manufacturer") (value "UNI-ROYAL(Uniroyal Elec)"))
      (property (name "Supplier") (value "LCSC"))
      (property (name "LCSC") (value "C23345"))
      (property (name "Attrition Qty") (value "10"))
      (property (name "Capacitance") (value ""))
      (property (name "Category") (value "Resistors,Chip Resistor - Surface Mount"))
      (property (name "Class") (value "Basic Component"))
      (property (name "Minimum Qty") (value "20"))
      (property (name "Part") (value "0603WAF220JT5E"))
      (property (name "Price") (value "0.004USD"))
      (property (name "Process") (value "SMT"))
      (property (name "Stock") (value "4414856"))
      (property (name "Temperature Coefficient") (value "±100ppm/°C"))
      (property (name "Tolerance") (value "±1%"))
      (property (name "Voltage Rated") (value ""))
      (property (name "Peak Wavelength") (value ""))
      (property (name "Resistance") (value "22Ω"))
      (property (name "Power(Watts)") (value "100mW"))
      (property (name "Type") (value "Thick Film Resistors"))
      (property (name "Overload Voltage (Max)") (value "75V"))
      (property (name "Operating Temperature Range") (value "-55°C~+155°C"))
      (property (name "Sheetname") (value "Root"))
      (property (name "Sheetfile") (value "Pico_Development_Stack.kicad_sch"))
      (property (name "ki_fp_filters") (value "R_*"))
      (sheetpath (names "/") (tstamps "/"))
      (tstamps "3217c41b-86d1-4041-98eb-ffb290e1153b"))
    (comp (ref "R58")
      (value "22")
      (footprint "PCM_JLCPCB:R_0603")
      (datasheet "https://www.lcsc.com/datasheet/lcsc_datasheet_2206010100_UNI-ROYAL-Uniroyal-Elec-0603WAF220JT5E_C23345.pdf")
      (description "100mW Thick Film Resistors 75V ±100ppm/°C ±1% 22Ω 0603 Chip Resistor - Surface Mount ROHS")
      (fields
        (field (name "Digi-Key Part Number"))
        (field (name "MPN") "RC0402FR-0727RL")
        (field (name "Manufacturer") "UNI-ROYAL(Uniroyal Elec)")
        (field (name "Supplier") "LCSC")
        (field (name "LCSC") "C23345")
        (field (name "Attrition Qty") "10")
        (field (name "Capacitance"))
        (field (name "Category") "Resistors,Chip Resistor - Surface Mount")
        (field (name "Class") "Basic Component")
        (field (name "Minimum Qty") "20")
        (field (name "Part") "0603WAF220JT5E")
        (field (name "Price") "0.004USD")
        (field (name "Process") "SMT")
        (field (name "Stock") "4414856")
        (field (name "Temperature Coefficient") "±100ppm/°C")
        (field (name "Tolerance") "±1%")
        (field (name "Voltage Rated"))
        (field (name "Peak Wavelength"))
        (field (name "Resistance") "22Ω")
        (field (name "Power(Watts)") "100mW")
        (field (name "Type") "Thick Film Resistors")
        (field (name "Overload Voltage (Max)") "75V")
        (field (name "Operating Temperature Range") "-55°C~+155°C")
        (field (name "Footprint") "PCM_JLCPCB:R_0603")
        (field (name "Datasheet") "https://www.lcsc.com/datasheet/lcsc_datasheet_2206010100_UNI-ROYAL-Uniroyal-Elec-0603WAF220JT5E_C23345.pdf")
        (field (name "Description") "100mW Thick Film Resistors 75V ±100ppm/°C ±1% 22Ω 0603 Chip Resistor - Surface Mount ROHS"))
      (libsource (lib "PCM_JLCPCB-Resistors") (part "0603,22Ω") (description "100mW Thick Film Resistors 75V ±100ppm/°C ±1% 22Ω 0603 Chip Resistor - Surface Mount ROHS"))
      (property (name "Digi-Key Part Number") (value ""))
      (property (name "MPN") (value "RC0402FR-0727RL"))
      (property (name "Manufacturer") (value "UNI-ROYAL(Uniroyal Elec)"))
      (property (name "Supplier") (value "LCSC"))
      (property (name "LCSC") (value "C23345"))
      (property (name "Attrition Qty") (value "10"))
      (property (name "Capacitance") (value ""))
      (property (name "Category") (value "Resistors,Chip Resistor - Surface Mount"))
      (property (name "Class") (value "Basic Component"))
      (property (name "Minimum Qty") (value "20"))
      (property (name "Part") (value "0603WAF220JT5E"))
      (property (name "Price") (value "0.004USD"))
      (property (name "Process") (value "SMT"))
      (property (name "Stock") (value "4414856"))
      (property (name "Temperature Coefficient") (value "±100ppm/°C"))
      (property (name "Tolerance") (value "±1%"))
      (property (name "Voltage Rated") (value ""))
      (property (name "Peak Wavelength") (value ""))
      (property (name "Resistance") (value "22Ω"))
      (property (name "Power(Watts)") (value "100mW"))
      (property (name "Type") (value "Thick Film Resistors"))
      (property (name "Overload Voltage (Max)") (value "75V"))
      (property (name "Operating Temperature Range") (value "-55°C~+155°C"))
      (property (name "Sheetname") (value "Root"))
      (property (name "Sheetfile") (value "Pico_Development_Stack.kicad_sch"))
      (property (name "ki_fp_filters") (value "R_*"))
      (sheetpath (names "/") (tstamps "/"))
      (tstamps "f6fb2368-6763-42c2-a594-5e6a53ce1f18"))
    (comp (ref "R59")
      (value "22kΩ")
      (footprint "PCM_JLCPCB:R_0603")
      (datasheet "https://www.lcsc.com/datasheet/lcsc_datasheet_2206010030_UNI-ROYAL-Uniroyal-Elec-0603WAF2202T5E_C31850.pdf")
      (description "100mW Thick Film Resistors 75V ±100ppm/°C ±1% 22kΩ 0603 Chip Resistor - Surface Mount ROHS")
      (fields
        (field (name "LCSC") "C31850")
        (field (name "Stock") "1601895")
        (field (name "Price") "0.004USD")
        (field (name "Process") "SMT")
        (field (name "Minimum Qty") "20")
        (field (name "Attrition Qty") "10")
        (field (name "Class") "Basic Component")
        (field (name "Category") "Resistors,Chip Resistor - Surface Mount")
        (field (name "Manufacturer") "UNI-ROYAL(Uniroyal Elec)")
        (field (name "Part") "0603WAF2202T5E")
        (field (name "Resistance") "22kΩ")
        (field (name "Power(Watts)") "100mW")
        (field (name "Type") "Thick Film Resistors")
        (field (name "Overload Voltage (Max)") "75V")
        (field (name "Operating Temperature Range") "-55°C~+155°C")
        (field (name "Tolerance") "±1%")
        (field (name "Temperature Coefficient") "±100ppm/°C")
        (field (name "Footprint") "PCM_JLCPCB:R_0603")
        (field (name "Datasheet") "https://www.lcsc.com/datasheet/lcsc_datasheet_2206010030_UNI-ROYAL-Uniroyal-Elec-0603WAF2202T5E_C31850.pdf")
        (field (name "Description") "100mW Thick Film Resistors 75V ±100ppm/°C ±1% 22kΩ 0603 Chip Resistor - Surface Mount ROHS"))
      (libsource (lib "PCM_JLCPCB-Resistors") (part "0603,22kΩ") (description "100mW Thick Film Resistors 75V ±100ppm/°C ±1% 22kΩ 0603 Chip Resistor - Surface Mount ROHS"))
      (property (name "LCSC") (value "C31850"))
      (property (name "Stock") (value "1601895"))
      (property (name "Price") (value "0.004USD"))
      (property (name "Process") (value "SMT"))
      (property (name "Minimum Qty") (value "20"))
      (property (name "Attrition Qty") (value "10"))
      (property (name "Class") (value "Basic Component"))
      (property (name "Category") (value "Resistors,Chip Resistor - Surface Mount"))
      (property (name "Manufacturer") (value "UNI-ROYAL(Uniroyal Elec)"))
      (property (name "Part") (value "0603WAF2202T5E"))
      (property (name "Resistance") (value "22kΩ"))
      (property (name "Power(Watts)") (value "100mW"))
      (property (name "Type") (value "Thick Film Resistors"))
      (property (name "Overload Voltage (Max)") (value "75V"))
      (property (name "Operating Temperature Range") (value "-55°C~+155°C"))
      (property (name "Tolerance") (value "±1%"))
      (property (name "Temperature Coefficient") (value "±100ppm/°C"))
      (property (name "Sheetname") (value "Root"))
      (property (name "Sheetfile") (value "Pico_Development_Stack.kicad_sch"))
      (property (name "ki_fp_filters") (value "R_*"))
      (sheetpath (names "/") (tstamps "/"))
      (tstamps "1999b5fe-0a9e-4902-be17-73e84caf3593"))
    (comp (ref "R60")
      (value "680Ω")
      (footprint "PCM_JLCPCB:R_0603")
      (datasheet "https://www.lcsc.com/datasheet/lcsc_datasheet_2206010100_UNI-ROYAL-Uniroyal-Elec-0603WAF6800T5E_C23228.pdf")
      (description "100mW Thick Film Resistors 75V ±100ppm/°C ±1% 680Ω 0603 Chip Resistor - Surface Mount ROHS")
      (fields
        (field (name "LCSC") "C23228")
        (field (name "Stock") "1146230")
        (field (name "Price") "0.004USD")
        (field (name "Process") "SMT")
        (field (name "Minimum Qty") "20")
        (field (name "Attrition Qty") "10")
        (field (name "Class") "Basic Component")
        (field (name "Category") "Resistors,Chip Resistor - Surface Mount")
        (field (name "Manufacturer") "UNI-ROYAL(Uniroyal Elec)")
        (field (name "Part") "0603WAF6800T5E")
        (field (name "Resistance") "680Ω")
        (field (name "Power(Watts)") "100mW")
        (field (name "Type") "Thick Film Resistors")
        (field (name "Overload Voltage (Max)") "75V")
        (field (name "Operating Temperature Range") "-55°C~+155°C")
        (field (name "Tolerance") "±1%")
        (field (name "Temperature Coefficient") "±100ppm/°C")
        (field (name "Footprint") "PCM_JLCPCB:R_0603")
        (field (name "Datasheet") "https://www.lcsc.com/datasheet/lcsc_datasheet_2206010100_UNI-ROYAL-Uniroyal-Elec-0603WAF6800T5E_C23228.pdf")
        (field (name "Description") "100mW Thick Film Resistors 75V ±100ppm/°C ±1% 680Ω 0603 Chip Resistor - Surface Mount ROHS"))
      (libsource (lib "PCM_JLCPCB-Resistors") (part "0603,680Ω") (description "100mW Thick Film Resistors 75V ±100ppm/°C ±1% 680Ω 0603 Chip Resistor - Surface Mount ROHS"))
      (property (name "LCSC") (value "C23228"))
      (property (name "Stock") (value "1146230"))
      (property (name "Price") (value "0.004USD"))
      (property (name "Process") (value "SMT"))
      (property (name "Minimum Qty") (value "20"))
      (property (name "Attrition Qty") (value "10"))
      (property (name "Class") (value "Basic Component"))
      (property (name "Category") (value "Resistors,Chip Resistor - Surface Mount"))
      (property (name "Manufacturer") (value "UNI-ROYAL(Uniroyal Elec)"))
      (property (name "Part") (value "0603WAF6800T5E"))
      (property (name "Resistance") (value "680Ω"))
      (property (name "Power(Watts)") (value "100mW"))
      (property (name "Type") (value "Thick Film Resistors"))
      (property (name "Overload Voltage (Max)") (value "75V"))
      (property (name "Operating Temperature Range") (value "-55°C~+155°C"))
      (property (name "Tolerance") (value "±1%"))
      (property (name "Temperature Coefficient") (value "±100ppm/°C"))
      (property (name "Sheetname") (value "Root"))
      (property (name "Sheetfile") (value "Pico_Development_Stack.kicad_sch"))
      (property (name "ki_fp_filters") (value "R_*"))
      (sheetpath (names "/") (tstamps "/"))
      (tstamps "f7c31055-e487-405b-8530-6335c6f73ab3"))
    (comp (ref "S1")
      (value "Tactile Button, 160gf")
      (footprint "PCM_JLCPCB:SW_TS-1088-AR02016")
      (datasheet "https://www.lcsc.com/datasheet/lcsc_datasheet_2304140030_XUNPU-TS-1088-AR02016_C720477.pdf")
      (description "Without 50mA 4mm 100MΩ 100000 Times 12V 160gf 3mm 2mm Round Button Standing paste SPST SMD Tactile Switches ROHS")
      (fields
        (field (name "LCSC") "C720477")
        (field (name "Stock") "346801")
        (field (name "Price") "0.044USD")
        (field (name "Process") "SMT")
        (field (name "Minimum Qty") "5")
        (field (name "Attrition Qty") "4")
        (field (name "Class") "Basic Component")
        (field (name "Category") "Switches,Tactile Switches")
        (field (name "Manufacturer") "XUNPU")
        (field (name "Part") "TS-1088-AR02016")
        (field (name "Switch Length") "4mm")
        (field (name "Voltage Rating (Dc)") "12V")
        (field (name "With Lamp") "No")
        (field (name "Operating Force") "160gf@±50gf")
        (field (name "Actuator/Cap Color") "Black")
        (field (name "Mechanical Life") "100000 Times")
        (field (name "Strike Gundam") "NO")
        (field (name "Circuit") "SPST")
        (field (name "Switch Height") "2mm")
        (field (name "Actuator Style") "Round Button")
        (field (name "Switch Width") "3mm")
        (field (name "Contact Current") "50mA")
        (field (name "Operating Temperature") "-30°C~+80°C")
        (field (name "Mounting Style") "Brick nogging")
        (field (name "Insulation Resistance") "100MΩ")
        (field (name "Pin Style") "SMDSplicing")
        (field (name "Peak Wavelength"))
        (field (name "Footprint") "PCM_JLCPCB:SW_TS-1088-AR02016")
        (field (name "Datasheet") "https://www.lcsc.com/datasheet/lcsc_datasheet_2304140030_XUNPU-TS-1088-AR02016_C720477.pdf")
        (field (name "Description") "Without 50mA 4mm 100MΩ 100000 Times 12V 160gf 3mm 2mm Round Button Standing paste SPST SMD Tactile Switches ROHS"))
      (libsource (lib "") (part "Tactile Button, 160gf, 12V, 50mA, 4.0mm_1") (description "Without 50mA 4mm 100MΩ 100000 Times 12V 160gf 3mm 2mm Round Button Standing paste SPST SMD Tactile Switches ROHS"))
      (property (name "LCSC") (value "C720477"))
      (property (name "Stock") (value "346801"))
      (property (name "Price") (value "0.044USD"))
      (property (name "Process") (value "SMT"))
      (property (name "Minimum Qty") (value "5"))
      (property (name "Attrition Qty") (value "4"))
      (property (name "Class") (value "Basic Component"))
      (property (name "Category") (value "Switches,Tactile Switches"))
      (property (name "Manufacturer") (value "XUNPU"))
      (property (name "Part") (value "TS-1088-AR02016"))
      (property (name "Switch Length") (value "4mm"))
      (property (name "Voltage Rating (Dc)") (value "12V"))
      (property (name "With Lamp") (value "No"))
      (property (name "Operating Force") (value "160gf@±50gf"))
      (property (name "Actuator/Cap Color") (value "Black"))
      (property (name "Mechanical Life") (value "100000 Times"))
      (property (name "Strike Gundam") (value "NO"))
      (property (name "Circuit") (value "SPST"))
      (property (name "Switch Height") (value "2mm"))
      (property (name "Actuator Style") (value "Round Button"))
      (property (name "Switch Width") (value "3mm"))
      (property (name "Contact Current") (value "50mA"))
      (property (name "Operating Temperature") (value "-30°C~+80°C"))
      (property (name "Mounting Style") (value "Brick nogging"))
      (property (name "Insulation Resistance") (value "100MΩ"))
      (property (name "Pin Style") (value "SMDSplicing"))
      (property (name "Peak Wavelength") (value ""))
      (property (name "Sheetname") (value "Root"))
      (property (name "Sheetfile") (value "Pico_Development_Stack.kicad_sch"))
      (property (name "ki_keywords") (value "C720477"))
      (sheetpath (names "/") (tstamps "/"))
      (tstamps "e25314fb-d3de-4868-a004-9a9d4976bf82"))
    (comp (ref "S2")
      (value "Tactile Button, 160gf")
      (footprint "PCM_JLCPCB:SW_TS-1088-AR02016")
      (datasheet "https://www.lcsc.com/datasheet/lcsc_datasheet_2304140030_XUNPU-TS-1088-AR02016_C720477.pdf")
      (description "Without 50mA 4mm 100MΩ 100000 Times 12V 160gf 3mm 2mm Round Button Standing paste SPST SMD Tactile Switches ROHS")
      (fields
        (field (name "LCSC") "C720477")
        (field (name "Stock") "346801")
        (field (name "Price") "0.044USD")
        (field (name "Process") "SMT")
        (field (name "Minimum Qty") "5")
        (field (name "Attrition Qty") "4")
        (field (name "Class") "Basic Component")
        (field (name "Category") "Switches,Tactile Switches")
        (field (name "Manufacturer") "XUNPU")
        (field (name "Part") "TS-1088-AR02016")
        (field (name "Switch Length") "4mm")
        (field (name "Voltage Rating (Dc)") "12V")
        (field (name "With Lamp") "No")
        (field (name "Operating Force") "160gf@±50gf")
        (field (name "Actuator/Cap Color") "Black")
        (field (name "Mechanical Life") "100000 Times")
        (field (name "Strike Gundam") "NO")
        (field (name "Circuit") "SPST")
        (field (name "Switch Height") "2mm")
        (field (name "Actuator Style") "Round Button")
        (field (name "Switch Width") "3mm")
        (field (name "Contact Current") "50mA")
        (field (name "Operating Temperature") "-30°C~+80°C")
        (field (name "Mounting Style") "Brick nogging")
        (field (name "Insulation Resistance") "100MΩ")
        (field (name "Pin Style") "SMDSplicing")
        (field (name "Peak Wavelength"))
        (field (name "Footprint") "PCM_JLCPCB:SW_TS-1088-AR02016")
        (field (name "Datasheet") "https://www.lcsc.com/datasheet/lcsc_datasheet_2304140030_XUNPU-TS-1088-AR02016_C720477.pdf")
        (field (name "Description") "Without 50mA 4mm 100MΩ 100000 Times 12V 160gf 3mm 2mm Round Button Standing paste SPST SMD Tactile Switches ROHS"))
      (libsource (lib "") (part "Tactile Button, 160gf, 12V, 50mA, 4.0mm_1") (description "Without 50mA 4mm 100MΩ 100000 Times 12V 160gf 3mm 2mm Round Button Standing paste SPST SMD Tactile Switches ROHS"))
      (property (name "LCSC") (value "C720477"))
      (property (name "Stock") (value "346801"))
      (property (name "Price") (value "0.044USD"))
      (property (name "Process") (value "SMT"))
      (property (name "Minimum Qty") (value "5"))
      (property (name "Attrition Qty") (value "4"))
      (property (name "Class") (value "Basic Component"))
      (property (name "Category") (value "Switches,Tactile Switches"))
      (property (name "Manufacturer") (value "XUNPU"))
      (property (name "Part") (value "TS-1088-AR02016"))
      (property (name "Switch Length") (value "4mm"))
      (property (name "Voltage Rating (Dc)") (value "12V"))
      (property (name "With Lamp") (value "No"))
      (property (name "Operating Force") (value "160gf@±50gf"))
      (property (name "Actuator/Cap Color") (value "Black"))
      (property (name "Mechanical Life") (value "100000 Times"))
      (property (name "Strike Gundam") (value "NO"))
      (property (name "Circuit") (value "SPST"))
      (property (name "Switch Height") (value "2mm"))
      (property (name "Actuator Style") (value "Round Button"))
      (property (name "Switch Width") (value "3mm"))
      (property (name "Contact Current") (value "50mA"))
      (property (name "Operating Temperature") (value "-30°C~+80°C"))
      (property (name "Mounting Style") (value "Brick nogging"))
      (property (name "Insulation Resistance") (value "100MΩ"))
      (property (name "Pin Style") (value "SMDSplicing"))
      (property (name "Peak Wavelength") (value ""))
      (property (name "Sheetname") (value "Root"))
      (property (name "Sheetfile") (value "Pico_Development_Stack.kicad_sch"))
      (property (name "ki_keywords") (value "C720477"))
      (sheetpath (names "/") (tstamps "/"))
      (tstamps "d3b782e6-0bdc-415b-8f83-48abea386e64"))
    (comp (ref "S3")
      (value "Tactile Button, 160gf")
      (footprint "PCM_JLCPCB:SW_TS-1088-AR02016")
      (datasheet "https://www.lcsc.com/datasheet/lcsc_datasheet_2304140030_XUNPU-TS-1088-AR02016_C720477.pdf")
      (description "Without 50mA 4mm 100MΩ 100000 Times 12V 160gf 3mm 2mm Round Button Standing paste SPST SMD Tactile Switches ROHS")
      (fields
        (field (name "LCSC") "C720477")
        (field (name "Stock") "346801")
        (field (name "Price") "0.044USD")
        (field (name "Process") "SMT")
        (field (name "Minimum Qty") "5")
        (field (name "Attrition Qty") "4")
        (field (name "Class") "Basic Component")
        (field (name "Category") "Switches,Tactile Switches")
        (field (name "Manufacturer") "XUNPU")
        (field (name "Part") "TS-1088-AR02016")
        (field (name "Switch Length") "4mm")
        (field (name "Voltage Rating (Dc)") "12V")
        (field (name "With Lamp") "No")
        (field (name "Operating Force") "160gf@±50gf")
        (field (name "Actuator/Cap Color") "Black")
        (field (name "Mechanical Life") "100000 Times")
        (field (name "Strike Gundam") "NO")
        (field (name "Circuit") "SPST")
        (field (name "Switch Height") "2mm")
        (field (name "Actuator Style") "Round Button")
        (field (name "Switch Width") "3mm")
        (field (name "Contact Current") "50mA")
        (field (name "Operating Temperature") "-30°C~+80°C")
        (field (name "Mounting Style") "Brick nogging")
        (field (name "Insulation Resistance") "100MΩ")
        (field (name "Pin Style") "SMDSplicing")
        (field (name "Peak Wavelength"))
        (field (name "Footprint") "PCM_JLCPCB:SW_TS-1088-AR02016")
        (field (name "Datasheet") "https://www.lcsc.com/datasheet/lcsc_datasheet_2304140030_XUNPU-TS-1088-AR02016_C720477.pdf")
        (field (name "Description") "Without 50mA 4mm 100MΩ 100000 Times 12V 160gf 3mm 2mm Round Button Standing paste SPST SMD Tactile Switches ROHS"))
      (libsource (lib "") (part "Tactile Button, 160gf, 12V, 50mA, 4.0mm_1") (description "Without 50mA 4mm 100MΩ 100000 Times 12V 160gf 3mm 2mm Round Button Standing paste SPST SMD Tactile Switches ROHS"))
      (property (name "LCSC") (value "C720477"))
      (property (name "Stock") (value "346801"))
      (property (name "Price") (value "0.044USD"))
      (property (name "Process") (value "SMT"))
      (property (name "Minimum Qty") (value "5"))
      (property (name "Attrition Qty") (value "4"))
      (property (name "Class") (value "Basic Component"))
      (property (name "Category") (value "Switches,Tactile Switches"))
      (property (name "Manufacturer") (value "XUNPU"))
      (property (name "Part") (value "TS-1088-AR02016"))
      (property (name "Switch Length") (value "4mm"))
      (property (name "Voltage Rating (Dc)") (value "12V"))
      (property (name "With Lamp") (value "No"))
      (property (name "Operating Force") (value "160gf@±50gf"))
      (property (name "Actuator/Cap Color") (value "Black"))
      (property (name "Mechanical Life") (value "100000 Times"))
      (property (name "Strike Gundam") (value "NO"))
      (property (name "Circuit") (value "SPST"))
      (property (name "Switch Height") (value "2mm"))
      (property (name "Actuator Style") (value "Round Button"))
      (property (name "Switch Width") (value "3mm"))
      (property (name "Contact Current") (value "50mA"))
      (property (name "Operating Temperature") (value "-30°C~+80°C"))
      (property (name "Mounting Style") (value "Brick nogging"))
      (property (name "Insulation Resistance") (value "100MΩ"))
      (property (name "Pin Style") (value "SMDSplicing"))
      (property (name "Peak Wavelength") (value ""))
      (property (name "Sheetname") (value "Root"))
      (property (name "Sheetfile") (value "Pico_Development_Stack.kicad_sch"))
      (property (name "ki_keywords") (value "C720477"))
      (sheetpath (names "/") (tstamps "/"))
      (tstamps "5f2a1b5b-70bc-4b15-afe4-48c22b6617f2"))
    (comp (ref "S4")
      (value "Tactile Button, 160gf")
      (footprint "PCM_JLCPCB:SW_TS-1088-AR02016")
      (datasheet "https://www.lcsc.com/datasheet/lcsc_datasheet_2304140030_XUNPU-TS-1088-AR02016_C720477.pdf")
      (description "Without 50mA 4mm 100MΩ 100000 Times 12V 160gf 3mm 2mm Round Button Standing paste SPST SMD Tactile Switches ROHS")
      (fields
        (field (name "LCSC") "C720477")
        (field (name "Stock") "346801")
        (field (name "Price") "0.044USD")
        (field (name "Process") "SMT")
        (field (name "Minimum Qty") "5")
        (field (name "Attrition Qty") "4")
        (field (name "Class") "Basic Component")
        (field (name "Category") "Switches,Tactile Switches")
        (field (name "Manufacturer") "XUNPU")
        (field (name "Part") "TS-1088-AR02016")
        (field (name "Switch Length") "4mm")
        (field (name "Voltage Rating (Dc)") "12V")
        (field (name "With Lamp") "No")
        (field (name "Operating Force") "160gf@±50gf")
        (field (name "Actuator/Cap Color") "Black")
        (field (name "Mechanical Life") "100000 Times")
        (field (name "Strike Gundam") "NO")
        (field (name "Circuit") "SPST")
        (field (name "Switch Height") "2mm")
        (field (name "Actuator Style") "Round Button")
        (field (name "Switch Width") "3mm")
        (field (name "Contact Current") "50mA")
        (field (name "Operating Temperature") "-30°C~+80°C")
        (field (name "Mounting Style") "Brick nogging")
        (field (name "Insulation Resistance") "100MΩ")
        (field (name "Pin Style") "SMDSplicing")
        (field (name "Peak Wavelength"))
        (field (name "Footprint") "PCM_JLCPCB:SW_TS-1088-AR02016")
        (field (name "Datasheet") "https://www.lcsc.com/datasheet/lcsc_datasheet_2304140030_XUNPU-TS-1088-AR02016_C720477.pdf")
        (field (name "Description") "Without 50mA 4mm 100MΩ 100000 Times 12V 160gf 3mm 2mm Round Button Standing paste SPST SMD Tactile Switches ROHS"))
      (libsource (lib "") (part "Tactile Button, 160gf, 12V, 50mA, 4.0mm_1") (description "Without 50mA 4mm 100MΩ 100000 Times 12V 160gf 3mm 2mm Round Button Standing paste SPST SMD Tactile Switches ROHS"))
      (property (name "LCSC") (value "C720477"))
      (property (name "Stock") (value "346801"))
      (property (name "Price") (value "0.044USD"))
      (property (name "Process") (value "SMT"))
      (property (name "Minimum Qty") (value "5"))
      (property (name "Attrition Qty") (value "4"))
      (property (name "Class") (value "Basic Component"))
      (property (name "Category") (value "Switches,Tactile Switches"))
      (property (name "Manufacturer") (value "XUNPU"))
      (property (name "Part") (value "TS-1088-AR02016"))
      (property (name "Switch Length") (value "4mm"))
      (property (name "Voltage Rating (Dc)") (value "12V"))
      (property (name "With Lamp") (value "No"))
      (property (name "Operating Force") (value "160gf@±50gf"))
      (property (name "Actuator/Cap Color") (value "Black"))
      (property (name "Mechanical Life") (value "100000 Times"))
      (property (name "Strike Gundam") (value "NO"))
      (property (name "Circuit") (value "SPST"))
      (property (name "Switch Height") (value "2mm"))
      (property (name "Actuator Style") (value "Round Button"))
      (property (name "Switch Width") (value "3mm"))
      (property (name "Contact Current") (value "50mA"))
      (property (name "Operating Temperature") (value "-30°C~+80°C"))
      (property (name "Mounting Style") (value "Brick nogging"))
      (property (name "Insulation Resistance") (value "100MΩ"))
      (property (name "Pin Style") (value "SMDSplicing"))
      (property (name "Peak Wavelength") (value ""))
      (property (name "Sheetname") (value "Root"))
      (property (name "Sheetfile") (value "Pico_Development_Stack.kicad_sch"))
      (property (name "ki_keywords") (value "C720477"))
      (sheetpath (names "/") (tstamps "/"))
      (tstamps "14fd5e85-5948-4789-bcf4-0dacba11d74a"))
    (comp (ref "S5")
      (value "Tactile Button, 160gf")
      (footprint "PCM_JLCPCB:SW_TS-1088-AR02016")
      (datasheet "https://www.lcsc.com/datasheet/lcsc_datasheet_2304140030_XUNPU-TS-1088-AR02016_C720477.pdf")
      (description "Without 50mA 4mm 100MΩ 100000 Times 12V 160gf 3mm 2mm Round Button Standing paste SPST SMD Tactile Switches ROHS")
      (fields
        (field (name "LCSC") "C720477")
        (field (name "Stock") "346801")
        (field (name "Price") "0.044USD")
        (field (name "Process") "SMT")
        (field (name "Minimum Qty") "5")
        (field (name "Attrition Qty") "4")
        (field (name "Class") "Basic Component")
        (field (name "Category") "Switches,Tactile Switches")
        (field (name "Manufacturer") "XUNPU")
        (field (name "Part") "TS-1088-AR02016")
        (field (name "Switch Length") "4mm")
        (field (name "Voltage Rating (Dc)") "12V")
        (field (name "With Lamp") "No")
        (field (name "Operating Force") "160gf@±50gf")
        (field (name "Actuator/Cap Color") "Black")
        (field (name "Mechanical Life") "100000 Times")
        (field (name "Strike Gundam") "NO")
        (field (name "Circuit") "SPST")
        (field (name "Switch Height") "2mm")
        (field (name "Actuator Style") "Round Button")
        (field (name "Switch Width") "3mm")
        (field (name "Contact Current") "50mA")
        (field (name "Operating Temperature") "-30°C~+80°C")
        (field (name "Mounting Style") "Brick nogging")
        (field (name "Insulation Resistance") "100MΩ")
        (field (name "Pin Style") "SMDSplicing")
        (field (name "Peak Wavelength"))
        (field (name "Footprint") "PCM_JLCPCB:SW_TS-1088-AR02016")
        (field (name "Datasheet") "https://www.lcsc.com/datasheet/lcsc_datasheet_2304140030_XUNPU-TS-1088-AR02016_C720477.pdf")
        (field (name "Description") "Without 50mA 4mm 100MΩ 100000 Times 12V 160gf 3mm 2mm Round Button Standing paste SPST SMD Tactile Switches ROHS"))
      (libsource (lib "") (part "Tactile Button, 160gf, 12V, 50mA, 4.0mm_1") (description "Without 50mA 4mm 100MΩ 100000 Times 12V 160gf 3mm 2mm Round Button Standing paste SPST SMD Tactile Switches ROHS"))
      (property (name "LCSC") (value "C720477"))
      (property (name "Stock") (value "346801"))
      (property (name "Price") (value "0.044USD"))
      (property (name "Process") (value "SMT"))
      (property (name "Minimum Qty") (value "5"))
      (property (name "Attrition Qty") (value "4"))
      (property (name "Class") (value "Basic Component"))
      (property (name "Category") (value "Switches,Tactile Switches"))
      (property (name "Manufacturer") (value "XUNPU"))
      (property (name "Part") (value "TS-1088-AR02016"))
      (property (name "Switch Length") (value "4mm"))
      (property (name "Voltage Rating (Dc)") (value "12V"))
      (property (name "With Lamp") (value "No"))
      (property (name "Operating Force") (value "160gf@±50gf"))
      (property (name "Actuator/Cap Color") (value "Black"))
      (property (name "Mechanical Life") (value "100000 Times"))
      (property (name "Strike Gundam") (value "NO"))
      (property (name "Circuit") (value "SPST"))
      (property (name "Switch Height") (value "2mm"))
      (property (name "Actuator Style") (value "Round Button"))
      (property (name "Switch Width") (value "3mm"))
      (property (name "Contact Current") (value "50mA"))
      (property (name "Operating Temperature") (value "-30°C~+80°C"))
      (property (name "Mounting Style") (value "Brick nogging"))
      (property (name "Insulation Resistance") (value "100MΩ"))
      (property (name "Pin Style") (value "SMDSplicing"))
      (property (name "Peak Wavelength") (value ""))
      (property (name "Sheetname") (value "Root"))
      (property (name "Sheetfile") (value "Pico_Development_Stack.kicad_sch"))
      (property (name "ki_keywords") (value "C720477"))
      (sheetpath (names "/") (tstamps "/"))
      (tstamps "85c295dd-7d0c-4dbb-af1c-7b4ef6deea5e"))
    (comp (ref "SW1")
      (value "SPDT")
      (footprint "rpi-lib-kicad-rp235x:SW_SPDT_Shouhan_MSK12C02")
      (datasheet "https://www.lcsc.com/datasheet/C431540.pdf")
      (fields
        (field (name "LCSC") "C431540")
        (field (name "Field6"))
        (field (name "Footprint") "rpi-lib-kicad-rp235x:SW_SPDT_Shouhan_MSK12C02")
        (field (name "Datasheet") "https://www.lcsc.com/datasheet/C431540.pdf")
        (field (name "Description")))
      (libsource (lib "rpi-lib-kicad-rp235x") (part "SPDT_GND") (description ""))
      (property (name "LCSC") (value "C431540"))
      (property (name "Field6") (value ""))
      (property (name "Sheetname") (value "Root"))
      (property (name "Sheetfile") (value "Pico_Development_Stack.kicad_sch"))
      (sheetpath (names "/") (tstamps "/"))
      (tstamps "5dbe9b37-0ca1-4892-8abf-59e71b97d079"))
    (comp (ref "TP1")
      (value "GND Wire 1")
      (footprint "TestPoint:TestPoint_Loop_D2.54mm_Drill1.5mm_Beaded")
      (datasheet "~")
      (description "test point")
      (fields
        (field (name "Peak Wavelength"))
        (field (name "Footprint") "TestPoint:TestPoint_Loop_D2.54mm_Drill1.5mm_Beaded")
        (field (name "Datasheet") "~")
        (field (name "Description") "test point"))
      (libsource (lib "Connector") (part "TestPoint") (description "test point"))
      (property (name "Peak Wavelength") (value ""))
      (property (name "Sheetname") (value "Root"))
      (property (name "Sheetfile") (value "Pico_Development_Stack.kicad_sch"))
      (property (name "ki_keywords") (value "test point tp"))
      (property (name "ki_fp_filters") (value "Pin* Test*"))
      (sheetpath (names "/") (tstamps "/"))
      (tstamps "1309d07c-69ea-4d7a-9cad-a231d2c94ac3"))
    (comp (ref "TP2")
      (value "GND Wire 0")
      (footprint "TestPoint:TestPoint_Loop_D2.54mm_Drill1.5mm_Beaded")
      (datasheet "~")
      (description "test point")
      (fields
        (field (name "Peak Wavelength"))
        (field (name "Footprint") "TestPoint:TestPoint_Loop_D2.54mm_Drill1.5mm_Beaded")
        (field (name "Datasheet") "~")
        (field (name "Description") "test point"))
      (libsource (lib "Connector") (part "TestPoint") (description "test point"))
      (property (name "Peak Wavelength") (value ""))
      (property (name "Sheetname") (value "Root"))
      (property (name "Sheetfile") (value "Pico_Development_Stack.kicad_sch"))
      (property (name "ki_keywords") (value "test point tp"))
      (property (name "ki_fp_filters") (value "Pin* Test*"))
      (sheetpath (names "/") (tstamps "/"))
      (tstamps "4380fd7b-51fe-4e9e-bb22-3ec757260175"))
    (comp (ref "TP3")
      (value "5V")
      (footprint "TestPoint:TestPoint_Loop_D2.50mm_Drill1.0mm_LowProfile")
      (datasheet "~")
      (description "test point")
      (fields
        (field (name "Peak Wavelength"))
        (field (name "Footprint") "TestPoint:TestPoint_Loop_D2.50mm_Drill1.0mm_LowProfile")
        (field (name "Datasheet") "~")
        (field (name "Description") "test point"))
      (libsource (lib "Connector") (part "TestPoint") (description "test point"))
      (property (name "Peak Wavelength") (value ""))
      (property (name "Sheetname") (value "Root"))
      (property (name "Sheetfile") (value "Pico_Development_Stack.kicad_sch"))
      (property (name "ki_keywords") (value "test point tp"))
      (property (name "ki_fp_filters") (value "Pin* Test*"))
      (sheetpath (names "/") (tstamps "/"))
      (tstamps "1d10aac2-5505-43fd-8a15-59ae144feba1"))
    (comp (ref "TP4")
      (value "3V3")
      (footprint "TestPoint:TestPoint_Loop_D2.50mm_Drill1.0mm_LowProfile")
      (datasheet "~")
      (description "test point")
      (fields
        (field (name "Peak Wavelength"))
        (field (name "Footprint") "TestPoint:TestPoint_Loop_D2.50mm_Drill1.0mm_LowProfile")
        (field (name "Datasheet") "~")
        (field (name "Description") "test point"))
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
