frohro/Pico_Debug_Stack/rpi-lib-kicad/blocks/rpi-lib-kicad-RP2040.kicad_blocks/RP2040.kicad_block/RP2040.kicad_sch

## KiCad design rpi-lib-kicad/blocks/rpi-lib-kicad-RP2040.kicad_blocks/RP2040.kicad_block/RP2040.kicad_sch (2025-12-30)

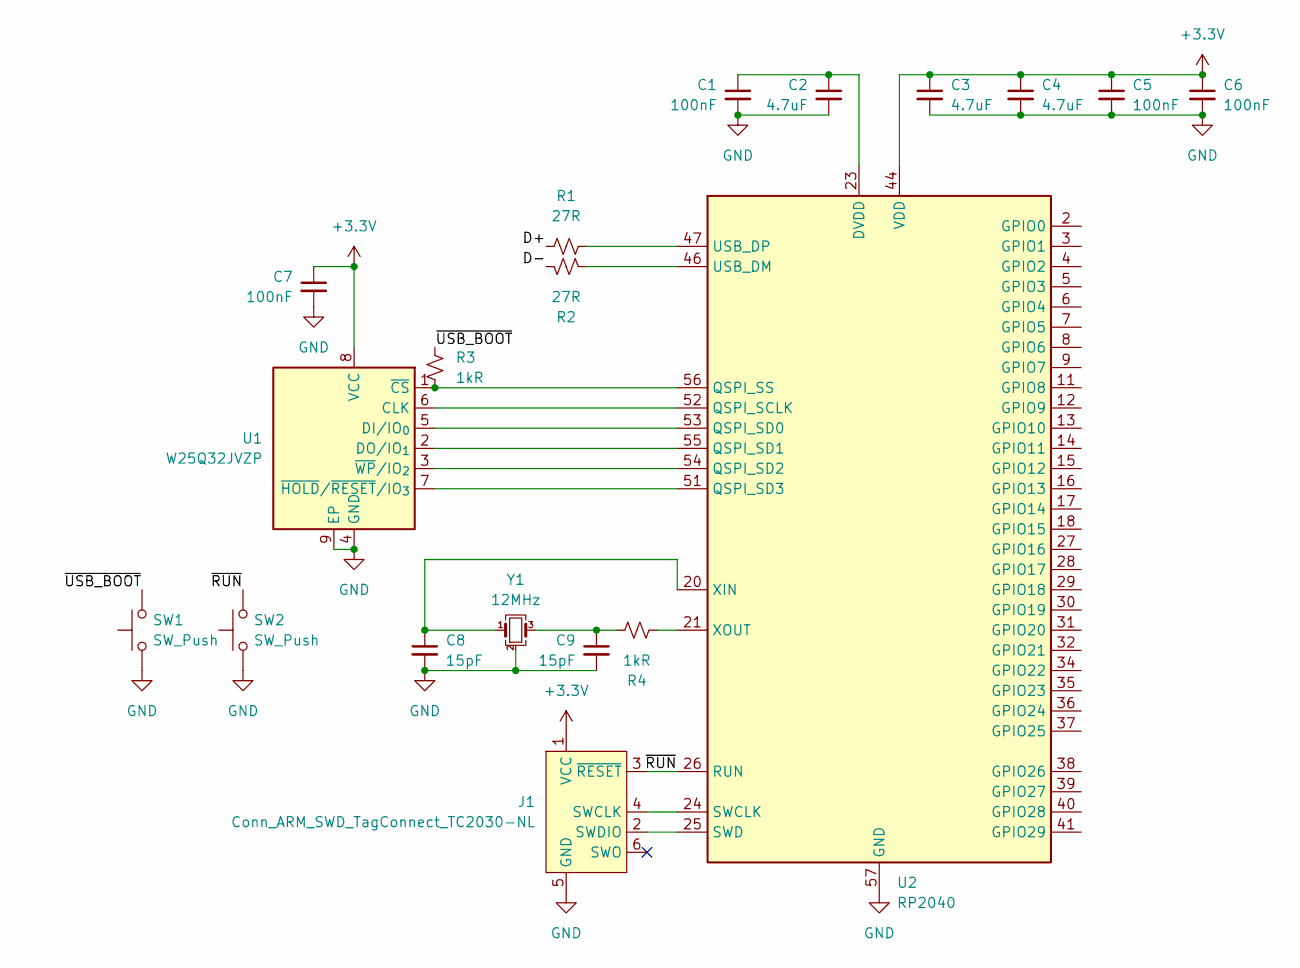
[picture p14: schematic RP2040.kicad_sch]

Parts:
C1, C5, C6, C7: 100nF; C_0402_1005Metric; LCSC C1525
C2, C3, C4: 4.7uF; C_0402_1005Metric; LCSC C23733
C8, C9: 15pF; C_0402_1005Metric; LCSC C1548
J1: Conn_ARM_SWD_TagConnect_TC2030-NL; Tag-Connect_TC2030-IDC-NL_2x03_P1.27mm_Vertical
R1, R2: 27R; R_0402_1005Metric; LCSC C138021
R3, R4: 1kR; R_0402_1005Metric; LCSC C11702
SW1, SW2: SW_Push; SW_Push_1P1T_NO_Vertical_Wuerth_434133025816; LCSC C843674
U1: W25Q32JVZP; WSON-8-1EP_6x5mm_P1.27mm_EP3.4x4.3mm; LCSC C571260
U2: RP2040; QFN-56-1EP_7x7mm_P0.4mm_EP3.2x3.2mm; LCSC C2040
Y1: 12MHz; Crystal_SMD_3225-4Pin_3.2x2.5mm; LCSC C37635368

Connections:
+3.3V: C3.1, C4.1, C5.1, C6.1, C7.1, J1.1 (VCC), U1.8 (VCC), U2.1 (VDD), U2.10 (IOVDD), U2.22 (IOVDD), U2.33 (IOVDD), U2.42 (IOVDD), U2.43 (VDD), U2.44 (VDD), U2.48 (VDD), U2.49 (IOVDD)
D+: R1.1
D-: R2.1
GND: C1.2, C2.2, C3.2, C4.2, C5.2, C6.2, C7.2, C8.2, C9.2, J1.5 (GND), SW1.1, SW2.1, U1.4 (GND), U1.9 (EP), U2.19 (GND), U2.57 (GND), Y1.2, Y1.4
unnamed: C1.1, C2.1, U2.23 (DVDD), U2.45 (DVDD), U2.50 (DVDD)
unnamed: C8.1, U2.20 (XIN), Y1.1
unnamed: C9.1, R4.1, Y1.3
unnamed: J1.2 (SWDIO), U2.25 (SWD)
unnamed: J1.4 (SWCLK), U2.24 (SWCLK)
unnamed: R1.2, U2.47 (USB_DP)
unnamed: R2.2, U2.46 (USB_DM)
unnamed: R3.2, U1.1 (~CS), U2.56 (QSPI_SS)
unnamed: R4.2, U2.21 (XOUT)
unnamed: U1.2 (DO/IO_{1}), U2.55 (QSPI_SD1)
unnamed: U1.3 (~WP/IO_{2}), U2.54 (QSPI_SD2)
unnamed: U1.5 (DI/IO_{0}), U2.53 (QSPI_SD0)
unnamed: U1.6 (CLK), U2.52 (QSPI_SCLK)
unnamed: U1.7 (~HOLD/~RESET/IO_{3}), U2.51 (QSPI_SD3)
~RUN: J1.3 (~RESET), SW2.2, U2.26 (RUN)
~USB_BOOT: R3.1, SW1.2
